skutis/jtbubl/cores/bubl/ver/game/scene1/1.png

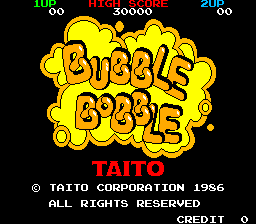
cores/bubl/ver/game/scene1/1.png
