skutis/jtbubl/cores/bubl/ver/game/scene2/2.png

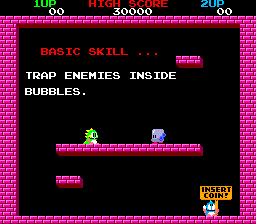
cores/bubl/ver/game/scene2/2.png
