skutis/jtbubl/cores/bubl/ver/game/scene3/3.png

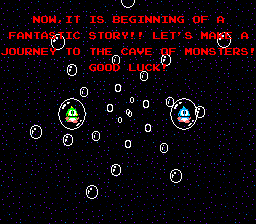
cores/bubl/ver/game/scene3/3.png
