skutis/jtbubl/cores/bubl/ver/game/scene4/4.png

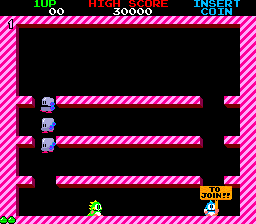
cores/bubl/ver/game/scene4/4.png
