skutis/jtbubl/cores/bubl/ver/game/scene5/5.png

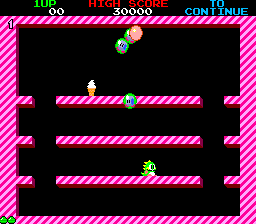
cores/bubl/ver/game/scene5/5.png
