skutis/jtbubl/cores/bubl/ver/game/scene6/6.png

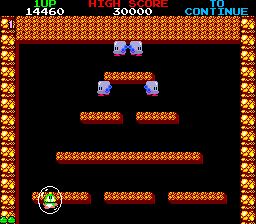
cores/bubl/ver/game/scene6/6.png
