skutis/jtbubl/cores/bubl/ver/game/scene7/7.png

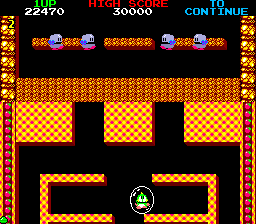
cores/bubl/ver/game/scene7/7.png
