skutis/jtbubl/cores/bubl/ver/game/scene8/8.png

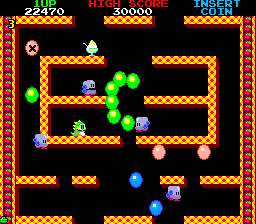
cores/bubl/ver/game/scene8/8.png
