skutis/jtbubl/cores/kiwi/sch/capacitors.kicad_sch

## KiCad design cores/kiwi/sch/capacitors.kicad_sch (2022-11-14, an earlier design)

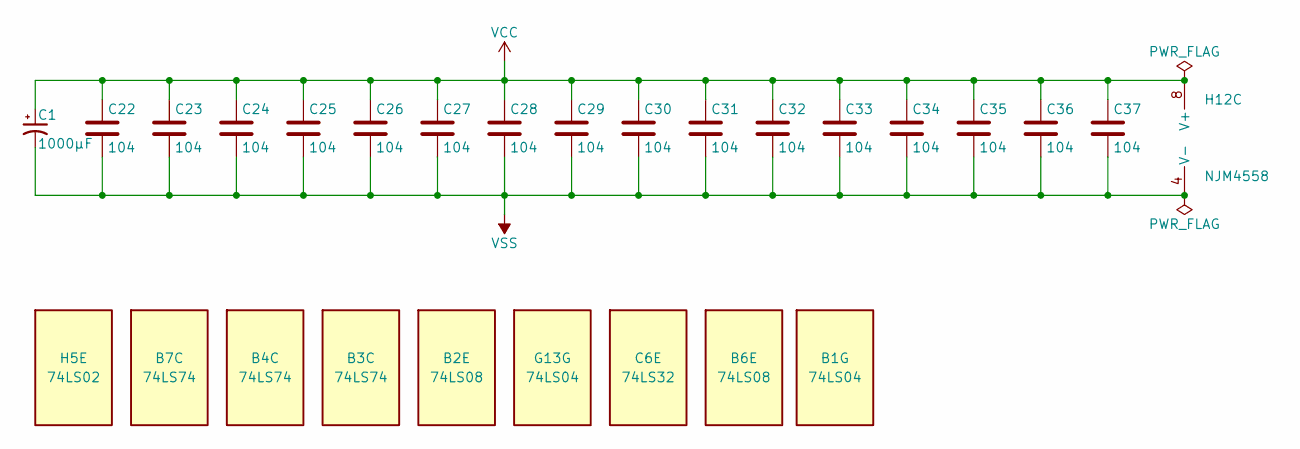
[picture p10: schematic capacitors.kicad_sch]

Parts:
B1: 74LS04
B2, B6: 74LS08
B3, B4, B7: 74LS74
C1: 1000μF
C6: 74LS32
C22, C23, C24, C25, C26, C27, C28, C29, C30, C31, C32, C33, C34, C35, C36, C37: 104
G13: 74LS04
H5: 74LS02
H12: NJM4558

Connections:
VCC: C1.1, C22.1, C23.1, C24.1, C25.1, C26.1, C27.1, C28.1, C29.1, C30.1, C31.1, C32.1, C33.1, C34.1, C35.1, C36.1, C37.1, H12.8 (V+)
VSS: C1.2, C22.2, C23.2, C24.2, C25.2, C26.2, C27.2, C28.2, C29.2, C30.2, C31.2, C32.2, C33.2, C34.2, C35.2, C36.2, C37.2, H12.4 (V-)
