skutis/jtbubl/cores/kiwi/sch/colmix.kicad_sch

## KiCad design cores/kiwi/sch/colmix.kicad_sch (2022-11-14, an earlier design)

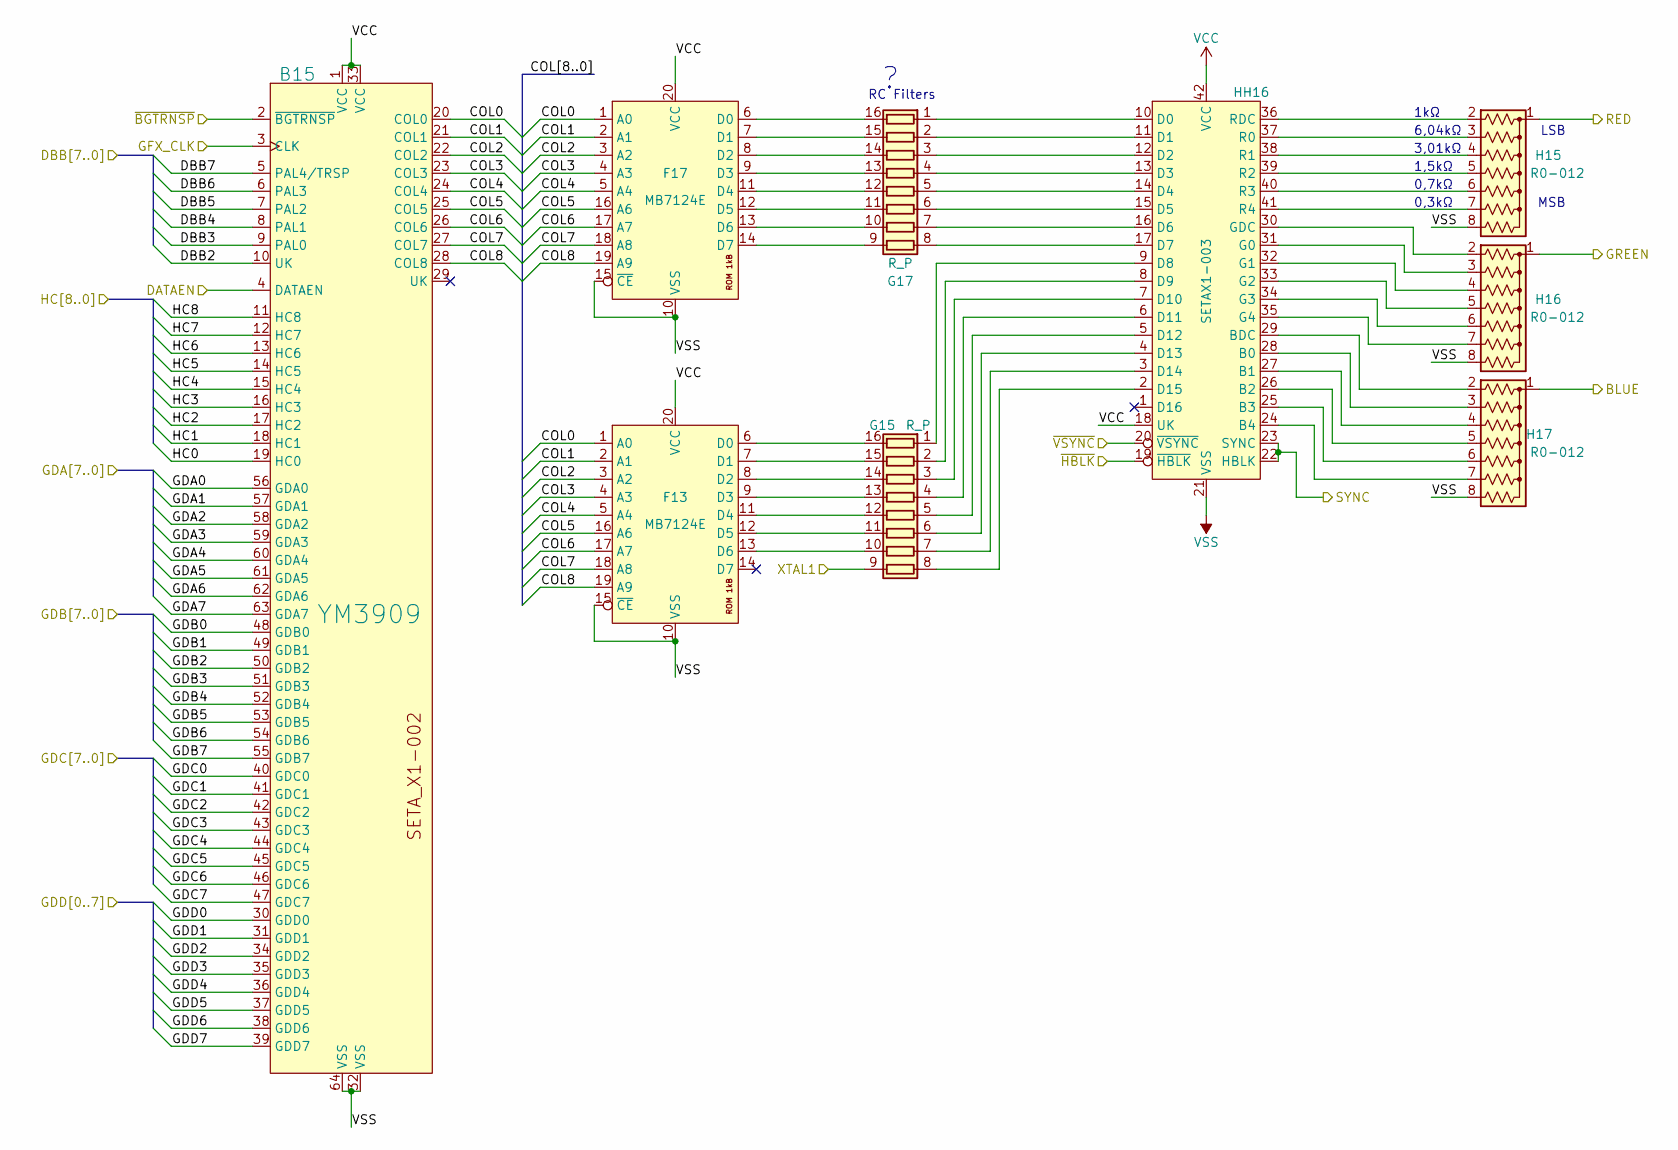
[picture p11: schematic colmix.kicad_sch]

Parts:
B15: YM3909
F13, F17: MB7124E
G15, G17: R_P
H15, H16, H17: R0-012; R_Array_SIP8
HH16: SETAX1-003

Connections:
BLUE: H17.1 (common)
COL0: B15.20 (COL0), F13.1 (A0), F17.1 (A0)
COL1: B15.21 (COL1), F13.2 (A1), F17.2 (A1)
COL2: B15.22 (COL2), F13.3 (A2), F17.3 (A2)
COL3: B15.23 (COL3), F13.4 (A3), F17.4 (A3)
COL4: B15.24 (COL4), F13.5 (A4), F17.5 (A4)
COL5: B15.25 (COL5), F13.16 (A6), F17.16 (A6)
COL6: B15.26 (COL6), F13.17 (A7), F17.17 (A7)
COL7: B15.27 (COL7), F13.18 (A8), F17.18 (A8)
COL8: B15.28 (COL8), F13.19 (A9), F17.19 (A9)
DATAEN: B15.4 (DATAEN)
DBB2: B15.10 (UK)
DBB3: B15.9 (PAL0)
DBB4: B15.8 (PAL1)
DBB5: B15.7 (PAL2)
DBB6: B15.6 (PAL3)
DBB7: B15.5 (PAL4/TRSP)
GDA0: B15.56 (GDA0)
GDA1: B15.57 (GDA1)
GDA2: B15.58 (GDA2)
GDA3: B15.59 (GDA3)
GDA4: B15.60 (GDA4)
GDA5: B15.61 (GDA5)
GDA6: B15.62 (GDA6)
GDA7: B15.63 (GDA7)
GDB0: B15.48 (GDB0)
GDB1: B15.49 (GDB1)
GDB2: B15.50 (GDB2)
GDB3: B15.51 (GDB3)
GDB4: B15.52 (GDB4)
GDB5: B15.53 (GDB5)
GDB6: B15.54 (GDB6)
GDB7: B15.55 (GDB7)
GDC0: B15.40 (GDC0)
GDC1: B15.41 (GDC1)
GDC2: B15.42 (GDC2)
GDC3: B15.43 (GDC3)
GDC4: B15.44 (GDC4)
GDC5: B15.45 (GDC5)
GDC6: B15.46 (GDC6)
GDC7: B15.47 (GDC7)
GDD0: B15.30 (GDD0)
GDD1: B15.31 (GDD1)
GDD2: B15.34 (GDD2)
GDD3: B15.35 (GDD3)
GDD4: B15.36 (GDD4)
GDD5: B15.37 (GDD5)
GDD6: B15.38 (GDD6)
GDD7: B15.39 (GDD7)
GFX_CLK: B15.3 (CLK)
GREEN: H16.1 (common)
HC0: B15.19 (HC0)
HC1: B15.18 (HC1)
HC2: B15.17 (HC2)
HC3: B15.16 (HC3)
HC4: B15.15 (HC4)
HC5: B15.14 (HC5)
HC6: B15.13 (HC6)
HC7: B15.12 (HC7)
HC8: B15.11 (HC8)
unnamed: F13.6 (D0), G15.16 (R1.2)
unnamed: F13.7 (D1), G15.15 (R2.2)
unnamed: F13.8 (D2), G15.14 (R3.2)
unnamed: F13.9 (D3), G15.13 (R4.2)
unnamed: F13.11 (D4), G15.12 (R5.2)
unnamed: F13.12 (D5), G15.11 (R6.2)
unnamed: F13.13 (D6), G15.10 (R7.2)
unnamed: F17.6 (D0), G17.16 (R1.2)
unnamed: F17.7 (D1), G17.15 (R2.2)
unnamed: F17.8 (D2), G17.14 (R3.2)
unnamed: F17.9 (D3), G17.13 (R4.2)
unnamed: F17.11 (D4), G17.12 (R5.2)
unnamed: F17.12 (D5), G17.11 (R6.2)
unnamed: F17.13 (D6), G17.10 (R7.2)
unnamed: F17.14 (D7), G17.9 (R8.2)
unnamed: G15.1 (R1.1), HH16.9 (D8)
unnamed: G15.2 (R2.1), HH16.8 (D9)
unnamed: G15.3 (R3.1), HH16.7 (D10)
unnamed: G15.4 (R4.1), HH16.6 (D11)
unnamed: G15.5 (R5.1), HH16.5 (D12)
unnamed: G15.6 (R6.1), HH16.4 (D13)
unnamed: G15.7 (R7.1), HH16.3 (D14)
unnamed: G15.8 (R8.1), HH16.2 (D15)
unnamed: G17.1 (R1.1), HH16.10 (D0)
unnamed: G17.2 (R2.1), HH16.11 (D1)
unnamed: G17.3 (R3.1), HH16.12 (D2)
unnamed: G17.4 (R4.1), HH16.13 (D3)
unnamed: G17.5 (R5.1), HH16.14 (D4)
unnamed: G17.6 (R6.1), HH16.15 (D5)
unnamed: G17.7 (R7.1), HH16.16 (D6)
unnamed: G17.8 (R8.1), HH16.17 (D7)
unnamed: H15.2 (R1), HH16.36 (RDC)
unnamed: H15.3 (R2), HH16.37 (R0)
unnamed: H15.4 (R3), HH16.38 (R1)
unnamed: H15.5 (R4), HH16.39 (R2)
unnamed: H15.6 (R5), HH16.40 (R3)
unnamed: H15.7 (R6), HH16.41 (R4)
unnamed: H16.2 (R1), HH16.30 (GDC)
unnamed: H16.3 (R2), HH16.31 (G0)
unnamed: H16.4 (R3), HH16.32 (G1)
unnamed: H16.5 (R4), HH16.33 (G2)
unnamed: H16.6 (R5), HH16.34 (G3)
unnamed: H16.7 (R6), HH16.35 (G4)
unnamed: H17.2 (R1), HH16.29 (BDC)
unnamed: H17.3 (R2), HH16.28 (B0)
unnamed: H17.4 (R3), HH16.27 (B1)
unnamed: H17.5 (R4), HH16.26 (B2)
unnamed: H17.6 (R5), HH16.25 (B3)
unnamed: H17.7 (R6), HH16.24 (B4)
RED: H15.1 (common)
SYNC: HH16.22 (HBLK), HH16.23 (SYNC)
VCC: B15.1 (VCC), B15.33 (VCC), F13.20 (VCC), F17.20 (VCC), HH16.18 (UK), HH16.42 (VCC)
VSS: B15.32 (VSS), B15.64 (VSS), F13.10 (VSS), F13.15 (~CE), F17.10 (VSS), F17.15 (~CE), H15.8 (R7), H16.8 (R7), H17.8 (R7), HH16.21 (VSS)
XTAL1: G15.9 (R8.2)
~BGTRNSP: B15.2 (~BGTRNSP)
~HBLK: HH16.19 (~HBLK)
~VSYNC: HH16.20 (~VSYNC)

Notes on the sheet:
MSB
RC Filters
1,5kΩ
1kΩ
3,01kΩ
0,3kΩ
LSB
6,04kΩ
0,7kΩ
