skutis/jtbubl/cores/kiwi/sch/gfx.kicad_sch

## KiCad design cores/kiwi/sch/gfx.kicad_sch (2022-11-14, an earlier design)

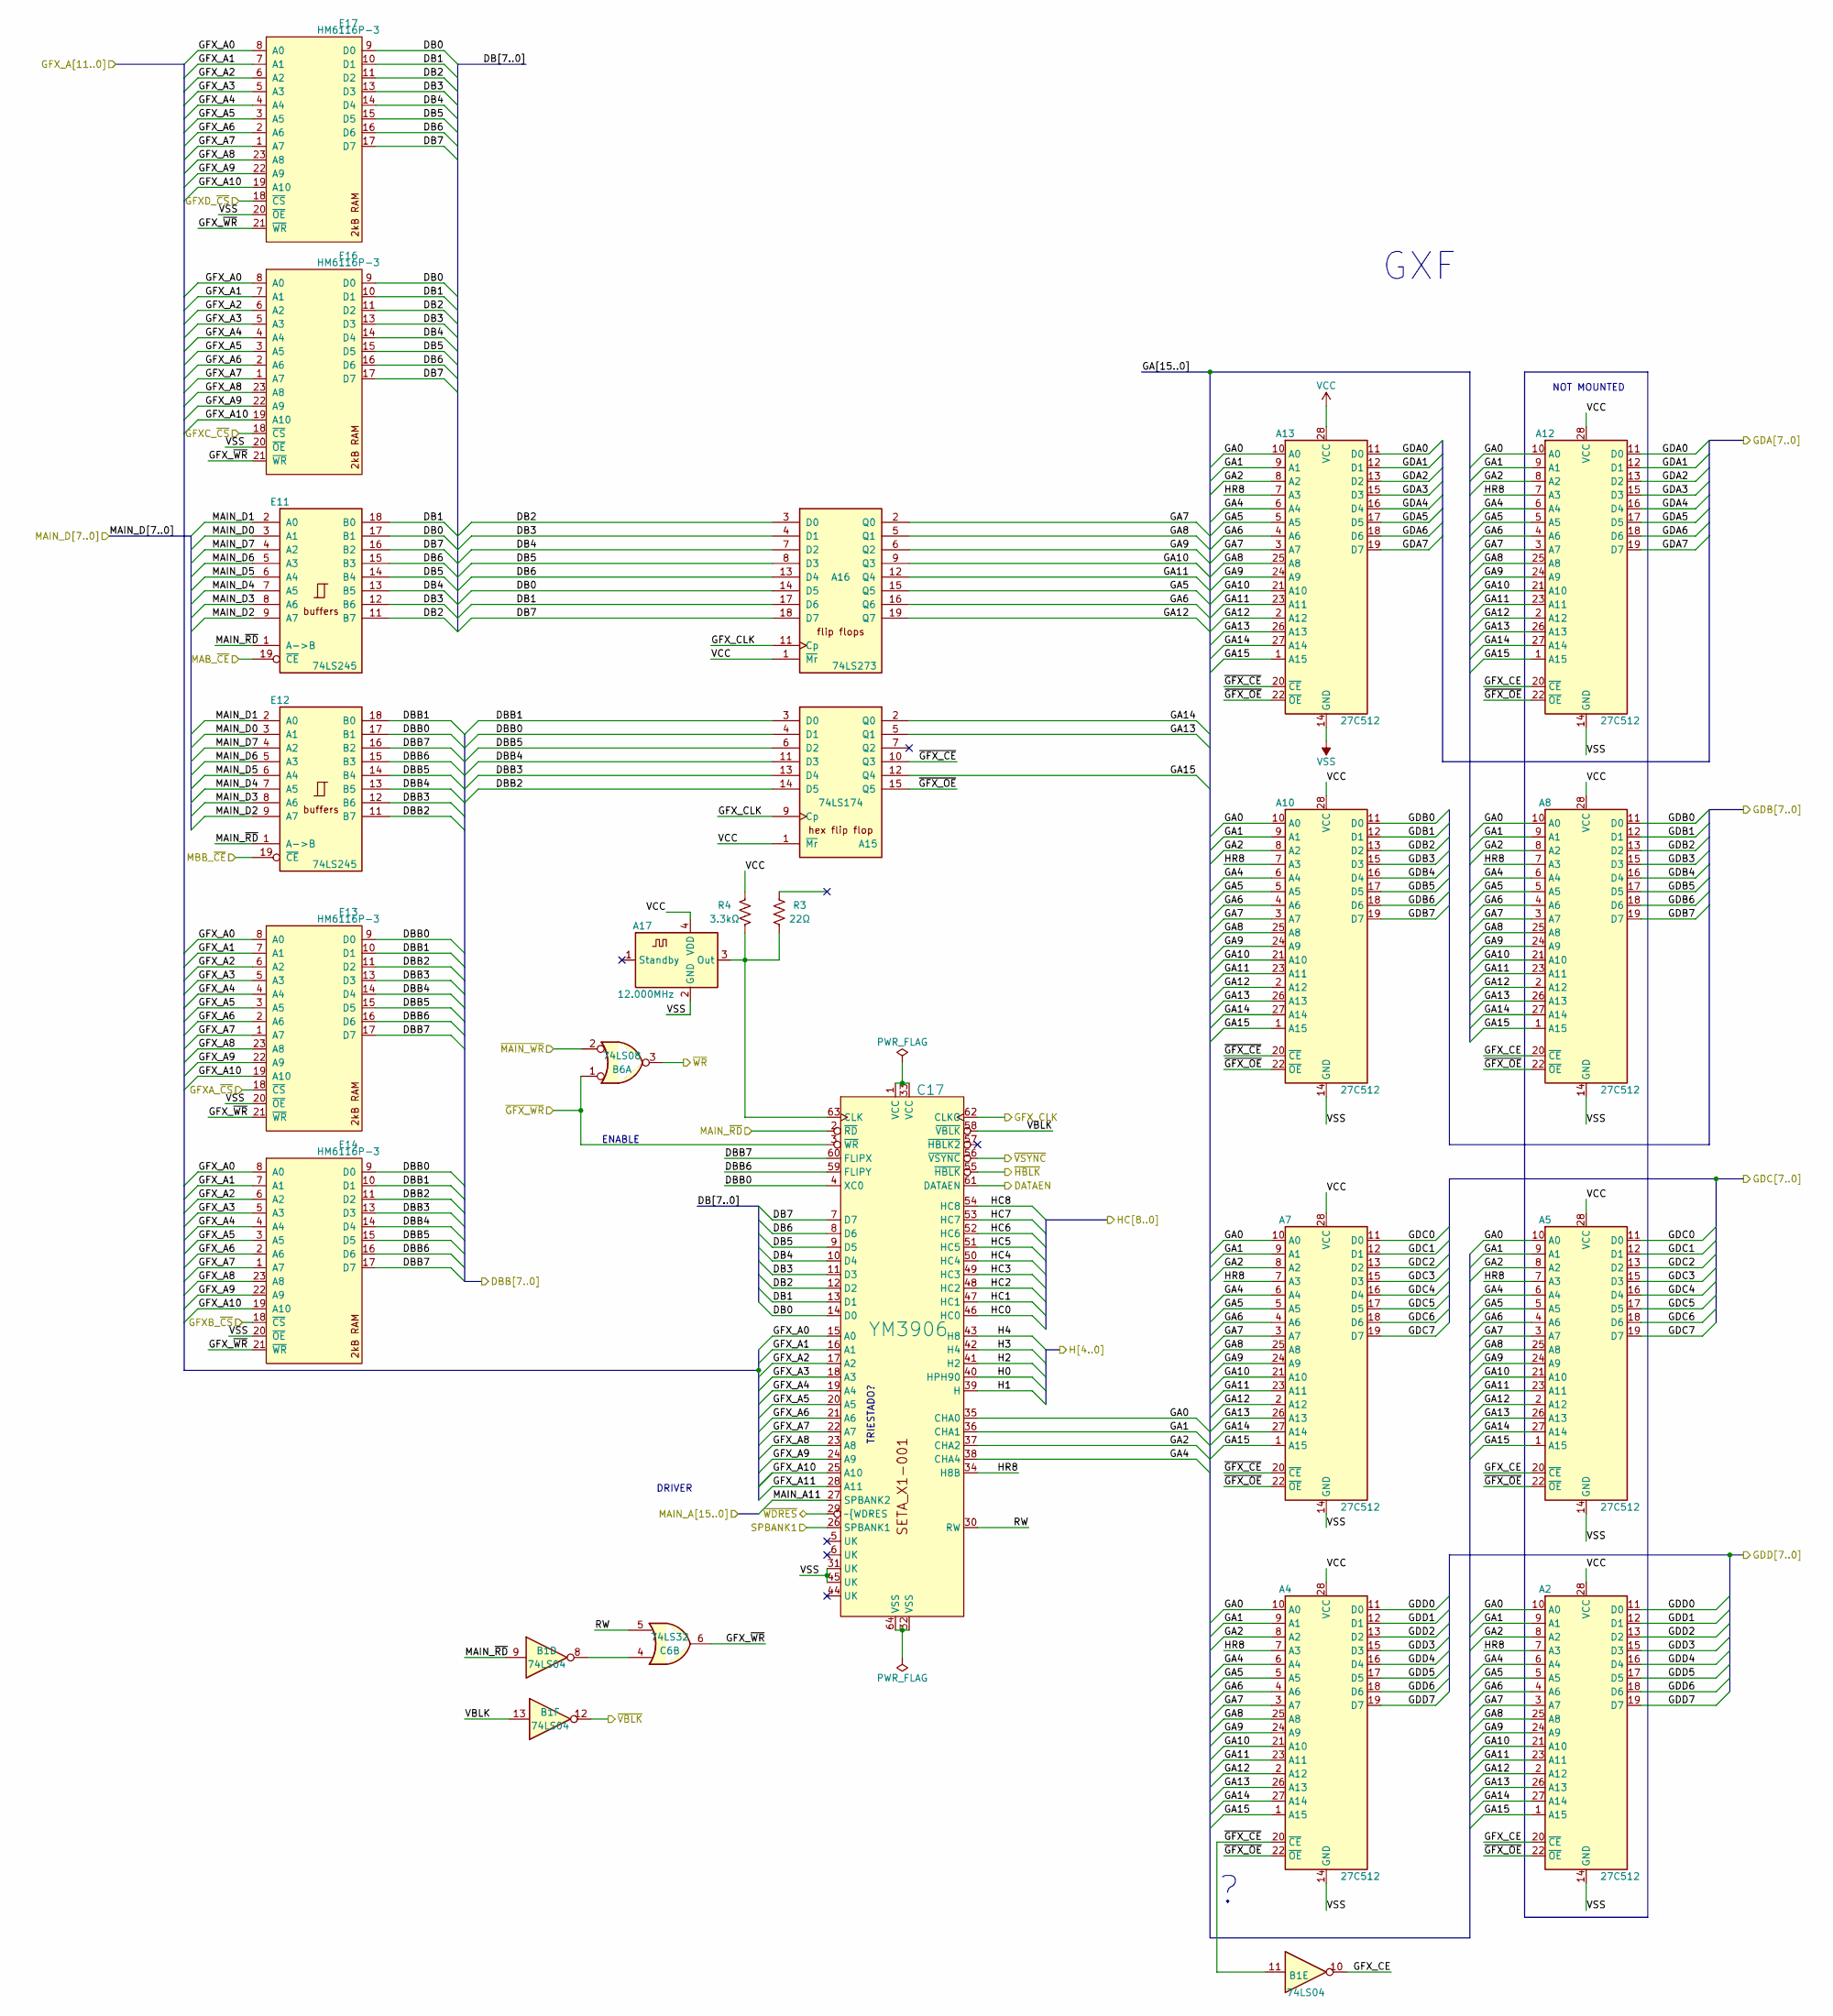
[picture p13: schematic gfx.kicad_sch]

Parts:
A2, A4, A5, A7, A8, A10, A12, A13: 27C512; DIP-28_W15.24mm
A15: 74LS174
A16: 74LS273
A17: 12.000MHz; Oscillator_SMD_Abracon_ASDMB-4Pin_2.5x2.0mm
B1: 74LS04
B6: 74LS08
C6: 74LS32
C17: YM3906
E11, E12: 74LS245
E13, E14, E16, E17: HM6116P-3
R3: 22Ω
R4: 3.3kΩ

Connections:
DATAEN: C17.61 (DATAEN)
DB0: A16.14 (D5), C17.14 (D0), E11.17 (B1), E16.9 (D0), E17.9 (D0)
DB1: A16.17 (D6), C17.13 (D1), E11.18 (B0), E16.10 (D1), E17.10 (D1)
DB2: A16.3 (D0), C17.12 (D2), E11.11 (B7), E16.11 (D2), E17.11 (D2)
DB3: A16.4 (D1), C17.11 (D3), E11.12 (B6), E16.13 (D3), E17.13 (D3)
DB4: A16.7 (D2), C17.10 (D4), E11.13 (B5), E16.14 (D4), E17.14 (D4)
DB5: A16.8 (D3), C17.9 (D5), E11.14 (B4), E16.15 (D5), E17.15 (D5)
DB6: A16.13 (D4), C17.8 (D6), E11.15 (B3), E16.16 (D6), E17.16 (D6)
DB7: A16.18 (D7), C17.7 (D7), E11.16 (B2), E16.17 (D7), E17.17 (D7)
DBB0: A15.4 (D1), C17.4 (XC0), E12.17 (B1), E13.9 (D0), E14.9 (D0)
DBB1: A15.3 (D0), E12.18 (B0), E13.10 (D1), E14.10 (D1)
DBB2: A15.14 (D5), E12.11 (B7), E13.11 (D2), E14.11 (D2)
DBB3: A15.13 (D4), E12.12 (B6), E13.13 (D3), E14.13 (D3)
DBB4: A15.11 (D3), E12.13 (B5), E13.14 (D4), E14.14 (D4)
DBB5: A15.6 (D2), E12.14 (B4), E13.15 (D5), E14.15 (D5)
DBB6: C17.59 (FLIPY), E12.15 (B3), E13.16 (D6), E14.16 (D6)
DBB7: C17.60 (FLIPX), E12.16 (B2), E13.17 (D7), E14.17 (D7)
GA0: A2.10 (A0), A4.10 (A0), A5.10 (A0), A7.10 (A0), A8.10 (A0), A10.10 (A0), A12.10 (A0), A13.10 (A0), C17.35 (CHA0)
GA1: A2.9 (A1), A4.9 (A1), A5.9 (A1), A7.9 (A1), A8.9 (A1), A10.9 (A1), A12.9 (A1), A13.9 (A1), C17.36 (CHA1)
GA2: A2.8 (A2), A4.8 (A2), A5.8 (A2), A7.8 (A2), A8.8 (A2), A10.8 (A2), A12.8 (A2), A13.8 (A2), C17.37 (CHA2)
GA4: A2.6 (A4), A4.6 (A4), A5.6 (A4), A7.6 (A4), A8.6 (A4), A10.6 (A4), A12.6 (A4), A13.6 (A4), C17.38 (CHA4)
GA5: A2.5 (A5), A4.5 (A5), A5.5 (A5), A7.5 (A5), A8.5 (A5), A10.5 (A5), A12.5 (A5), A13.5 (A5), A16.15 (Q5)
GA6: A2.4 (A6), A4.4 (A6), A5.4 (A6), A7.4 (A6), A8.4 (A6), A10.4 (A6), A12.4 (A6), A13.4 (A6), A16.16 (Q6)
GA7: A2.3 (A7), A4.3 (A7), A5.3 (A7), A7.3 (A7), A8.3 (A7), A10.3 (A7), A12.3 (A7), A13.3 (A7), A16.2 (Q0)
GA8: A2.25 (A8), A4.25 (A8), A5.25 (A8), A7.25 (A8), A8.25 (A8), A10.25 (A8), A12.25 (A8), A13.25 (A8), A16.5 (Q1)
GA9: A2.24 (A9), A4.24 (A9), A5.24 (A9), A7.24 (A9), A8.24 (A9), A10.24 (A9), A12.24 (A9), A13.24 (A9), A16.6 (Q2)
GA10: A2.21 (A10), A4.21 (A10), A5.21 (A10), A7.21 (A10), A8.21 (A10), A10.21 (A10), A12.21 (A10), A13.21 (A10), A16.9 (Q3)
GA11: A2.23 (A11), A4.23 (A11), A5.23 (A11), A7.23 (A11), A8.23 (A11), A10.23 (A11), A12.23 (A11), A13.23 (A11), A16.12 (Q4)
GA12: A2.2 (A12), A4.2 (A12), A5.2 (A12), A7.2 (A12), A8.2 (A12), A10.2 (A12), A12.2 (A12), A13.2 (A12), A16.19 (Q7)
GA13: A2.26 (A13), A4.26 (A13), A5.26 (A13), A7.26 (A13), A8.26 (A13), A10.26 (A13), A12.26 (A13), A13.26 (A13), A15.5 (Q1)
GA14: A2.27 (A14), A4.27 (A14), A5.27 (A14), A7.27 (A14), A8.27 (A14), A10.27 (A14), A12.27 (A14), A13.27 (A14), A15.2 (Q0)
GA15: A2.1 (A15), A4.1 (A15), A5.1 (A15), A7.1 (A15), A8.1 (A15), A10.1 (A15), A12.1 (A15), A13.1 (A15), A15.12 (Q4)
GDA0: A12.11 (D0), A13.11 (D0)
GDA1: A12.12 (D1), A13.12 (D1)
GDA2: A12.13 (D2), A13.13 (D2)
GDA3: A12.15 (D3), A13.15 (D3)
GDA4: A12.16 (D4), A13.16 (D4)
GDA5: A12.17 (D5), A13.17 (D5)
GDA6: A12.18 (D6), A13.18 (D6)
GDA7: A12.19 (D7), A13.19 (D7)
GDB0: A8.11 (D0), A10.11 (D0)
GDB1: A8.12 (D1), A10.12 (D1)
GDB2: A8.13 (D2), A10.13 (D2)
GDB3: A8.15 (D3), A10.15 (D3)
GDB4: A8.16 (D4), A10.16 (D4)
GDB5: A8.17 (D5), A10.17 (D5)
GDB6: A8.18 (D6), A10.18 (D6)
GDB7: A8.19 (D7), A10.19 (D7)
GDC0: A5.11 (D0), A7.11 (D0)
GDC1: A5.12 (D1), A7.12 (D1)
GDC2: A5.13 (D2), A7.13 (D2)
GDC3: A5.15 (D3), A7.15 (D3)
GDC4: A5.16 (D4), A7.16 (D4)
GDC5: A5.17 (D5), A7.17 (D5)
GDC6: A5.18 (D6), A7.18 (D6)
GDC7: A5.19 (D7), A7.19 (D7)
GDD0: A2.11 (D0), A4.11 (D0)
GDD1: A2.12 (D1), A4.12 (D1)
GDD2: A2.13 (D2), A4.13 (D2)
GDD3: A2.15 (D3), A4.15 (D3)
GDD4: A2.16 (D4), A4.16 (D4)
GDD5: A2.17 (D5), A4.17 (D5)
GDD6: A2.18 (D6), A4.18 (D6)
GDD7: A2.19 (D7), A4.19 (D7)
GFXA_~CS: E13.18 (~CS)
GFXB_~CS: E14.18 (~CS)
GFXC_~CS: E16.18 (~CS)
GFXD_~CS: E17.18 (~CS)
GFX_A0: C17.15 (A0), E13.8 (A0), E14.8 (A0), E16.8 (A0), E17.8 (A0)
GFX_A1: C17.16 (A1), E13.7 (A1), E14.7 (A1), E16.7 (A1), E17.7 (A1)
GFX_A2: C17.17 (A2), E13.6 (A2), E14.6 (A2), E16.6 (A2), E17.6 (A2)
GFX_A3: C17.18 (A3), E13.5 (A3), E14.5 (A3), E16.5 (A3), E17.5 (A3)
GFX_A4: C17.19 (A4), E13.4 (A4), E14.4 (A4), E16.4 (A4), E17.4 (A4)
GFX_A5: C17.20 (A5), E13.3 (A5), E14.3 (A5), E16.3 (A5), E17.3 (A5)
GFX_A6: C17.21 (A6), E13.2 (A6), E14.2 (A6), E16.2 (A6), E17.2 (A6)
GFX_A7: C17.22 (A7), E13.1 (A7), E14.1 (A7), E16.1 (A7), E17.1 (A7)
GFX_A8: C17.23 (A8), E13.23 (A8), E14.23 (A8), E16.23 (A8), E17.23 (A8)
GFX_A9: C17.24 (A9), E13.22 (A9), E14.22 (A9), E16.22 (A9), E17.22 (A9)
GFX_A10: C17.25 (A10), E13.19 (A10), E14.19 (A10), E16.19 (A10), E17.19 (A10)
GFX_A11: C17.28 (A11)
GFX_CE: A2.20 (~CE), A5.20 (~CE), A8.20 (~CE), A12.20 (~CE), B1.10
GFX_CLK: A15.9 (Cp), A16.11 (Cp), C17.62 (CLKO)
GFX_~WR: C6.6, E13.21 (~WR), E14.21 (~WR), E16.21 (~WR), E17.21 (~WR)
H0: C17.40 (HPH90)
H1: C17.39 (H)
H2: C17.41 (H2)
H3: C17.42 (H4)
H4: C17.43 (H8)
HC0: C17.46 (HC0)
HC1: C17.47 (HC1)
HC2: C17.48 (HC2)
HC3: C17.49 (HC3)
HC4: C17.50 (HC4)
HC5: C17.51 (HC5)
HC6: C17.52 (HC6)
HC7: C17.53 (HC7)
HC8: C17.54 (HC8)
HR8: A2.7 (A3), A4.7 (A3), A5.7 (A3), A7.7 (A3), A8.7 (A3), A10.7 (A3), A12.7 (A3), A13.7 (A3), C17.34 (H8B)
MAB_~CE: E11.19 (~CE)
MAIN_A11: C17.27 (SPBANK2)
MAIN_D0: E11.3 (A1), E12.3 (A1)
MAIN_D1: E11.2 (A0), E12.2 (A0)
MAIN_D2: E11.9 (A7), E12.9 (A7)
MAIN_D3: E11.8 (A6), E12.8 (A6)
MAIN_D4: E11.7 (A5), E12.7 (A5)
MAIN_D5: E11.6 (A4), E12.6 (A4)
MAIN_D6: E11.5 (A3), E12.5 (A3)
MAIN_D7: E11.4 (A2), E12.4 (A2)
MAIN_~RD: B1.9, C17.2 (~RD), E11.1 (A->B), E12.1 (A->B)
MBB_~CE: E12.19 (~CE)
unnamed: A17.3 (Out), C17.63 (CLK), R3.2, R4.2
unnamed: B1.8, C6.4
unnamed: C17.1 (VCC), C17.33 (VCC)
unnamed: C17.32 (VSS), C17.64 (VSS)
RW: C6.5, C17.30 (RW)
SPBANK1: C17.26 (SPBANK1)
VBLK: B1.13, C17.58 (~VBLK)
VCC: A2.28 (VCC), A4.28 (VCC), A5.28 (VCC), A7.28 (VCC), A8.28 (VCC), A10.28 (VCC), A12.28 (VCC), A13.28 (VCC), A15.1 (~Mr), A16.1 (~Mr), A17.4 (VDD), R4.1
VSS: A2.14 (GND), A4.14 (GND), A5.14 (GND), A7.14 (GND), A8.14 (GND), A10.14 (GND), A12.14 (GND), A13.14 (GND), A17.2 (GND), C17.31 (UK), C17.45 (UK), E13.20 (~OE), E14.20 (~OE), E16.20 (~OE), E17.20 (~OE)
~GFX_CE: A4.20 (~CE), A7.20 (~CE), A10.20 (~CE), A13.20 (~CE), A15.10 (Q3), B1.11
~GFX_OE: A2.22 (~OE), A4.22 (~OE), A5.22 (~OE), A7.22 (~OE), A8.22 (~OE), A10.22 (~OE), A12.22 (~OE), A13.22 (~OE), A15.15 (Q5)
~GFX_WR: B6.1, C17.3 (~WR)
~HBLK: C17.55 (~HBLK)
~MAIN_WR: B6.2
~VBLK: B1.12
~VSYNC: C17.56 (~VSYNC)
~WDRES: C17.29 (~{WDRES)
~WR: B6.3

Notes on the sheet:
TRIESTADO?
DRIVER
GXF
ENABLE
NOT MOUNTED
