skutis/jtbubl/cores/kiwi/sch/main.kicad_sch

## KiCad design cores/kiwi/sch/main.kicad_sch (2022-11-14)

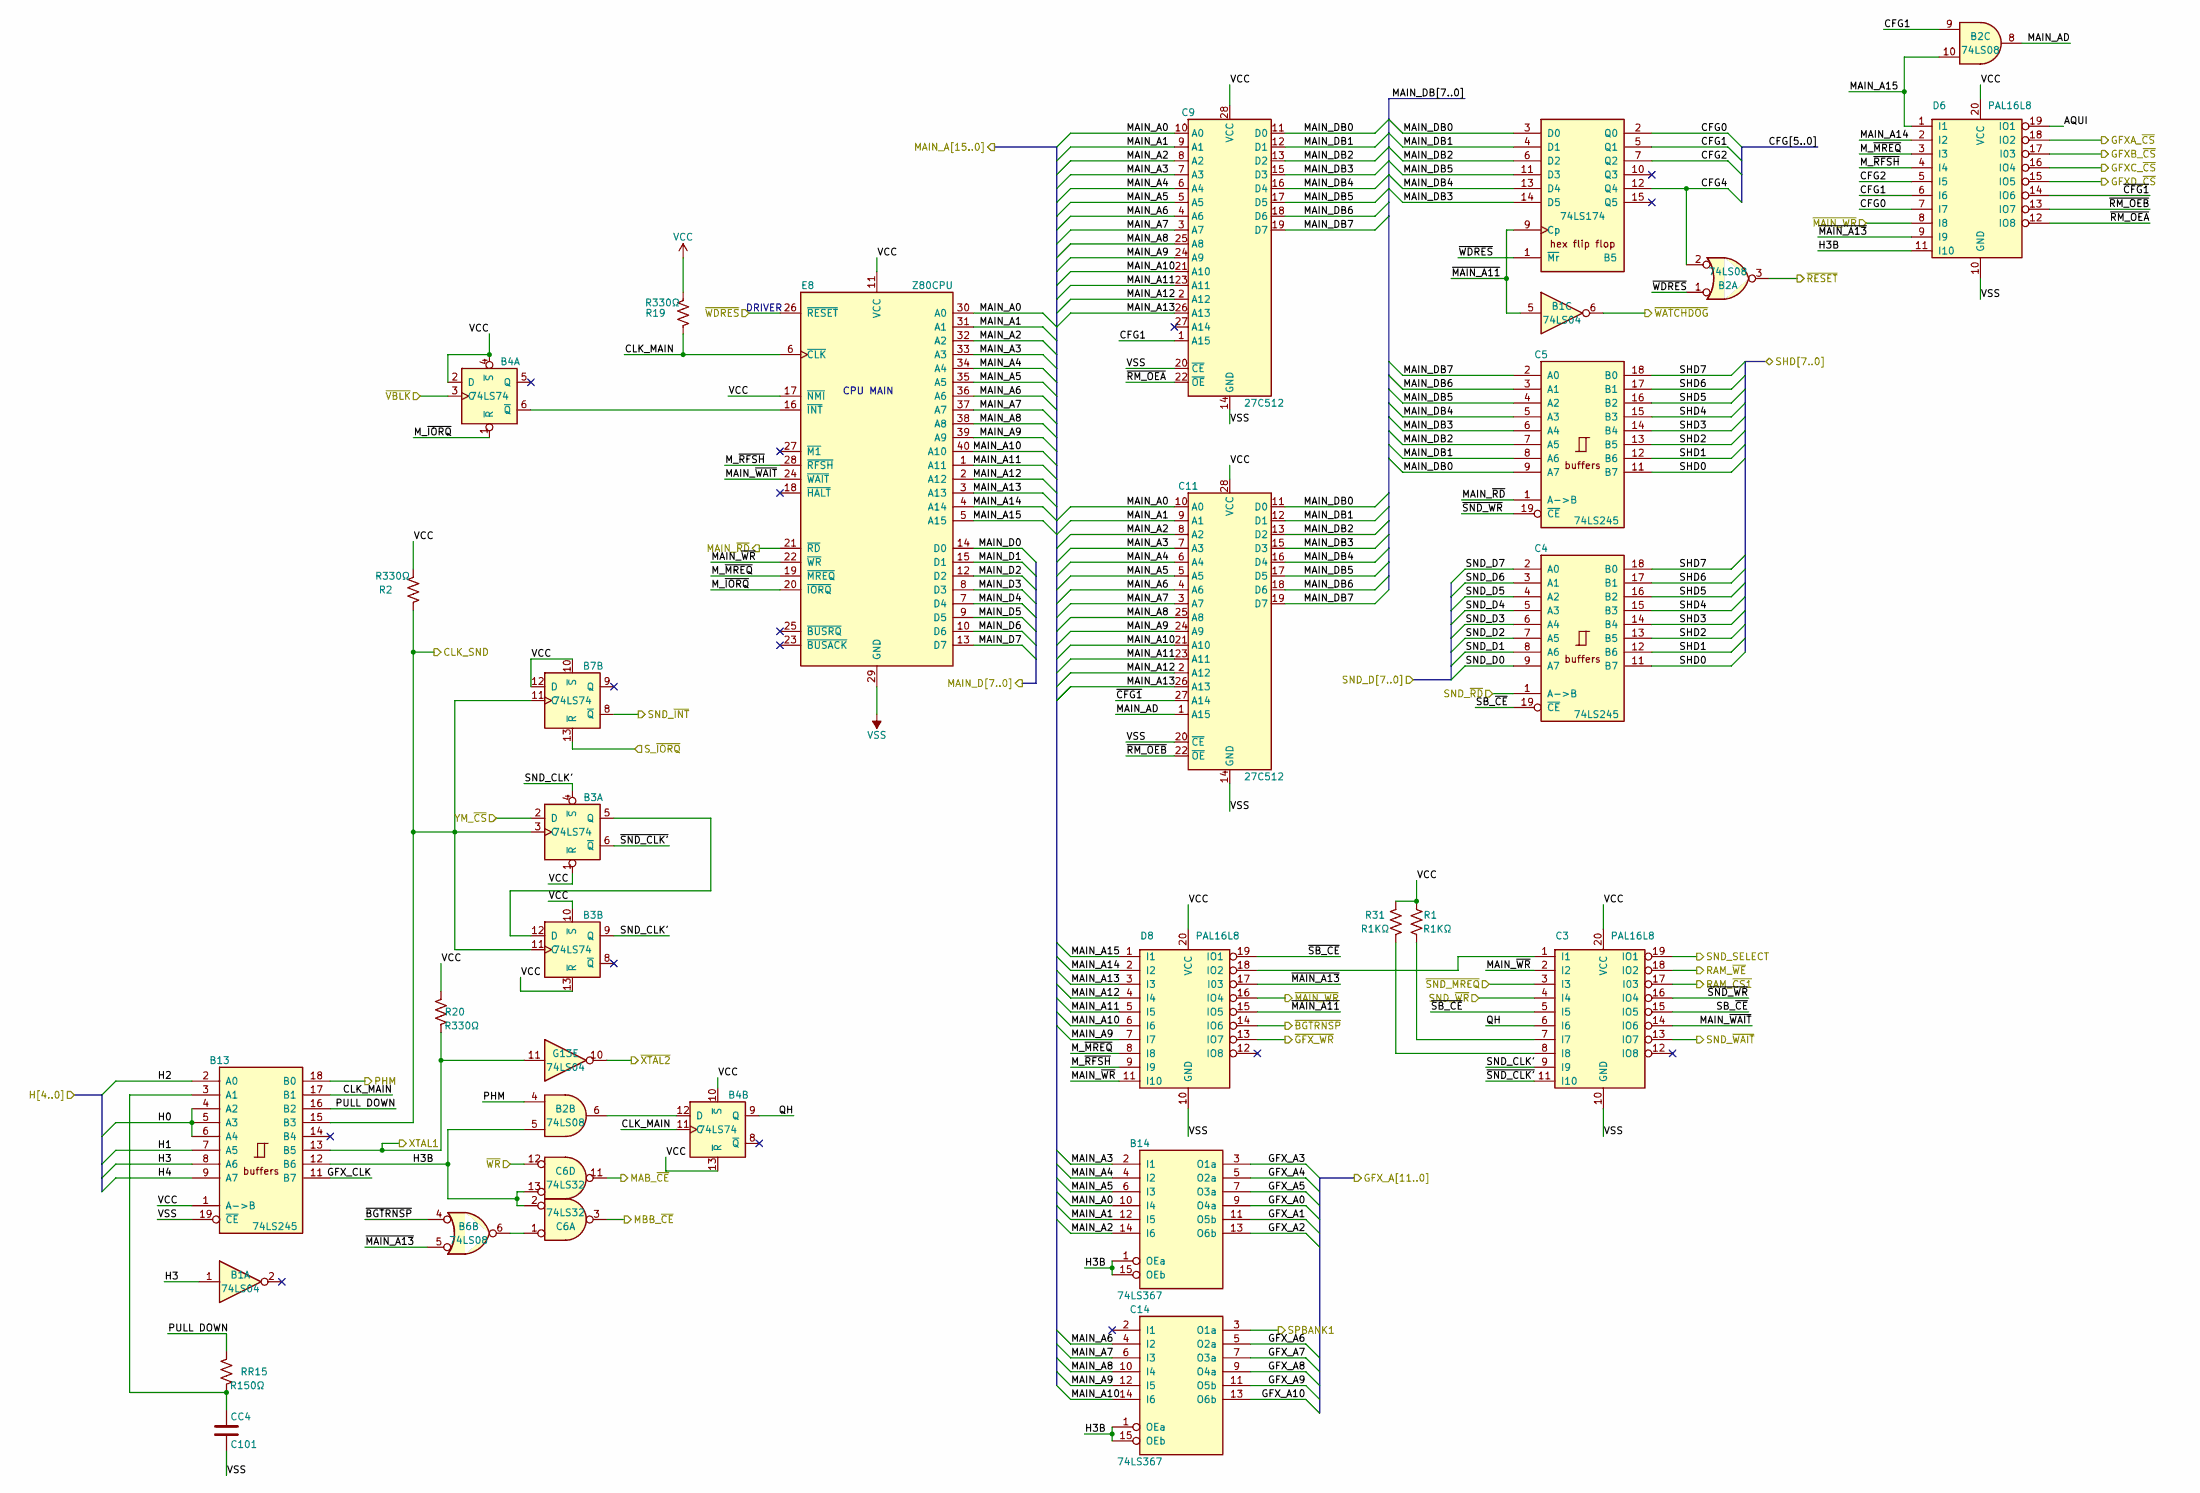
[picture p14: schematic main.kicad_sch]

Parts:
B1: 74LS04
B2, B6: 74LS08
B3, B4, B7: 74LS74
B5: 74LS174
B13: 74LS245
B14: 74LS367
C3: PAL16L8
C4, C5: 74LS245
C6: 74LS32
C9, C11: 27C512; DIP-28_W15.24mm
C14: 74LS367
CC4: C101
D6, D8: PAL16L8
E8: Z80CPU
G13: 74LS04
R1, R31: R1KΩ
R2, R19, R20: R330Ω
RR15: R150Ω

Connections:
AQUI: D6.19 (IO1)
CFG0: B5.2 (Q0), D6.7 (I7)
CFG1: B2.9, B5.5 (Q1), C9.1 (A15), D6.6 (I6)
CFG2: B5.7 (Q2), D6.5 (I5)
CFG4: B2.2, B5.12 (Q4)
CLK_MAIN: B4.11 (C), B13.17 (B1), E8.6 (~CLK), R19.2
CLK_SND: B3.3 (C), B3.11 (C), B7.11 (C), B13.15 (B3), R2.2
GFXA_~CS: D6.18 (IO2)
GFXB_~CS: D6.17 (I03)
GFXC_~CS: D6.16 (IO4)
GFXD_~CS: D6.15 (IO5)
GFX_A0: B14.9 (O4a)
GFX_A1: B14.11 (O5b)
GFX_A2: B14.13 (O6b)
GFX_A3: B14.3 (O1a)
GFX_A4: B14.5 (O2a)
GFX_A5: B14.7 (O3a)
GFX_A6: C14.5 (O2a)
GFX_A7: C14.7 (O3a)
GFX_A8: C14.9 (O4a)
GFX_A9: C14.11 (O5b)
GFX_A10: C14.13 (O6b)
GFX_CLK: B13.11 (B7)
H0: B13.4 (A2), B13.5 (A3), B13.6 (A4)
H1: B13.7 (A5)
H2: B13.2 (A0)
H3: B1.1, B13.8 (A6)
H3B: B2.5, B13.12 (B6), B14.1 (OEa), B14.15 (OEb), C6.2, C6.13, C14.1 (OEa), C14.15 (OEb), D6.11 (I10)
H4: B13.9 (A7)
MAB_~CE: C6.11
MAIN_A0: B14.10 (I4), C9.10 (A0), C11.10 (A0), E8.30 (A0)
MAIN_A1: B14.12 (I5), C9.9 (A1), C11.9 (A1), E8.31 (A1)
MAIN_A2: B14.14 (I6), C9.8 (A2), C11.8 (A2), E8.32 (A2)
MAIN_A3: B14.2 (I1), C9.7 (A3), C11.7 (A3), E8.33 (A3)
MAIN_A4: B14.4 (I2), C9.6 (A4), C11.6 (A4), E8.34 (A4)
MAIN_A5: B14.6 (I3), C9.5 (A5), C11.5 (A5), E8.35 (A5)
MAIN_A6: C9.4 (A6), C11.4 (A6), C14.4 (I2), E8.36 (A6)
MAIN_A7: C9.3 (A7), C11.3 (A7), C14.6 (I3), E8.37 (A7)
MAIN_A8: C9.25 (A8), C11.25 (A8), C14.10 (I4), E8.38 (A8)
MAIN_A9: C9.24 (A9), C11.24 (A9), C14.12 (I5), D8.7 (I7), E8.39 (A9)
MAIN_A10: C9.21 (A10), C11.21 (A10), C14.14 (I6), D8.6 (I6), E8.40 (A10)
MAIN_A11: C9.23 (A11), C11.23 (A11), D8.5 (I5), E8.1 (A11)
MAIN_A12: C9.2 (A12), C11.2 (A12), D8.4 (I4), E8.2 (A12)
MAIN_A13: C9.26 (A13), C11.26 (A13), D8.3 (I3), E8.3 (A13)
MAIN_A14: D6.2 (I2), D8.2 (I2), E8.4 (A14)
MAIN_A15: B2.10, D6.1 (I1), D8.1 (I1), E8.5 (A15)
MAIN_AD: B2.8, C11.1 (A15)
MAIN_D0: E8.14 (D0)
MAIN_D1: E8.15 (D1)
MAIN_D2: E8.12 (D2)
MAIN_D3: E8.8 (D3)
MAIN_D4: E8.7 (D4)
MAIN_D5: E8.9 (D5)
MAIN_D6: E8.10 (D6)
MAIN_D7: E8.13 (D7)
MAIN_DB0: B5.3 (D0), C5.9 (A7), C9.11 (D0), C11.11 (D0)
MAIN_DB1: B5.4 (D1), C5.8 (A6), C9.12 (D1), C11.12 (D1)
MAIN_DB2: B5.6 (D2), C5.7 (A5), C9.13 (D2), C11.13 (D2)
MAIN_DB3: B5.14 (D5), C5.6 (A4), C9.15 (D3), C11.15 (D3)
MAIN_DB4: B5.13 (D4), C5.5 (A3), C9.16 (D4), C11.16 (D4)
MAIN_DB5: B5.11 (D3), C5.4 (A2), C9.17 (D5), C11.17 (D5)
MAIN_DB6: C5.3 (A1), C9.18 (D6), C11.18 (D6)
MAIN_DB7: C5.2 (A0), C9.19 (D7), C11.19 (D7)
MAIN_~RD: C5.1 (A->B), E8.21 (~RD)
MAIN_~WAIT: C3.14 (IO6), E8.24 (~WAIT)
MAIN_~WR: C3.2 (I2), D8.11 (I10), E8.22 (~WR)
MBB_~CE: C6.3
M_~IORQ: B4.1 (~R), E8.20 (~IORQ)
M_~MREQ: D6.3 (I3), D8.8 (I8), E8.19 (~MREQ)
M_~RFSH: D6.4 (I4), D8.9 (I9), E8.28 (~RFSH)
unnamed: B2.6, B4.12 (D)
unnamed: B3.5 (Q), B3.12 (D)
unnamed: B4.6 (~Q), E8.16 (~INT)
unnamed: B6.6, C6.1
unnamed: B13.3 (A1), CC4.1, RR15.1
unnamed: C3.1 (I1), D8.18 (IO2)
unnamed: C3.7 (I7), R1.2
unnamed: C3.8 (I8), R31.2
PHM: B2.4, B13.18 (B0)
PULL DOWN: B13.16 (B2), RR15.2
QH: B4.9 (Q), C3.6 (I6)
RAM_~CS1: C3.17 (I03)
RAM_~WE: C3.18 (IO2)
SB_~CE: C3.15 (IO5), C4.19 (~CE)
SHD0: C4.11 (B7), C5.11 (B7)
SHD1: C4.12 (B6), C5.12 (B6)
SHD2: C4.13 (B5), C5.13 (B5)
SHD3: C4.14 (B4), C5.14 (B4)
SHD4: C4.15 (B3), C5.15 (B3)
SHD5: C4.16 (B2), C5.16 (B2)
SHD6: C4.17 (B1), C5.17 (B1)
SHD7: C4.18 (B0), C5.18 (B0)
SND_CLK': B3.4 (~S), B3.9 (Q), C3.9 (I9)
SND_D0: C4.9 (A7)
SND_D1: C4.8 (A6)
SND_D2: C4.7 (A5)
SND_D3: C4.6 (A4)
SND_D4: C4.5 (A3)
SND_D5: C4.4 (A2)
SND_D6: C4.3 (A1)
SND_D7: C4.2 (A0)
SND_SELECT: C3.19 (IO1)
SND_~INT: B7.8 (~Q)
SND_~RD: C4.1 (A->B)
SND_~WAIT: C3.13 (IO7)
SND_~WR: C3.4 (I4)
SPBANK1: C14.3 (O1a)
S_~IORQ: B7.13 (~R)
VCC: B3.1 (~R), B3.10 (~S), B3.13 (~R), B4.2 (D), B4.4 (~S), B4.10 (~S), B4.13 (~R), B7.10 (~S), B7.12 (D), B13.1 (A->B), C3.20 (VCC), C9.28 (VCC), C11.28 (VCC), D6.20 (VCC), D8.20 (VCC), E8.11 (VCC), E8.17 (~NMI), R1.1, R2.1, R19.1, R20.2, R31.1
VSS: B13.19 (~CE), C3.10 (GND), C9.14 (GND), C9.20 (~CE), C11.14 (GND), C11.20 (~CE), CC4.2, D6.10 (GND), D8.10 (GND), E8.29 (GND)
XTAL1: B13.13 (B5), G13.11, R20.1
YM_~CS: B3.2 (D)
~BGTRNSP: B6.4, D8.14 (IO6)
~CFG1: C11.27 (A14), D6.14 (IO6)
~GFX_WR: D8.13 (IO7)
~MAIN_A11: B1.5, B5.9 (Cp), D8.15 (IO5)
~MAIN_A13: B6.5, D6.9 (I9), D8.17 (I03)
~MAIN_WR: D6.8 (I8), D8.16 (IO4)
~RESET: B2.3
~RM_OEA: C9.22 (~OE), D6.12 (IO8)
~RM_OEB: C11.22 (~OE), D6.13 (IO7)
~SB_CE: C3.5 (I5), D8.19 (IO1)
~SND_CLK': B3.6 (~Q), C3.11 (I10)
~SND_MREQ: C3.3 (I3)
~SND_WR: C3.16 (IO4), C5.19 (~CE)
~VBLK: B4.3 (C)
~WATCHDOG: B1.6
~WDRES: B2.1, B5.1 (~Mr), E8.26 (~RESET)
~WR: C6.12
~XTAL2: G13.10

Notes on the sheet:
DRIVER
CPU MAIN
