skutis/jtbubl/cores/kiwi/sch/sound.kicad_sch

## KiCad design cores/kiwi/sch/sound.kicad_sch (2022-11-14, an earlier design)

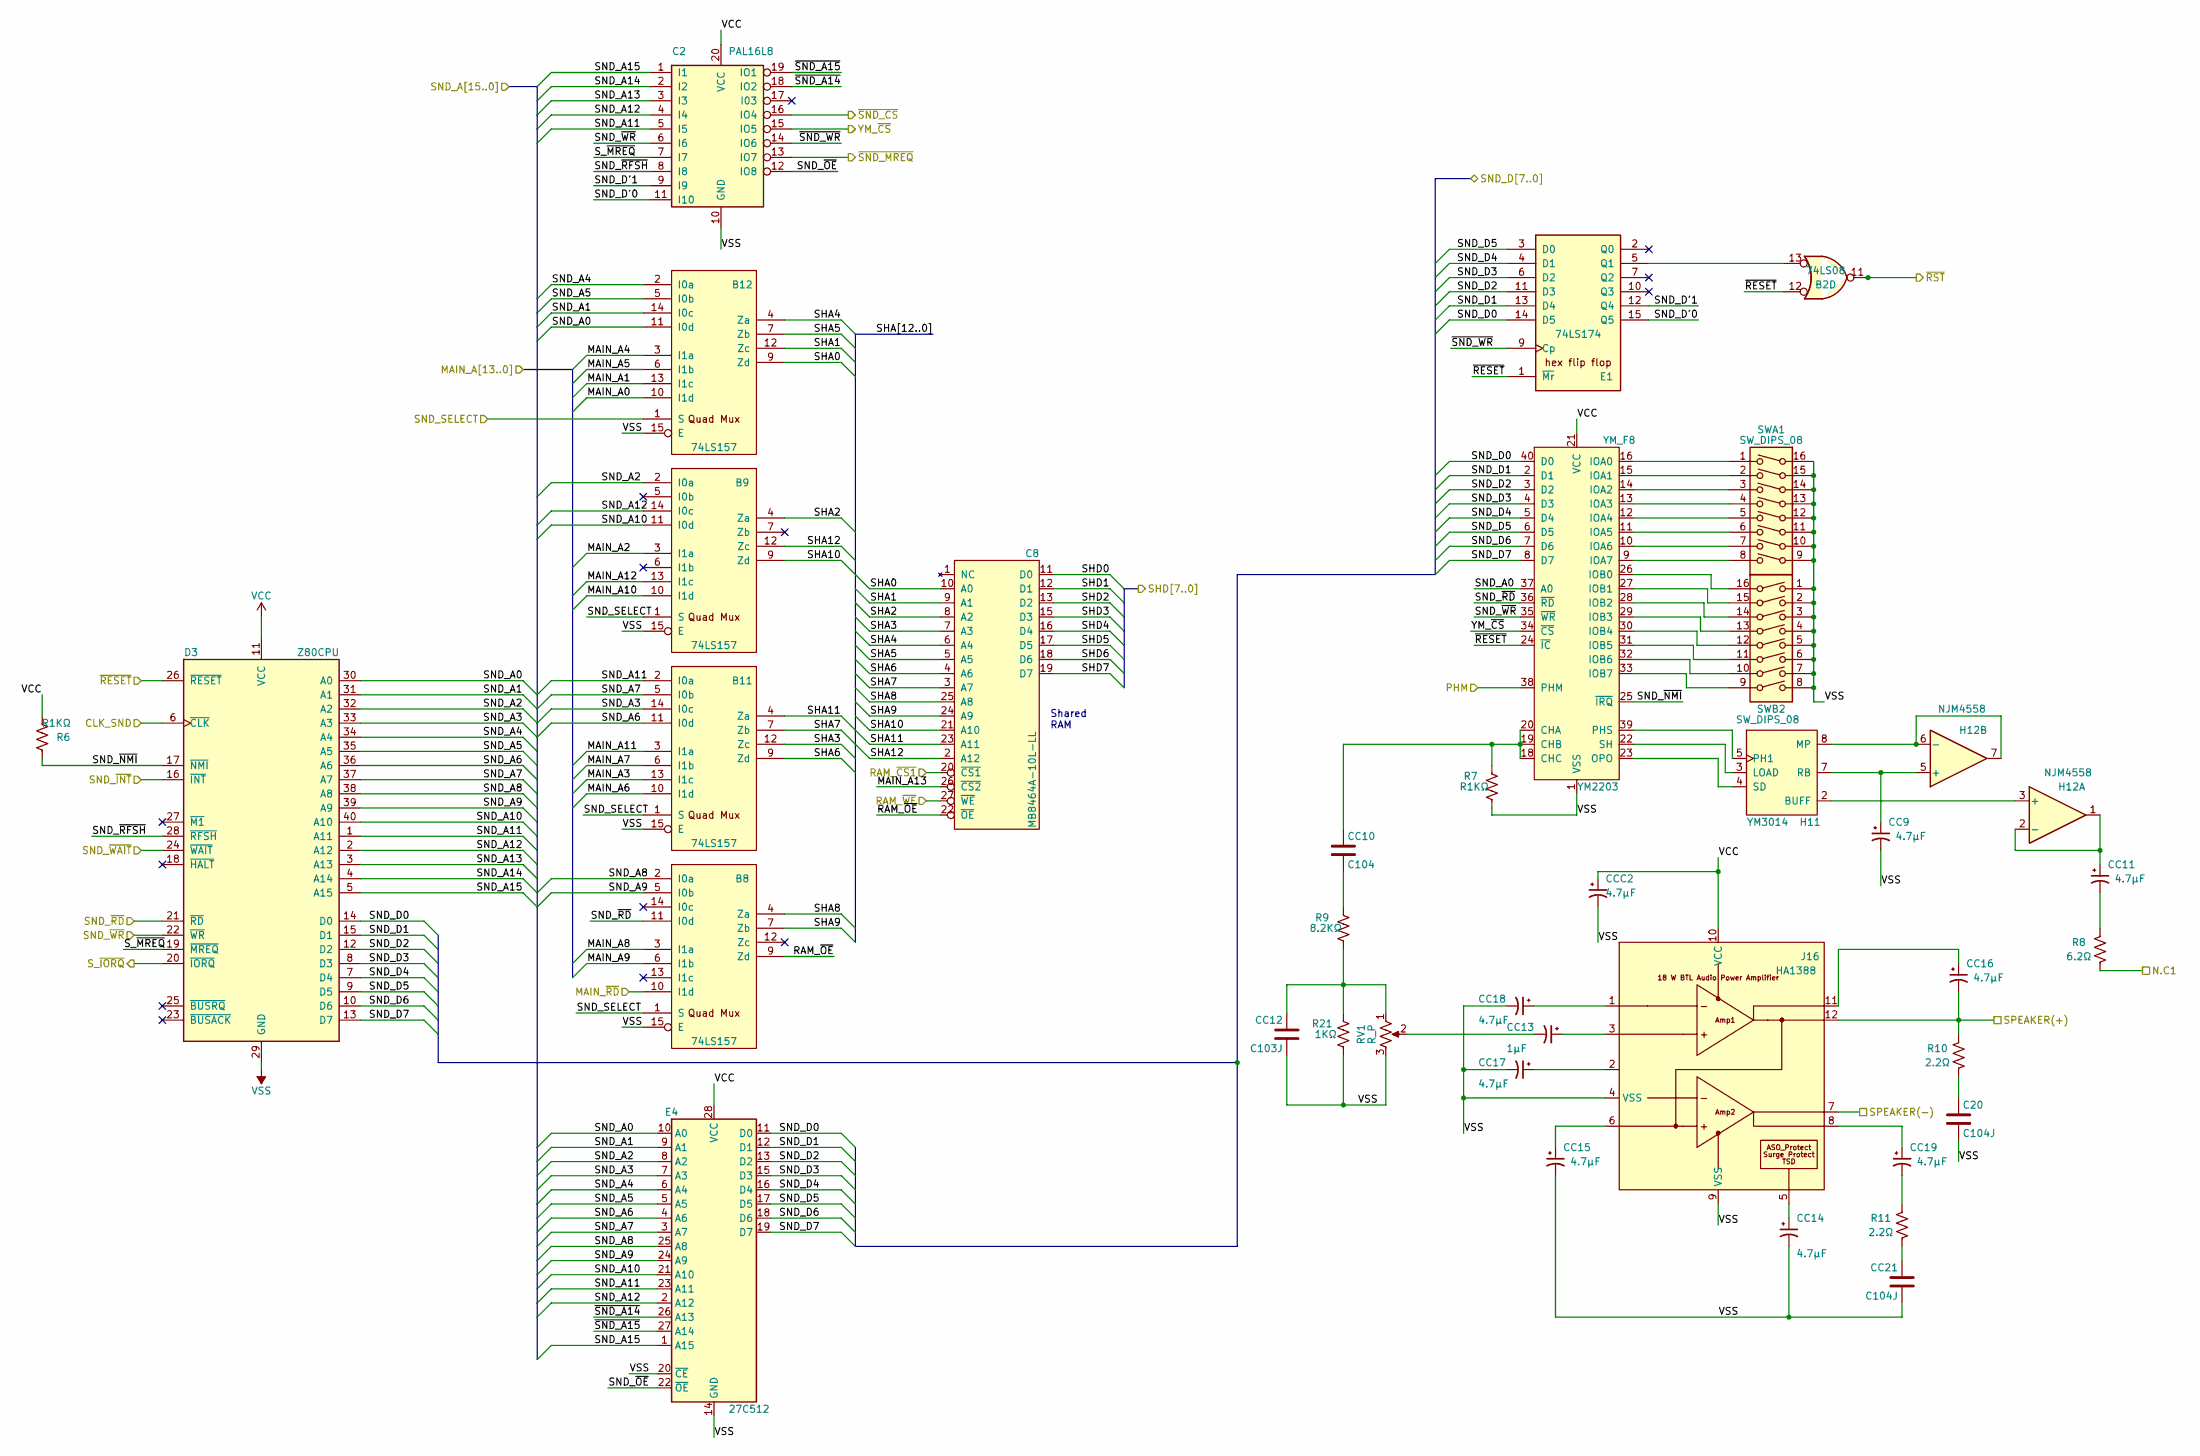
[picture p15: schematic sound.kicad_sch]

Parts:
B2: 74LS08
B8, B9, B11, B12: 74LS157
C2: PAL16L8
C8: MB8464A-10L-LL
C20: C104J
CC9, CC11, CC14, CC15, CC16, CC17, CC18, CC19: 4.7μF
CC10: C104
CC12: C103J
CC13: 1μF
CC21: C104J
CCC2: 4.7μF
D3: Z80CPU
E1: 74LS174
E4: 27C512; DIP-28_W15.24mm
H11: YM3014; DIP-8_W7.62mm
H12: NJM4558
J16: HA1388
R6, R7: R1KΩ
R8: 6.2Ω
R9: 8.2KΩ
R10, R11: 2.2Ω
R21: 1KΩ
RV1: R_P
SWA1: SW_DIPS_08
SWB2: SW_DIPS_08
YM_F8: YM2203; DIP-40_W15.24mm

Connections:
CLK_SND: D3.6 (~CLK)
MAIN_A0: B12.10 (I1d)
MAIN_A1: B12.13 (I1c)
MAIN_A2: B9.3 (I1a)
MAIN_A3: B11.13 (I1c)
MAIN_A4: B12.3 (I1a)
MAIN_A5: B12.6 (I1b)
MAIN_A6: B11.10 (I1d)
MAIN_A7: B11.6 (I1b)
MAIN_A8: B8.3 (I1a)
MAIN_A9: B8.6 (I1b)
MAIN_A10: B9.10 (I1d)
MAIN_A11: B11.3 (I1a)
MAIN_A12: B9.13 (I1c)
MAIN_A13: C8.26 (~CS2)
MAIN_~RD: B8.10 (I1d)
N.C1: R8.2
unnamed: B2.13, E1.5 (Q1)
unnamed: C20.1, R10.2
unnamed: CC9.1, H11.7 (RB), H12.5 (+)
unnamed: CC10.1, R7.2, YM_F8.18 (CHC), YM_F8.19 (CHB), YM_F8.20 (CHA)
unnamed: CC10.2, R9.2
unnamed: CC11.1, H12.1, H12.2 (-)
unnamed: CC11.2, R8.1
unnamed: CC12.1, R9.1, R21.2, RV1.1
unnamed: CC13.1, J16.3
unnamed: CC13.2, RV1.2
unnamed: CC14.1, J16.5
unnamed: CC15.1, J16.6
unnamed: CC16.1, J16.11
unnamed: CC17.1, J16.2
unnamed: CC18.1, J16.1
unnamed: CC19.1, J16.8
unnamed: CC19.2, R11.1
unnamed: CC21.1, R11.2
unnamed: H11.2 (BUFF), H12.3 (+)
unnamed: H11.3 (LOAD), YM_F8.22 (SH)
unnamed: H11.4 (SD), YM_F8.23 (OPO)
unnamed: H11.5 (PH1), YM_F8.39 (PHS)
unnamed: H11.8 (MP), H12.6 (-), H12.7
unnamed: SWA1.1, YM_F8.16 (IOA0)
unnamed: SWA1.2, YM_F8.15 (IOA1)
unnamed: SWA1.3, YM_F8.14 (IOA2)
unnamed: SWA1.4, YM_F8.13 (IOA3)
unnamed: SWA1.5, YM_F8.12 (IOA4)
unnamed: SWA1.6, YM_F8.11 (IOA5)
unnamed: SWA1.7, YM_F8.10 (IOA6)
unnamed: SWA1.8, YM_F8.9 (IOA7)
unnamed: SWB2.9, YM_F8.33 (IOB7)
unnamed: SWB2.10, YM_F8.32 (IOB6)
unnamed: SWB2.11, YM_F8.31 (IOB5)
unnamed: SWB2.12, YM_F8.30 (IOB4)
unnamed: SWB2.13, YM_F8.29 (IOB3)
unnamed: SWB2.14, YM_F8.28 (IOB2)
unnamed: SWB2.15, YM_F8.27 (IOB1)
unnamed: SWB2.16, YM_F8.26 (IOB0)
PHM: YM_F8.38 (PHM)
RAM_~CS1: C8.20 (~CS1)
RAM_~OE: B8.9 (Zd), C8.22 (~OE)
RAM_~WE: C8.27 (~WE)
SHA0: B12.9 (Zd), C8.10 (A0)
SHA1: B12.12 (Zc), C8.9 (A1)
SHA2: B9.4 (Za), C8.8 (A2)
SHA3: B11.12 (Zc), C8.7 (A3)
SHA4: B12.4 (Za), C8.6 (A4)
SHA5: B12.7 (Zb), C8.5 (A5)
SHA6: B11.9 (Zd), C8.4 (A6)
SHA7: B11.7 (Zb), C8.3 (A7)
SHA8: B8.4 (Za), C8.25 (A8)
SHA9: B8.7 (Zb), C8.24 (A9)
SHA10: B9.9 (Zd), C8.21 (A10)
SHA11: B11.4 (Za), C8.23 (A11)
SHA12: B9.12 (Zc), C8.2 (A12)
SHD0: C8.11 (D0)
SHD1: C8.12 (D1)
SHD2: C8.13 (D2)
SHD3: C8.15 (D3)
SHD4: C8.16 (D4)
SHD5: C8.17 (D5)
SHD6: C8.18 (D6)
SHD7: C8.19 (D7)
SND_A0: B12.11 (I0d), D3.30 (A0), E4.10 (A0), YM_F8.37 (A0)
SND_A1: B12.14 (I0c), D3.31 (A1), E4.9 (A1)
SND_A2: B9.2 (I0a), D3.32 (A2), E4.8 (A2)
SND_A3: B11.14 (I0c), D3.33 (A3), E4.7 (A3)
SND_A4: B12.2 (I0a), D3.34 (A4), E4.6 (A4)
SND_A5: B12.5 (I0b), D3.35 (A5), E4.5 (A5)
SND_A6: B11.11 (I0d), D3.36 (A6), E4.4 (A6)
SND_A7: B11.5 (I0b), D3.37 (A7), E4.3 (A7)
SND_A8: B8.2 (I0a), D3.38 (A8), E4.25 (A8)
SND_A9: B8.5 (I0b), D3.39 (A9), E4.24 (A9)
SND_A10: B9.11 (I0d), D3.40 (A10), E4.21 (A10)
SND_A11: B11.2 (I0a), C2.5 (I5), D3.1 (A11), E4.23 (A11)
SND_A12: B9.14 (I0c), C2.4 (I4), D3.2 (A12), E4.2 (A12)
SND_A13: C2.3 (I3), D3.3 (A13)
SND_A14: C2.2 (I2), D3.4 (A14)
SND_A15: C2.1 (I1), D3.5 (A15), E4.1 (A15)
SND_D0: D3.14 (D0), E1.14 (D5), E4.11 (D0), YM_F8.40 (D0)
SND_D1: D3.15 (D1), E1.13 (D4), E4.12 (D1), YM_F8.2 (D1)
SND_D2: D3.12 (D2), E1.11 (D3), E4.13 (D2), YM_F8.3 (D2)
SND_D3: D3.8 (D3), E1.6 (D2), E4.15 (D3), YM_F8.4 (D3)
SND_D4: D3.7 (D4), E1.4 (D1), E4.16 (D4), YM_F8.5 (D4)
SND_D5: D3.9 (D5), E1.3 (D0), E4.17 (D5), YM_F8.6 (D5)
SND_D6: D3.10 (D6), E4.18 (D6), YM_F8.7 (D6)
SND_D7: D3.13 (D7), E4.19 (D7), YM_F8.8 (D7)
SND_D'0: C2.11 (I10), E1.15 (Q5)
SND_D'1: C2.9 (I9), E1.12 (Q4)
SND_SELECT: B8.1 (S), B9.1 (S), B11.1 (S), B12.1 (S)
SND_~INT: D3.16 (~INT)
SND_~NMI: D3.17 (~NMI), R6.2, YM_F8.25 (~IRQ)
SND_~OE: C2.12 (IO8), E4.22 (~OE)
SND_~RD: B8.11 (I0d), D3.21 (~RD), YM_F8.36 (~RD)
SND_~RFSH: C2.8 (I8), D3.28 (~RFSH)
SND_~WAIT: D3.24 (~WAIT)
SND_~WR: C2.6 (I6), D3.22 (~WR), YM_F8.35 (~WR)
SPEAKER(+): CC16.2, J16.12, R10.1
SPEAKER(-): J16.7
S_~IORQ: D3.20 (~IORQ)
S_~MREQ: C2.7 (I7), D3.19 (~MREQ)
VCC: C2.20 (VCC), CCC2.1, D3.11 (VCC), E4.28 (VCC), J16.10 (VCC), R6.1, YM_F8.21 (VCC)
VSS: B8.15 (E), B9.15 (E), B11.15 (E), B12.15 (E), C2.10 (GND), C20.2, CC9.2, CC12.2, CC14.2, CC15.2, CC17.2, CC18.2, CC21.2, CCC2.2, D3.29 (GND), E4.14 (GND), E4.20 (~CE), J16.4 (VSS), J16.9 (VSS), R7.1, R21.1, RV1.3, SWA1.9, SWA1.10, SWA1.11, SWA1.12, SWA1.13, SWA1.14, SWA1.15, SWA1.16, SWB2.1, SWB2.2, SWB2.3, SWB2.4, SWB2.5, SWB2.6, SWB2.7, SWB2.8, YM_F8.1 (VSS)
YM_~CS: C2.15 (IO5), YM_F8.34 (~CS)
~RESET: B2.12, D3.26 (~RESET), E1.1 (~Mr), YM_F8.24 (~IC)
~RST: B2.11
~SND_A14: C2.18 (IO2), E4.26 (A13)
~SND_A15: C2.19 (IO1), E4.27 (A14)
~SND_CS: C2.16 (IO4)
~SND_MREQ: C2.13 (IO7)
~SND_WR: C2.14 (IO6), E1.9 (Cp)

Notes on the sheet:
Shared RAM
