skutis/jtbubl/cores/kiwi/sch/exterm/exterm.kicad_sch

## KiCad design cores/kiwi/sch/exterm/exterm.kicad_sch (2023-01-22)

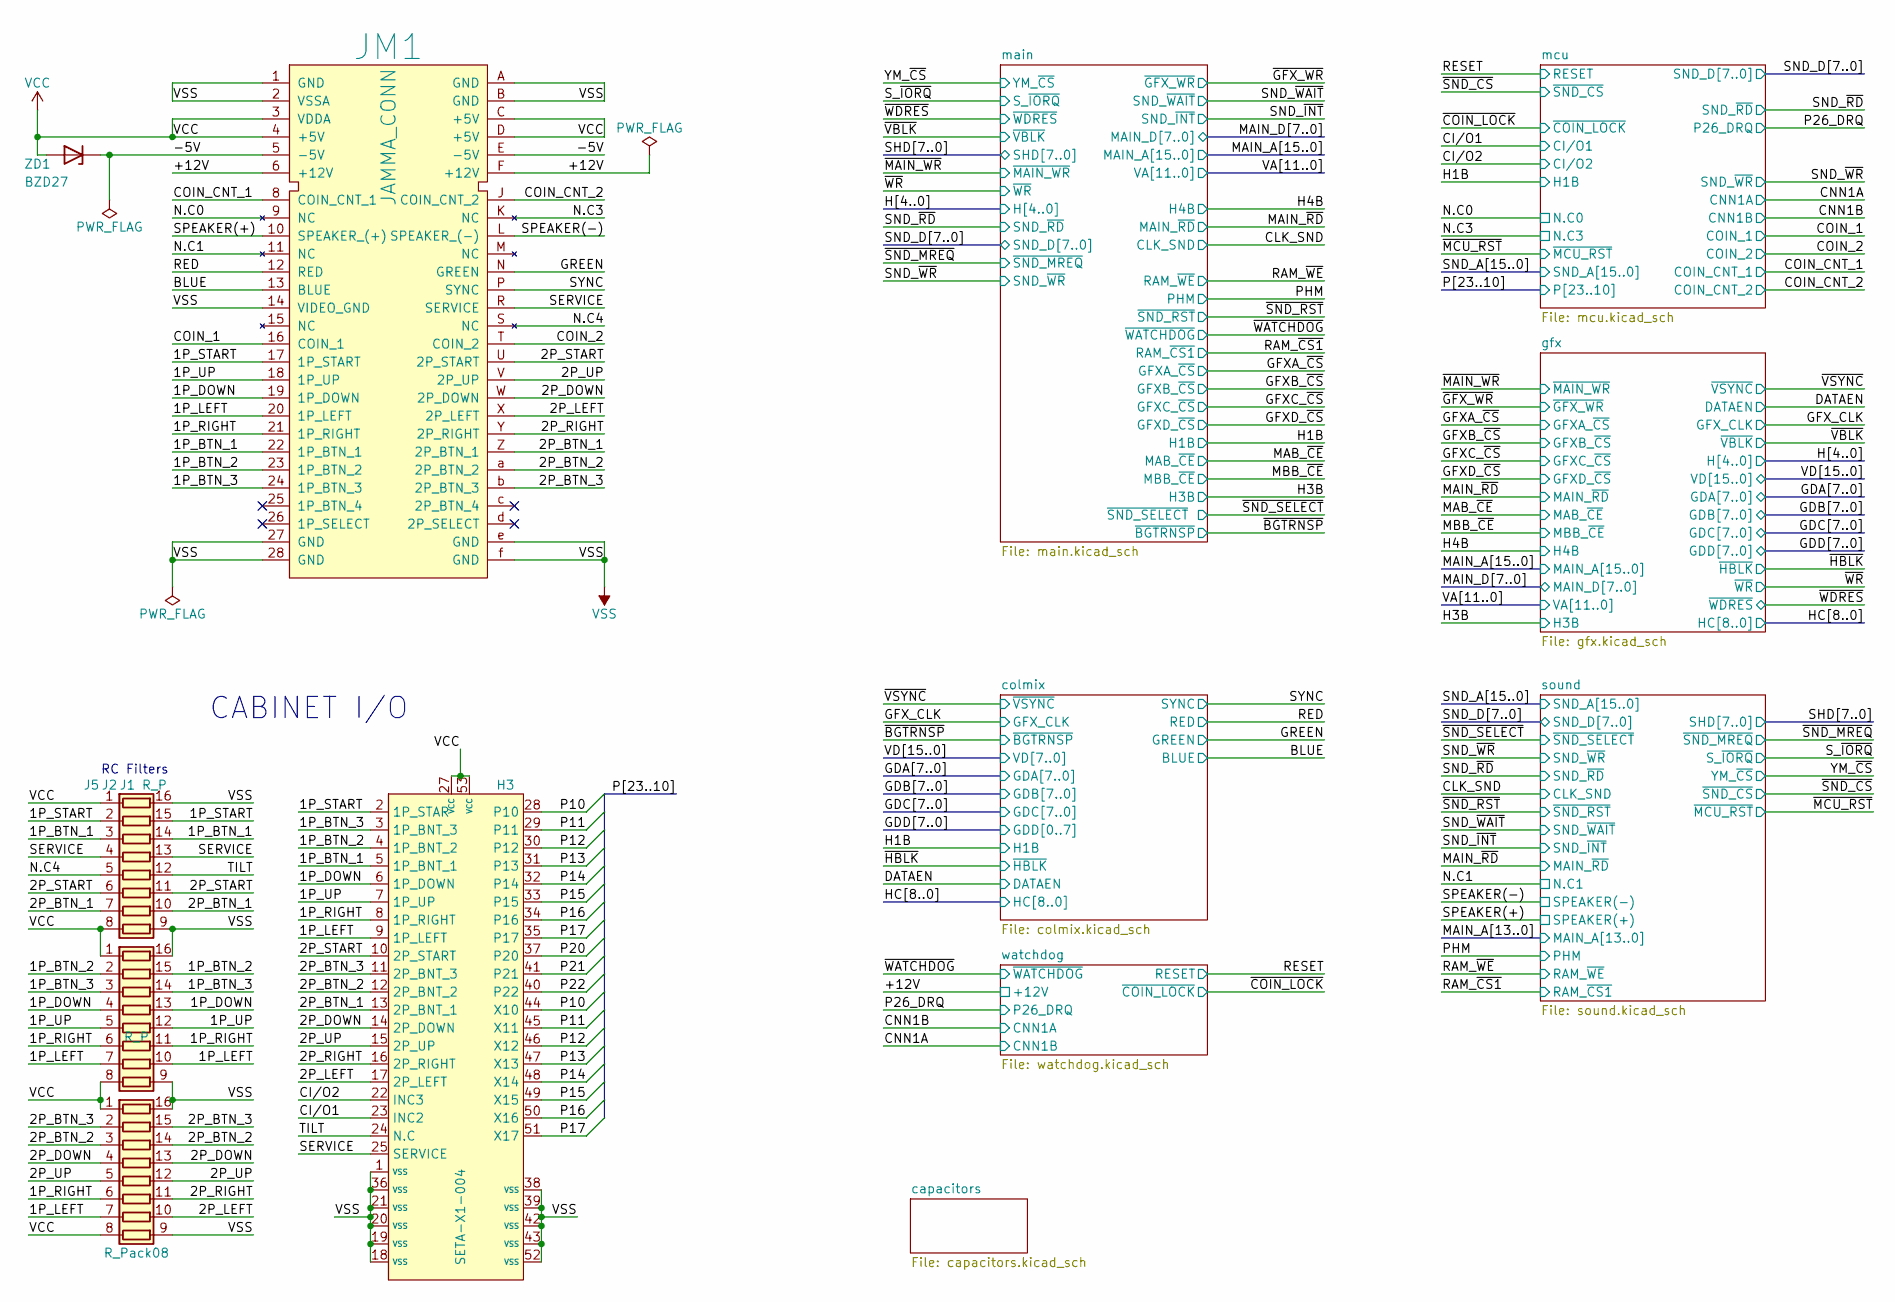
[picture p16: schematic exterm.kicad_sch]

Parts:
H3: SETA-X1-004
J1: R_Pack08
J2, J5: R_P
JM1: JAMMA_CONN
ZD1: BZD27; D_SMF

Connections:
1P_BTN_1: H3.5 (1P_BNT_1), J5.3 (R3.1), J5.14 (R3.2), JM1.22 (1P_BTN_1)
1P_BTN_2: H3.4 (1P_BNT_2), J2.2 (R2.1), J2.15 (R2.2), JM1.23 (1P_BTN_2)
1P_BTN_3: H3.3 (1P_BNT_3), J2.3 (R3.1), J2.14 (R3.2), JM1.24 (1P_BTN_3)
1P_DOWN: H3.6 (1P_DOWN), J2.4 (R4.1), J2.13 (R4.2), JM1.19 (1P_DOWN)
1P_LEFT: H3.9 (1P_LEFT), J1.7 (R7.1), J2.7 (R7.1), J2.10 (R7.2), JM1.20 (1P_LEFT)
1P_RIGHT: H3.8 (1P_RIGHT), J1.6 (R6.1), J2.6 (R6.1), J2.11 (R6.2), JM1.21 (1P_RIGHT)
1P_START: H3.2 (1P_STAR), J5.2 (R2.1), J5.15 (R2.2), JM1.17 (1P_START)
1P_UP: H3.7 (1P_UP), J2.5 (R5.1), J2.12 (R5.2), JM1.18 (1P_UP)
2P_BTN_1: H3.13 (2P_BNT_1), J5.7 (R7.1), J5.10 (R7.2), JM1.Z (2P_BTN_1)
2P_BTN_2: H3.12 (2P_BNT_2), J1.3 (R3.1), J1.14 (R3.2), JM1.a (2P_BTN_2)
2P_BTN_3: H3.11 (2P_BNT_3), J1.2 (R2.1), J1.15 (R2.2), JM1.b (2P_BTN_3)
2P_DOWN: H3.14 (2P_DOWN), J1.4 (R4.1), J1.13 (R4.2), JM1.W (2P_DOWN)
2P_LEFT: H3.17 (2P_LEFT), J1.10 (R7.2), JM1.X (2P_LEFT)
2P_RIGHT: H3.16 (2P_RIGHT), J1.11 (R6.2), JM1.Y (2P_RIGHT)
2P_START: H3.10 (2P_START), J5.6 (R6.1), J5.11 (R6.2), JM1.U (2P_START)
2P_UP: H3.15 (2P_UP), J1.5 (R5.1), J1.12 (R5.2), JM1.V (2P_UP)
+12V: JM1.6 (+12V), JM1.F (+12V)
-5V: JM1.5 (-5V), JM1.E (-5V), ZD1.1 (K)
BLUE: JM1.13 (BLUE)
CI/O1: H3.23 (INC2)
CI/O2: H3.22 (INC3)
COIN_1: JM1.16 (COIN_1)
COIN_2: JM1.T (COIN_2)
COIN_CNT_1: JM1.8 (COIN_CNT_1)
COIN_CNT_2: JM1.J (COIN_CNT_2)
GREEN: JM1.N (GREEN)
N.C0: JM1.9 (NC)
N.C1: JM1.11 (NC)
N.C3: JM1.K (NC)
N.C4: J5.5 (R5.1), JM1.S (NC)
P10: H3.28 (P10), H3.44 (X10)
P11: H3.29 (P11), H3.45 (X11)
P12: H3.30 (P12), H3.46 (X12)
P13: H3.31 (P13), H3.47 (X13)
P14: H3.32 (P14), H3.48 (X14)
P15: H3.33 (P15), H3.49 (X15)
P16: H3.34 (P16), H3.50 (X16)
P17: H3.35 (P17), H3.51 (X17)
P20: H3.37 (P20)
P21: H3.41 (P21)
P22: H3.40 (P22)
RED: JM1.12 (RED)
SERVICE: H3.25 (SERVICE), J5.4 (R4.1), J5.13 (R4.2), JM1.R (SERVICE)
SPEAKER(+): JM1.10 (SPEAKER_(+))
SPEAKER(-): JM1.L (SPEAKER_(-))
SYNC: JM1.P (SYNC)
TILT: H3.24 (N.C), J5.12 (R5.2)
VCC: H3.27 (VCC), H3.53 (VCC), J1.1 (R1.1), J1.8 (R8.1), J2.1 (R1.1), J2.8 (R8.1), J5.1 (R1.1), J5.8 (R8.1), JM1.3 (VDDA), JM1.4 (+5V), JM1.C (+5V), JM1.D (+5V), ZD1.2 (A)
VSS: H3.1 (VSS), H3.18 (VSS), H3.19 (VSS), H3.20 (VSS), H3.21 (VSS), H3.36 (VSS), H3.38 (VSS), H3.39 (VSS), H3.42 (VSS), H3.43 (VSS), H3.52 (VSS), J1.9 (R8.2), J1.16 (R1.2), J2.9 (R8.2), J2.16 (R1.2), J5.9 (R8.2), J5.16 (R1.2), JM1.1 (GND), JM1.2 (VSSA), JM1.14 (VIDEO_GND), JM1.27 (GND), JM1.28 (GND), JM1.A (GND), JM1.B (GND), JM1.e (GND), JM1.f (GND)

Notes on the sheet:
RC Filters
CABINET I/O
