skutis/jtbubl/cores/kiwi/sch/exterm/gfx.kicad_sch

## KiCad design cores/kiwi/sch/exterm/gfx.kicad_sch (2022-12-09)

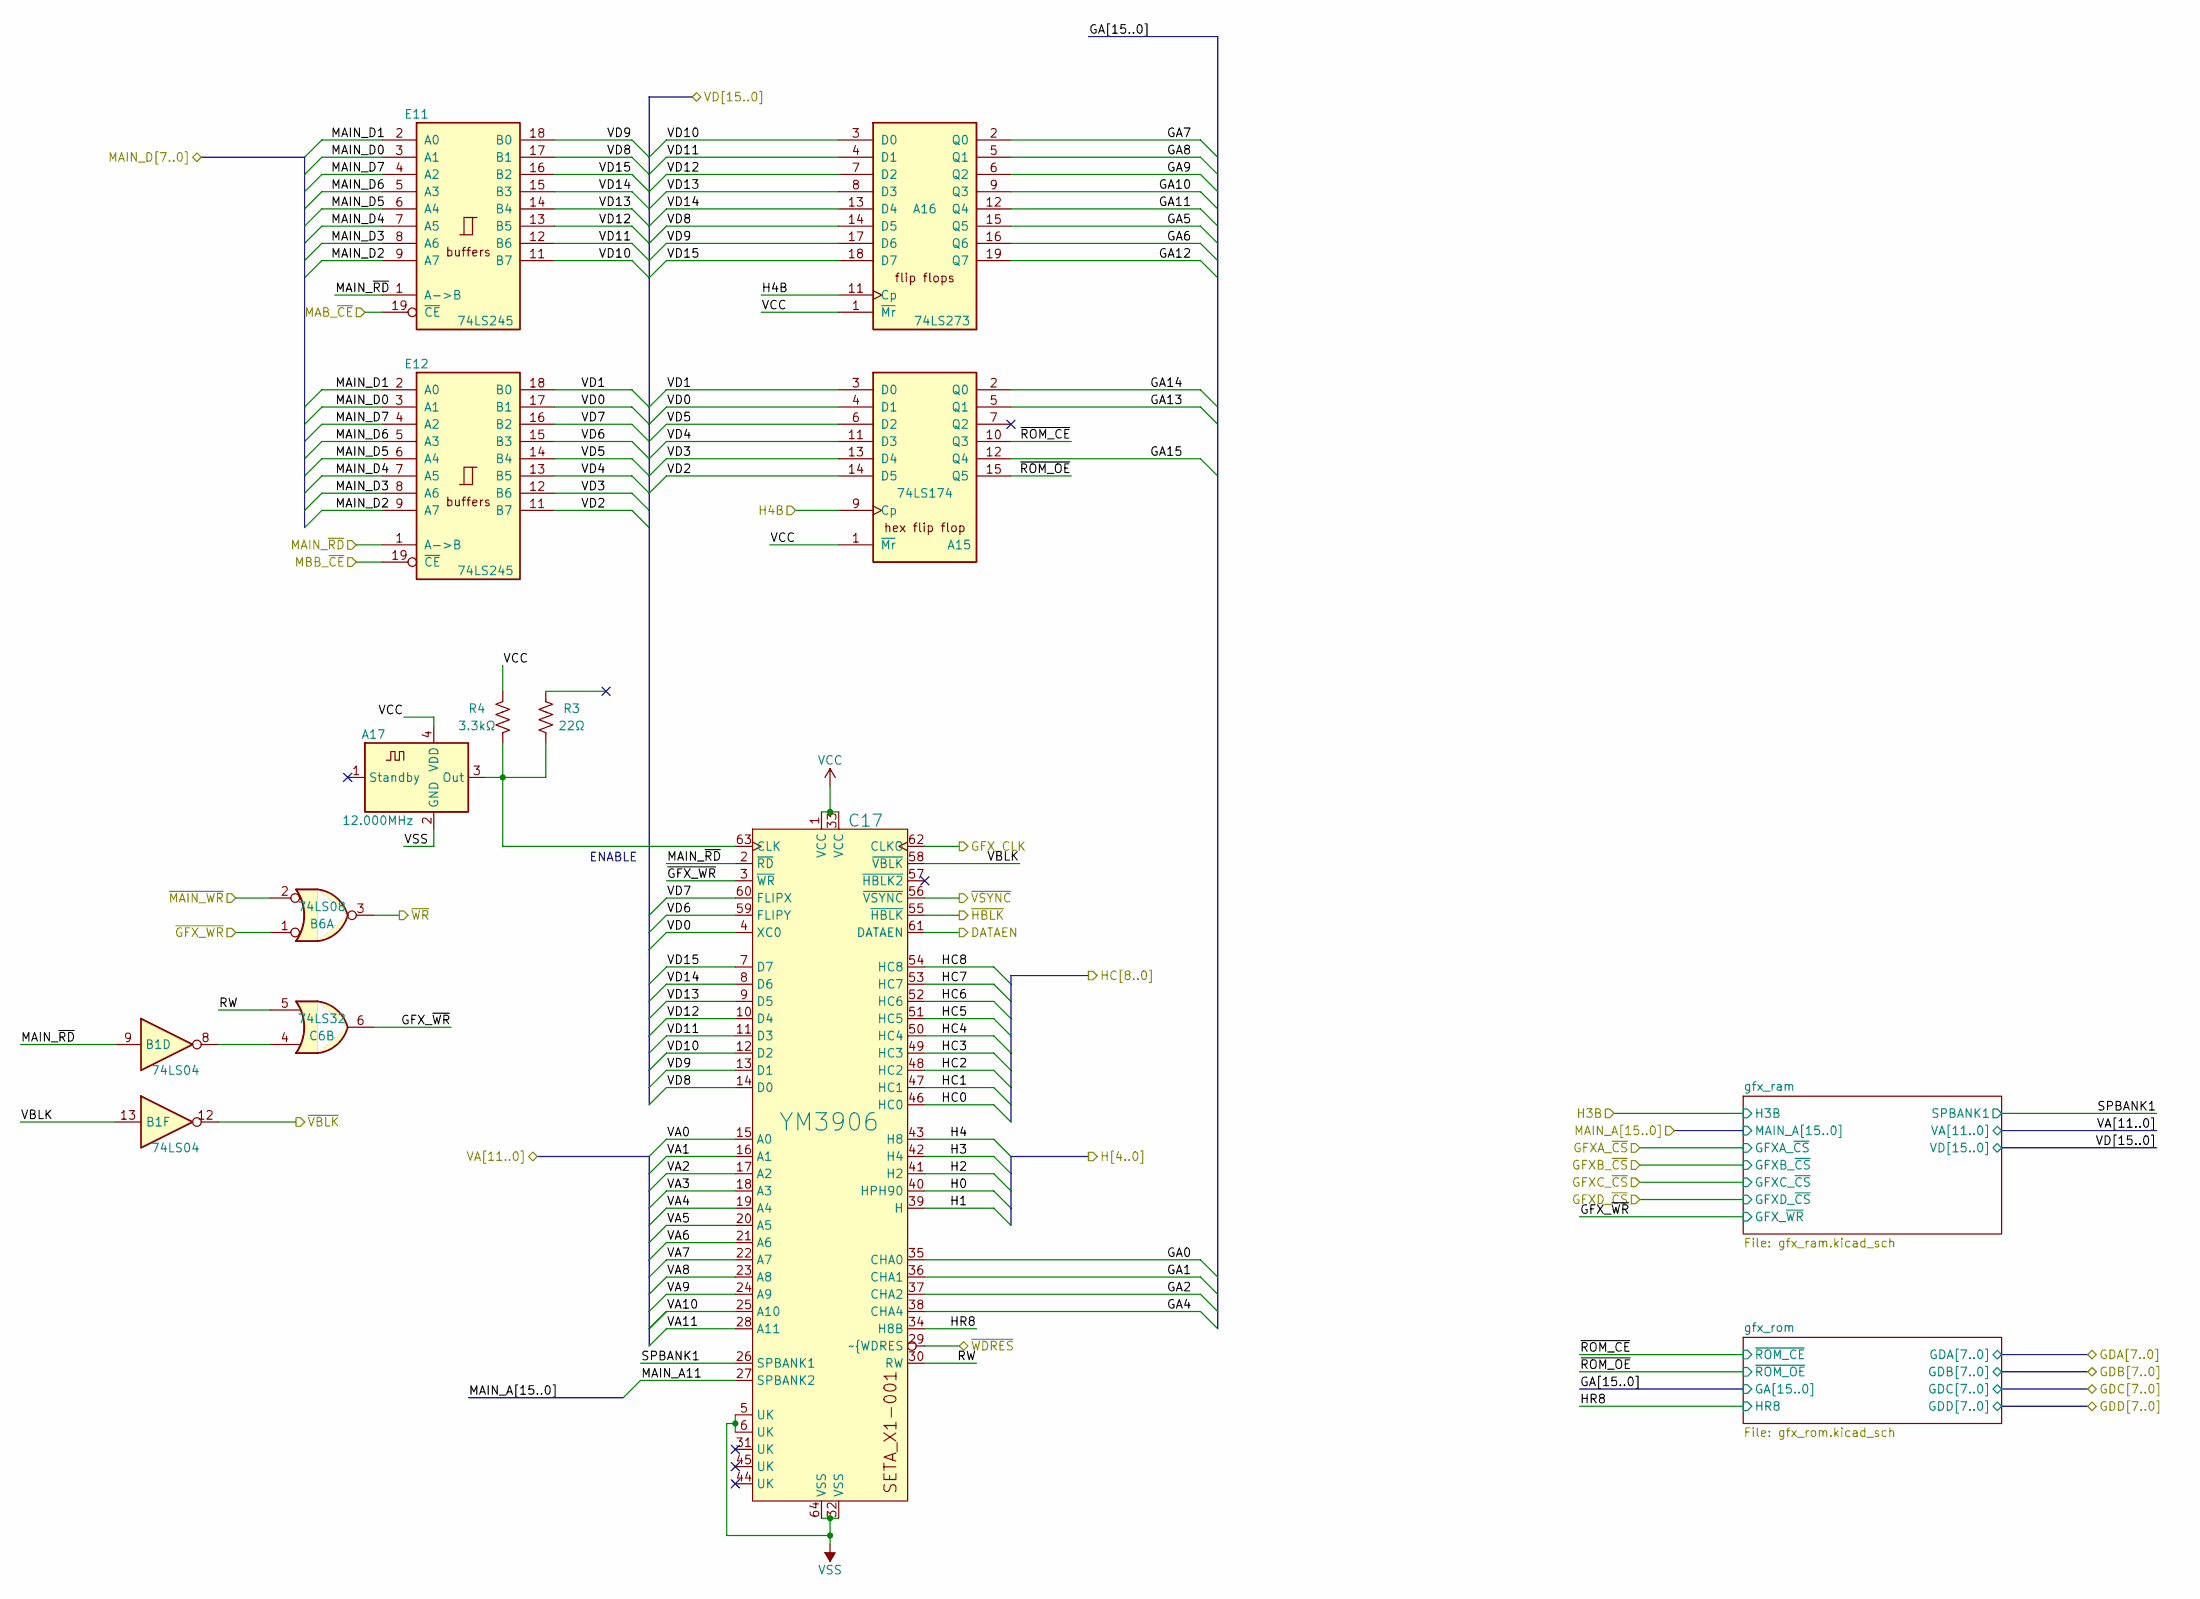
[picture p17: schematic gfx.kicad_sch]

Parts:
A15: 74LS174
A16: 74LS273
A17: 12.000MHz; Oscillator_SMD_Abracon_ASDMB-4Pin_2.5x2.0mm
B1: 74LS04
B6: 74LS08
C6: 74LS32
C17: YM3906
E11, E12: 74LS245
R3: 22Ω
R4: 3.3kΩ

Connections:
DATAEN: C17.61 (DATAEN)
GA0: C17.35 (CHA0)
GA1: C17.36 (CHA1)
GA2: C17.37 (CHA2)
GA4: C17.38 (CHA4)
GA5: A16.15 (Q5)
GA6: A16.16 (Q6)
GA7: A16.2 (Q0)
GA8: A16.5 (Q1)
GA9: A16.6 (Q2)
GA10: A16.9 (Q3)
GA11: A16.12 (Q4)
GA12: A16.19 (Q7)
GA13: A15.5 (Q1)
GA14: A15.2 (Q0)
GA15: A15.12 (Q4)
GFX_CLK: C17.62 (CLKO)
GFX_~WR: C6.6
H0: C17.40 (HPH90)
H1: C17.39 (H)
H2: C17.41 (H2)
H3: C17.42 (H4)
H4: C17.43 (H8)
H4B: A15.9 (Cp), A16.11 (Cp)
HC0: C17.46 (HC0)
HC1: C17.47 (HC1)
HC2: C17.48 (HC2)
HC3: C17.49 (HC3)
HC4: C17.50 (HC4)
HC5: C17.51 (HC5)
HC6: C17.52 (HC6)
HC7: C17.53 (HC7)
HC8: C17.54 (HC8)
HR8: C17.34 (H8B)
MAB_~CE: E11.19 (~CE)
MAIN_A11: C17.27 (SPBANK2)
MAIN_D0: E11.3 (A1), E12.3 (A1)
MAIN_D1: E11.2 (A0), E12.2 (A0)
MAIN_D2: E11.9 (A7), E12.9 (A7)
MAIN_D3: E11.8 (A6), E12.8 (A6)
MAIN_D4: E11.7 (A5), E12.7 (A5)
MAIN_D5: E11.6 (A4), E12.6 (A4)
MAIN_D6: E11.5 (A3), E12.5 (A3)
MAIN_D7: E11.4 (A2), E12.4 (A2)
MAIN_~RD: B1.9, C17.2 (~RD), E11.1 (A->B), E12.1 (A->B)
MBB_~CE: E12.19 (~CE)
unnamed: A17.3 (Out), C17.63 (CLK), R3.2, R4.2
unnamed: B1.8, C6.4
RW: C6.5, C17.30 (RW)
SPBANK1: C17.26 (SPBANK1)
VA0: C17.15 (A0)
VA1: C17.16 (A1)
VA2: C17.17 (A2)
VA3: C17.18 (A3)
VA4: C17.19 (A4)
VA5: C17.20 (A5)
VA6: C17.21 (A6)
VA7: C17.22 (A7)
VA8: C17.23 (A8)
VA9: C17.24 (A9)
VA10: C17.25 (A10)
VA11: C17.28 (A11)
VBLK: B1.13, C17.58 (~VBLK)
VCC: A15.1 (~Mr), A16.1 (~Mr), A17.4 (VDD), C17.1 (VCC), C17.33 (VCC), R4.1
VD0: A15.4 (D1), C17.4 (XC0), E12.17 (B1)
VD1: A15.3 (D0), E12.18 (B0)
VD2: A15.14 (D5), E12.11 (B7)
VD3: A15.13 (D4), E12.12 (B6)
VD4: A15.11 (D3), E12.13 (B5)
VD5: A15.6 (D2), E12.14 (B4)
VD6: C17.59 (FLIPY), E12.15 (B3)
VD7: C17.60 (FLIPX), E12.16 (B2)
VD8: A16.14 (D5), C17.14 (D0), E11.17 (B1)
VD9: A16.17 (D6), C17.13 (D1), E11.18 (B0)
VD10: A16.3 (D0), C17.12 (D2), E11.11 (B7)
VD11: A16.4 (D1), C17.11 (D3), E11.12 (B6)
VD12: A16.7 (D2), C17.10 (D4), E11.13 (B5)
VD13: A16.8 (D3), C17.9 (D5), E11.14 (B4)
VD14: A16.13 (D4), C17.8 (D6), E11.15 (B3)
VD15: A16.18 (D7), C17.7 (D7), E11.16 (B2)
VSS: A17.2 (GND), C17.5 (UK), C17.6 (UK), C17.32 (VSS), C17.64 (VSS)
~GFX_WR: B6.1, C17.3 (~WR)
~HBLK: C17.55 (~HBLK)
~MAIN_WR: B6.2
~ROM_CE: A15.10 (Q3)
~ROM_OE: A15.15 (Q5)
~VBLK: B1.12
~VSYNC: C17.56 (~VSYNC)
~WDRES: C17.29 (~{WDRES)
~WR: B6.3

Notes on the sheet:
ENABLE
