skutis/jtbubl/cores/kiwi/sch/exterm/gfx_ram.kicad_sch

## KiCad design cores/kiwi/sch/exterm/gfx_ram.kicad_sch (2022-12-09)

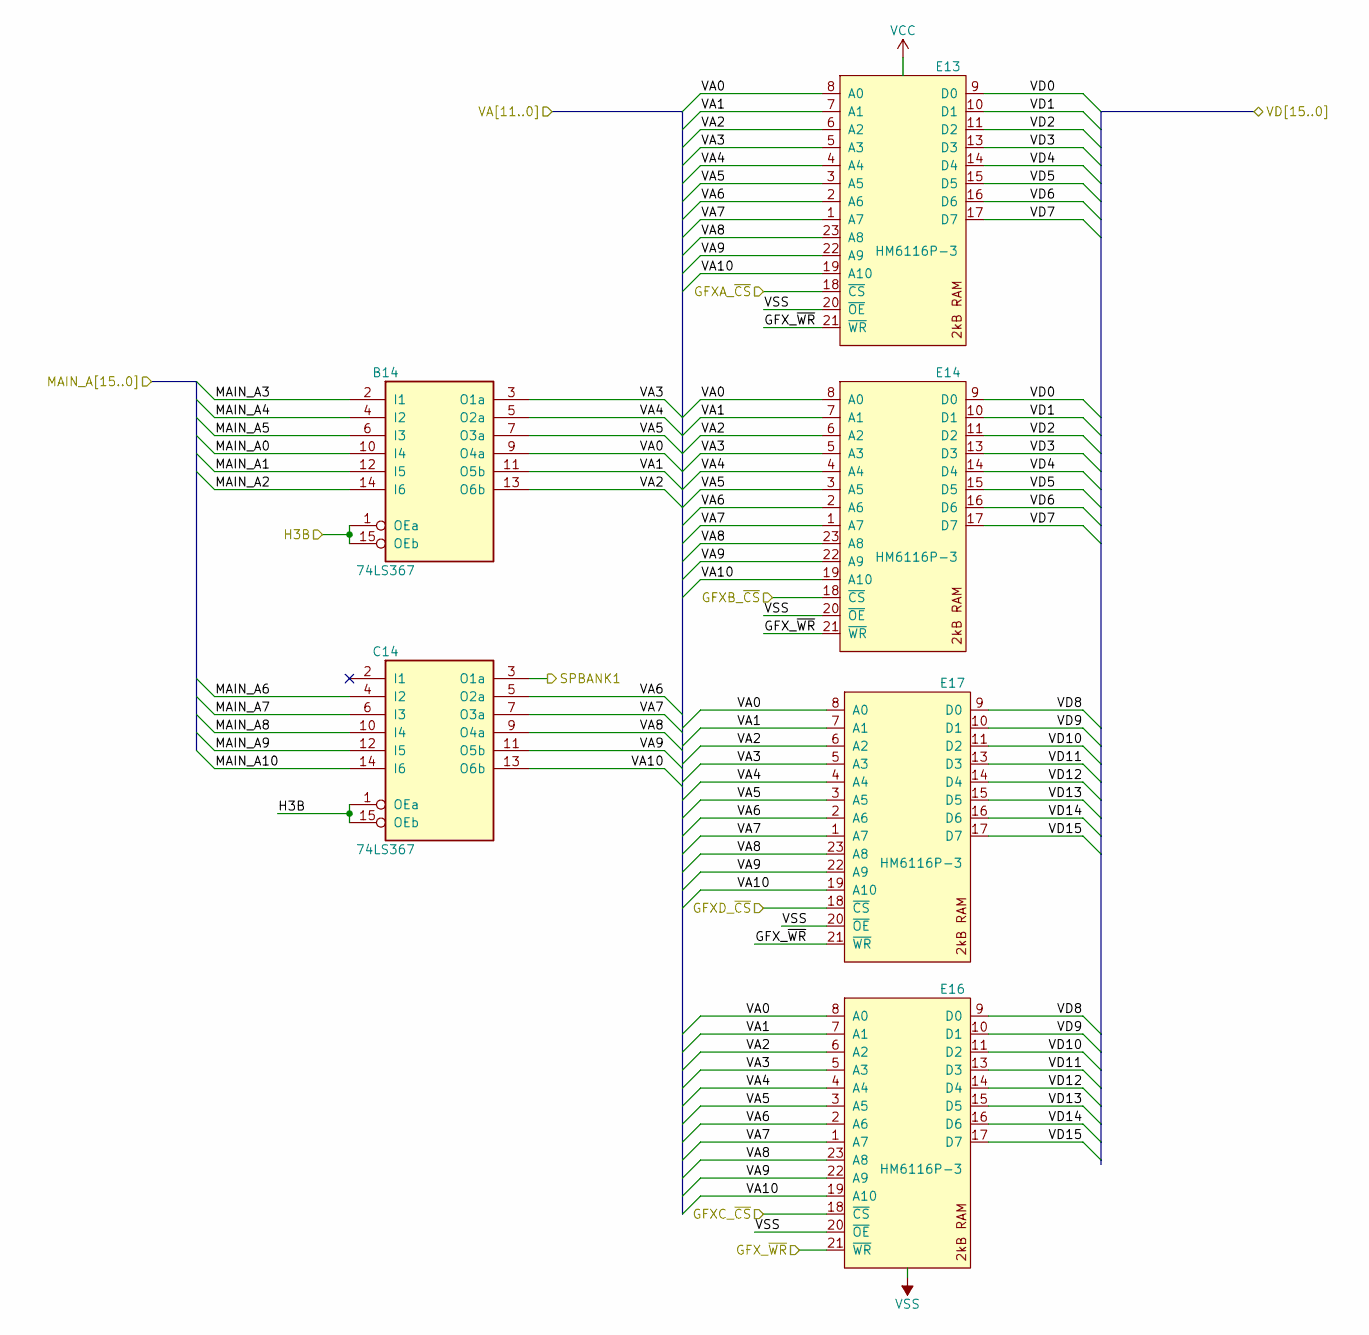
[picture p18: schematic gfx_ram.kicad_sch]

Parts:
B14: 74LS367
C14: 74LS367
E13, E14, E16, E17: HM6116P-3

Connections:
GFXA_~CS: E13.18 (~CS)
GFXB_~CS: E14.18 (~CS)
GFXC_~CS: E16.18 (~CS)
GFXD_~CS: E17.18 (~CS)
GFX_~WR: E13.21 (~WR), E14.21 (~WR), E16.21 (~WR), E17.21 (~WR)
H3B: B14.1 (OEa), B14.15 (OEb), C14.1 (OEa), C14.15 (OEb)
MAIN_A0: B14.10 (I4)
MAIN_A1: B14.12 (I5)
MAIN_A2: B14.14 (I6)
MAIN_A3: B14.2 (I1)
MAIN_A4: B14.4 (I2)
MAIN_A5: B14.6 (I3)
MAIN_A6: C14.4 (I2)
MAIN_A7: C14.6 (I3)
MAIN_A8: C14.10 (I4)
MAIN_A9: C14.12 (I5)
MAIN_A10: C14.14 (I6)
SPBANK1: C14.3 (O1a)
VA0: B14.9 (O4a), E13.8 (A0), E14.8 (A0), E16.8 (A0), E17.8 (A0)
VA1: B14.11 (O5b), E13.7 (A1), E14.7 (A1), E16.7 (A1), E17.7 (A1)
VA2: B14.13 (O6b), E13.6 (A2), E14.6 (A2), E16.6 (A2), E17.6 (A2)
VA3: B14.3 (O1a), E13.5 (A3), E14.5 (A3), E16.5 (A3), E17.5 (A3)
VA4: B14.5 (O2a), E13.4 (A4), E14.4 (A4), E16.4 (A4), E17.4 (A4)
VA5: B14.7 (O3a), E13.3 (A5), E14.3 (A5), E16.3 (A5), E17.3 (A5)
VA6: C14.5 (O2a), E13.2 (A6), E14.2 (A6), E16.2 (A6), E17.2 (A6)
VA7: C14.7 (O3a), E13.1 (A7), E14.1 (A7), E16.1 (A7), E17.1 (A7)
VA8: C14.9 (O4a), E13.23 (A8), E14.23 (A8), E16.23 (A8), E17.23 (A8)
VA9: C14.11 (O5b), E13.22 (A9), E14.22 (A9), E16.22 (A9), E17.22 (A9)
VA10: C14.13 (O6b), E13.19 (A10), E14.19 (A10), E16.19 (A10), E17.19 (A10)
VCC: E13.24 (VCC)
VD0: E13.9 (D0), E14.9 (D0)
VD1: E13.10 (D1), E14.10 (D1)
VD2: E13.11 (D2), E14.11 (D2)
VD3: E13.13 (D3), E14.13 (D3)
VD4: E13.14 (D4), E14.14 (D4)
VD5: E13.15 (D5), E14.15 (D5)
VD6: E13.16 (D6), E14.16 (D6)
VD7: E13.17 (D7), E14.17 (D7)
VD8: E16.9 (D0), E17.9 (D0)
VD9: E16.10 (D1), E17.10 (D1)
VD10: E16.11 (D2), E17.11 (D2)
VD11: E16.13 (D3), E17.13 (D3)
VD12: E16.14 (D4), E17.14 (D4)
VD13: E16.15 (D5), E17.15 (D5)
VD14: E16.16 (D6), E17.16 (D6)
VD15: E16.17 (D7), E17.17 (D7)
VSS: E13.20 (~OE), E14.20 (~OE), E16.12 (VSS), E16.20 (~OE), E17.20 (~OE)
