skutis/jtbubl/cores/kiwi/sch/exterm/gfx_rom.kicad_sch

## KiCad design cores/kiwi/sch/exterm/gfx_rom.kicad_sch (2022-12-09)

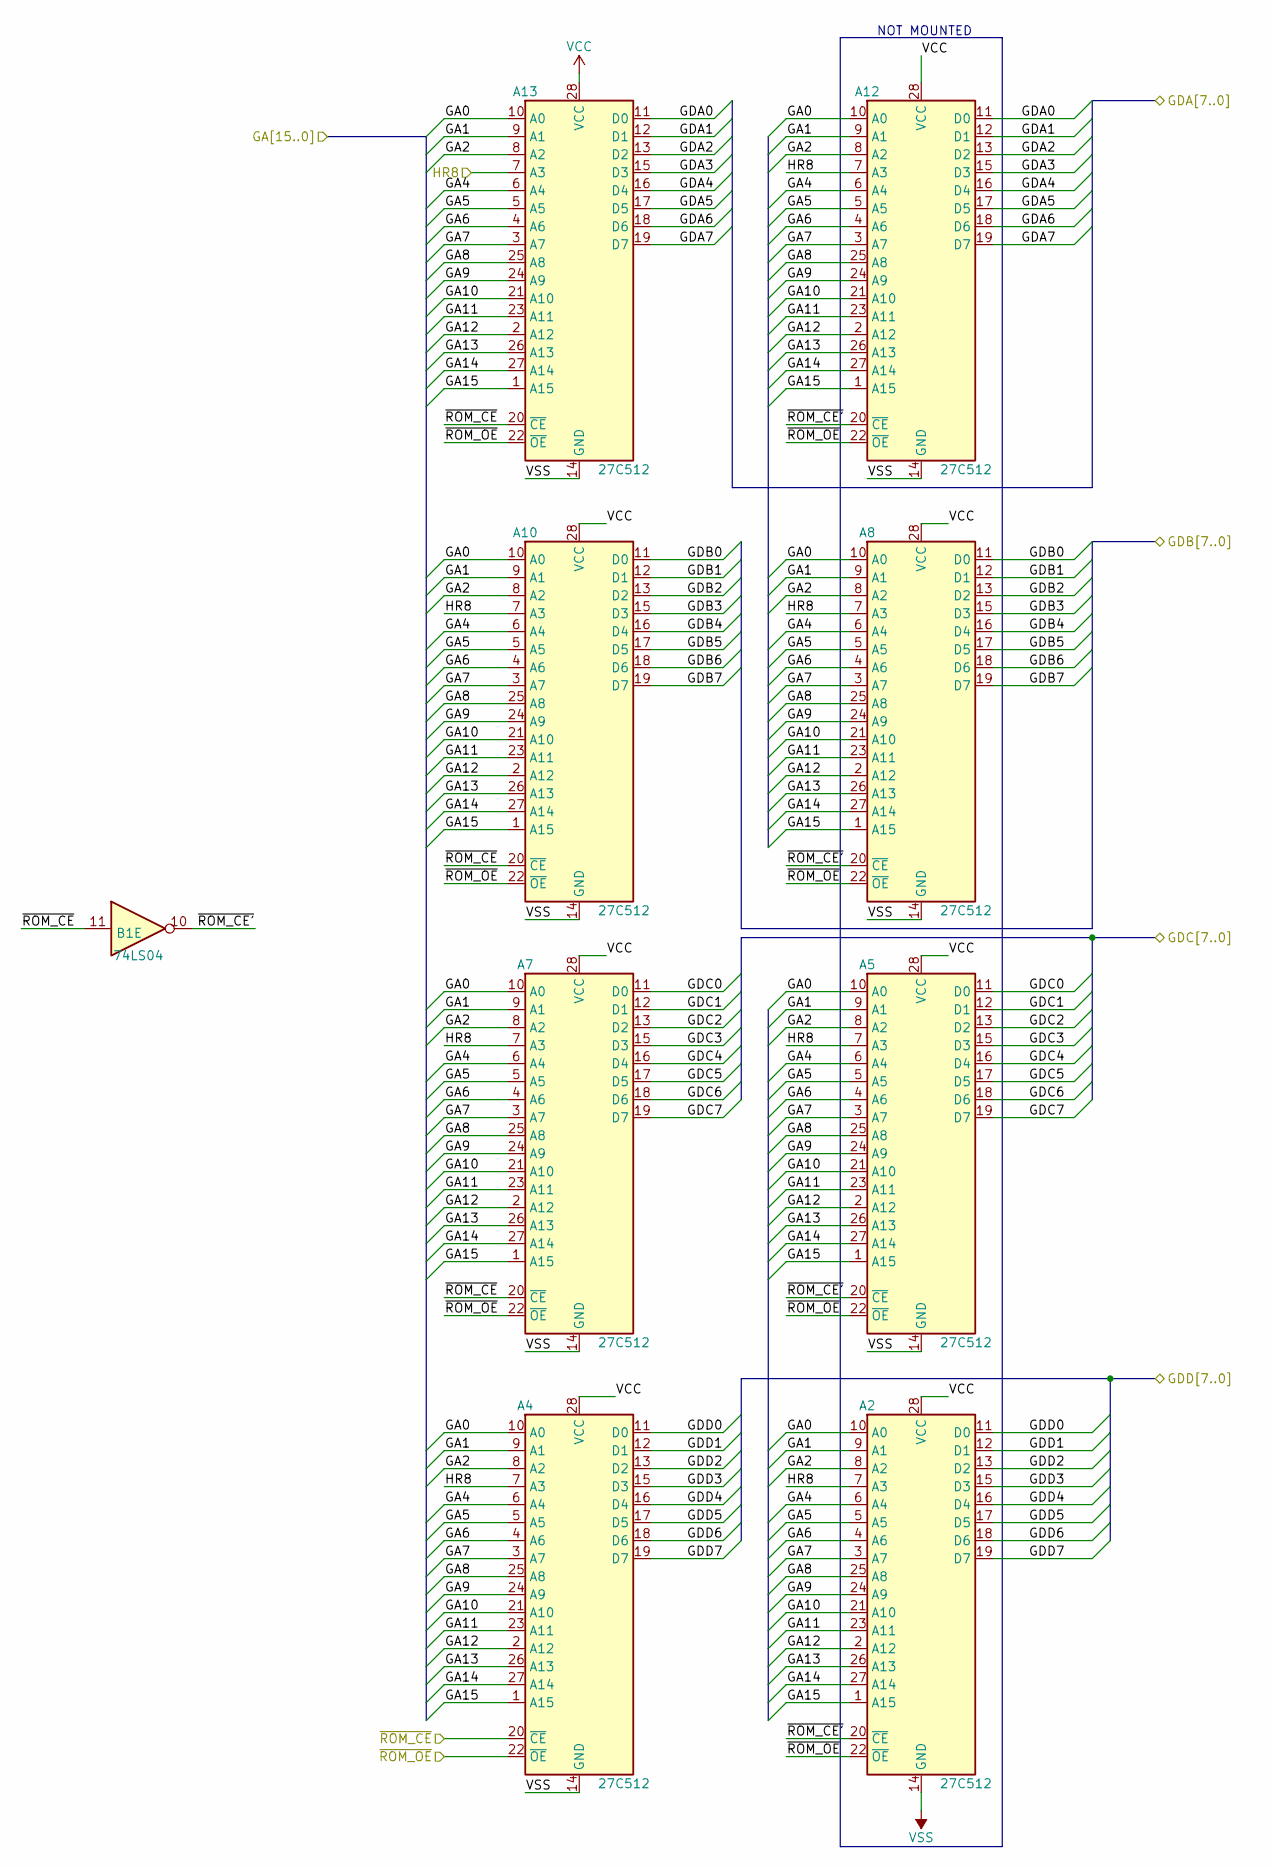
[picture p19: schematic gfx_rom.kicad_sch]

Parts:
A2, A4, A5, A7, A8, A10, A12, A13: 27C512; DIP-28_W15.24mm
B1: 74LS04

Connections:
GA0: A2.10 (A0), A4.10 (A0), A5.10 (A0), A7.10 (A0), A8.10 (A0), A10.10 (A0), A12.10 (A0), A13.10 (A0)
GA1: A2.9 (A1), A4.9 (A1), A5.9 (A1), A7.9 (A1), A8.9 (A1), A10.9 (A1), A12.9 (A1), A13.9 (A1)
GA2: A2.8 (A2), A4.8 (A2), A5.8 (A2), A7.8 (A2), A8.8 (A2), A10.8 (A2), A12.8 (A2), A13.8 (A2)
GA4: A2.6 (A4), A4.6 (A4), A5.6 (A4), A7.6 (A4), A8.6 (A4), A10.6 (A4), A12.6 (A4), A13.6 (A4)
GA5: A2.5 (A5), A4.5 (A5), A5.5 (A5), A7.5 (A5), A8.5 (A5), A10.5 (A5), A12.5 (A5), A13.5 (A5)
GA6: A2.4 (A6), A4.4 (A6), A5.4 (A6), A7.4 (A6), A8.4 (A6), A10.4 (A6), A12.4 (A6), A13.4 (A6)
GA7: A2.3 (A7), A4.3 (A7), A5.3 (A7), A7.3 (A7), A8.3 (A7), A10.3 (A7), A12.3 (A7), A13.3 (A7)
GA8: A2.25 (A8), A4.25 (A8), A5.25 (A8), A7.25 (A8), A8.25 (A8), A10.25 (A8), A12.25 (A8), A13.25 (A8)
GA9: A2.24 (A9), A4.24 (A9), A5.24 (A9), A7.24 (A9), A8.24 (A9), A10.24 (A9), A12.24 (A9), A13.24 (A9)
GA10: A2.21 (A10), A4.21 (A10), A5.21 (A10), A7.21 (A10), A8.21 (A10), A10.21 (A10), A12.21 (A10), A13.21 (A10)
GA11: A2.23 (A11), A4.23 (A11), A5.23 (A11), A7.23 (A11), A8.23 (A11), A10.23 (A11), A12.23 (A11), A13.23 (A11)
GA12: A2.2 (A12), A4.2 (A12), A5.2 (A12), A7.2 (A12), A8.2 (A12), A10.2 (A12), A12.2 (A12), A13.2 (A12)
GA13: A2.26 (A13), A4.26 (A13), A5.26 (A13), A7.26 (A13), A8.26 (A13), A10.26 (A13), A12.26 (A13), A13.26 (A13)
GA14: A2.27 (A14), A4.27 (A14), A5.27 (A14), A7.27 (A14), A8.27 (A14), A10.27 (A14), A12.27 (A14), A13.27 (A14)
GA15: A2.1 (A15), A4.1 (A15), A5.1 (A15), A7.1 (A15), A8.1 (A15), A10.1 (A15), A12.1 (A15), A13.1 (A15)
GDA0: A12.11 (D0), A13.11 (D0)
GDA1: A12.12 (D1), A13.12 (D1)
GDA2: A12.13 (D2), A13.13 (D2)
GDA3: A12.15 (D3), A13.15 (D3)
GDA4: A12.16 (D4), A13.16 (D4)
GDA5: A12.17 (D5), A13.17 (D5)
GDA6: A12.18 (D6), A13.18 (D6)
GDA7: A12.19 (D7), A13.19 (D7)
GDB0: A8.11 (D0), A10.11 (D0)
GDB1: A8.12 (D1), A10.12 (D1)
GDB2: A8.13 (D2), A10.13 (D2)
GDB3: A8.15 (D3), A10.15 (D3)
GDB4: A8.16 (D4), A10.16 (D4)
GDB5: A8.17 (D5), A10.17 (D5)
GDB6: A8.18 (D6), A10.18 (D6)
GDB7: A8.19 (D7), A10.19 (D7)
GDC0: A5.11 (D0), A7.11 (D0)
GDC1: A5.12 (D1), A7.12 (D1)
GDC2: A5.13 (D2), A7.13 (D2)
GDC3: A5.15 (D3), A7.15 (D3)
GDC4: A5.16 (D4), A7.16 (D4)
GDC5: A5.17 (D5), A7.17 (D5)
GDC6: A5.18 (D6), A7.18 (D6)
GDC7: A5.19 (D7), A7.19 (D7)
GDD0: A2.11 (D0), A4.11 (D0)
GDD1: A2.12 (D1), A4.12 (D1)
GDD2: A2.13 (D2), A4.13 (D2)
GDD3: A2.15 (D3), A4.15 (D3)
GDD4: A2.16 (D4), A4.16 (D4)
GDD5: A2.17 (D5), A4.17 (D5)
GDD6: A2.18 (D6), A4.18 (D6)
GDD7: A2.19 (D7), A4.19 (D7)
HR8: A2.7 (A3), A4.7 (A3), A5.7 (A3), A7.7 (A3), A8.7 (A3), A10.7 (A3), A12.7 (A3), A13.7 (A3)
VCC: A2.28 (VCC), A4.28 (VCC), A5.28 (VCC), A7.28 (VCC), A8.28 (VCC), A10.28 (VCC), A12.28 (VCC), A13.28 (VCC)
VSS: A2.14 (GND), A4.14 (GND), A5.14 (GND), A7.14 (GND), A8.14 (GND), A10.14 (GND), A12.14 (GND), A13.14 (GND)
~ROM_CE': A2.20 (~CE), A5.20 (~CE), A8.20 (~CE), A12.20 (~CE), B1.10
~ROM_CE: A4.20 (~CE), A7.20 (~CE), A10.20 (~CE), A13.20 (~CE), B1.11
~ROM_OE: A2.22 (~OE), A4.22 (~OE), A5.22 (~OE), A7.22 (~OE), A8.22 (~OE), A10.22 (~OE), A12.22 (~OE), A13.22 (~OE)

Notes on the sheet:
NOT MOUNTED
