skutis/jtbubl/cores/kiwi/sch/exterm/watchdog.kicad_sch

## KiCad design cores/kiwi/sch/exterm/watchdog.kicad_sch (2022-12-01)

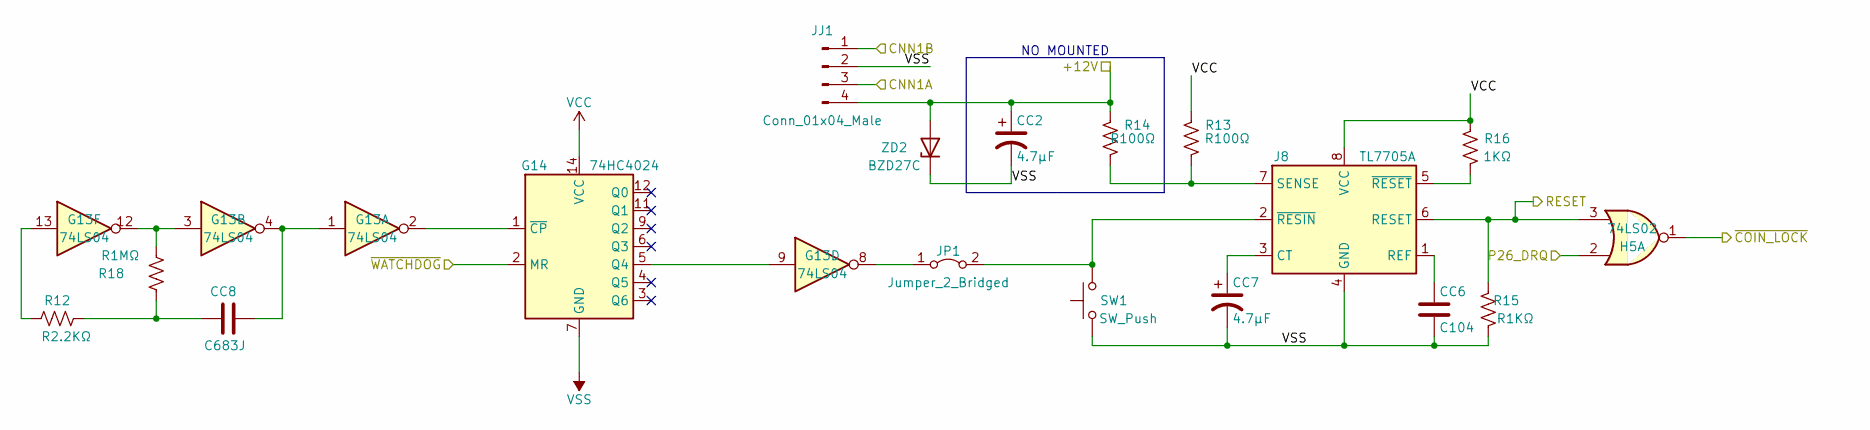
[picture p21: schematic watchdog.kicad_sch]

Parts:
CC2, CC7: 4.7μF
CC6: C104
CC8: C683J
G13: 74LS04
G14: 74HC4024; SOIC-14_3.9x8.7mm_P1.27mm
H5: 74LS02
J8: TL7705A
JJ1: Conn_01x04_Male
JP1: Jumper_2_Bridged
R12: R2.2KΩ
R13, R14: R100Ω
R15: R1KΩ
R16: 1KΩ
R18: R1MΩ
SW1: SW_Push
ZD2: BZD27C; D_SMF

Connections:
+12V: CC2.1, JJ1.4, R14.2, ZD2.2 (A)
CNN1A: JJ1.3
CNN1B: JJ1.1
unnamed: CC6.1, J8.1 (REF)
unnamed: CC7.1, J8.3 (CT)
unnamed: CC8.1, R12.2, R18.1
unnamed: CC8.2, G13.1, G13.4
unnamed: G13.2, G14.1 (~CP)
unnamed: G13.8, JP1.1 (A)
unnamed: G13.9, G14.5 (Q4)
unnamed: G13.3, G13.12, R18.2
unnamed: G13.13, R12.1
unnamed: J8.2 (~RESIN), JP1.2 (B), SW1.2
unnamed: J8.5 (~RESET), R16.1
unnamed: J8.7 (SENSE), R13.1, R14.1
P26_DRQ: H5.2
RESET: H5.3, J8.6 (RESET), R15.2
VCC: G14.14 (VCC), J8.8 (VCC), R13.2, R16.2
VSS: CC2.2, CC6.2, CC7.2, G14.7 (GND), J8.4 (GND), JJ1.2, R15.1, SW1.1, ZD2.1 (K)
~COIN_LOCK: H5.1
~WATCHDOG: G14.2 (MR)

Notes on the sheet:
NO MOUNTED
