skutis/jtbubl/cores/kiwi/sch/insectx/cpu.kicad_sch

## KiCad design cores/kiwi/sch/insectx/cpu.kicad_sch (2022-12-07)

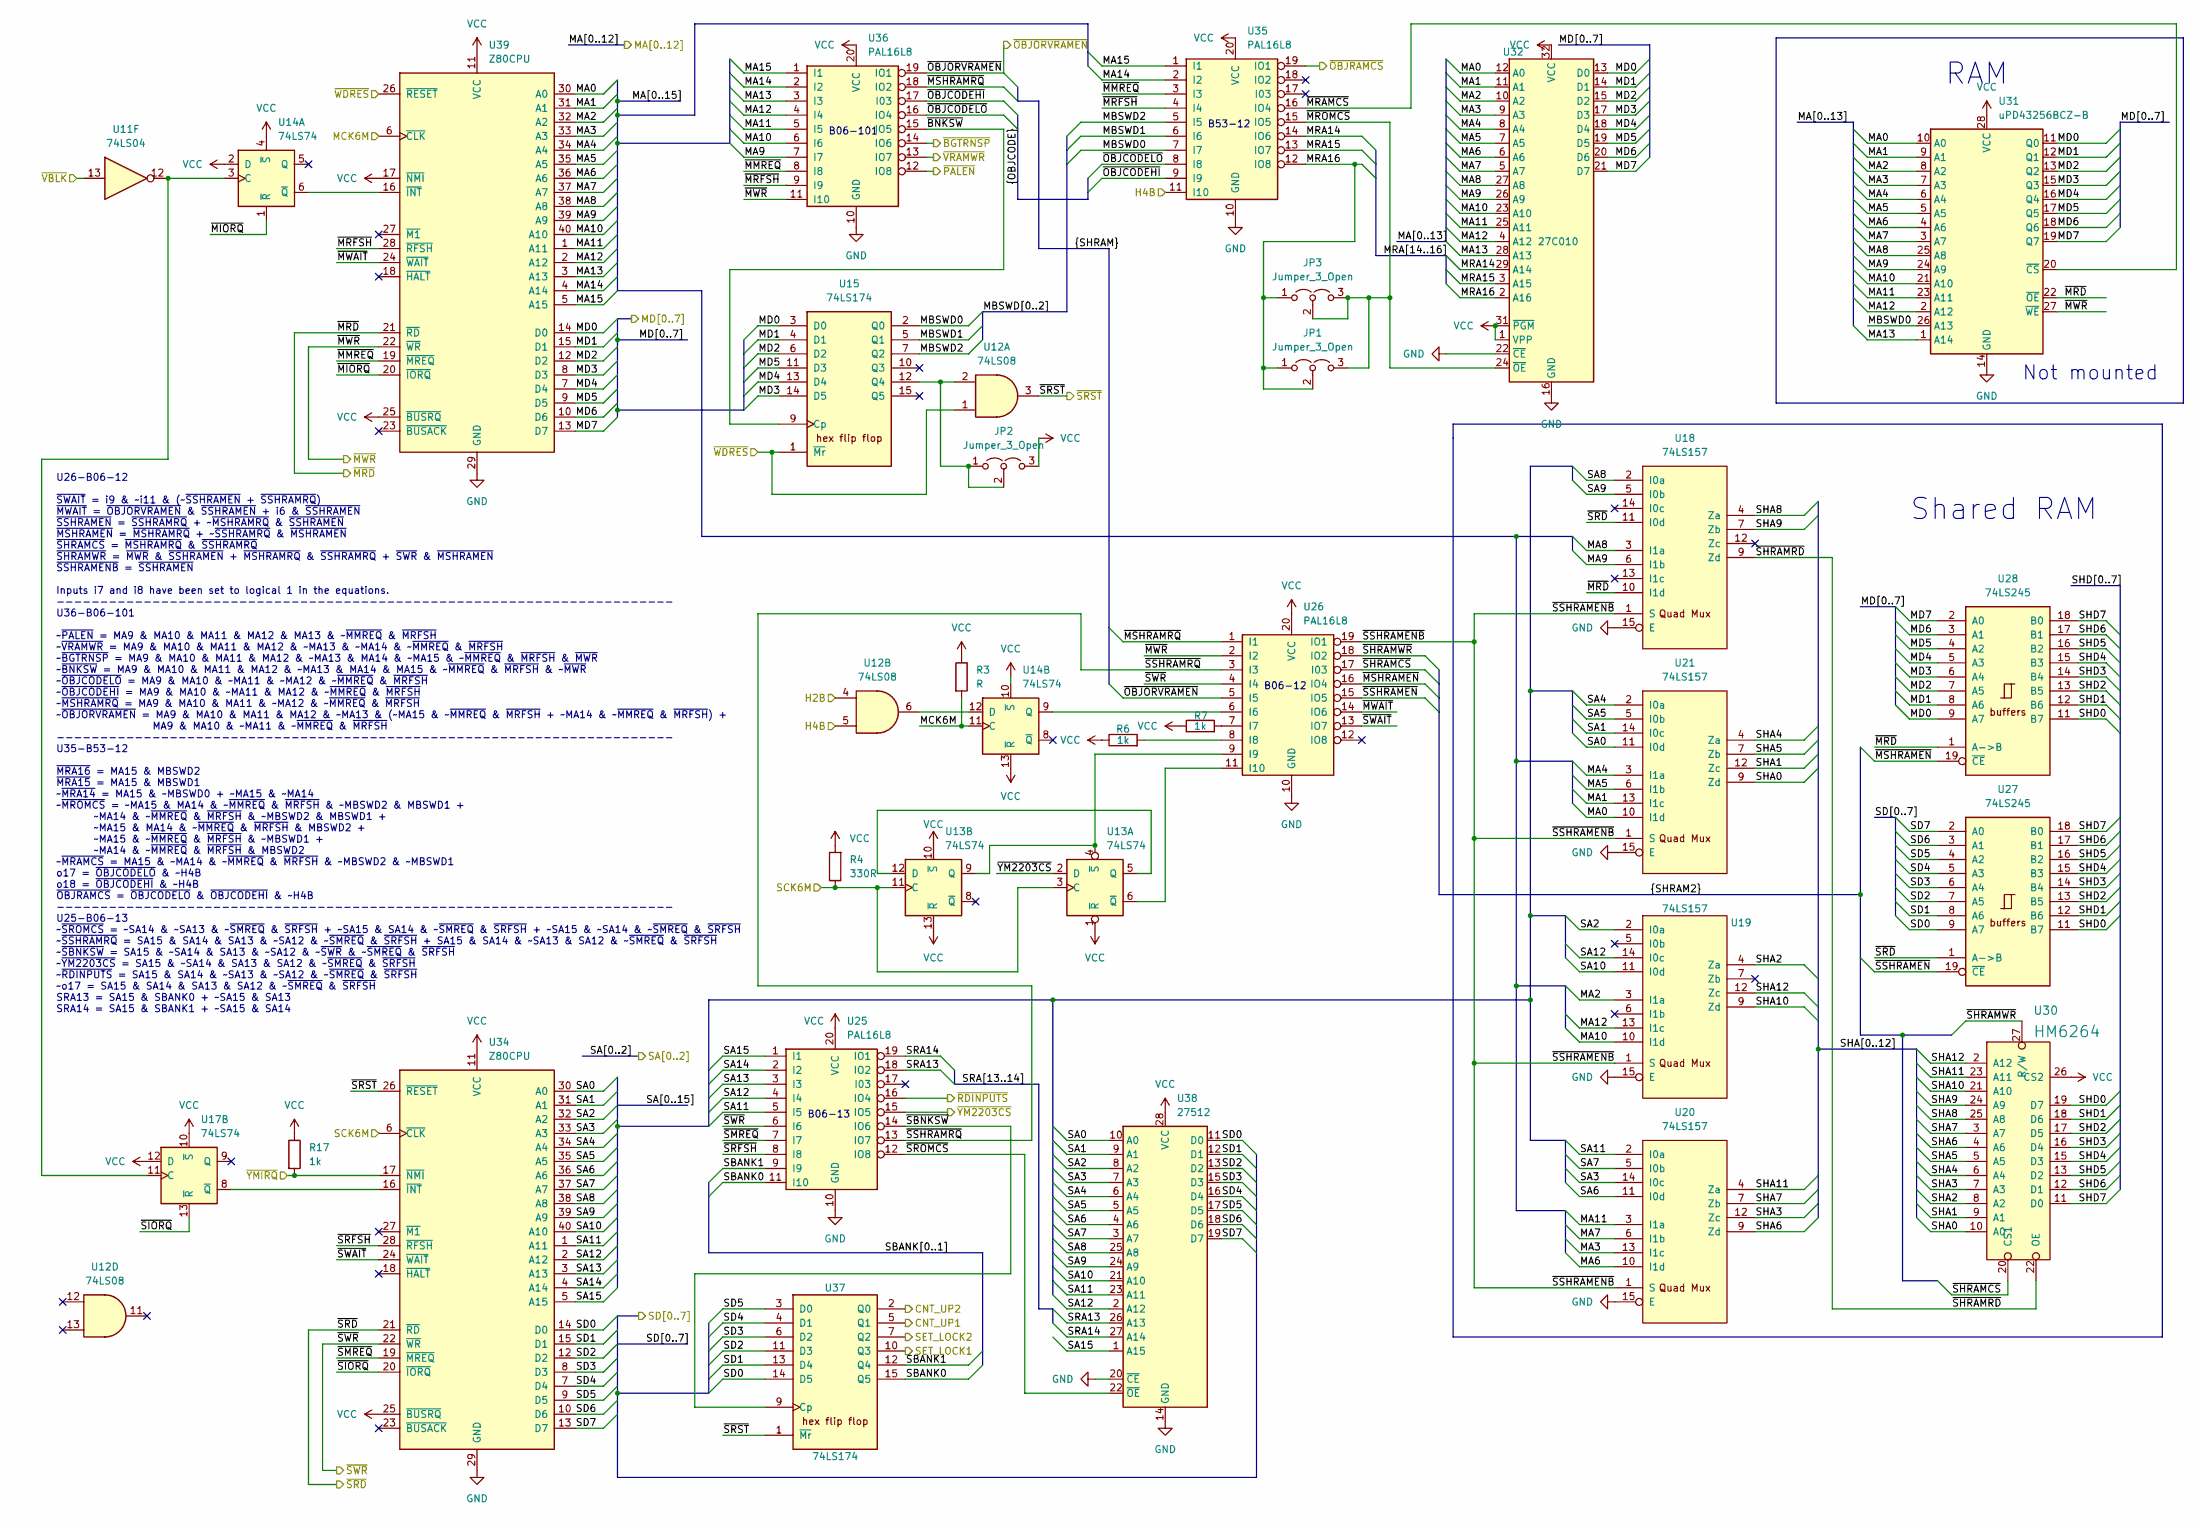
[picture p22: schematic cpu.kicad_sch]

Parts:
JP1, JP2, JP3: Jumper_3_Open
R3: R
R4: 330R
R6, R7, R17: 1k
U11: 74LS04
U12: 74LS08
U13, U14, U17: 74LS74
U15, U37: 74LS174
U18, U19, U20, U21: 74LS157
U25, U26, U35, U36: PAL16L8
U27, U28: 74LS245
U30: HM6264
U31: uPD43256BCZ-B
U32: 27C010
U34, U39: Z80CPU
U38: 27512; DIP-28_W15.24mm

Connections:
CNT_UP1: U37.5 (Q1)
CNT_UP2: U37.2 (Q0)
GND: U18.15 (E), U19.15 (E), U20.15 (E), U21.15 (E), U25.10 (GND), U26.10 (GND), U31.14 (GND), U32.16 (GND), U32.22 (~CE), U34.29 (GND), U35.10 (GND), U36.10 (GND), U38.14 (GND), U38.20 (~CE), U39.29 (GND)
H2B: U12.4
H4B: U12.5, U35.11 (I10)
MA0: U21.10 (I1d), U31.10 (A0), U32.12 (A0), U39.30 (A0)
MA1: U21.13 (I1c), U31.9 (A1), U32.11 (A1), U39.31 (A1)
MA2: U19.3 (I1a), U31.8 (A2), U32.10 (A2), U39.32 (A2)
MA3: U20.13 (I1c), U31.7 (A3), U32.9 (A3), U39.33 (A3)
MA4: U21.3 (I1a), U31.6 (A4), U32.8 (A4), U39.34 (A4)
MA5: U21.6 (I1b), U31.5 (A5), U32.7 (A5), U39.35 (A5)
MA6: U20.10 (I1d), U31.4 (A6), U32.6 (A6), U39.36 (A6)
MA7: U20.6 (I1b), U31.3 (A7), U32.5 (A7), U39.37 (A7)
MA8: U18.3 (I1a), U31.25 (A8), U32.27 (A8), U39.38 (A8)
MA9: U18.6 (I1b), U31.24 (A9), U32.26 (A9), U36.7 (I7), U39.39 (A9)
MA10: U19.10 (I1d), U31.21 (A10), U32.23 (A10), U36.6 (I6), U39.40 (A10)
MA11: U20.3 (I1a), U31.23 (A11), U32.25 (A11), U36.5 (I5), U39.1 (A11)
MA12: U19.13 (I1c), U31.2 (A12), U32.4 (A12), U36.4 (I4), U39.2 (A12)
MA13: U31.1 (A14), U32.28 (A13), U36.3 (I3), U39.3 (A13)
MA14: U35.2 (I2), U36.2 (I2), U39.4 (A14)
MA15: U35.1 (I1), U36.1 (I1), U39.5 (A15)
MBSWD0: U15.2 (Q0), U31.26 (A13), U35.7 (I7)
MBSWD1: U15.5 (Q1), U35.6 (I6)
MBSWD2: U15.7 (Q2), U35.5 (I5)
MCK6M: R3.2, U14.11 (C), U39.6 (~CLK)
MD0: U15.3 (D0), U28.9 (A7), U31.11 (Q0), U32.13 (D0), U39.14 (D0)
MD1: U15.4 (D1), U28.8 (A6), U31.12 (Q1), U32.14 (D1), U39.15 (D1)
MD2: U15.6 (D2), U28.7 (A5), U31.13 (Q2), U32.15 (D2), U39.12 (D2)
MD3: U15.14 (D5), U28.6 (A4), U31.15 (Q3), U32.17 (D3), U39.8 (D3)
MD4: U15.13 (D4), U28.5 (A3), U31.16 (Q4), U32.18 (D4), U39.7 (D4)
MD5: U15.11 (D3), U28.4 (A2), U31.17 (Q5), U32.19 (D5), U39.9 (D5)
MD6: U28.3 (A1), U31.18 (Q6), U32.20 (D6), U39.10 (D6)
MD7: U28.2 (A0), U31.19 (Q7), U32.21 (D7), U39.13 (D7)
MRA14: U32.29 (A14), U35.14 (IO6)
MRA15: U32.3 (A15), U35.13 (IO7)
MRA16: JP1.1 (A), JP1.2 (C), JP3.1 (A), U32.2 (A16), U35.12 (IO8)
unnamed: JP2.1 (A), JP2.2 (C), U12.2, U15.12 (Q4)
unnamed: R6.2, U26.8 (I8)
unnamed: R7.2, U26.7 (I7)
unnamed: U11.12, U14.3 (C), U17.11 (C)
unnamed: U12.6, U14.12 (D)
unnamed: U13.4 (~S), U13.9 (Q), U26.9 (I9)
unnamed: U13.6 (~Q), U26.11 (I10)
unnamed: U13.5 (Q), U13.12 (D)
unnamed: U14.6 (~Q), U39.16 (~INT)
unnamed: U14.9 (Q), U26.6 (I6)
unnamed: U17.8 (~Q), U34.16 (~INT)
SA0: U21.11 (I0d), U34.30 (A0), U38.10 (A0)
SA1: U21.14 (I0c), U34.31 (A1), U38.9 (A1)
SA2: U19.2 (I0a), U34.32 (A2), U38.8 (A2)
SA3: U20.14 (I0c), U34.33 (A3), U38.7 (A3)
SA4: U21.2 (I0a), U34.34 (A4), U38.6 (A4)
SA5: U21.5 (I0b), U34.35 (A5), U38.5 (A5)
SA6: U20.11 (I0d), U34.36 (A6), U38.4 (A6)
SA7: U20.5 (I0b), U34.37 (A7), U38.3 (A7)
SA8: U18.2 (I0a), U34.38 (A8), U38.25 (A8)
SA9: U18.5 (I0b), U34.39 (A9), U38.24 (A9)
SA10: U19.11 (I0d), U34.40 (A10), U38.21 (A10)
SA11: U20.2 (I0a), U25.5 (I5), U34.1 (A11), U38.23 (A11)
SA12: U19.14 (I0c), U25.4 (I4), U34.2 (A12), U38.2 (A12)
SA13: U25.3 (I3), U34.3 (A13)
SA14: U25.2 (I2), U34.4 (A14)
SA15: U25.1 (I1), U34.5 (A15), U38.1 (A15)
SBANK0: U25.11 (I10), U37.15 (Q5)
SBANK1: U25.9 (I9), U37.12 (Q4)
SCK6M: R4.1, U13.3 (C), U13.11 (C), U34.6 (~CLK)
SD0: U27.9 (A7), U34.14 (D0), U37.14 (D5), U38.11 (D0)
SD1: U27.8 (A6), U34.15 (D1), U37.13 (D4), U38.12 (D1)
SD2: U27.7 (A5), U34.12 (D2), U37.11 (D3), U38.13 (D2)
SD3: U27.6 (A4), U34.8 (D3), U37.6 (D2), U38.15 (D3)
SD4: U27.5 (A3), U34.7 (D4), U37.4 (D1), U38.16 (D4)
SD5: U27.4 (A2), U34.9 (D5), U37.3 (D0), U38.17 (D5)
SD6: U27.3 (A1), U34.10 (D6), U38.18 (D6)
SD7: U27.2 (A0), U34.13 (D7), U38.19 (D7)
SET_LOCK1: U37.10 (Q3)
SET_LOCK2: U37.7 (Q2)
SHA0: U21.9 (Zd), U30.10 (A0)
SHA1: U21.12 (Zc), U30.9 (A1)
SHA2: U19.4 (Za), U30.8 (A2)
SHA3: U20.12 (Zc), U30.7 (A3)
SHA4: U21.4 (Za), U30.6 (A4)
SHA5: U21.7 (Zb), U30.5 (A5)
SHA6: U20.9 (Zd), U30.4 (A6)
SHA7: U20.7 (Zb), U30.3 (A7)
SHA8: U18.4 (Za), U30.25 (A8)
SHA9: U18.7 (Zb), U30.24 (A9)
SHA10: U19.9 (Zd), U30.21 (A10)
SHA11: U20.4 (Za), U30.23 (A11)
SHA12: U19.12 (Zc), U30.2 (A12)
SHD0: U27.11 (B7), U28.11 (B7), U30.19 (D7)
SHD1: U27.12 (B6), U28.12 (B6), U30.18 (D6)
SHD2: U27.13 (B5), U28.13 (B5), U30.17 (D5)
SHD3: U27.14 (B4), U28.14 (B4), U30.16 (D4)
SHD4: U27.15 (B3), U28.15 (B3), U30.15 (D3)
SHD5: U27.16 (B2), U28.16 (B2), U30.13 (D2)
SHD6: U27.17 (B1), U28.17 (B1), U30.12 (D1)
SHD7: U27.18 (B0), U28.18 (B0), U30.11 (D0)
SRA13: U25.18 (IO2), U38.26 (A13)
SRA14: U25.19 (IO1), U38.27 (A14)
VCC: JP2.3 (B), R3.1, R4.2, R6.1, R7.1, R17.1, U13.1 (~R), U13.10 (~S), U13.13 (~R), U14.2 (D), U14.4 (~S), U14.10 (~S), U14.13 (~R), U17.10 (~S), U17.12 (D), U25.20 (VCC), U26.20 (VCC), U30.26 (CS2), U31.28 (VCC), U32.1 (VPP), U32.31 (~PGM), U32.32 (VCC), U34.11 (VCC), U34.25 (~BUSRQ), U35.20 (VCC), U36.20 (VCC), U38.28 (VCC), U39.11 (VCC), U39.17 (~NMI), U39.25 (~BUSRQ)
~BGTRNSP: U36.14 (IO6)
~BNKSW: U15.9 (Cp), U36.15 (IO5)
~MIORQ: U14.1 (~R), U39.20 (~IORQ)
~MMREQ: U35.3 (I3), U36.8 (I8), U39.19 (~MREQ)
~MRAMCS: U31.20 (~CS), U35.16 (IO4)
~MRD: U18.10 (I1d), U28.1 (A->B), U31.22 (~OE), U39.21 (~RD)
~MRFSH: U35.4 (I4), U36.9 (I9), U39.28 (~RFSH)
~MROMCS: JP1.3 (B), JP3.2 (C), JP3.3 (B), U32.24 (~OE), U35.15 (IO5)
~MSHRAMEN: U26.16 (IO4), U28.19 (~CE)
~MSHRAMRQ: U26.1 (I1), U36.18 (IO2)
~MWAIT: U26.14 (IO6), U39.24 (~WAIT)
~MWR: U26.2 (I2), U31.27 (~WE), U36.11 (I10), U39.22 (~WR)
~OBJCODEHI: U35.9 (I9), U36.17 (I03)
~OBJCODELO: U35.8 (I8), U36.16 (IO4)
~OBJORVRAMEN: U26.5 (I5), U36.19 (IO1)
~OBJRAMCS: U35.19 (IO1)
~PALEN: U36.12 (IO8)
~RDINPUTS: U25.16 (IO4)
~SBNKSW: U25.14 (IO6), U37.9 (Cp)
~SHRAMCS: U26.17 (I03), U30.20 (CS1)
~SHRAMRD: U18.9 (Zd), U30.22 (OE)
~SHRAMWR: U26.18 (IO2), U30.27 (R/W)
~SIORQ: U17.13 (~R), U34.20 (~IORQ)
~SMREQ: U25.7 (I7), U34.19 (~MREQ)
~SRD: U18.11 (I0d), U27.1 (A->B), U34.21 (~RD)
~SRFSH: U25.8 (I8), U34.28 (~RFSH)
~SROMCS: U25.12 (IO8), U38.22 (~OE)
~SRST: U12.3, U34.26 (~RESET), U37.1 (~Mr)
~SSHRAMENB: U18.1 (S), U19.1 (S), U20.1 (S), U21.1 (S), U26.19 (IO1)
~SSHRAMEN: U26.15 (IO5), U27.19 (~CE)
~SSHRAMRQ: U25.13 (IO7), U26.3 (I3)
~SWAIT: U26.13 (IO7), U34.24 (~WAIT)
~SWR: U25.6 (I6), U26.4 (I4), U34.22 (~WR)
~VBLK: U11.13
~VRAMWR: U36.13 (IO7)
~WDRES: U12.1, U15.1 (~Mr), U39.26 (~RESET)
~YM2203CS: U13.2 (D), U25.15 (IO5)
~YMIRQ: R17.2, U34.17 (~NMI)

Notes on the sheet:
Not mounted
B06-13
Shared RAM
RAM
B06-12
U26-B06-12 ~{SWAIT} = i9 & ~i11 & (~~{SSHRAMEN} + ~{SSHRAMRQ}) ~{MWAIT} = ~{OBJORVRAMEN} & ~{SSHRAMEN} + i6 & ~{SSHRAMEN} ~{SSHRAMEN} = ~{SSHRAMRQ} + ~~{MSHRAMRQ} & ~{SSHRAMEN} ~{MSHRAMEN} = ~{MSHRAMRQ} + ~~{SSHRAMRQ} & ~{MSHRAMEN} ~{SHRAMCS} = ~{MSHRAMRQ} & ~{SSHRAMRQ} ~{SHRAMWR} = ~{MWR} & ~{SSHR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
B53-12
B06-101
