skutis/jtbubl/cores/kiwi/sch/insectx/graphics.kicad_sch

## KiCad design cores/kiwi/sch/insectx/graphics.kicad_sch (2022-12-07)

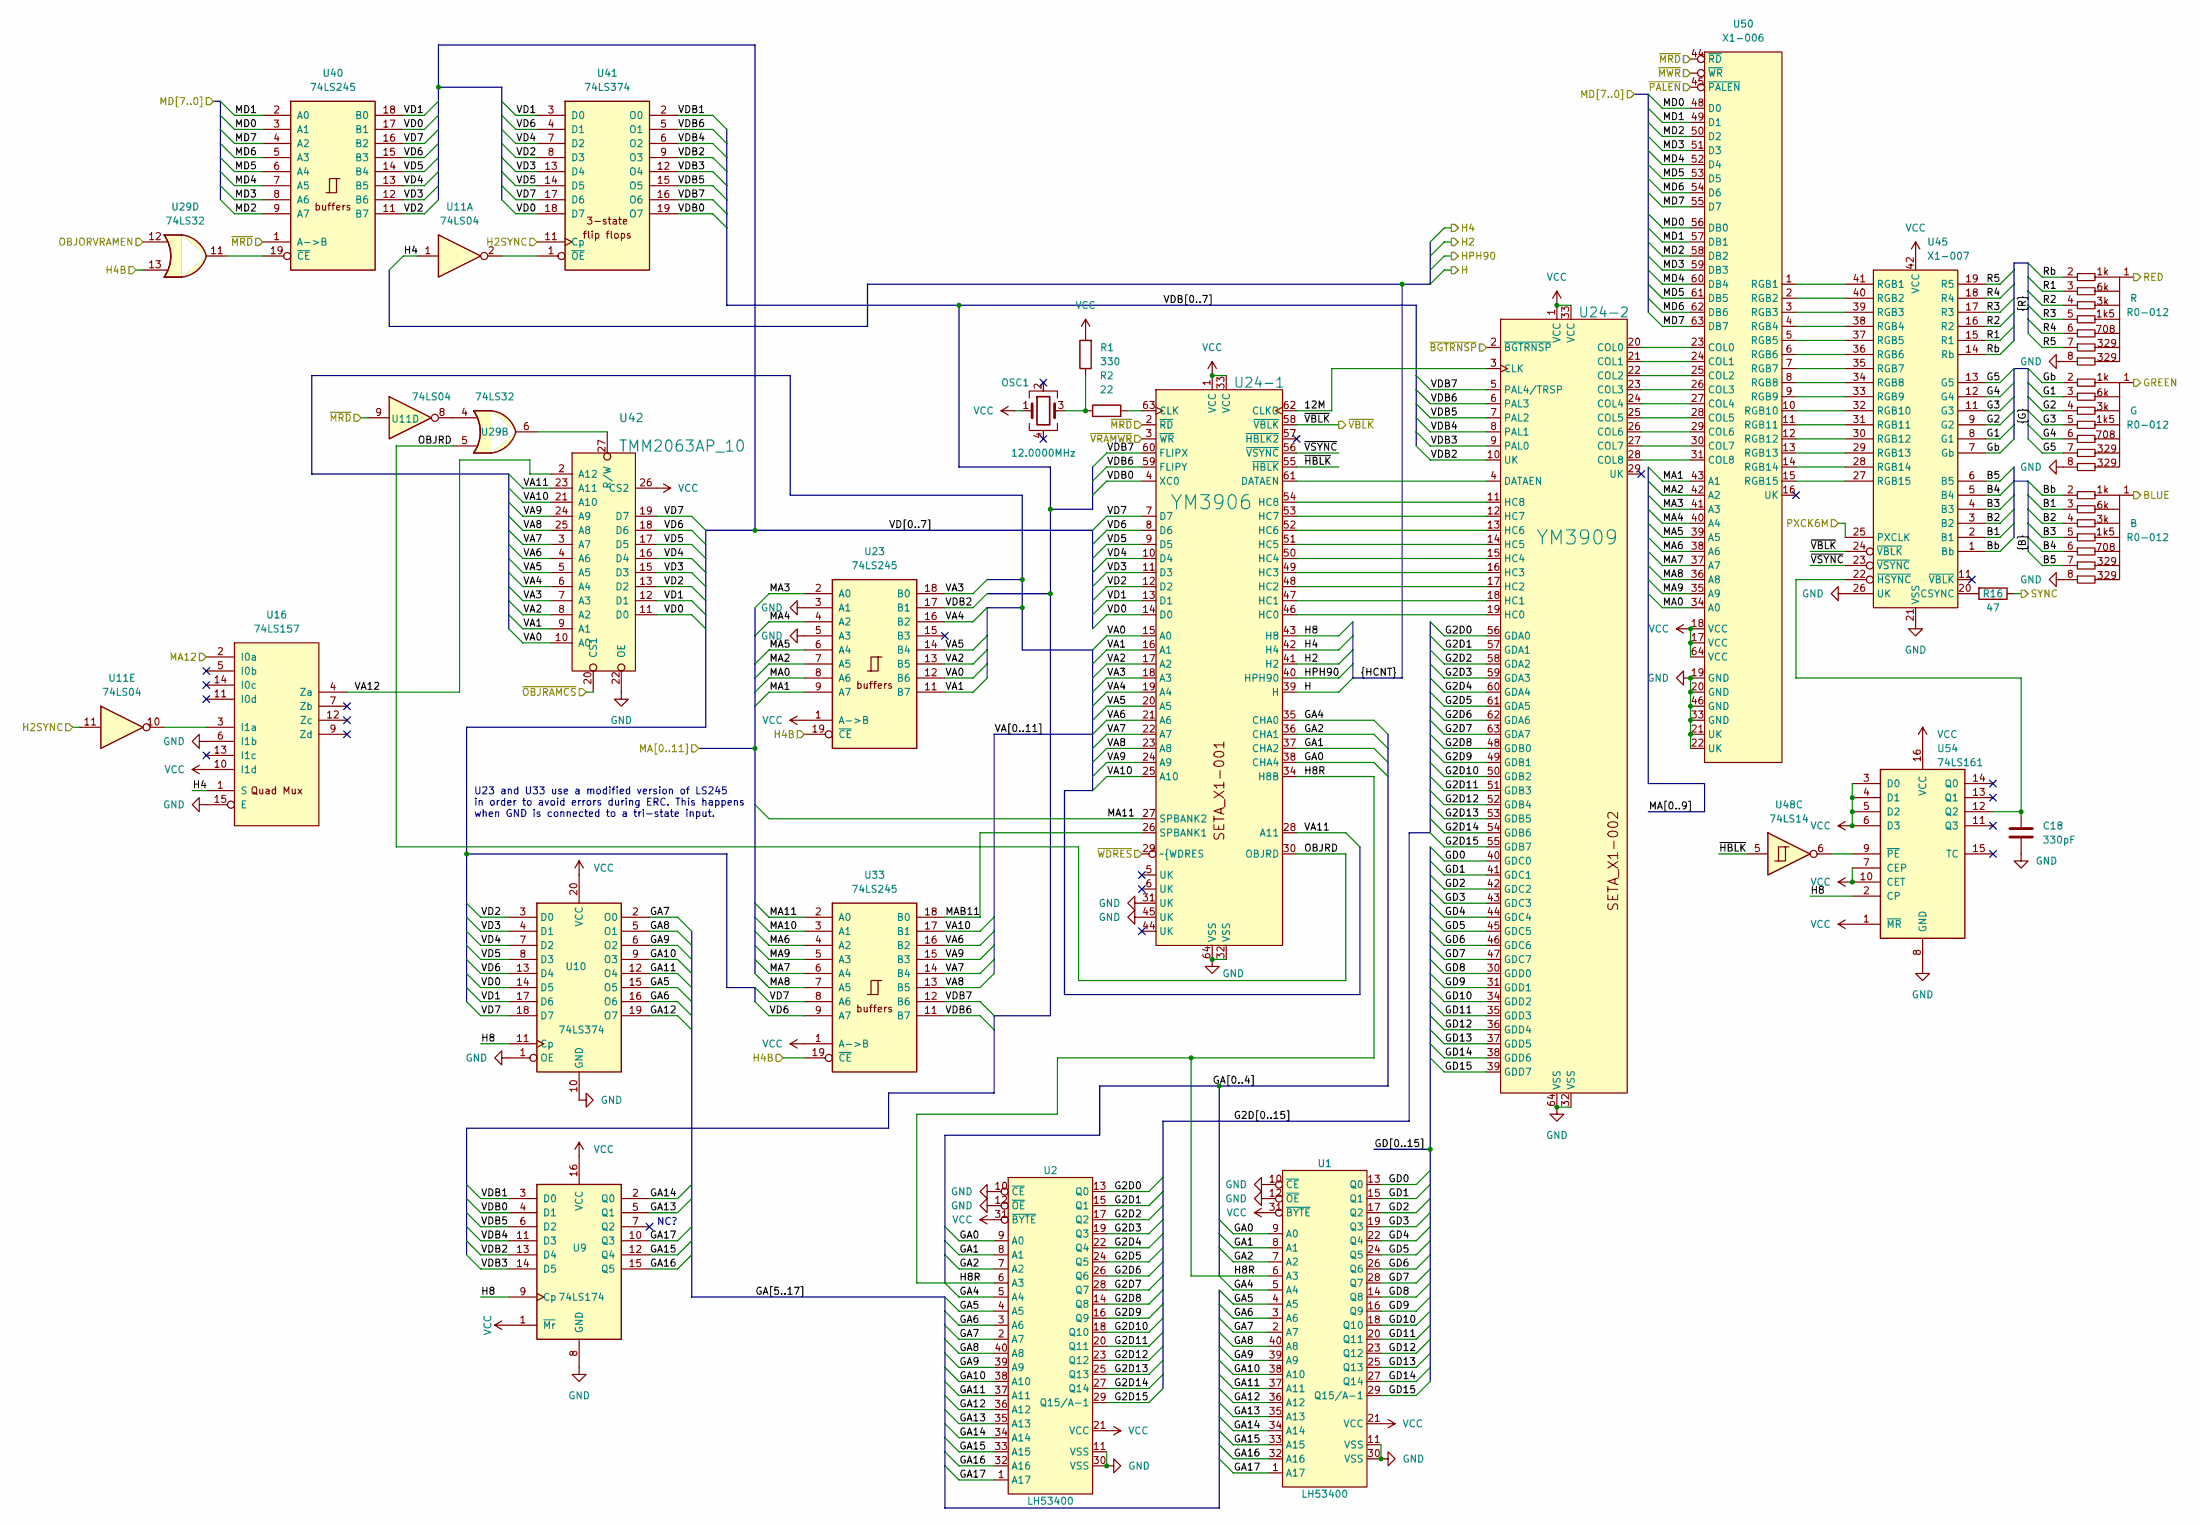
[picture p23: schematic graphics.kicad_sch]

Parts:
B1: R0-012
C18: 330pF
G1: R0-012
OSC1: 12.0000MHz
R1: 330
R2: 22
R16: 47
R999: R0-012
U1, U2: LH53400
U9: 74LS174
U10, U41: 74LS374
U11: 74LS04
U16: 74LS157
U23, U33, U40: 74LS245
U24-1: YM3906
U24-2: YM3909
U29: 74LS32
U42: TMM2063AP_10
U45: X1-007
U48: 74LS14
U50: X1-006
U54: 74LS161

Connections:
12M: U24-1.62 (CLKO), U24-2.3 (CLK)
B1: B1.3, U45.2 (B1)
B2: B1.4, U45.3 (B2)
B3: B1.5, U45.4 (B3)
B4: B1.6, U45.5 (B4)
B5: B1.7, U45.6 (B5)
BLUE: B1.1
Bb: B1.2, U45.1 (Bb)
G1: G1.3, U45.8 (G1)
G2: G1.4, U45.9 (G2)
G2D0: U2.13 (Q0), U24-2.56 (GDA0)
G2D1: U2.15 (Q1), U24-2.57 (GDA1)
G2D2: U2.17 (Q2), U24-2.58 (GDA2)
G2D3: U2.19 (Q3), U24-2.59 (GDA3)
G2D4: U2.22 (Q4), U24-2.60 (GDA4)
G2D5: U2.24 (Q5), U24-2.61 (GDA5)
G2D6: U2.26 (Q6), U24-2.62 (GDA6)
G2D7: U2.28 (Q7), U24-2.63 (GDA7)
G2D8: U2.14 (Q8), U24-2.48 (GDB0)
G2D9: U2.16 (Q9), U24-2.49 (GDB1)
G2D10: U2.18 (Q10), U24-2.50 (GDB2)
G2D11: U2.20 (Q11), U24-2.51 (GDB3)
G2D12: U2.23 (Q12), U24-2.52 (GDB4)
G2D13: U2.25 (Q13), U24-2.53 (GDB5)
G2D14: U2.27 (Q14), U24-2.54 (GDB6)
G2D15: U2.29 (Q15/A-1), U24-2.55 (GDB7)
G3: G1.5, U45.11 (G3)
G4: G1.6, U45.12 (G4)
G5: G1.7, U45.13 (G5)
GA0: U1.9 (A0), U2.9 (A0), U24-1.38 (CHA4)
GA1: U1.8 (A1), U2.8 (A1), U24-1.37 (CHA2)
GA2: U1.7 (A2), U2.7 (A2), U24-1.36 (CHA1)
GA4: U1.5 (A4), U2.5 (A4), U24-1.35 (CHA0)
GA5: U1.4 (A5), U2.4 (A5), U10.15 (O5)
GA6: U1.3 (A6), U2.3 (A6), U10.16 (O6)
GA7: U1.2 (A7), U2.2 (A7), U10.2 (O0)
GA8: U1.40 (A8), U2.40 (A8), U10.5 (O1)
GA9: U1.39 (A9), U2.39 (A9), U10.6 (O2)
GA10: U1.38 (A10), U2.38 (A10), U10.9 (O3)
GA11: U1.37 (A11), U2.37 (A11), U10.12 (O4)
GA12: U1.36 (A12), U2.36 (A12), U10.19 (O7)
GA13: U1.35 (A13), U2.35 (A13), U9.5 (Q1)
GA14: U1.34 (A14), U2.34 (A14), U9.2 (Q0)
GA15: U1.33 (A15), U2.33 (A15), U9.12 (Q4)
GA16: U1.32 (A16), U2.32 (A16), U9.15 (Q5)
GA17: U1.1 (A17), U2.1 (A17), U9.10 (Q3)
GD0: U1.13 (Q0), U24-2.40 (GDC0)
GD1: U1.15 (Q1), U24-2.41 (GDC1)
GD2: U1.17 (Q2), U24-2.42 (GDC2)
GD3: U1.19 (Q3), U24-2.43 (GDC3)
GD4: U1.22 (Q4), U24-2.44 (GDC4)
GD5: U1.24 (Q5), U24-2.45 (GDC5)
GD6: U1.26 (Q6), U24-2.46 (GDC6)
GD7: U1.28 (Q7), U24-2.47 (GDC7)
GD8: U1.14 (Q8), U24-2.30 (GDD0)
GD9: U1.16 (Q9), U24-2.31 (GDD1)
GD10: U1.18 (Q10), U24-2.34 (GDD2)
GD11: U1.20 (Q11), U24-2.35 (GDD3)
GD12: U1.23 (Q12), U24-2.36 (GDD4)
GD13: U1.25 (Q13), U24-2.37 (GDD5)
GD14: U1.27 (Q14), U24-2.38 (GDD6)
GD15: U1.29 (Q15/A-1), U24-2.39 (GDD7)
GND: B1.8, C18.2, G1.8, R999.8, U1.10 (~CE), U1.11 (VSS), U1.12 (~OE), U1.30 (VSS), U2.10 (~CE), U2.11 (VSS), U2.12 (~OE), U2.30 (VSS), U9.8 (GND), U10.1 (OE), U10.10 (GND), U16.6 (I1b), U16.15 (E), U23.3 (A1), U23.5 (A3), U24-1.31 (UK), U24-1.32 (VSS), U24-1.45 (UK), U24-1.64 (VSS), U24-2.32 (VSS), U24-2.64 (VSS), U42.22 (OE), U45.21 (VSS), U45.26 (UK), U50.19 (GND), U50.20 (GND), U50.21 (UK), U50.22 (UK), U50.33 (GND), U50.46 (GND), U54.8 (GND)
GREEN: G1.1
Gb: G1.2, U45.7 (Gb)
H: U24-1.39 (H)
H2: U24-1.41 (H2)
H2SYNC: U11.11, U41.11 (Cp)
H4: U11.1, U16.1 (S), U24-1.42 (H4)
H4B: U23.19 (~CE), U29.13, U33.19 (~CE)
H8: U9.9 (Cp), U10.11 (Cp), U24-1.43 (H8), U54.2 (CP)
H8R: U1.6 (A3), U2.6 (A3), U24-1.34 (H8B)
HPH90: U24-1.40 (HPH90)
MA0: U23.8 (A6), U50.34 (A0)
MA1: U23.9 (A7), U50.43 (A1)
MA2: U23.7 (A5), U50.42 (A2)
MA3: U23.2 (A0), U50.41 (A3)
MA4: U23.4 (A2), U50.40 (A4)
MA5: U23.6 (A4), U50.39 (A5)
MA6: U33.4 (A2), U50.38 (A6)
MA7: U33.6 (A4), U50.37 (A7)
MA8: U33.7 (A5), U50.36 (A8)
MA9: U33.5 (A3), U50.35 (A9)
MA10: U33.3 (A1)
MA11: U24-1.27 (SPBANK2), U33.2 (A0)
MA12: U16.2 (I0a)
MAB11: U24-1.26 (SPBANK1), U33.18 (B0)
MD0: U40.3 (A1), U50.48 (D0), U50.56 (DB0)
MD1: U40.2 (A0), U50.49 (D1), U50.57 (DB1)
MD2: U40.9 (A7), U50.50 (D2), U50.58 (DB2)
MD3: U40.8 (A6), U50.51 (D3), U50.59 (DB3)
MD4: U40.7 (A5), U50.52 (D4), U50.60 (DB4)
MD5: U40.6 (A4), U50.53 (D5), U50.61 (DB5)
MD6: U40.5 (A3), U50.54 (D6), U50.62 (DB6)
MD7: U40.4 (A2), U50.55 (D7), U50.63 (DB7)
unnamed: C18.1, U45.22 (~HSYNC), U54.12 (Q2)
unnamed: OSC1.3, R1.1, R2.1
unnamed: R2.2, U24-1.63 (CLK)
unnamed: R16.2, U45.20 (CSYNC)
unnamed: U11.2, U41.1 (~OE)
unnamed: U11.8, U29.4
unnamed: U11.10, U16.3 (I1a)
unnamed: U24-1.46 (HC0), U24-2.19 (HC0)
unnamed: U24-1.47 (HC1), U24-2.18 (HC1)
unnamed: U24-1.48 (HC2), U24-2.17 (HC2)
unnamed: U24-1.49 (HC3), U24-2.16 (HC3)
unnamed: U24-1.50 (HC4), U24-2.15 (HC4)
unnamed: U24-1.51 (HC5), U24-2.14 (HC5)
unnamed: U24-1.52 (HC6), U24-2.13 (HC6)
unnamed: U24-1.53 (HC7), U24-2.12 (HC7)
unnamed: U24-1.54 (HC8), U24-2.11 (HC8)
unnamed: U24-1.61 (DATAEN), U24-2.4 (DATAEN)
unnamed: U24-2.20 (COL0), U50.23 (COL0)
unnamed: U24-2.21 (COL1), U50.24 (COL1)
unnamed: U24-2.22 (COL2), U50.25 (COL2)
unnamed: U24-2.23 (COL3), U50.26 (COL3)
unnamed: U24-2.24 (COL4), U50.27 (COL4)
unnamed: U24-2.25 (COL5), U50.28 (COL5)
unnamed: U24-2.26 (COL6), U50.29 (COL6)
unnamed: U24-2.27 (COL7), U50.30 (COL7)
unnamed: U24-2.28 (COL8), U50.31 (COL8)
unnamed: U29.6, U42.27 (R/W)
unnamed: U29.11, U40.19 (~CE)
unnamed: U45.27 (RGB15), U50.15 (RGB15)
unnamed: U45.28 (RGB14), U50.14 (RGB14)
unnamed: U45.29 (RGB13), U50.13 (RGB13)
unnamed: U45.30 (RGB12), U50.12 (RGB12)
unnamed: U45.31 (RGB11), U50.11 (RGB11)
unnamed: U45.32 (RGB10), U50.10 (RGB10)
unnamed: U45.33 (RGB9), U50.9 (RGB9)
unnamed: U45.34 (RGB8), U50.8 (RGB8)
unnamed: U45.35 (RGB7), U50.7 (RGB7)
unnamed: U45.36 (RGB6), U50.6 (RGB6)
unnamed: U45.37 (RGB5), U50.5 (RGB5)
unnamed: U45.38 (RGB4), U50.4 (RGB4)
unnamed: U45.39 (RGB3), U50.3 (RGB3)
unnamed: U45.40 (RGB2), U50.2 (RGB2)
unnamed: U45.41 (RGB1), U50.1 (RGB1)
unnamed: U48.6, U54.9 (~PE)
OBJORVRAMEN: U29.12
OBJRD: U24-1.30 (OBJRD), U29.5
PXCK6M: U45.25 (PXCLK)
R1: R999.3, U45.15 (R1)
R2: R999.4, U45.16 (R2)
R3: R999.5, U45.17 (R3)
R4: R999.6, U45.18 (R4)
R5: R999.7, U45.19 (R5)
RED: R999.1
Rb: R999.2, U45.14 (Rb)
SYNC: R16.1
VA0: U23.12 (B6), U24-1.15 (A0), U42.10 (A0)
VA1: U23.11 (B7), U24-1.16 (A1), U42.9 (A1)
VA2: U23.13 (B5), U24-1.17 (A2), U42.8 (A2)
VA3: U23.18 (B0), U24-1.18 (A3), U42.7 (A3)
VA4: U23.16 (B2), U24-1.19 (A4), U42.6 (A4)
VA5: U23.14 (B4), U24-1.20 (A5), U42.5 (A5)
VA6: U24-1.21 (A6), U33.16 (B2), U42.4 (A6)
VA7: U24-1.22 (A7), U33.14 (B4), U42.3 (A7)
VA8: U24-1.23 (A8), U33.13 (B5), U42.25 (A8)
VA9: U24-1.24 (A9), U33.15 (B3), U42.24 (A9)
VA10: U24-1.25 (A10), U33.17 (B1), U42.21 (A10)
VA11: U24-1.28 (A11), U42.23 (A11)
VA12: U16.4 (Za), U42.2 (A12)
VCC: OSC1.1, R1.2, U1.21 (VCC), U1.31 (~BYTE), U2.21 (VCC), U2.31 (~BYTE), U9.1 (~Mr), U9.16 (VCC), U10.20 (VCC), U16.10 (I1d), U23.1 (A->B), U24-1.1 (VCC), U24-1.33 (VCC), U24-2.1 (VCC), U24-2.33 (VCC), U33.1 (A->B), U42.26 (CS2), U45.42 (VCC), U50.17 (VCC), U50.18 (VCC), U50.64 (VCC), U54.1 (~MR), U54.3 (D0), U54.4 (D1), U54.5 (D2), U54.6 (D3), U54.7 (CEP), U54.10 (CET), U54.16 (VCC)
VD0: U10.14 (D5), U24-1.14 (D0), U40.17 (B1), U41.18 (D7), U42.11 (D0)
VD1: U10.17 (D6), U24-1.13 (D1), U40.18 (B0), U41.3 (D0), U42.12 (D1)
VD2: U10.3 (D0), U24-1.12 (D2), U40.11 (B7), U41.8 (D3), U42.13 (D2)
VD3: U10.4 (D1), U24-1.11 (D3), U40.12 (B6), U41.13 (D4), U42.15 (D3)
VD4: U10.7 (D2), U24-1.10 (D4), U40.13 (B5), U41.7 (D2), U42.16 (D4)
VD5: U10.8 (D3), U24-1.9 (D5), U40.14 (B4), U41.14 (D5), U42.17 (D5)
VD6: U10.13 (D4), U24-1.8 (D6), U33.9 (A7), U40.15 (B3), U41.4 (D1), U42.18 (D6)
VD7: U10.18 (D7), U24-1.7 (D7), U33.8 (A6), U40.16 (B2), U41.17 (D6), U42.19 (D7)
VDB0: U9.4 (D1), U24-1.4 (XC0), U41.19 (O7)
VDB1: U9.3 (D0), U41.2 (O0)
VDB2: U9.13 (D4), U23.17 (B1), U24-2.10 (UK), U41.9 (O3)
VDB3: U9.14 (D5), U24-2.9 (PAL0), U41.12 (O4)
VDB4: U9.11 (D3), U24-2.8 (PAL1), U41.6 (O2)
VDB5: U9.6 (D2), U24-2.7 (PAL2), U41.15 (O5)
VDB6: U24-1.59 (FLIPY), U24-2.6 (PAL3), U33.11 (B7), U41.5 (O1)
VDB7: U24-1.60 (FLIPX), U24-2.5 (PAL4/TRSP), U33.12 (B6), U41.16 (O6)
~BGTRNSP: U24-2.2 (~BGTRNSP)
~HBLK: U24-1.55 (~HBLK), U48.5
~MRD: U11.9, U24-1.2 (~RD), U40.1 (A->B), U50.44 (~RD)
~MWR: U50. (~WR)
~OBJRAMCS: U42.20 (CS1)
~PALEN: U50.45 (~PALEN)
~VBLK: U24-1.58 (~VBLK), U45.24 (~VBLK)
~VRAMWR: U24-1.3 (~WR)
~VSYNC: U24-1.56 (~VSYNC), U45.23 (~VSYNC)
~WDRES: U24-1.29 (~{WDRES)

Notes on the sheet:
NC?
U23 and U33 use a modified version of LS245 in order to avoid errors during ERC. This happens when GND is connected to a tri-state input.
