skutis/jtbubl/cores/kiwi/sch/insectx/io.kicad_sch

## KiCad design cores/kiwi/sch/insectx/io.kicad_sch (2022-12-07)

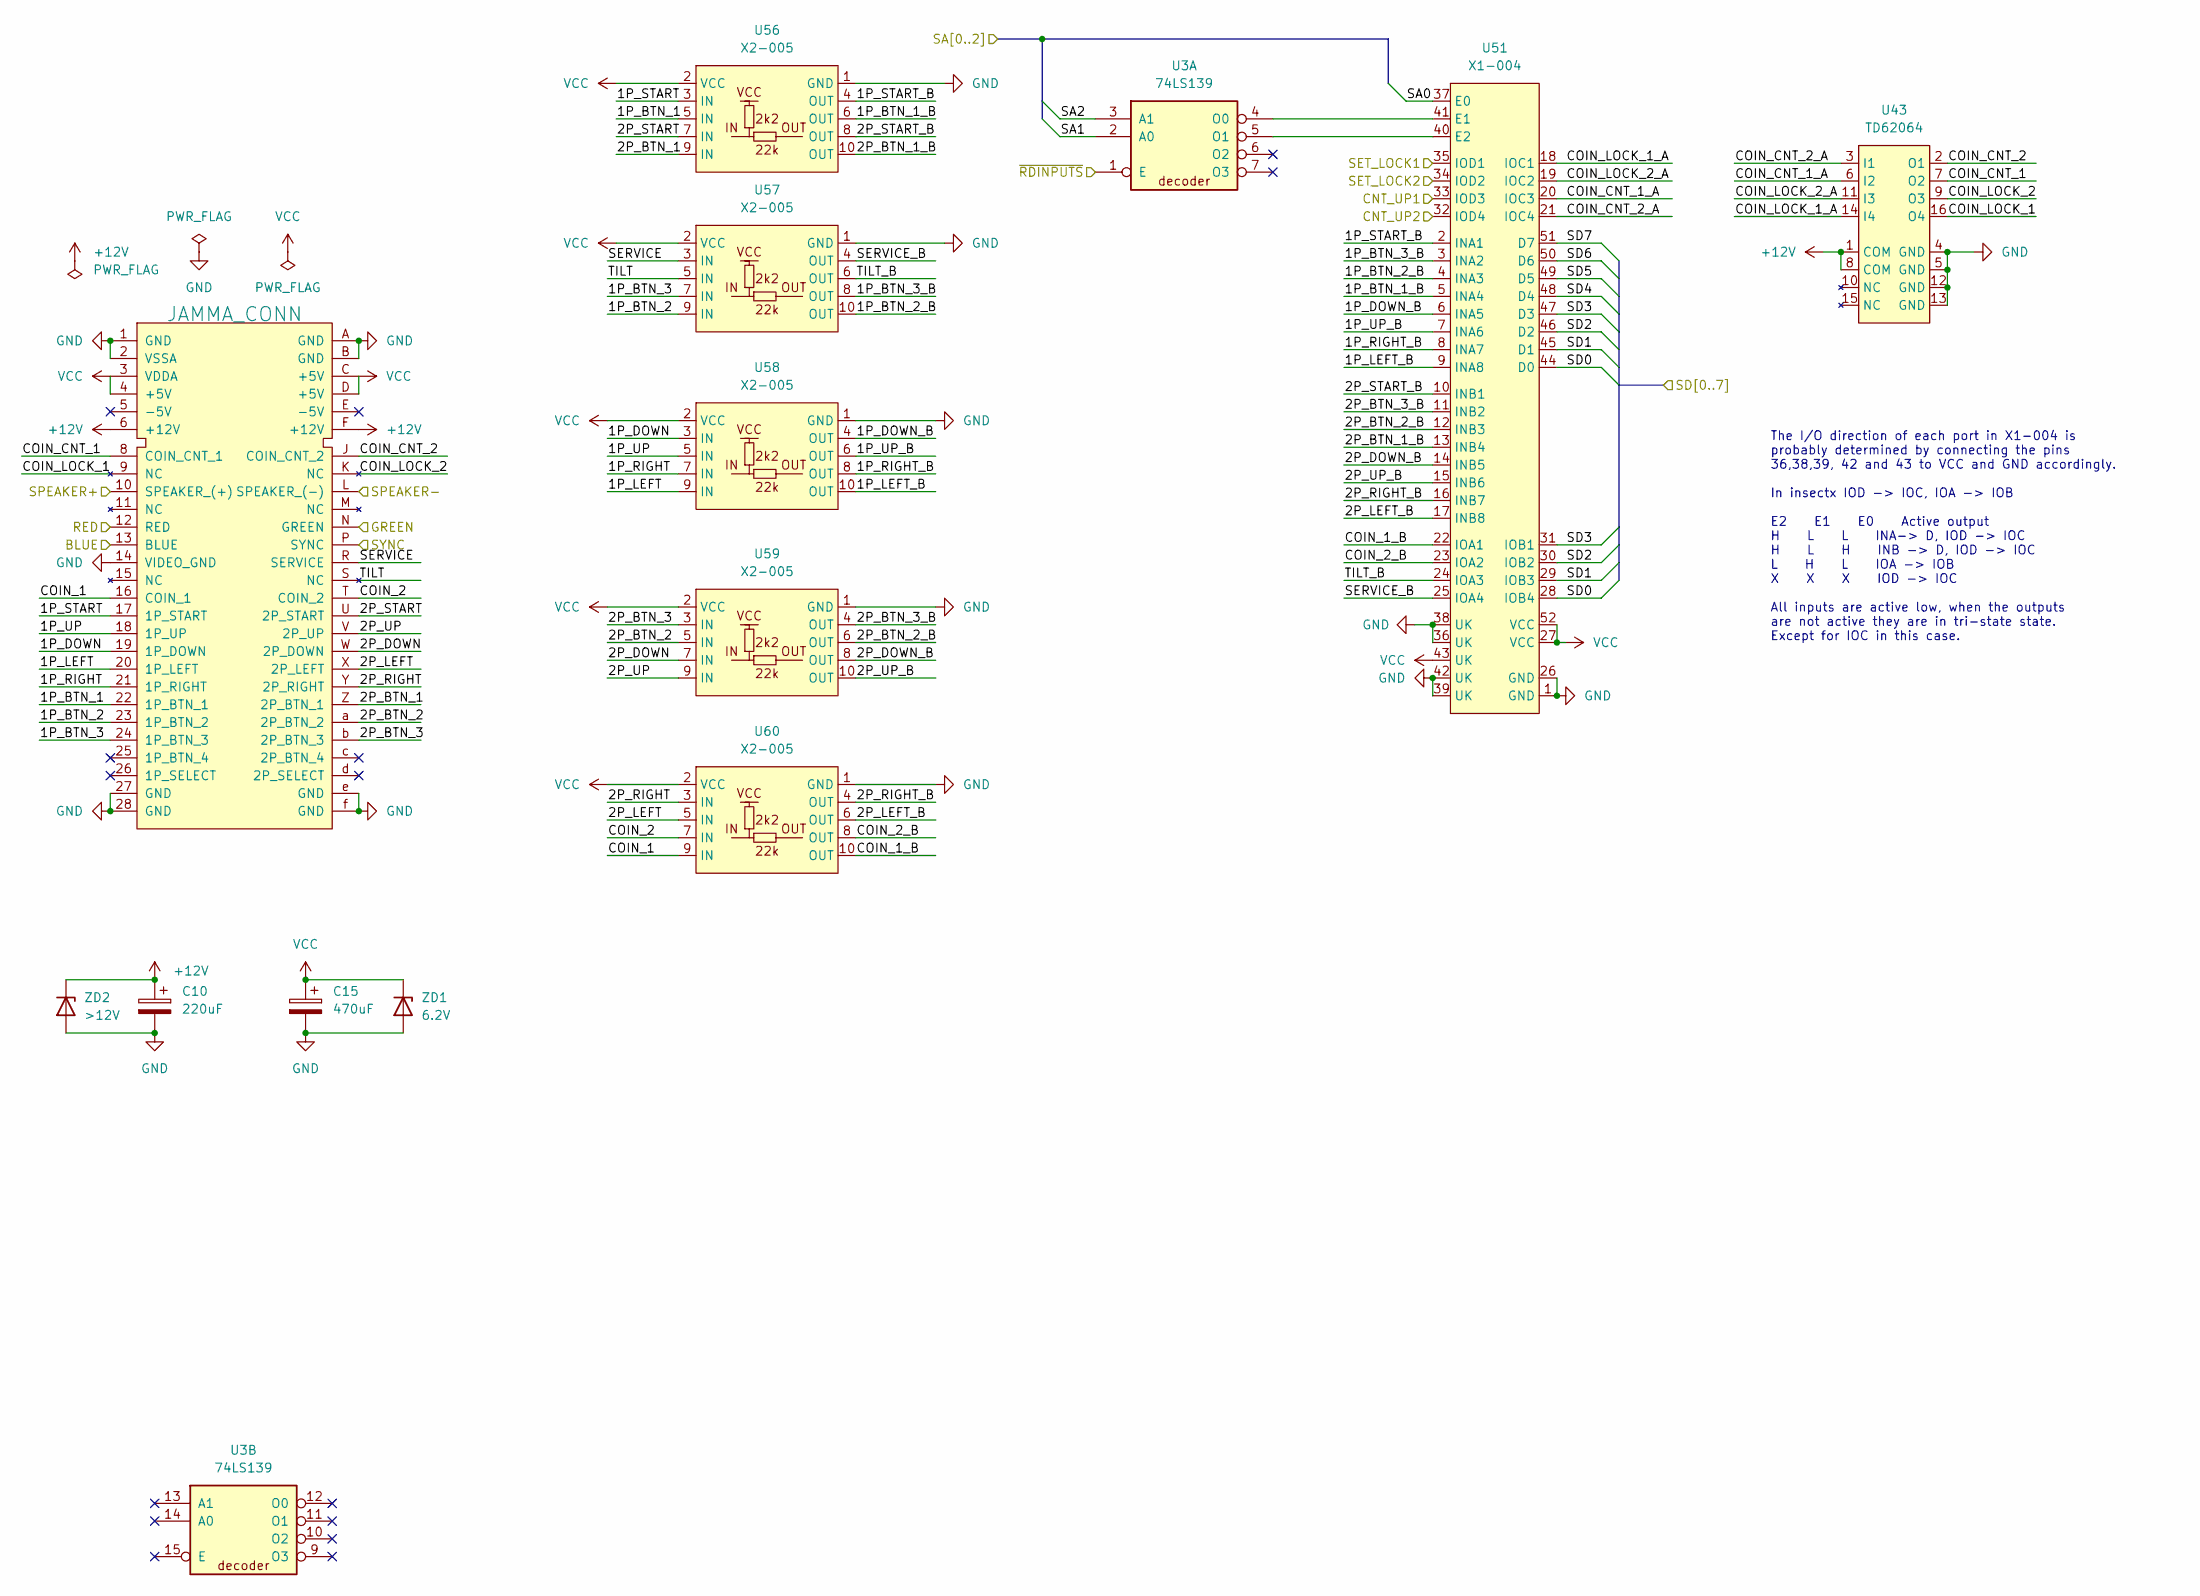
[picture p24: schematic io.kicad_sch]

Parts:
C10: 220uF
C15: 470uF
JAMMA1: JAMMA_CONN
U3: 74LS139
U43: TD62064
U51: X1-004
U56, U57, U58, U59, U60: X2-005
ZD1: 6.2V
ZD2: >12V

Connections:
1P_BTN_1: JAMMA1.22 (1P_BTN_1), U56.5 (IN)
1P_BTN_1_B: U51.5 (INA4), U56.6 (OUT)
1P_BTN_2: JAMMA1.23 (1P_BTN_2), U57.9 (IN)
1P_BTN_2_B: U51.4 (INA3), U57.10 (OUT)
1P_BTN_3: JAMMA1.24 (1P_BTN_3), U57.7 (IN)
1P_BTN_3_B: U51.3 (INA2), U57.8 (OUT)
1P_DOWN: JAMMA1.19 (1P_DOWN), U58.3 (IN)
1P_DOWN_B: U51.6 (INA5), U58.4 (OUT)
1P_LEFT: JAMMA1.20 (1P_LEFT), U58.9 (IN)
1P_LEFT_B: U51.9 (INA8), U58.10 (OUT)
1P_RIGHT: JAMMA1.21 (1P_RIGHT), U58.7 (IN)
1P_RIGHT_B: U51.8 (INA7), U58.8 (OUT)
1P_START: JAMMA1.17 (1P_START), U56.3 (IN)
1P_START_B: U51.2 (INA1), U56.4 (OUT)
1P_UP: JAMMA1.18 (1P_UP), U58.5 (IN)
1P_UP_B: U51.7 (INA6), U58.6 (OUT)
2P_BTN_1: JAMMA1.Z (2P_BTN_1), U56.9 (IN)
2P_BTN_1_B: U51.13 (INB4), U56.10 (OUT)
2P_BTN_2: JAMMA1.a (2P_BTN_2), U59.5 (IN)
2P_BTN_2_B: U51.12 (INB3), U59.6 (OUT)
2P_BTN_3: JAMMA1.b (2P_BTN_3), U59.3 (IN)
2P_BTN_3_B: U51.11 (INB2), U59.4 (OUT)
2P_DOWN: JAMMA1.W (2P_DOWN), U59.7 (IN)
2P_DOWN_B: U51.14 (INB5), U59.8 (OUT)
2P_LEFT: JAMMA1.X (2P_LEFT), U60.5 (IN)
2P_LEFT_B: U51.17 (INB8), U60.6 (OUT)
2P_RIGHT: JAMMA1.Y (2P_RIGHT), U60.3 (IN)
2P_RIGHT_B: U51.16 (INB7), U60.4 (OUT)
2P_START: JAMMA1.U (2P_START), U56.7 (IN)
2P_START_B: U51.10 (INB1), U56.8 (OUT)
2P_UP: JAMMA1.V (2P_UP), U59.9 (IN)
2P_UP_B: U51.15 (INB6), U59.10 (OUT)
+12V: C10.1, JAMMA1.6 (+12V), JAMMA1.F (+12V), U43.1 (COM), U43.8 (COM), ZD2.1 (K)
BLUE: JAMMA1.13 (BLUE)
CNT_UP1: U51.33 (IOD3)
CNT_UP2: U51.32 (IOD4)
COIN_1: JAMMA1.16 (COIN_1), U60.9 (IN)
COIN_1_B: U51.22 (IOA1), U60.10 (OUT)
COIN_2: JAMMA1.T (COIN_2), U60.7 (IN)
COIN_2_B: U51.23 (IOA2), U60.8 (OUT)
COIN_CNT_1: JAMMA1.8 (COIN_CNT_1), U43.7 (O2)
COIN_CNT_1_A: U43.6 (I2), U51.20 (IOC3)
COIN_CNT_2: JAMMA1.J (COIN_CNT_2), U43.2 (O1)
COIN_CNT_2_A: U43.3 (I1), U51.21 (IOC4)
COIN_LOCK_1: JAMMA1.9 (NC), U43.16 (O4)
COIN_LOCK_1_A: U43.14 (I4), U51.18 (IOC1)
COIN_LOCK_2: JAMMA1.K (NC), U43.9 (O3)
COIN_LOCK_2_A: U43.11 (I3), U51.19 (IOC2)
GND: C10.2, C15.2, JAMMA1.1 (GND), JAMMA1.2 (VSSA), JAMMA1.14 (VIDEO_GND), JAMMA1.27 (GND), JAMMA1.28 (GND), JAMMA1.A (GND), JAMMA1.B (GND), JAMMA1.e (GND), JAMMA1.f (GND), U43.4 (GND), U43.5 (GND), U43.12 (GND), U43.13 (GND), U51.1 (GND), U51.26 (GND), U51.36 (UK), U51.38 (UK), U51.39 (UK), U51.42 (UK), U56.1 (GND), U57.1 (GND), U58.1 (GND), U59.1 (GND), U60.1 (GND), ZD1.2 (A), ZD2.2 (A)
GREEN: JAMMA1.N (GREEN)
unnamed: U3.4 (O0), U51.41 (E1)
unnamed: U3.5 (O1), U51.40 (E2)
RED: JAMMA1.12 (RED)
SA0: U51.37 (E0)
SA1: U3.2 (A0)
SA2: U3.3 (A1)
SD0: U51.28 (IOB4), U51.44 (D0)
SD1: U51.29 (IOB3), U51.45 (D1)
SD2: U51.30 (IOB2), U51.46 (D2)
SD3: U51.31 (IOB1), U51.47 (D3)
SD4: U51.48 (D4)
SD5: U51.49 (D5)
SD6: U51.50 (D6)
SD7: U51.51 (D7)
SERVICE: JAMMA1.R (SERVICE), U57.3 (IN)
SERVICE_B: U51.25 (IOA4), U57.4 (OUT)
SET_LOCK1: U51.35 (IOD1)
SET_LOCK2: U51.34 (IOD2)
SPEAKER+: JAMMA1.10 (SPEAKER_(+))
SPEAKER-: JAMMA1.L (SPEAKER_(-))
SYNC: JAMMA1.P (SYNC)
TILT: JAMMA1.S (NC), U57.5 (IN)
TILT_B: U51.24 (IOA3), U57.6 (OUT)
VCC: C15.1, JAMMA1.3 (VDDA), JAMMA1.4 (+5V), JAMMA1.C (+5V), JAMMA1.D (+5V), U51.27 (VCC), U51.43 (UK), U51.52 (VCC), U56.2 (VCC), U57.2 (VCC), U58.2 (VCC), U59.2 (VCC), U60.2 (VCC), ZD1.1 (K)
~RDINPUTS: U3.1 (E)

Notes on the sheet:
The I/O direction of each port in X1-004 is probably determined by connecting the pins 36,38,39, 42 and 43 to VCC and GND accordingly. In insectx IOD -> IOC, IOA -> IOB E2 E1 E0 Active output H L L INA-> D, IOD -> IOC H L H INB -> D, IOD -> IOC L H L IOA -> IOB X X X IOD -> IOC All inputs are activ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
