skutis/jtbubl/cores/kiwi/sch/insectx/mcu.kicad_sch

## KiCad design cores/kiwi/sch/insectx/mcu.kicad_sch (2022-11-14)

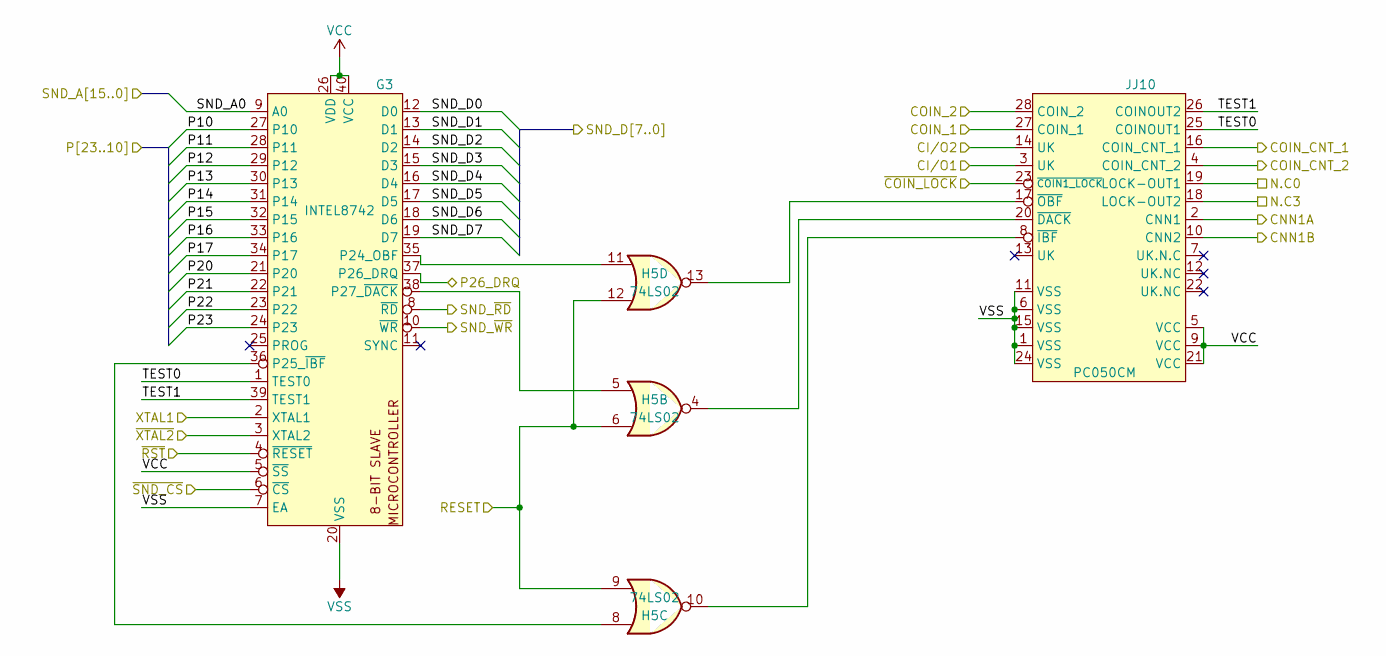
[picture p25: schematic mcu.kicad_sch]

Parts:
G3: INTEL8742
H5: 74LS02
JJ10: PC050CM

Connections:
CI/O1: JJ10.3 (UK)
CI/O2: JJ10.14 (UK)
CNN1A: JJ10.2 (CNN1)
CNN1B: JJ10.10 (CNN2)
COIN_1: JJ10.27 (COIN_1)
COIN_2: JJ10.28 (COIN_2)
COIN_CNT_1: JJ10.16 (COIN_CNT_1)
COIN_CNT_2: JJ10.4 (COIN_CNT_2)
N.C0: JJ10.19 (LOCK-OUT1)
N.C3: JJ10.18 (LOCK-OUT2)
unnamed: G3.35 (P24_OBF), H5.11
unnamed: G3.36 (P25_~IBF), H5.8
unnamed: G3.38 (P27_~DACK), H5.5
unnamed: H5.4, JJ10.20 (~DACK)
unnamed: H5.10, JJ10.8 (~IBF)
unnamed: H5.13, JJ10.17 (~OBF)
P10: G3.27 (P10)
P11: G3.28 (P11)
P12: G3.29 (P12)
P13: G3.30 (P13)
P14: G3.31 (P14)
P15: G3.32 (P15)
P16: G3.33 (P16)
P17: G3.34 (P17)
P20: G3.21 (P20)
P21: G3.22 (P21)
P22: G3.23 (P22)
P23: G3.24 (P23)
P26_DRQ: G3.37 (P26_DRQ)
RESET: H5.6, H5.9, H5.12
SND_A0: G3.9 (A0)
SND_D0: G3.12 (D0)
SND_D1: G3.13 (D1)
SND_D2: G3.14 (D2)
SND_D3: G3.15 (D3)
SND_D4: G3.16 (D4)
SND_D5: G3.17 (D5)
SND_D6: G3.18 (D6)
SND_D7: G3.19 (D7)
SND_~RD: G3.8 (~RD)
SND_~WR: G3.10 (~WR)
TEST0: G3.1 (TEST0), JJ10.25 (COINOUT1)
TEST1: G3.39 (TEST1), JJ10.26 (COINOUT2)
VCC: G3.5 (~SS), G3.26 (VDD), G3.40 (VCC), JJ10.5 (VCC), JJ10.9 (VCC), JJ10.21 (VCC)
VSS: G3.7 (EA), G3.20 (VSS), JJ10.1 (VSS), JJ10.6 (VSS), JJ10.11 (VSS), JJ10.15 (VSS), JJ10.24 (VSS)
XTAL1: G3.2 (XTAL1)
~COIN_LOCK: JJ10.23 (~COIN1_LOCK)
~RST: G3.4 (~RESET)
~SND_CS: G3.6 (~CS)
~XTAL2: G3.3 (XTAL2)
