skutis/jtbubl/cores/kiwi/sch/insectx/misc.kicad_sch

## KiCad design cores/kiwi/sch/insectx/misc.kicad_sch (2022-12-07)

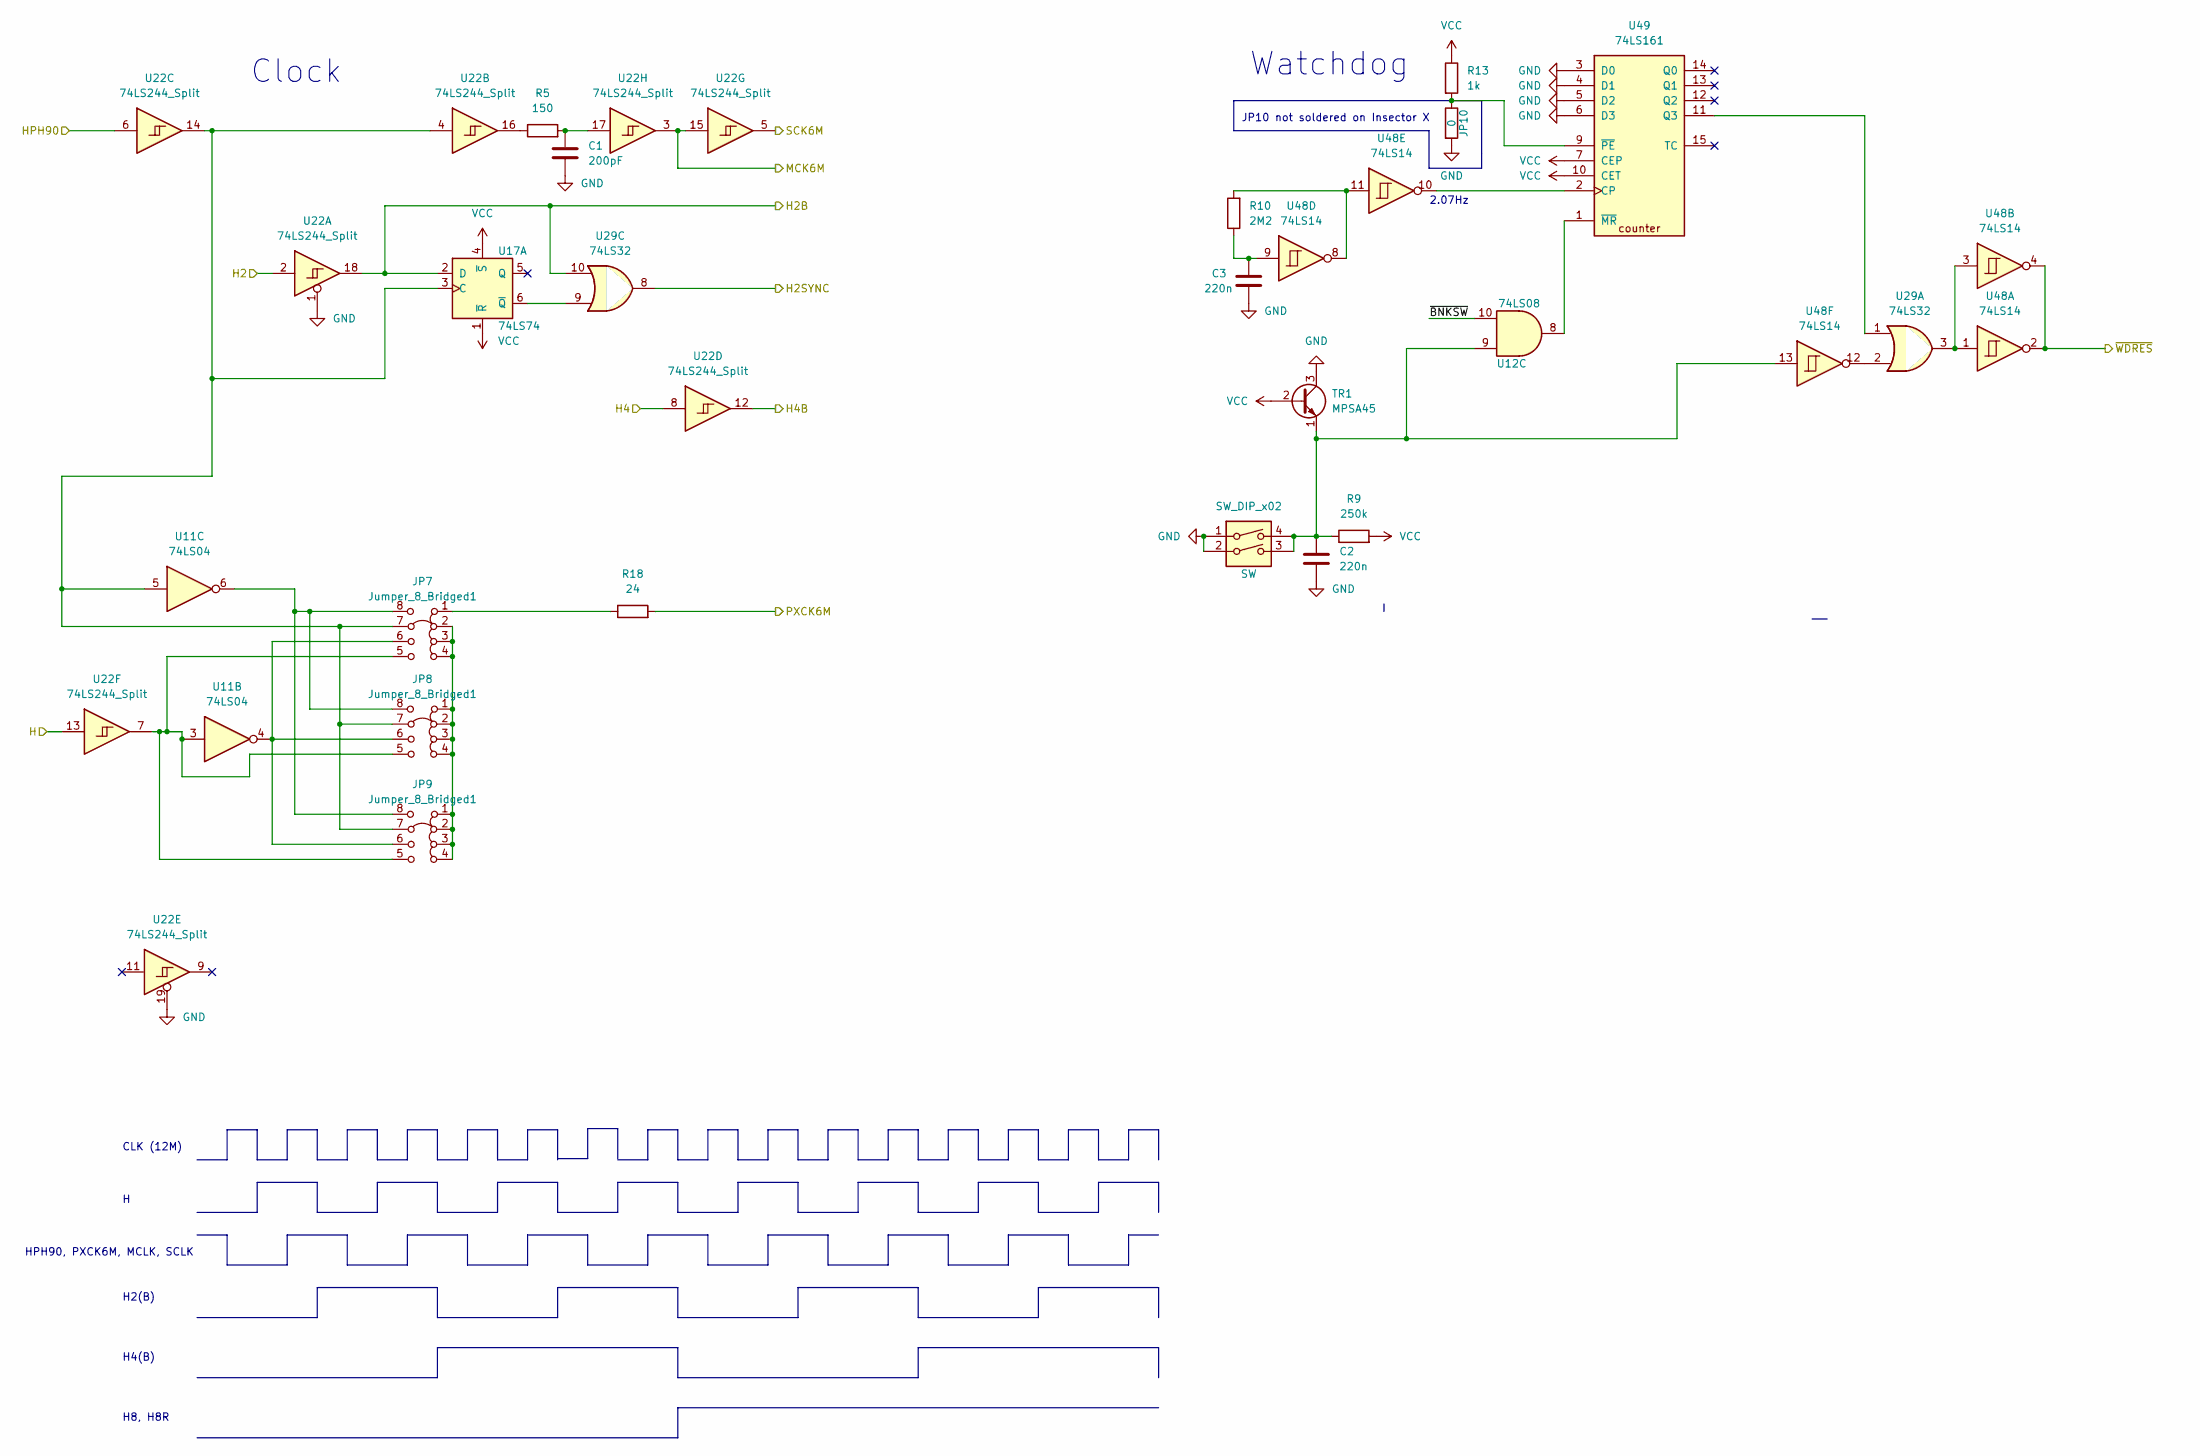
[picture p26: schematic misc.kicad_sch]

Parts:
C1: 200pF
C2, C3: 220n
JP7, JP8, JP9: Jumper_8_Bridged1
JP10: 0
R5: 150
R9: 250k
R10: 2M2
R13: 1k
R18: 24
SW1: SW_DIP_x02
TR1: MPSA45; TO-92_Inline
U11: 74LS04
U12: 74LS08
U17: 74LS74
U22: 74LS244_Split
U29: 74LS32
U48: 74LS14
U49: 74LS161

Connections:
GND: C1.2, C2.2, C3.2, JP10.2, SW1.1, SW1.2, TR1.3 (C), U22.1, U22.19, U49.3 (D0), U49.4 (D1), U49.5 (D2), U49.6 (D3)
H: U22.13
H2: U22.2
H2B: U17.2 (D), U22.18, U29.10
H2SYNC: U29.8
H4: U22.8
H4B: U22.12
HPH90: U22.6
MCK6M: U22.3, U22.15
unnamed: C1.1, R5.2, U22.17
unnamed: C2.1, R9.1, SW1.3, SW1.4, TR1.1 (E), U12.9, U48.13
unnamed: C3.1, R10.1, U48.9
unnamed: JP7.1 (A), R18.1
unnamed: JP7.2 (B), JP7.3 (C), JP7.4 (D), JP8.1 (A), JP8.2 (B), JP8.3 (C), JP8.4 (D), JP9.1 (A), JP9.2 (B), JP9.3 (C), JP9.4 (D)
unnamed: JP7.5 (B), JP8.5 (B), JP9.5 (B), U11.3, U22.7
unnamed: JP7.6 (B), JP8.6 (B), JP9.6 (B), U11.4
unnamed: JP7.7 (B), JP8.7 (B), JP9.7 (B), U11.5, U17.3 (C), U22.4, U22.14
unnamed: JP7.8 (B), JP8.8 (B), JP9.8 (B), U11.6
unnamed: JP10.1, R13.2, U49.9 (~PE)
unnamed: R5.1, U22.16
unnamed: R10.2, U48.8, U48.11
unnamed: U12.8, U49.1 (~MR)
unnamed: U17.6 (~Q), U29.9
unnamed: U29.1, U49.11 (Q3)
unnamed: U29.2, U48.12
unnamed: U29.3, U48.1, U48.3
unnamed: U48.10, U49.2 (CP)
PXCK6M: R18.2
SCK6M: U22.5
VCC: R9.2, R13.1, TR1.2 (B), U17.1 (~R), U17.4 (~S), U49.7 (CEP), U49.10 (CET)
~BNKSW: U12.10
~WDRES: U48.2, U48.4

Notes on the sheet:
HPH90, PXCK6M, MCLK, SCLK
H4(B)
CLK (12M)
JP10 not soldered on Insector X
Watchdog
2.07Hz
H2(B)
H8, H8R
Clock
