skutis/jtbubl/cores/kiwi/sch/insectx/sound.kicad_sch

## KiCad design cores/kiwi/sch/insectx/sound.kicad_sch (2022-12-07)

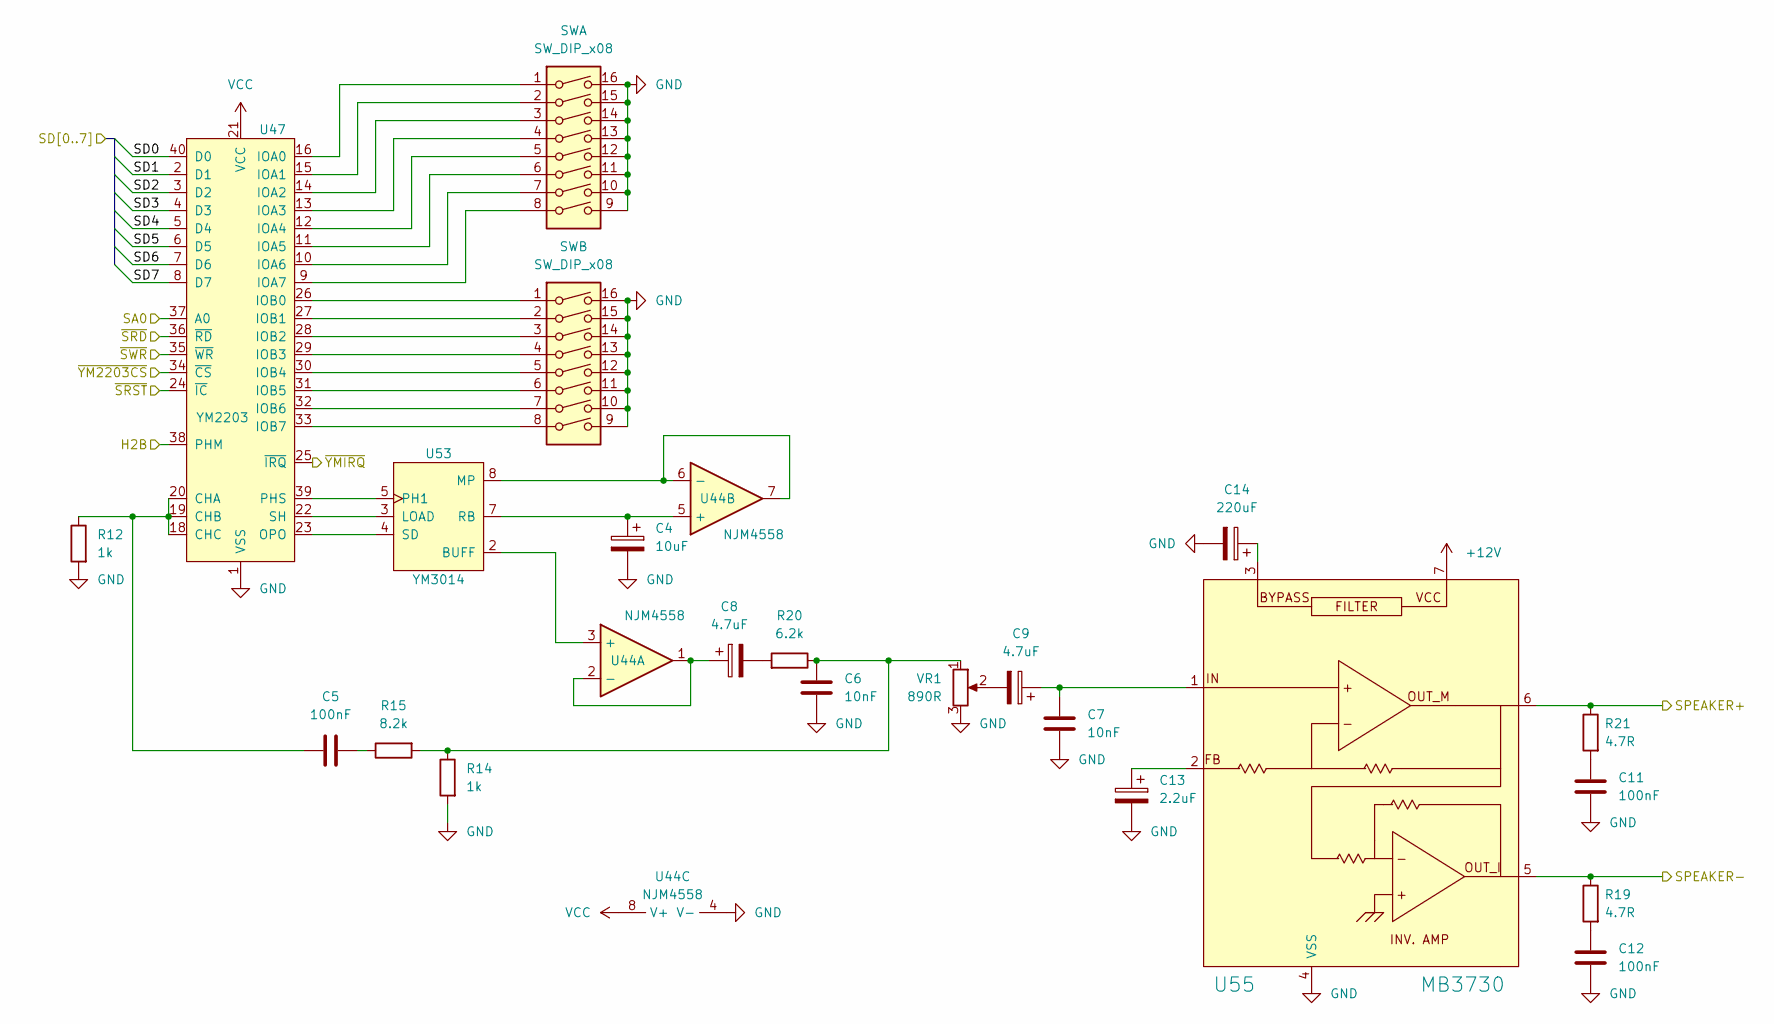
[picture p27: schematic sound.kicad_sch]

Parts:
C4: 10uF
C5, C11, C12: 100nF
C6, C7: 10nF
C8, C9: 4.7uF
C13: 2.2uF
C14: 220uF
R12, R14: 1k
R15: 8.2k
R19, R21: 4.7R
R20: 6.2k
SW2, SW3: SW_DIP_x08
U44: NJM4558
U47: YM2203; DIP-40_W15.24mm
U53: YM3014; DIP-8_W7.62mm
U55: MB3730
VR1: 890R

Connections:
+12V: U55.7
GND: C4.2, C6.2, C7.2, C11.1, C12.1, C13.2, C14.2, R12.2, R14.2, SW2.9, SW2.10, SW2.11, SW2.12, SW2.13, SW2.14, SW2.15, SW2.16, SW3.9, SW3.10, SW3.11, SW3.12, SW3.13, SW3.14, SW3.15, SW3.16, U44.4 (V-), U47.1 (VSS), U55.4 (VSS), VR1.3
H2B: U47.38 (PHM)
unnamed: C4.1, U44.5 (+), U53.7 (RB)
unnamed: C5.1, R15.1
unnamed: C5.2, R12.1, U47.18 (CHC), U47.19 (CHB), U47.20 (CHA)
unnamed: C6.1, R14.1, R15.2, R20.1, VR1.1
unnamed: C7.1, C9.1, U55.1
unnamed: C8.1, U44.1, U44.2 (-)
unnamed: C8.2, R20.2
unnamed: C9.2, VR1.2
unnamed: C11.2, R21.2
unnamed: C12.2, R19.2
unnamed: C13.1, U55.2
unnamed: C14.1, U55.3
unnamed: SW2.1, U47.16 (IOA0)
unnamed: SW2.2, U47.15 (IOA1)
unnamed: SW2.3, U47.14 (IOA2)
unnamed: SW2.4, U47.13 (IOA3)
unnamed: SW2.5, U47.12 (IOA4)
unnamed: SW2.6, U47.11 (IOA5)
unnamed: SW2.7, U47.10 (IOA6)
unnamed: SW2.8, U47.9 (IOA7)
unnamed: SW3.1, U47.26 (IOB0)
unnamed: SW3.2, U47.27 (IOB1)
unnamed: SW3.3, U47.28 (IOB2)
unnamed: SW3.4, U47.29 (IOB3)
unnamed: SW3.5, U47.30 (IOB4)
unnamed: SW3.6, U47.31 (IOB5)
unnamed: SW3.7, U47.32 (IOB6)
unnamed: SW3.8, U47.33 (IOB7)
unnamed: U44.3 (+), U53.2 (BUFF)
unnamed: U44.6 (-), U44.7, U53.8 (MP)
unnamed: U47.22 (SH), U53.3 (LOAD)
unnamed: U47.23 (OPO), U53.4 (SD)
unnamed: U47.39 (PHS), U53.5 (PH1)
SA0: U47.37 (A0)
SD0: U47.40 (D0)
SD1: U47.2 (D1)
SD2: U47.3 (D2)
SD3: U47.4 (D3)
SD4: U47.5 (D4)
SD5: U47.6 (D5)
SD6: U47.7 (D6)
SD7: U47.8 (D7)
SPEAKER+: R21.1, U55.6
SPEAKER-: R19.1, U55.5
VCC: U44.8 (V+), U47.21 (VCC)
~SRD: U47.36 (~RD)
~SRST: U47.24 (~IC)
~SWR: U47.35 (~WR)
~YM2203CS: U47.34 (~CS)
~YMIRQ: U47.25 (~IRQ)
