skutis/jtbubl/cores/kiwi/sch/insectx/untitled.kicad_sch

## KiCad design cores/kiwi/sch/insectx/untitled.kicad_sch (2022-12-01)

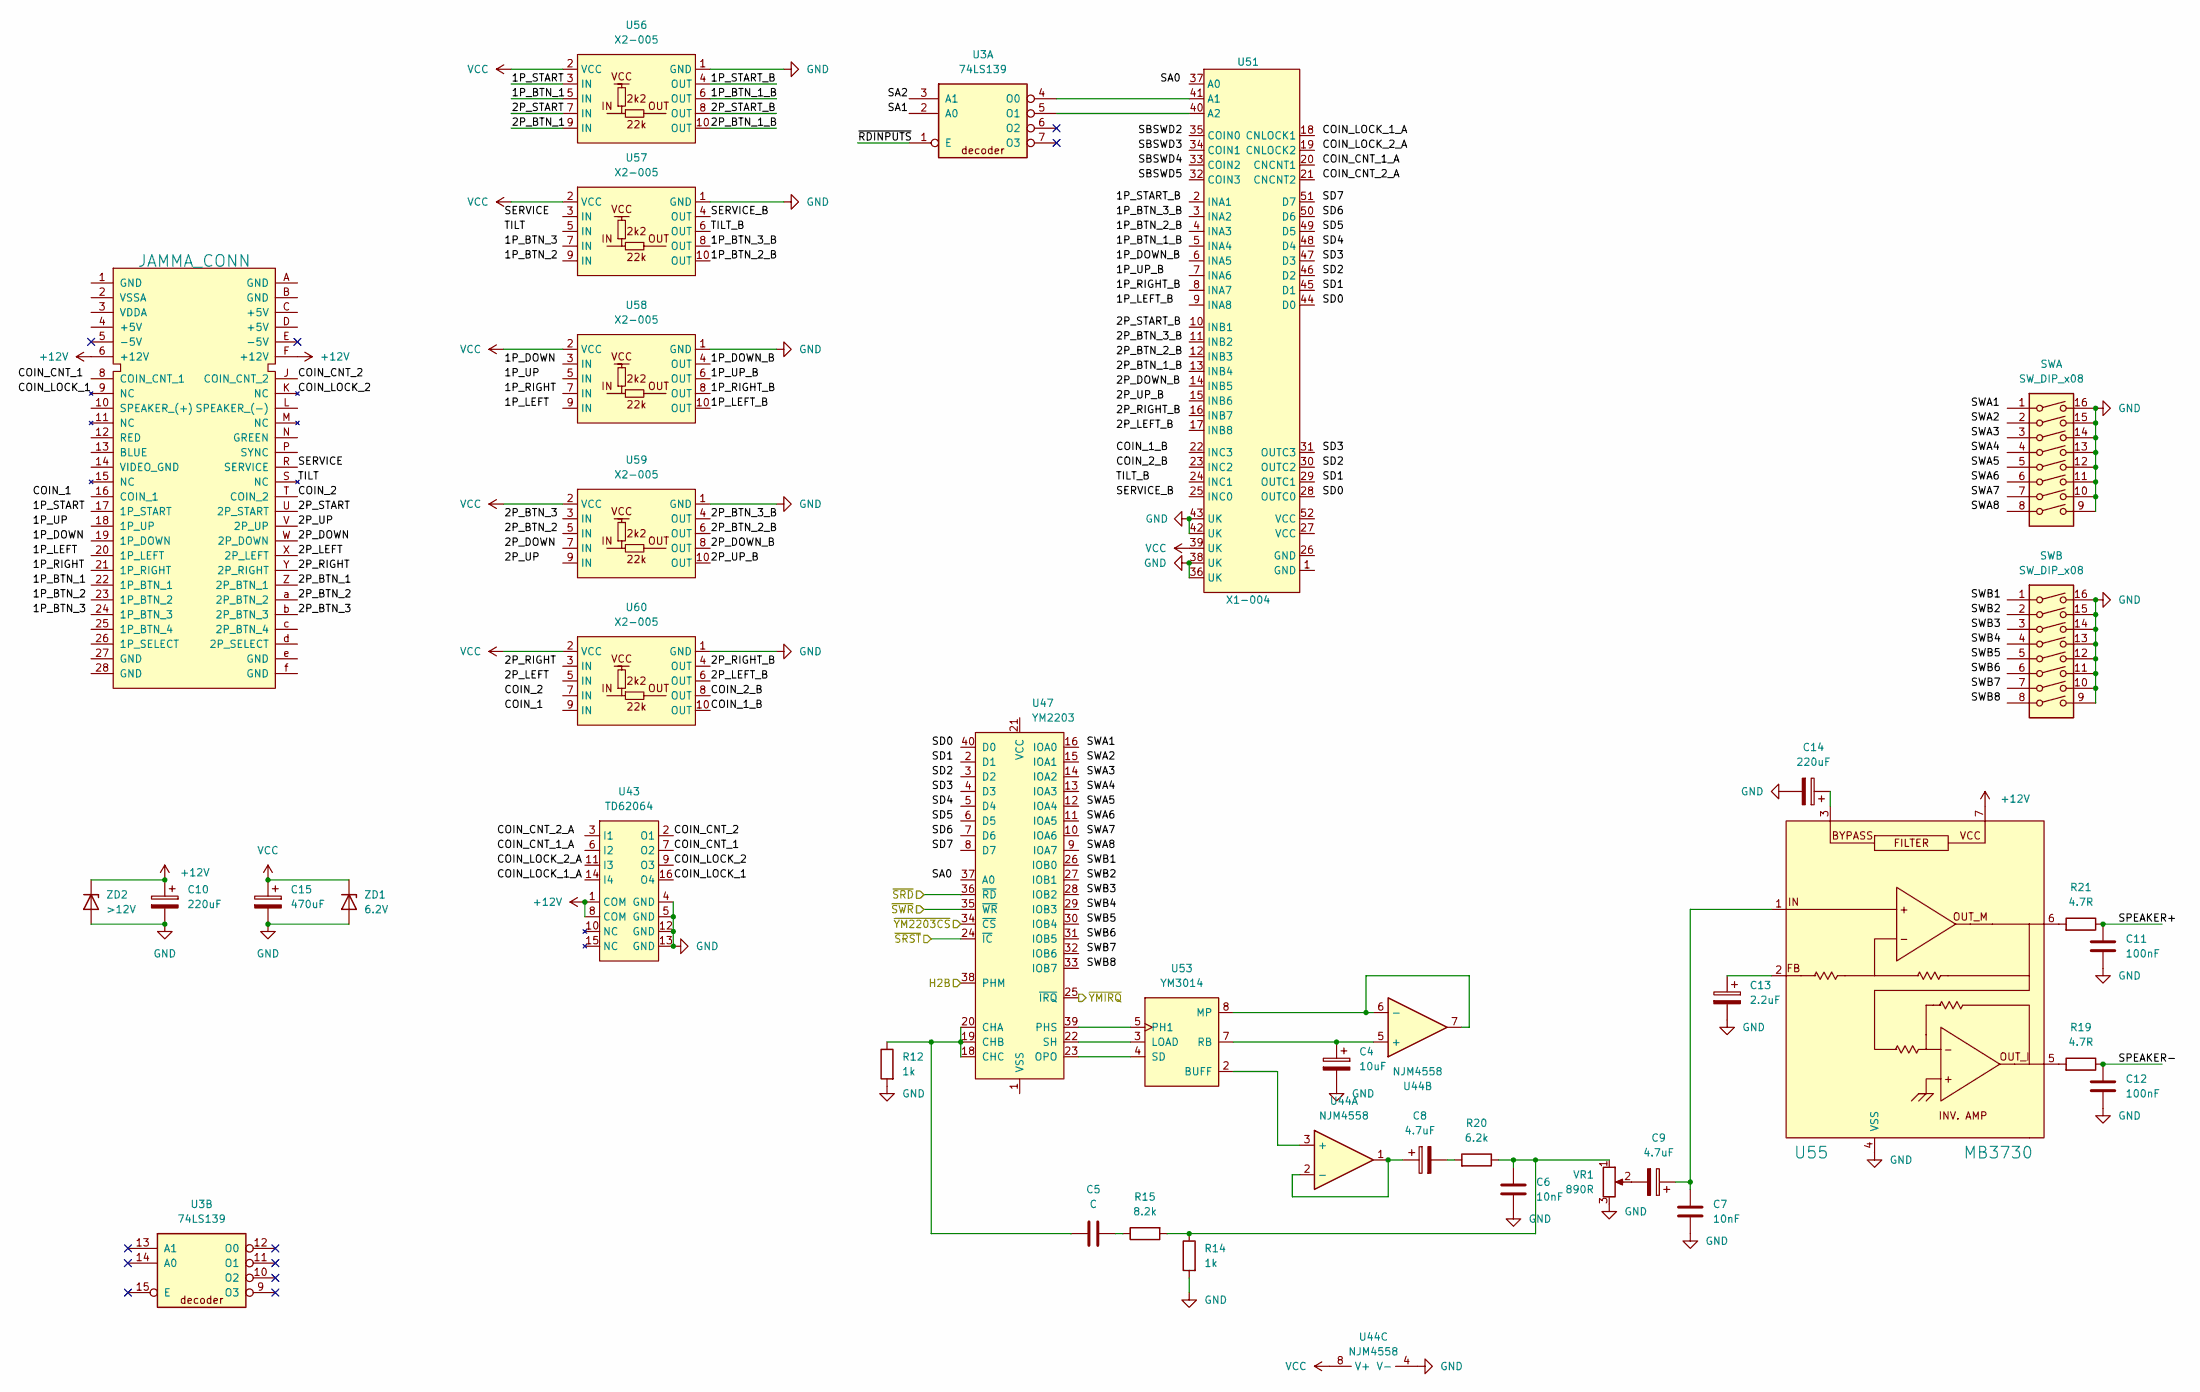
[picture p28: schematic untitled.kicad_sch]

Parts:
C4: 10uF
C5: C
C6, C7: 10nF
C8, C9: 4.7uF
C10, C14: 220uF
C11, C12: 100nF
C13: 2.2uF
C15: 470uF
R12, R14: 1k
R15: 8.2k
R19, R21: 4.7R
R20: 6.2k
SWA: SW_DIP_x08
SWB: SW_DIP_x08
U3: 74LS139
U43: TD62064
U44: NJM4558
U47: YM2203; DIP-40_W15.24mm
U51: X1-004
U53: YM3014; DIP-8_W7.62mm
U55: MB3730
U56, U57, U58, U59, U60: X2-005
VR1: 890R
ZD1: 6.2V
ZD2: >12V

Connections:
1P_BTN_1: U56.5 (IN)
1P_BTN_1_B: U56.6 (OUT)
1P_BTN_2_B: U57.10 (OUT)
1P_BTN_3_B: U57.8 (OUT)
1P_DOWN_B: U58.4 (OUT)
1P_LEFT_B: U58.10 (OUT)
1P_RIGHT_B: U58.8 (OUT)
1P_START: U56.3 (IN)
1P_START_B: U56.4 (OUT)
1P_UP_B: U58.6 (OUT)
2P_BTN_1: U56.9 (IN)
2P_BTN_1_B: U56.10 (OUT)
2P_BTN_2_B: U59.6 (OUT)
2P_BTN_3_B: U59.4 (OUT)
2P_DOWN_B: U59.8 (OUT)
2P_LEFT_B: U60.6 (OUT)
2P_RIGHT_B: U60.4 (OUT)
2P_START: U56.7 (IN)
2P_START_B: U56.8 (OUT)
2P_UP_B: U59.10 (OUT)
COIN_1_B: U60.10 (OUT)
COIN_2_B: U60.8 (OUT)
COIN_CNT_1: U43.7 (O2)
COIN_CNT_2: U43.2 (O1)
COIN_LOCK_1: U43.16 (O4)
COIN_LOCK_2: U43.9 (O3)
H2B: U47.38 (PHM)
unnamed: C4.1, U44.5 (+), U53.7 (RB)
unnamed: C5.1, R15.1
unnamed: C5.2, R12.1, U47.18 (CHC), U47.19 (CHB), U47.20 (CHA)
unnamed: C6.1, R14.1, R15.2, R20.1, VR1.1
unnamed: C7.1, C9.1, U55.1
unnamed: C8.1, U44.1, U44.2 (-)
unnamed: C8.2, R20.2
unnamed: C9.2, VR1.2
unnamed: C10.1, ZD2.1 (K)
unnamed: C10.2, ZD2.2 (A)
unnamed: C13.1, U55.2
unnamed: C14.1, U55.3
unnamed: C15.1, ZD1.1 (K)
unnamed: C15.2, ZD1.2 (A)
unnamed: R19.2, U55.5
unnamed: R21.2, U55.6
unnamed: SWA.9, SWA.10, SWA.11, SWA.12, SWA.13, SWA.14, SWA.15, SWA.16
unnamed: SWB.9, SWB.10, SWB.11, SWB.12, SWB.13, SWB.14, SWB.15, SWB.16
unnamed: U3.4 (O0), U51.41 (A1)
unnamed: U3.5 (O1), U51.40 (A2)
unnamed: U43.1 (COM), U43.8 (COM)
unnamed: U43.4 (GND), U43.5 (GND), U43.12 (GND), U43.13 (GND)
unnamed: U44.3 (+), U53.2 (BUFF)
unnamed: U44.6 (-), U44.7, U53.8 (MP)
unnamed: U47.22 (SH), U53.3 (LOAD)
unnamed: U47.23 (OPO), U53.4 (SD)
unnamed: U47.39 (PHS), U53.5 (PH1)
unnamed: U51.36 (UK), U51.38 (UK)
unnamed: U51.42 (UK), U51.43 (UK)
SERVICE_B: U57.4 (OUT)
SPEAKER+: C11.2, R21.1
SPEAKER-: C12.2, R19.1
TILT_B: U57.6 (OUT)
~RDINPUTS: U3.1 (E)
~SRD: U47.36 (~RD)
~SRST: U47.24 (~IC)
~SWR: U47.35 (~WR)
~YM2203CS: U47.34 (~CS)
~YMIRQ: U47.25 (~IRQ)
