skutis/jtbubl/cores/kiwi/sch/tnzs/cpu.kicad_sch

## KiCad design cores/kiwi/sch/tnzs/cpu.kicad_sch (2022-12-01)

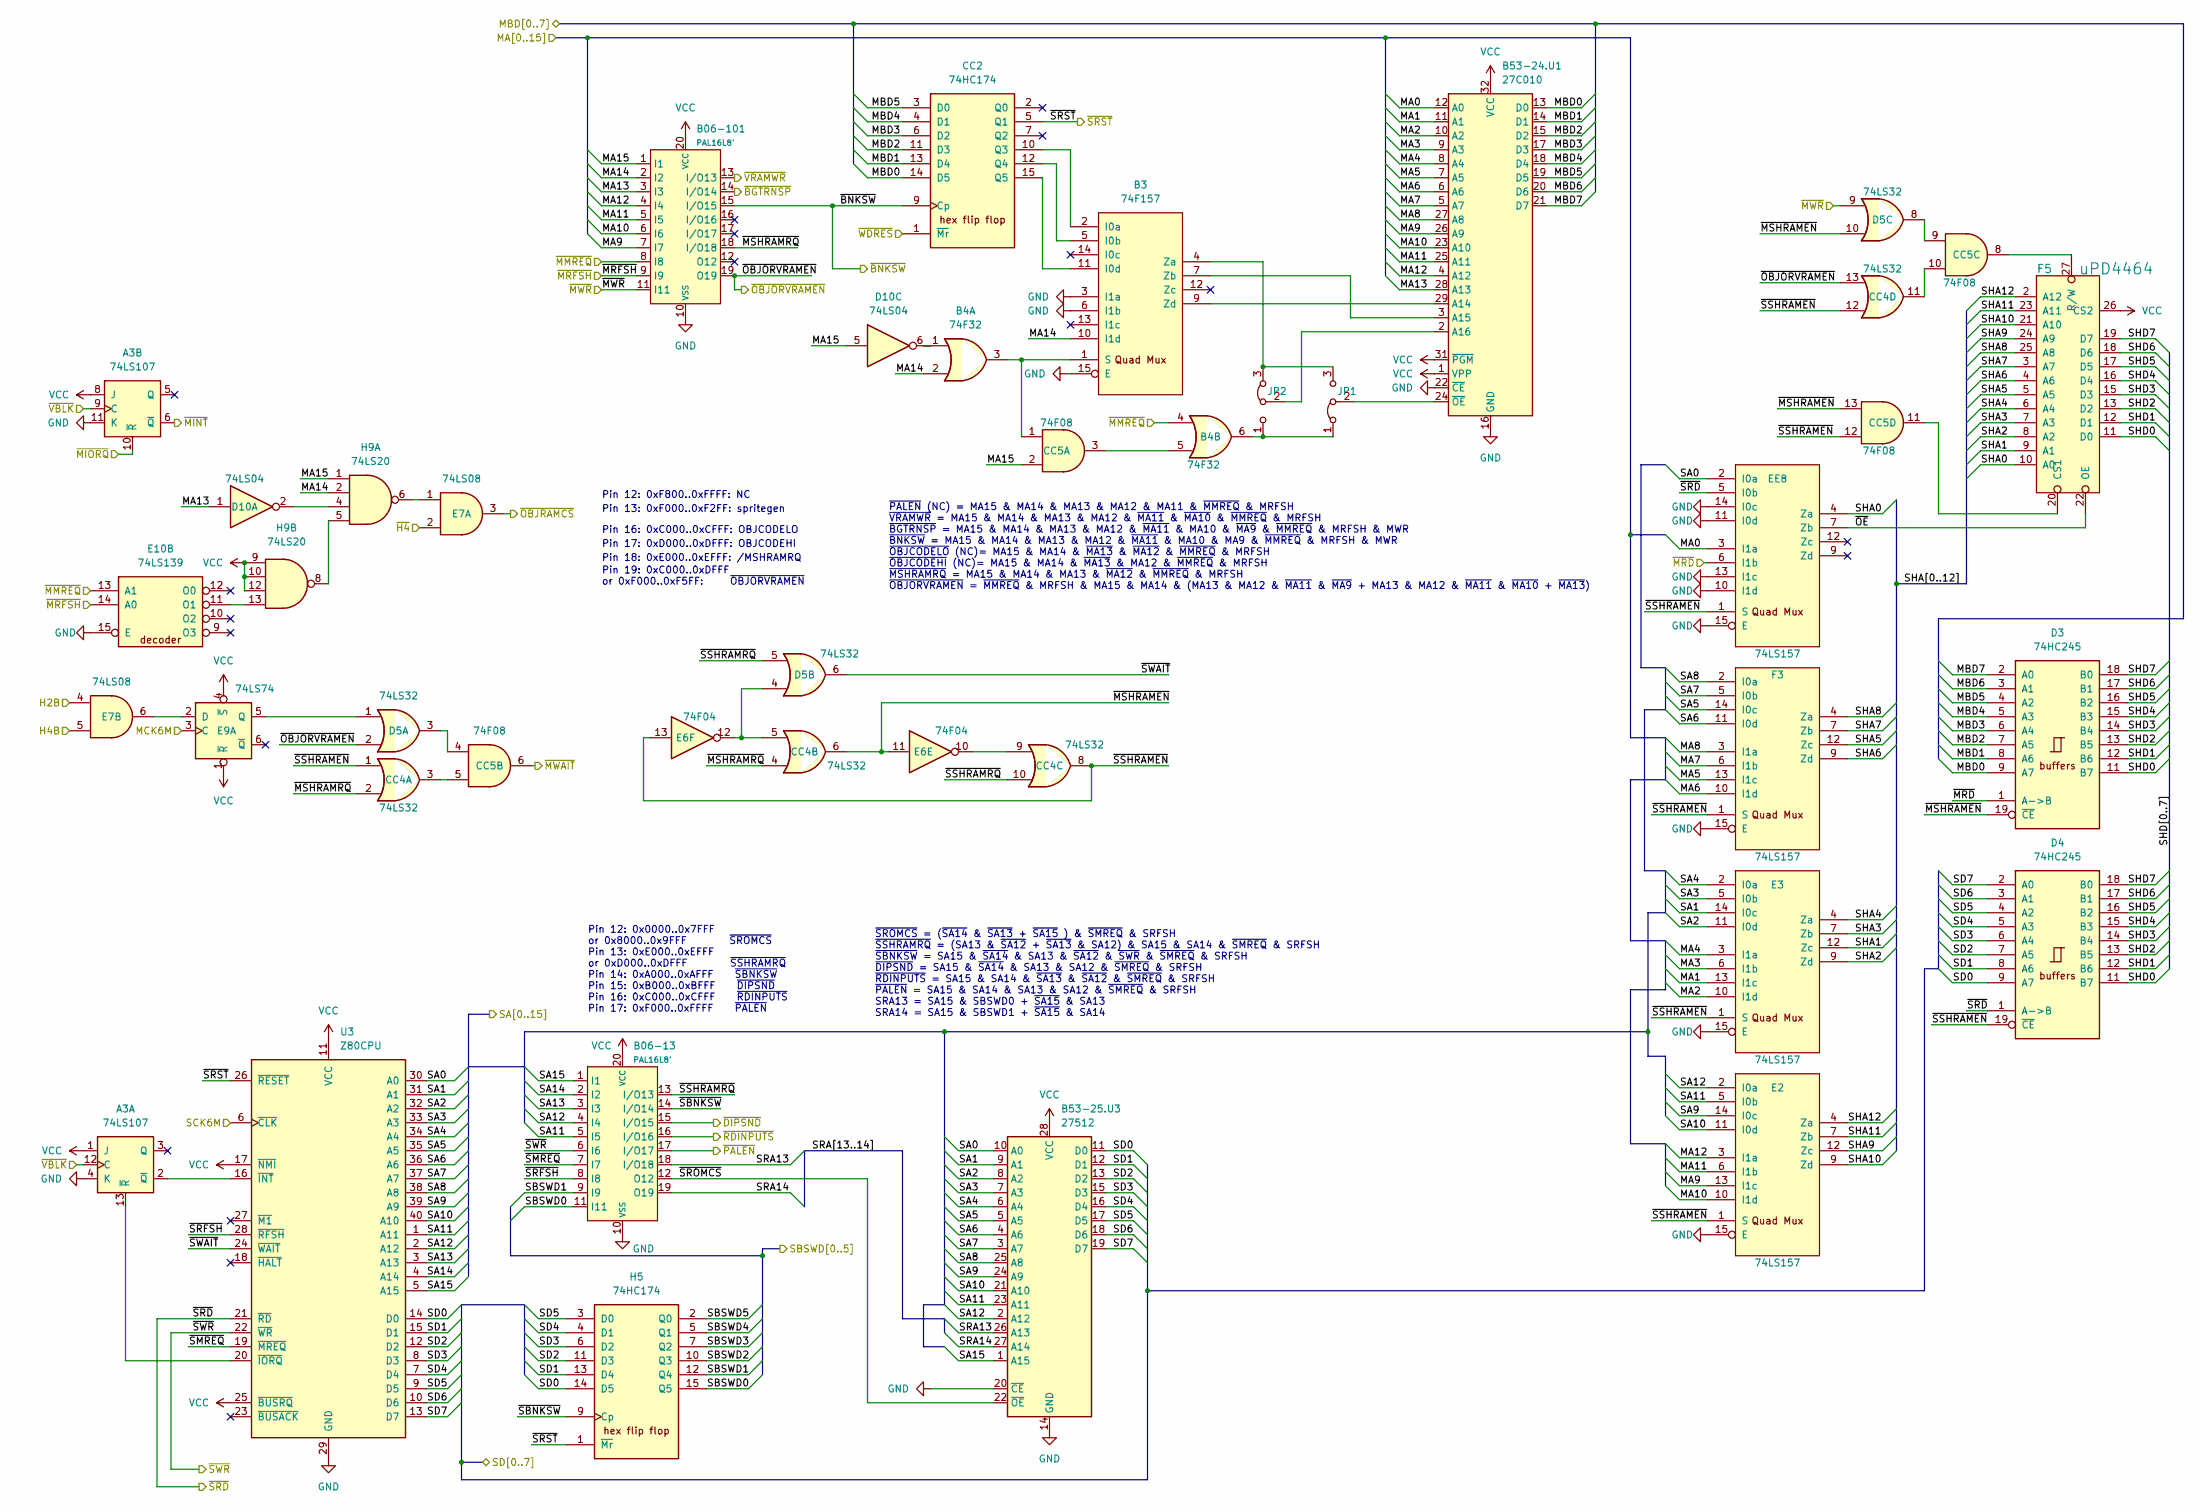
[picture p29: schematic cpu.kicad_sch]

Parts:
A3: 74LS107
B3: 74F157
B4: 74F32
B06-13, B06-101: PAL16L8’
B53-24.U1: 27C010
B53-25.U3: 27512; DIP-28_W15.24mm
CC2: 74HC174
CC4: 74LS32
CC5: 74F08
D3, D4: 74HC245
D5: 74LS32
D10: 74LS04
E2, E3: 74LS157
E6: 74F04
E7: 74LS08
E9: 74LS74
E10: 74LS139
EE8: 74LS157
F3: 74LS157
F5: uPD4464
H5: 74HC174
H9: 74LS20
JP1: Jumper_3_Bridged12
JP2: Jumper_3_Bridged23
U3: Z80CPU

Connections:
GND: A3.4 (K), A3.11 (K), B3.3 (I1a), B3.6 (I1b), B3.15 (E), B06-13.10 (VSS), B06-101.10 (VSS), B53-24.U1.16 (GND), B53-24.U1.22 (~CE), B53-25.U3.14 (GND), B53-25.U3.20 (~CE), E2.15 (E), E3.15 (E), E10.15 (E), EE8.10 (I1d), EE8.11 (I0d), EE8.13 (I1c), EE8.14 (I0c), EE8.15 (E), F3.15 (E), U3.29 (GND)
H2B: E7.4
H4B: E7.5
MA0: B53-24.U1.12 (A0), EE8.3 (I1a)
MA1: B53-24.U1.11 (A1), E3.13 (I1c)
MA2: B53-24.U1.10 (A2), E3.10 (I1d)
MA3: B53-24.U1.9 (A3), E3.6 (I1b)
MA4: B53-24.U1.8 (A4), E3.3 (I1a)
MA5: B53-24.U1.7 (A5), F3.13 (I1c)
MA6: B53-24.U1.6 (A6), F3.10 (I1d)
MA7: B53-24.U1.5 (A7), F3.6 (I1b)
MA8: B53-24.U1.27 (A8), F3.3 (I1a)
MA9: B06-101.7 (I7), B53-24.U1.26 (A9), E2.13 (I1c)
MA10: B06-101.6 (I6), B53-24.U1.23 (A10), E2.10 (I1d)
MA11: B06-101.5 (I5), B53-24.U1.25 (A11), E2.6 (I1b)
MA12: B06-101.4 (I4), B53-24.U1.4 (A12), E2.3 (I1a)
MA13: B06-101.3 (I3), B53-24.U1.28 (A13), D10.1
MA14: B3.10 (I1d), B4.2, B06-101.2 (I2), H9.2
MA15: B06-101.1 (I1), CC5.2, D10.5, H9.1
MBD0: B53-24.U1.13 (D0), CC2.14 (D5), D3.9 (A7)
MBD1: B53-24.U1.14 (D1), CC2.13 (D4), D3.8 (A6)
MBD2: B53-24.U1.15 (D2), CC2.11 (D3), D3.7 (A5)
MBD3: B53-24.U1.17 (D3), CC2.6 (D2), D3.6 (A4)
MBD4: B53-24.U1.18 (D4), CC2.4 (D1), D3.5 (A3)
MBD5: B53-24.U1.19 (D5), CC2.3 (D0), D3.4 (A2)
MBD6: B53-24.U1.20 (D6), D3.3 (A1)
MBD7: B53-24.U1.21 (D7), D3.2 (A0)
MCK6M: E9.3 (C)
unnamed: A3.2 (~Q), U3.16 (~INT)
unnamed: A3.13 (~R), U3.20 (~IORQ)
unnamed: B3.1 (S), B4.3, CC5.1
unnamed: B3.2 (I0a), CC2.10 (Q3)
unnamed: B3.4 (Za), JP1.3 (B), JP2.3 (B)
unnamed: B3.5 (I0b), CC2.12 (Q4)
unnamed: B3.7 (Zb), B53-24.U1.3 (A15)
unnamed: B3.9 (Zd), B53-24.U1.29 (A14)
unnamed: B3.11 (I0d), CC2.15 (Q5)
unnamed: B4.1, D10.6
unnamed: B4.5, CC5.3
unnamed: B4.6, JP1.1 (A), JP2.1 (A)
unnamed: B53-24.U1.2 (A16), JP2.2 (C)
unnamed: B53-24.U1.24 (~OE), JP1.2 (C)
unnamed: CC4.3, CC5.5
unnamed: CC4.5, D5.4, E6.12
unnamed: CC4.9, E6.10
unnamed: CC4.11, CC5.10
unnamed: CC5.4, D5.3
unnamed: CC5.8, F5.27 (R/W)
unnamed: CC5.9, D5.8
unnamed: CC5.11, F5.20 (CS1)
unnamed: D5.1, E9.5 (Q)
unnamed: D10.2, H9.4
unnamed: E7.1, H9.6
unnamed: E7.6, E9.2 (D)
unnamed: E10.11 (O1), H9.13
unnamed: H9.5, H9.8
SA0: B53-25.U3.10 (A0), EE8.2 (I0a), U3.30 (A0)
SA1: B53-25.U3.9 (A1), E3.14 (I0c), U3.31 (A1)
SA2: B53-25.U3.8 (A2), E3.11 (I0d), U3.32 (A2)
SA3: B53-25.U3.7 (A3), E3.5 (I0b), U3.33 (A3)
SA4: B53-25.U3.6 (A4), E3.2 (I0a), U3.34 (A4)
SA5: B53-25.U3.5 (A5), F3.14 (I0c), U3.35 (A5)
SA6: B53-25.U3.4 (A6), F3.11 (I0d), U3.36 (A6)
SA7: B53-25.U3.3 (A7), F3.5 (I0b), U3.37 (A7)
SA8: B53-25.U3.25 (A8), F3.2 (I0a), U3.38 (A8)
SA9: B53-25.U3.24 (A9), E2.14 (I0c), U3.39 (A9)
SA10: B53-25.U3.21 (A10), E2.11 (I0d), U3.40 (A10)
SA11: B06-13.5 (I5), B53-25.U3.23 (A11), E2.5 (I0b), U3.1 (A11)
SA12: B06-13.4 (I4), B53-25.U3.2 (A12), E2.2 (I0a), U3.2 (A12)
SA13: B06-13.3 (I3), U3.3 (A13)
SA14: B06-13.2 (I2), U3.4 (A14)
SA15: B06-13.1 (I1), B53-25.U3.1 (A15), U3.5 (A15)
SBSWD0: B06-13.11 (I11), H5.15 (Q5)
SBSWD1: B06-13.9 (I9), H5.12 (Q4)
SBSWD2: H5.10 (Q3)
SBSWD3: H5.7 (Q2)
SBSWD4: H5.5 (Q1)
SBSWD5: H5.2 (Q0)
SCK6M: U3.6 (~CLK)
SD0: B53-25.U3.11 (D0), D4.9 (A7), H5.14 (D5), U3.14 (D0)
SD1: B53-25.U3.12 (D1), D4.8 (A6), H5.13 (D4), U3.15 (D1)
SD2: B53-25.U3.13 (D2), D4.7 (A5), H5.11 (D3), U3.12 (D2)
SD3: B53-25.U3.15 (D3), D4.6 (A4), H5.6 (D2), U3.8 (D3)
SD4: B53-25.U3.16 (D4), D4.5 (A3), H5.4 (D1), U3.7 (D4)
SD5: B53-25.U3.17 (D5), D4.4 (A2), H5.3 (D0), U3.9 (D5)
SD6: B53-25.U3.18 (D6), D4.3 (A1), U3.10 (D6)
SD7: B53-25.U3.19 (D7), D4.2 (A0), U3.13 (D7)
SHA0: EE8.4 (Za), F5.10 (A0)
SHA1: E3.12 (Zc), F5.9 (A1)
SHA2: E3.9 (Zd), F5.8 (A2)
SHA3: E3.7 (Zb), F5.7 (A3)
SHA4: E3.4 (Za), F5.6 (A4)
SHA5: F3.12 (Zc), F5.5 (A5)
SHA6: F3.9 (Zd), F5.4 (A6)
SHA7: F3.7 (Zb), F5.3 (A7)
SHA8: F3.4 (Za), F5.25 (A8)
SHA9: E2.12 (Zc), F5.24 (A9)
SHA10: E2.9 (Zd), F5.21 (A10)
SHA11: E2.7 (Zb), F5.23 (A11)
SHA12: E2.4 (Za), F5.2 (A12)
SHD0: D3.11 (B7), D4.11 (B7), F5.11 (D0)
SHD1: D3.12 (B6), D4.12 (B6), F5.12 (D1)
SHD2: D3.13 (B5), D4.13 (B5), F5.13 (D2)
SHD3: D3.14 (B4), D4.14 (B4), F5.15 (D3)
SHD4: D3.15 (B3), D4.15 (B3), F5.16 (D4)
SHD5: D3.16 (B2), D4.16 (B2), F5.17 (D5)
SHD6: D3.17 (B1), D4.17 (B1), F5.18 (D6)
SHD7: D3.18 (B0), D4.18 (B0), F5.19 (D7)
SRA13: B06-13.18 (I/O18), B53-25.U3.26 (A13)
SRA14: B06-13.19 (O19), B53-25.U3.27 (A14)
VCC: A3.1 (J), A3.8 (J), B06-13.20 (VCC), B06-101.20 (VCC), B53-24.U1.1 (VPP), B53-24.U1.31 (~PGM), B53-24.U1.32 (VCC), B53-25.U3.28 (VCC), E9.1 (~R), E9.4 (~S), F5.26 (CS2), H9.9, H9.10, H9.12, U3.11 (VCC), U3.17 (~NMI), U3.25 (~BUSRQ)
~BGTRNSP: B06-101.14 (I/O14)
~BNKSW: B06-101.15 (I/O15), CC2.9 (Cp)
~DIPSND: B06-13.15 (I/O15)
~H4: E7.2
~MINT: A3.6 (~Q)
~MIORQ: A3.10 (~R)
~MMREQ: B4.4, B06-101.8 (I8), E10.13 (A1)
~MRD: D3.1 (A->B), EE8.6 (I1b)
~MRFSH: B06-101.9 (I9), E10.14 (A0)
~MSHRAMEN: CC4.6, CC5.13, D3.19 (~CE), D5.10, E6.11
~MSHRAMRQ: B06-101.18 (I/O18), CC4.2, CC4.4
~MWAIT: CC5.6
~MWR: B06-101.11 (I11), D5.9
~OBJORVRAMEN: B06-101.19 (O19), CC4.13, D5.2
~OBJRAMCS: E7.3
~OE: EE8.7 (Zb), F5.22 (OE)
~PALEN: B06-13.17 (I/O17)
~RDINPUTS: B06-13.16 (I/O16)
~SBNKSW: B06-13.14 (I/O14), H5.9 (Cp)
~SMREQ: B06-13.7 (I7), U3.19 (~MREQ)
~SRD: D4.1 (A->B), EE8.5 (I0b), U3.21 (~RD)
~SRFSH: B06-13.8 (I8), U3.28 (~RFSH)
~SROMCS: B06-13.12 (O12), B53-25.U3.22 (~OE)
~SRST: CC2.5 (Q1), H5.1 (~Mr), U3.26 (~RESET)
~SSHRAMEN: CC4.1, CC4.8, CC4.12, CC5.12, D4.19 (~CE), E2.1 (S), E3.1 (S), E6.13, EE8.1 (S), F3.1 (S)
~SSHRAMRQ: B06-13.13 (I/O13), CC4.10, D5.5
~SWAIT: D5.6, U3.24 (~WAIT)
~SWR: B06-13.6 (I6), U3.22 (~WR)
~VBLK: A3.9 (C), A3.12 (C)
~VRAMWR: B06-101.13 (I/O13)
~WDRES: CC2.1 (~Mr)

Notes on the sheet:
Pin 12: 0x0000..0x7FFF or 0x8000..0x9FFF ~{SROMCS} Pin 13: 0xE000..0xEFFF or 0xD000..0xDFFF ~{SSHRAMRQ} Pin 14: 0xA000..0xAFFF ~{SBNKSW} Pin 15: 0xB000..0xBFFF ~{DIPSND} Pin 16: 0xC000..0xCFFF ~{RDINPUTS} Pin 17: 0xF000..0xFFFF ~{PALEN}
Pin 17: 0xD000..0xDFFF: OBJCODEHI
Pin 13: 0xF000..0xF2FF: spritegen
Pin 18: 0xE000..0xEFFF: /MSHRAMRQ
Pin 12: 0xF800..0xFFFF: NC
~{PALEN} (NC) = MA15 & MA14 & MA13 & MA12 & MA11 & ~{MMREQ} & MRFSH ~{VRAMWR} = MA15 & MA14 & MA13 & MA12 & ~{MA11} & ~{MA10} & ~{MMREQ} & MRFSH ~{BGTRNSP} = MA15 & MA14 & MA13 & MA12 & ~{MA11} & MA10 & ~{MA9} & ~{MMREQ} & MRFSH & MWR ~{BNKSW} = MA15 & MA14 & MA13 & MA12 & ~{MA11} & MA10 & MA9 & ~{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
~{SROMCS} = (~{SA14} & ~{SA13} + ~{SA15} ) & ~{SMREQ} & SRFSH ~{SSHRAMRQ} = (SA13 & ~{SA12} + ~{SA13} & SA12) & SA15 & SA14 & ~{SMREQ} & SRFSH ~{SBNKSW} = SA15 & ~{SA14} & SA13 & ~{SA12} & ~{SWR} & ~{SMREQ} & SRFSH ~{DIPSND} = SA15 & ~{SA14} & SA13 & SA12 & ~{SMREQ} & SRFSH ~{RDINPUTS} = SA15 & SA1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
Pin 16: 0xC000..0xCFFF: OBJCODELO
Pin 19: 0xC000..0xDFFF or 0xF000..0xF5FF: ~{OBJORVRAMEN}
