skutis/jtbubl/cores/kiwi/sch/tnzs/graphics.kicad_sch

## KiCad design cores/kiwi/sch/tnzs/graphics.kicad_sch (2022-12-01)

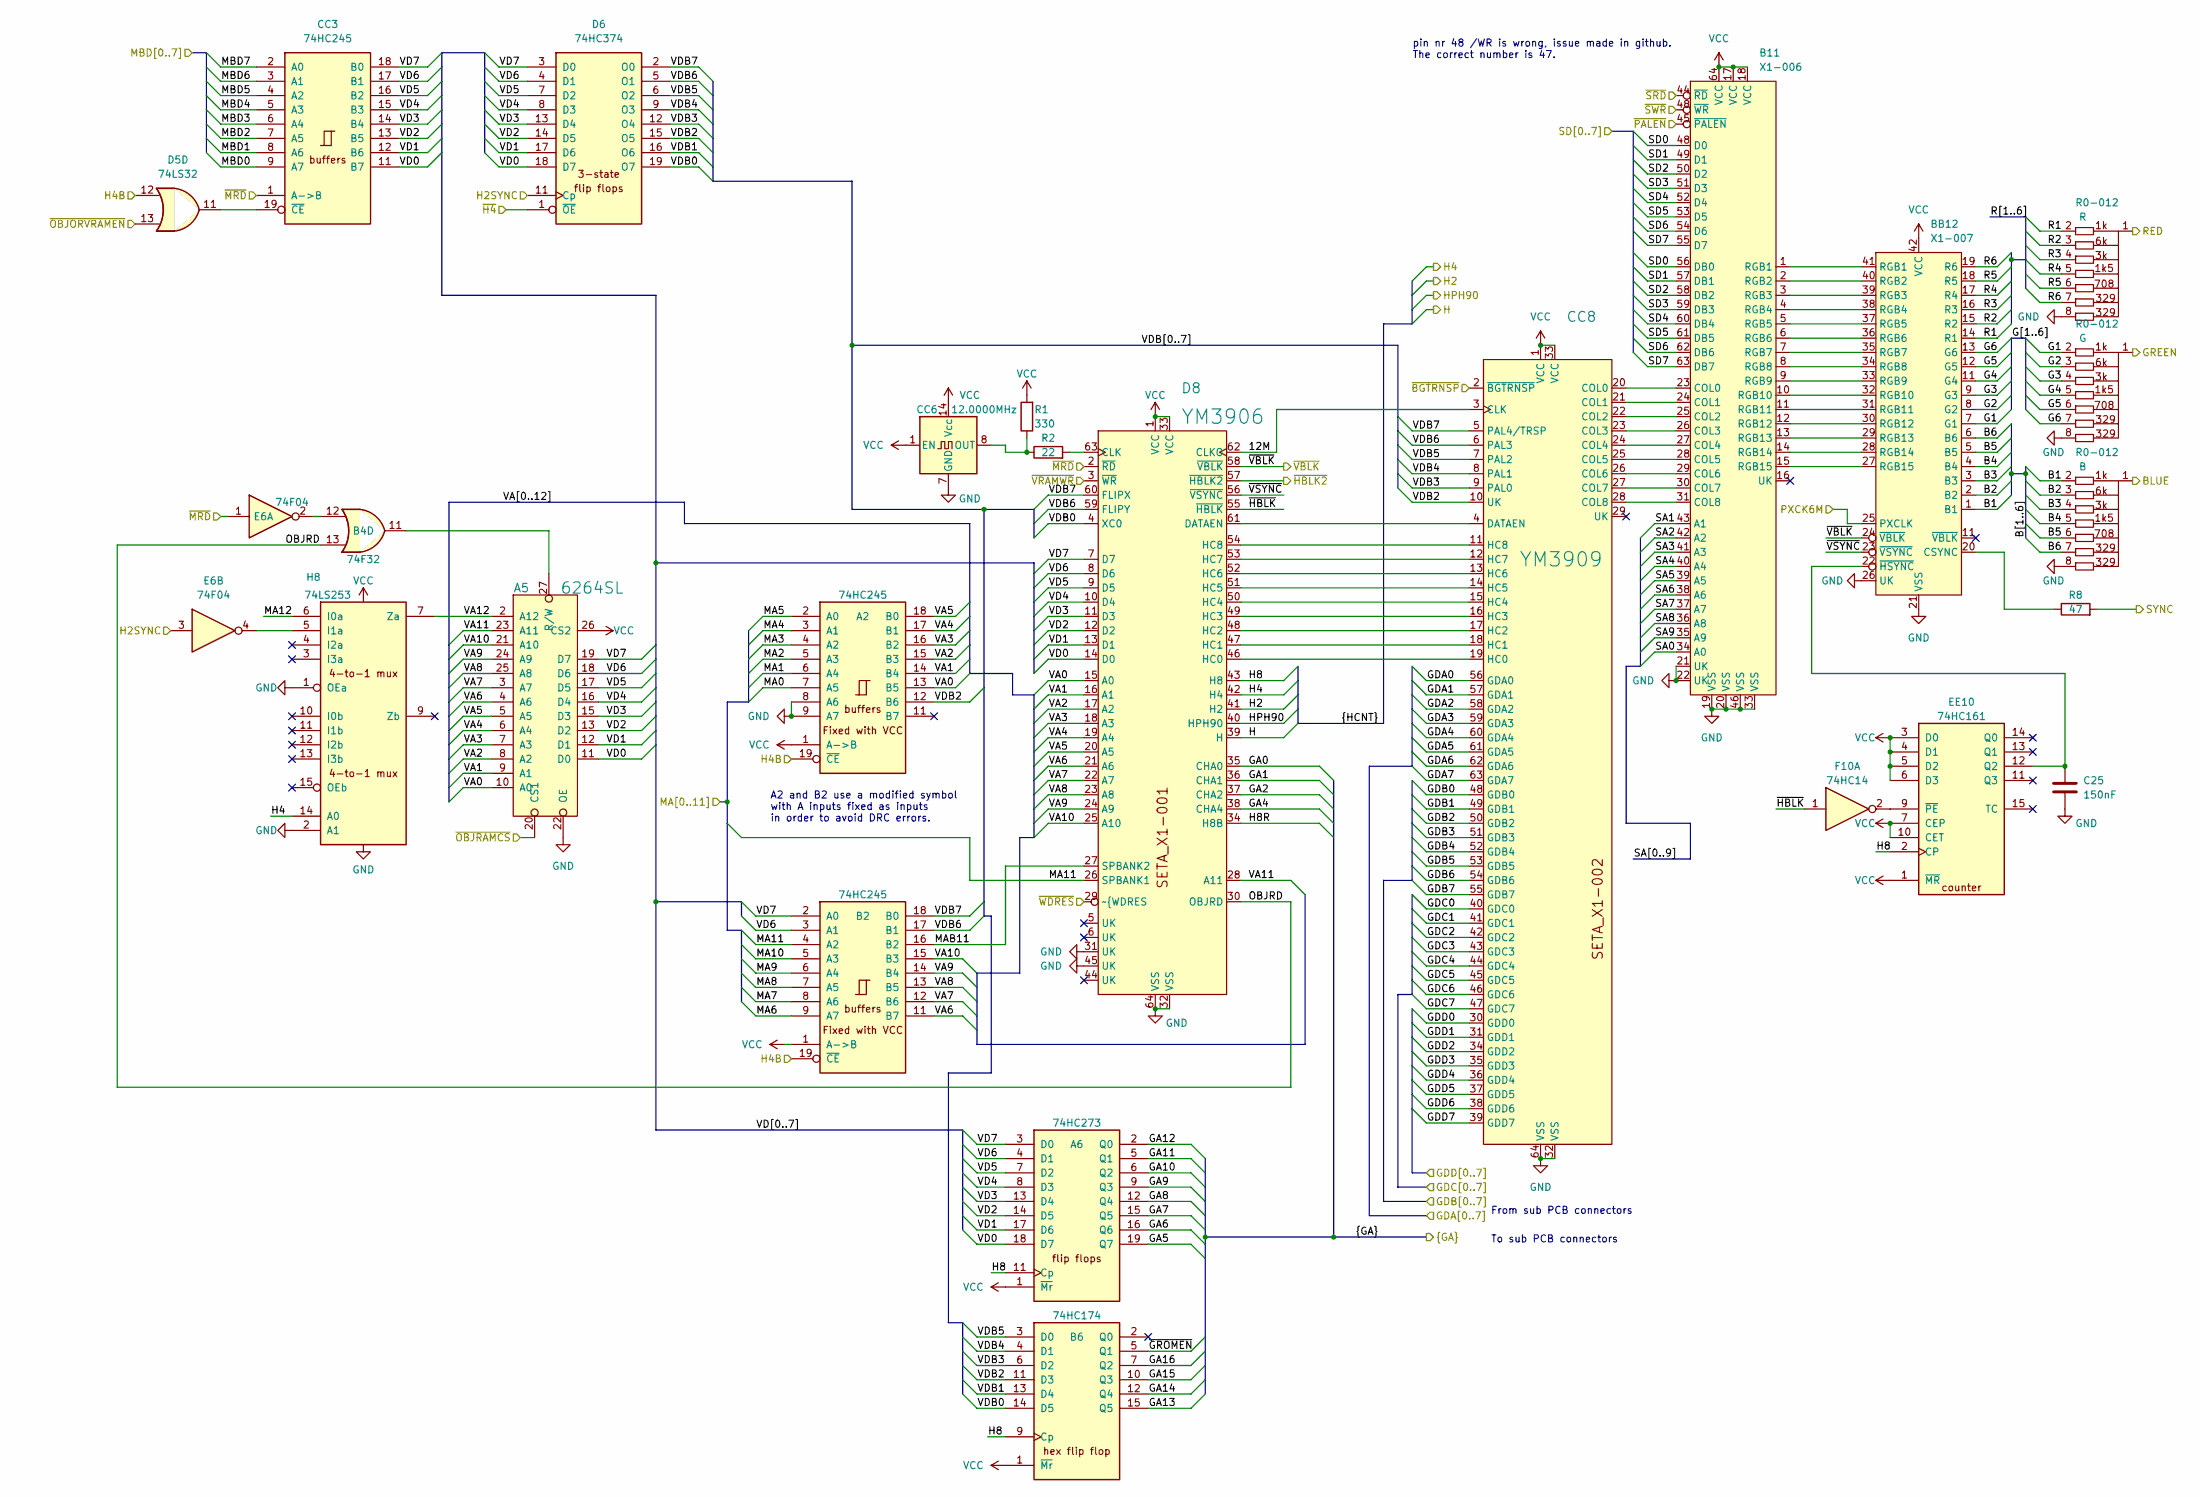
[picture p30: schematic graphics.kicad_sch]

Parts:
A2: 74HC245
A5: 6264SL
A6: 74HC273
B1: R0-012
B2: 74HC245
B4: 74F32
B6: 74HC174
B11: X1-006
BB12: X1-007
C25: 150nF
CC3: 74HC245
CC6: 12.0000MHz; Oscillator_DIP-14
CC8: YM3909
D5: 74LS32
D6: 74HC374
D8: YM3906
E6: 74F04
EE10: 74HC161
F10: 74HC14
G1: R0-012
H8: 74LS253
R1: 330
R2: 22
R8: 47
R999: R0-012

Connections:
12M: CC8.3 (CLK), D8.62 (CLKO)
B1: B1.2, BB12.1 (B1)
B2: B1.3, BB12.2 (B2)
B3: B1.4, BB12.3 (B3)
B4: B1.5, BB12.4 (B4)
B5: B1.6, BB12.5 (B5)
B6: B1.7, BB12.6 (B6)
BLUE: B1.1
G1: BB12.7 (G1), G1.2
G2: BB12.8 (G2), G1.3
G3: BB12.9 (G3), G1.4
G4: BB12.11 (G4), G1.5
G5: BB12.12 (G5), G1.6
G6: BB12.13 (G6), G1.7
GA0: D8.35 (CHA0)
GA1: D8.36 (CHA1)
GA2: D8.37 (CHA2)
GA4: D8.38 (CHA4)
GA5: A6.19 (Q7)
GA6: A6.16 (Q6)
GA7: A6.15 (Q5)
GA8: A6.12 (Q4)
GA9: A6.9 (Q3)
GA10: A6.6 (Q2)
GA11: A6.5 (Q1)
GA12: A6.2 (Q0)
GA13: B6.15 (Q5)
GA14: B6.12 (Q4)
GA15: B6.10 (Q3)
GA16: B6.7 (Q2)
GDA0: CC8.56 (GDA0)
GDA1: CC8.57 (GDA1)
GDA2: CC8.58 (GDA2)
GDA3: CC8.59 (GDA3)
GDA4: CC8.60 (GDA4)
GDA5: CC8.61 (GDA5)
GDA6: CC8.62 (GDA6)
GDA7: CC8.63 (GDA7)
GDB0: CC8.48 (GDB0)
GDB1: CC8.49 (GDB1)
GDB2: CC8.50 (GDB2)
GDB3: CC8.51 (GDB3)
GDB4: CC8.52 (GDB4)
GDB5: CC8.53 (GDB5)
GDB6: CC8.54 (GDB6)
GDB7: CC8.55 (GDB7)
GDC0: CC8.40 (GDC0)
GDC1: CC8.41 (GDC1)
GDC2: CC8.42 (GDC2)
GDC3: CC8.43 (GDC3)
GDC4: CC8.44 (GDC4)
GDC5: CC8.45 (GDC5)
GDC6: CC8.46 (GDC6)
GDC7: CC8.47 (GDC7)
GDD0: CC8.30 (GDD0)
GDD1: CC8.31 (GDD1)
GDD2: CC8.34 (GDD2)
GDD3: CC8.35 (GDD3)
GDD4: CC8.36 (GDD4)
GDD5: CC8.37 (GDD5)
GDD6: CC8.38 (GDD6)
GDD7: CC8.39 (GDD7)
GND: A2.8 (A6), A2.9 (A7), A5.22 (OE), B1.8, B11.19 (VSS), B11.20 (VSS), B11.21 (UK), B11.22 (UK), B11.33 (VSS), B11.46 (VSS), BB12.21 (VSS), BB12.26 (UK), C25.2, CC6.7 (GND), CC8.32 (VSS), CC8.64 (VSS), D8.31 (UK), D8.32 (VSS), D8.45 (UK), D8.64 (VSS), G1.8, H8.1 (OEa), H8.2 (A1), H8.8 (VSS), R999.8
GREEN: G1.1
H: D8.39 (H)
H2: D8.41 (H2)
H2SYNC: D6.11 (Cp), E6.3
H4: D8.42 (H4), H8.14 (A0)
H4B: A2.19 (~CE), B2.19 (~CE), D5.12
H8: A6.11 (Cp), B6.9 (Cp), D8.43 (H8), EE10.2 (CP)
H8R: D8.34 (H8B)
HPH90: D8.40 (HPH90)
MA0: A2.7 (A5)
MA1: A2.6 (A4)
MA2: A2.5 (A3)
MA3: A2.4 (A2)
MA4: A2.3 (A1)
MA5: A2.2 (A0)
MA6: B2.9 (A7)
MA7: B2.8 (A6)
MA8: B2.7 (A5)
MA9: B2.6 (A4)
MA10: B2.5 (A3)
MA11: B2.4 (A2), D8.26 (SPBANK1)
MA12: H8.6 (I0a)
MAB11: B2.16 (B2), D8.27 (SPBANK2)
MBD0: CC3.9 (A7)
MBD1: CC3.8 (A6)
MBD2: CC3.7 (A5)
MBD3: CC3.6 (A4)
MBD4: CC3.5 (A3)
MBD5: CC3.4 (A2)
MBD6: CC3.3 (A1)
MBD7: CC3.2 (A0)
unnamed: A5.27 (R/W), B4.11
unnamed: B4.12, E6.2
unnamed: B11.1 (RGB1), BB12.41 (RGB1)
unnamed: B11.2 (RGB2), BB12.40 (RGB2)
unnamed: B11.3 (RGB3), BB12.39 (RGB3)
unnamed: B11.4 (RGB4), BB12.38 (RGB4)
unnamed: B11.5 (RGB5), BB12.37 (RGB5)
unnamed: B11.6 (RGB6), BB12.36 (RGB6)
unnamed: B11.7 (RGB7), BB12.35 (RGB7)
unnamed: B11.8 (RGB8), BB12.34 (RGB8)
unnamed: B11.9 (RGB9), BB12.33 (RGB9)
unnamed: B11.10 (RGB10), BB12.32 (RGB10)
unnamed: B11.11 (RGB11), BB12.31 (RGB11)
unnamed: B11.12 (RGB12), BB12.30 (RGB12)
unnamed: B11.13 (RGB13), BB12.29 (RGB13)
unnamed: B11.14 (RGB14), BB12.28 (RGB14)
unnamed: B11.15 (RGB15), BB12.27 (RGB15)
unnamed: B11.23 (COL0), CC8.20 (COL0)
unnamed: B11.24 (COL1), CC8.21 (COL1)
unnamed: B11.25 (COL2), CC8.22 (COL2)
unnamed: B11.26 (COL3), CC8.23 (COL3)
unnamed: B11.27 (COL4), CC8.24 (COL4)
unnamed: B11.28 (COL5), CC8.25 (COL5)
unnamed: B11.29 (COL6), CC8.26 (COL6)
unnamed: B11.30 (COL7), CC8.27 (COL7)
unnamed: B11.31 (COL8), CC8.28 (COL8)
unnamed: BB12.20 (CSYNC), R8.1
unnamed: BB12.22 (~HSYNC), C25.1, EE10.12 (Q2)
unnamed: CC3.19 (~CE), D5.11
unnamed: CC6.8 (OUT), R1.1, R2.1
unnamed: CC8.4 (DATAEN), D8.61 (DATAEN)
unnamed: CC8.11 (HC8), D8.54 (HC8)
unnamed: CC8.12 (HC7), D8.53 (HC7)
unnamed: CC8.13 (HC6), D8.52 (HC6)
unnamed: CC8.14 (HC5), D8.51 (HC5)
unnamed: CC8.15 (HC4), D8.50 (HC4)
unnamed: CC8.16 (HC3), D8.49 (HC3)
unnamed: CC8.17 (HC2), D8.48 (HC2)
unnamed: CC8.18 (HC1), D8.47 (HC1)
unnamed: CC8.19 (HC0), D8.46 (HC0)
unnamed: D8.63 (CLK), R2.2
unnamed: E6.4, H8.5 (I1a)
unnamed: EE10.9 (~PE), F10.2
OBJRD: B4.13, D8.30 (OBJRD)
PXCK6M: BB12.25 (PXCLK)
R1: BB12.14 (R1), R999.2
R2: BB12.15 (R2), R999.3
R3: BB12.16 (R3), R999.4
R4: BB12.17 (R4), R999.5
R5: BB12.18 (R5), R999.6
R6: BB12.19 (R6), R999.7
RED: R999.1
SA0: B11.34 (A0)
SA1: B11.43 (A1)
SA2: B11.42 (A2)
SA3: B11.41 (A3)
SA4: B11.40 (A4)
SA5: B11.39 (A5)
SA6: B11.38 (A6)
SA7: B11.37 (A7)
SA8: B11.36 (A8)
SA9: B11.35 (A9)
SD0: B11.48 (D0), B11.56 (DB0)
SD1: B11.49 (D1), B11.57 (DB1)
SD2: B11.50 (D2), B11.58 (DB2)
SD3: B11.51 (D3), B11.59 (DB3)
SD4: B11.52 (D4), B11.60 (DB4)
SD5: B11.53 (D5), B11.61 (DB5)
SD6: B11.54 (D6), B11.62 (DB6)
SD7: B11.55 (D7), B11.63 (DB7)
SYNC: R8.2
VA0: A2.13 (B5), A5.10 (A0), D8.15 (A0)
VA1: A2.14 (B4), A5.9 (A1), D8.16 (A1)
VA2: A2.15 (B3), A5.8 (A2), D8.17 (A2)
VA3: A2.16 (B2), A5.7 (A3), D8.18 (A3)
VA4: A2.17 (B1), A5.6 (A4), D8.19 (A4)
VA5: A2.18 (B0), A5.5 (A5), D8.20 (A5)
VA6: A5.4 (A6), B2.11 (B7), D8.21 (A6)
VA7: A5.3 (A7), B2.12 (B6), D8.22 (A7)
VA8: A5.25 (A8), B2.13 (B5), D8.23 (A8)
VA9: A5.24 (A9), B2.14 (B4), D8.24 (A9)
VA10: A5.21 (A10), B2.15 (B3), D8.25 (A10)
VA11: A5.23 (A11), D8.28 (A11)
VA12: A5.2 (A12), H8.7 (Za)
VCC: A2.1 (A->B), A5.26 (CS2), A6.1 (~Mr), B2.1 (A->B), B6.1 (~Mr), B11.17 (VCC), B11.18 (VCC), B11.64 (VCC), BB12.42 (VCC), CC6.1 (EN), CC6.14 (Vcc), CC8.1 (VCC), CC8.33 (VCC), D8.1 (VCC), D8.33 (VCC), EE10.1 (~MR), EE10.3 (D0), EE10.4 (D1), EE10.5 (D2), EE10.6 (D3), EE10.7 (CEP), EE10.10 (CET), H8.16 (VCC), R1.2
VD0: A5.11 (D0), A6.18 (D7), CC3.11 (B7), D6.18 (D7), D8.14 (D0)
VD1: A5.12 (D1), A6.17 (D6), CC3.12 (B6), D6.17 (D6), D8.13 (D1)
VD2: A5.13 (D2), A6.14 (D5), CC3.13 (B5), D6.14 (D5), D8.12 (D2)
VD3: A5.15 (D3), A6.13 (D4), CC3.14 (B4), D6.13 (D4), D8.11 (D3)
VD4: A5.16 (D4), A6.8 (D3), CC3.15 (B3), D6.8 (D3), D8.10 (D4)
VD5: A5.17 (D5), A6.7 (D2), CC3.16 (B2), D6.7 (D2), D8.9 (D5)
VD6: A5.18 (D6), A6.4 (D1), B2.3 (A1), CC3.17 (B1), D6.4 (D1), D8.8 (D6)
VD7: A5.19 (D7), A6.3 (D0), B2.2 (A0), CC3.18 (B0), D6.3 (D0), D8.7 (D7)
VDB0: B6.14 (D5), D6.19 (O7), D8.4 (XC0)
VDB1: B6.13 (D4), D6.16 (O6)
VDB2: A2.12 (B6), B6.11 (D3), CC8.10 (UK), D6.15 (O5)
VDB3: B6.6 (D2), CC8.9 (PAL0), D6.12 (O4)
VDB4: B6.4 (D1), CC8.8 (PAL1), D6.9 (O3)
VDB5: B6.3 (D0), CC8.7 (PAL2), D6.6 (O2)
VDB6: B2.17 (B1), CC8.6 (PAL3), D6.5 (O1), D8.59 (FLIPY)
VDB7: B2.18 (B0), CC8.5 (PAL4/TRSP), D6.2 (O0), D8.60 (FLIPX)
~BGTRNSP: CC8.2 (~BGTRNSP)
~GROMEN: B6.5 (Q1)
~H4: D6.1 (~OE)
~HBLK2: D8.57 (~HBLK2)
~HBLK: D8.55 (~HBLK), F10.1
~MRD: CC3.1 (A->B), D8.2 (~RD), E6.1
~OBJORVRAMEN: D5.13
~OBJRAMCS: A5.20 (CS1)
~PALEN: B11.45 (~PALEN)
~SRD: B11.44 (~RD)
~SWR: B11.48 (D0)
~VBLK: BB12.24 (~VBLK), D8.58 (~VBLK)
~VRAMWR: D8.3 (~WR)
~VSYNC: BB12.23 (~VSYNC), D8.56 (~VSYNC)
~WDRES: D8.29 (~{WDRES)

Notes on the sheet:
To sub PCB connectors
pin nr 48 /WR is wrong, issue made in github. The correct number is 47.
A2 and B2 use a modified symbol with A inputs fixed as inputs in order to avoid DRC errors.
From sub PCB connectors
