skutis/jtbubl/cores/kiwi/sch/tnzs/io.kicad_sch

## KiCad design cores/kiwi/sch/tnzs/io.kicad_sch (2022-12-01)

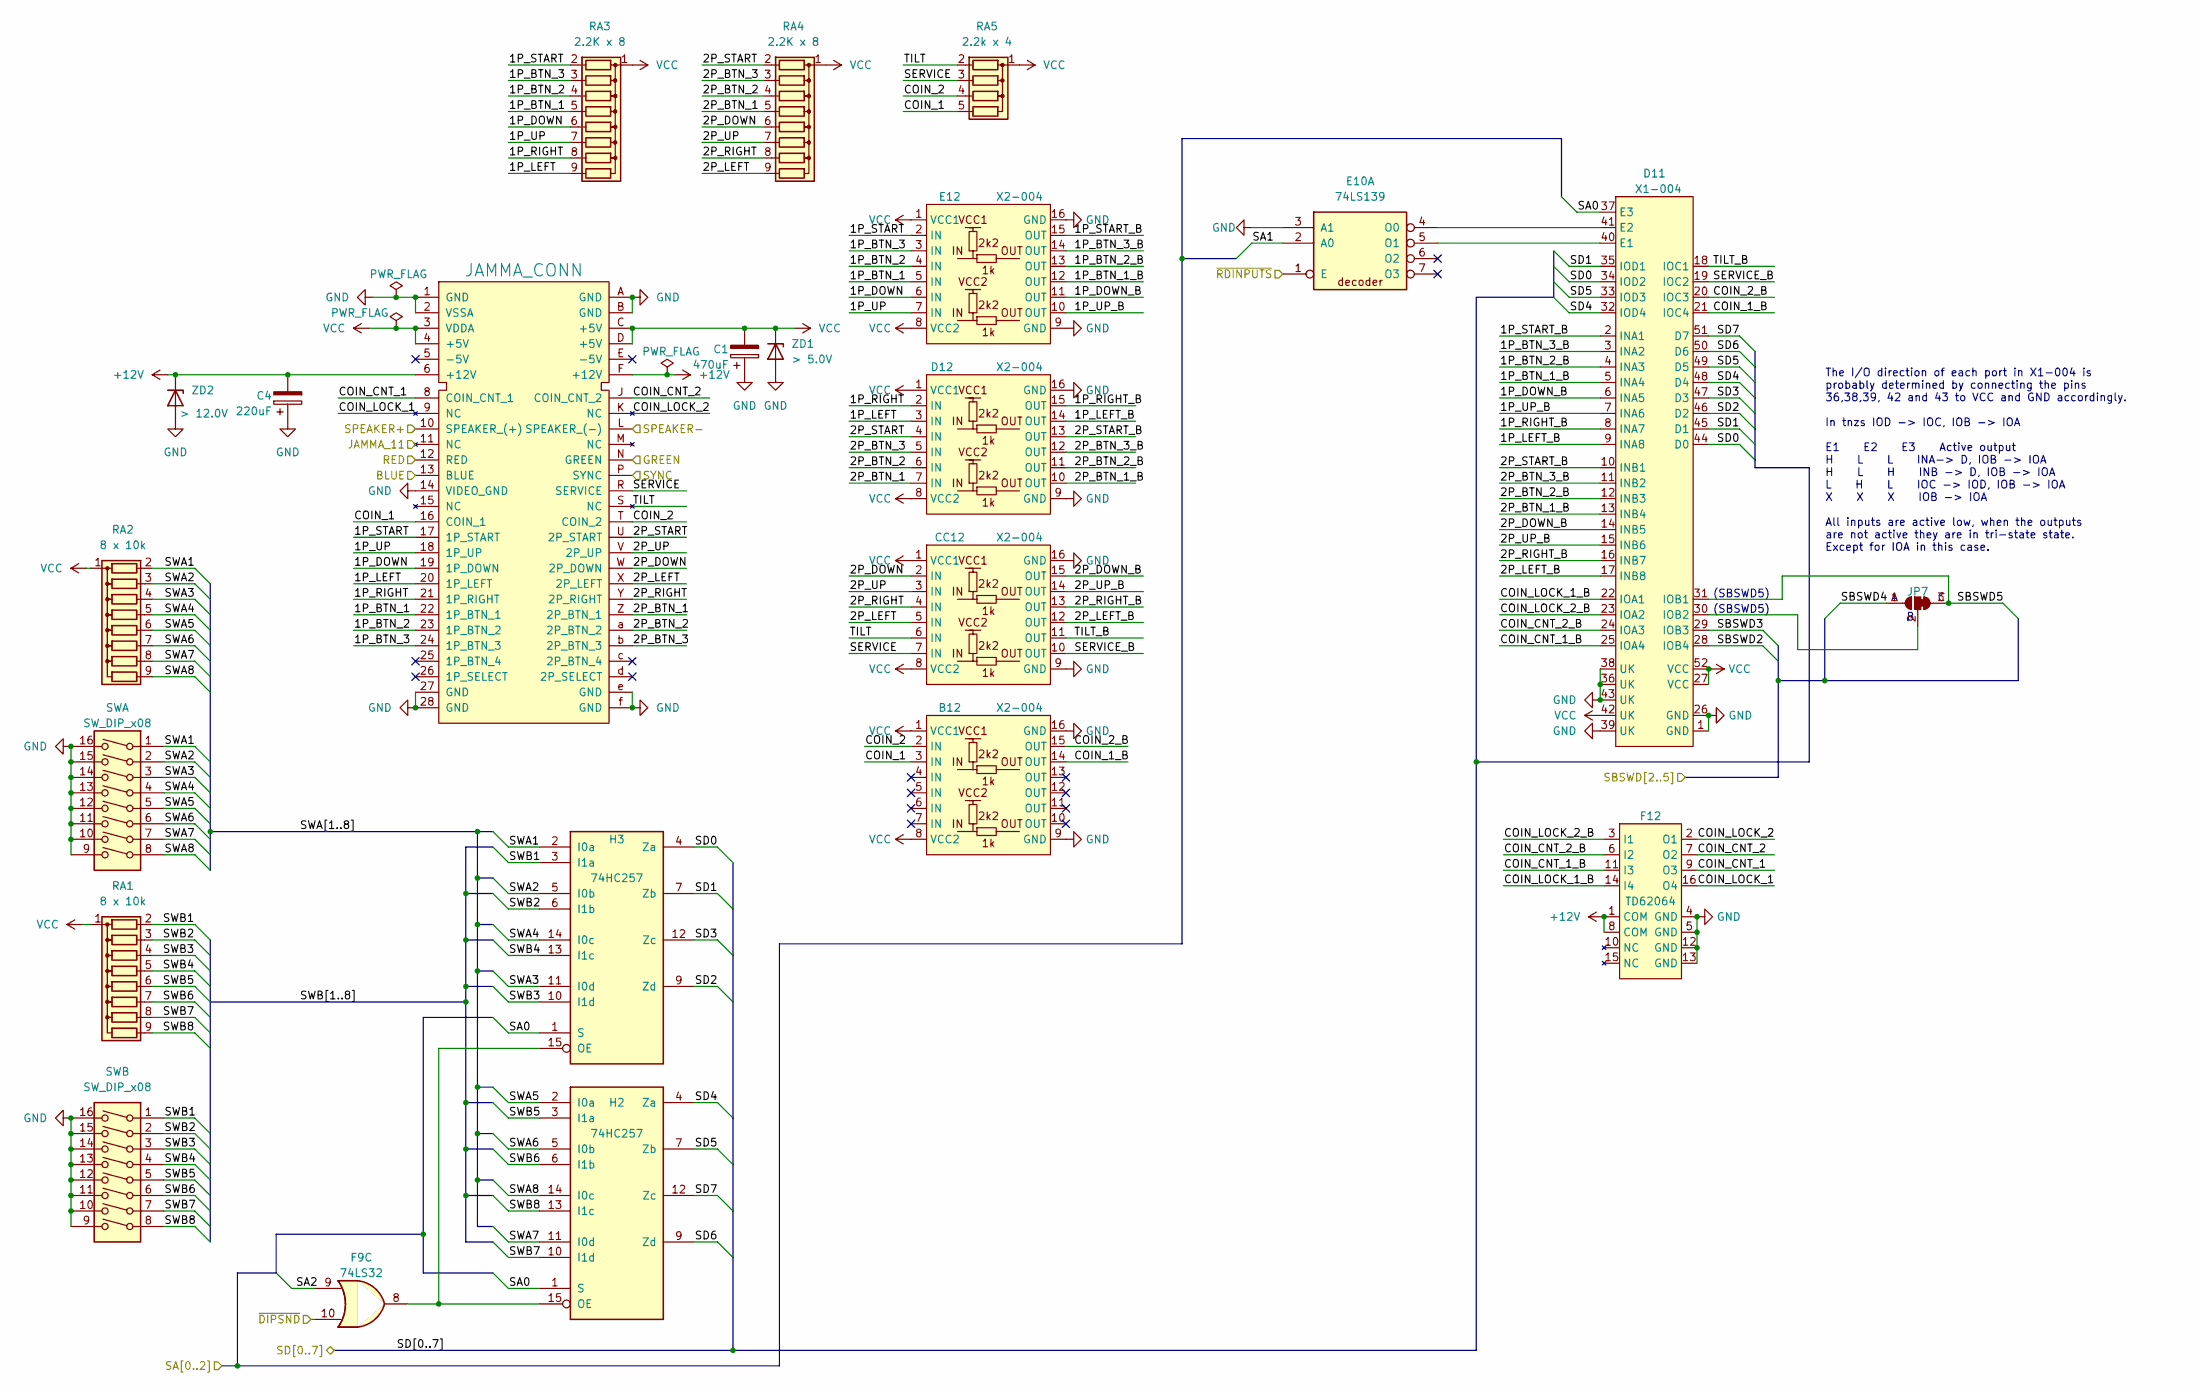
[picture p31: schematic io.kicad_sch]

Parts:
B12: X2-004
C1: 470uF
C4: 220uF
CC12: X2-004
D11: X1-004
D12: X2-004
E10: 74LS139
E12: X2-004
F9: 74LS32
F12: TD62064
H2, H3: 74HC257
JAMMA1: JAMMA_CONN
JP7: SolderJumper_3_Bridged23
RA1, RA2: 8 x 10k; R_Array_SIP9
RA3, RA4: 2.2K x 8; R_Array_SIP9
RA5: 2.2k x 4; R_Array_SIP5
SWA1: SW_DIP_x08
SWB1: SW_DIP_x08
ZD1: > 5.0V
ZD2: > 12.0V

Connections:
1P_BTN_1: E12.5 (IN), JAMMA1.22 (1P_BTN_1), RA3.5 (R4)
1P_BTN_1_B: D11.5 (INA4), E12.12 (OUT)
1P_BTN_2: E12.4 (IN), JAMMA1.23 (1P_BTN_2), RA3.4 (R3)
1P_BTN_2_B: D11.4 (INA3), E12.13 (OUT)
1P_BTN_3: E12.3 (IN), JAMMA1.24 (1P_BTN_3), RA3.3 (R2)
1P_BTN_3_B: D11.3 (INA2), E12.14 (OUT)
1P_DOWN: E12.6 (IN), JAMMA1.19 (1P_DOWN), RA3.6 (R5)
1P_DOWN_B: D11.6 (INA5), E12.11 (OUT)
1P_LEFT: D12.3 (IN), JAMMA1.20 (1P_LEFT), RA3.9 (R8)
1P_LEFT_B: D11.9 (INA8), D12.14 (OUT)
1P_RIGHT: D12.2 (IN), JAMMA1.21 (1P_RIGHT), RA3.8 (R7)
1P_RIGHT_B: D11.8 (INA7), D12.15 (OUT)
1P_START: E12.2 (IN), JAMMA1.17 (1P_START), RA3.2 (R1)
1P_START_B: D11.2 (INA1), E12.15 (OUT)
1P_UP: E12.7 (IN), JAMMA1.18 (1P_UP), RA3.7 (R6)
1P_UP_B: D11.7 (INA6), E12.10 (OUT)
2P_BTN_1: D12.7 (IN), JAMMA1.Z (2P_BTN_1), RA4.5 (R4)
2P_BTN_1_B: D11.13 (INB4), D12.10 (OUT)
2P_BTN_2: D12.6 (IN), JAMMA1.a (2P_BTN_2), RA4.4 (R3)
2P_BTN_2_B: D11.12 (INB3), D12.11 (OUT)
2P_BTN_3: D12.5 (IN), JAMMA1.b (2P_BTN_3), RA4.3 (R2)
2P_BTN_3_B: D11.11 (INB2), D12.12 (OUT)
2P_DOWN: CC12.2 (IN), JAMMA1.W (2P_DOWN), RA4.6 (R5)
2P_DOWN_B: CC12.15 (OUT), D11.14 (INB5)
2P_LEFT: CC12.5 (IN), JAMMA1.X (2P_LEFT), RA4.9 (R8)
2P_LEFT_B: CC12.12 (OUT), D11.17 (INB8)
2P_RIGHT: CC12.4 (IN), JAMMA1.Y (2P_RIGHT), RA4.8 (R7)
2P_RIGHT_B: CC12.13 (OUT), D11.16 (INB7)
2P_START: D12.4 (IN), JAMMA1.U (2P_START), RA4.2 (R1)
2P_START_B: D11.10 (INB1), D12.13 (OUT)
2P_UP: CC12.3 (IN), JAMMA1.V (2P_UP), RA4.7 (R6)
2P_UP_B: CC12.14 (OUT), D11.15 (INB6)
+12V: C4.2, F12.1 (COM), F12.8 (COM), JAMMA1.6 (+12V), JAMMA1.F (+12V), ZD2.1 (K)
BLUE: JAMMA1.13 (BLUE)
COIN_1: B12.3 (IN), JAMMA1.16 (COIN_1), RA5.5 (R4)
COIN_1_B: B12.14 (OUT), D11.21 (IOC4)
COIN_2: B12.2 (IN), JAMMA1.T (COIN_2), RA5.4 (R3)
COIN_2_B: B12.15 (OUT), D11.20 (IOC3)
COIN_CNT_1: F12.9 (O3), JAMMA1.8 (COIN_CNT_1)
COIN_CNT_1_B: D11.25 (IOA4), F12.11 (I3)
COIN_CNT_2: F12.7 (O2), JAMMA1.J (COIN_CNT_2)
COIN_CNT_2_B: D11.24 (IOA3), F12.6 (I2)
COIN_LOCK_1: F12.16 (O4), JAMMA1.9 (NC)
COIN_LOCK_1_B: D11.22 (IOA1), F12.14 (I4)
COIN_LOCK_2: F12.2 (O1), JAMMA1.K (NC)
COIN_LOCK_2_B: D11.23 (IOA2), F12.3 (I1)
GND: B12.9 (GND), B12.16 (GND), C1.1, C4.1, CC12.9 (GND), CC12.16 (GND), D11.1 (GND), D11.26 (GND), D11.36 (UK), D11.38 (UK), D11.39 (UK), D11.43 (UK), D12.9 (GND), D12.16 (GND), E10.3 (A1), E12.9 (GND), E12.16 (GND), F12.4 (GND), F12.5 (GND), F12.12 (GND), F12.13 (GND), JAMMA1.1 (GND), JAMMA1.2 (VSSA), JAMMA1.14 (VIDEO_GND), JAMMA1.27 (GND), JAMMA1.28 (GND), JAMMA1.A (GND), JAMMA1.B (GND), JAMMA1.e (GND), JAMMA1.f (GND), SWA1.9, SWA1.10, SWA1.11, SWA1.12, SWA1.13, SWA1.14, SWA1.15, SWA1.16, SWB1.9, SWB1.10, SWB1.11, SWB1.12, SWB1.13, SWB1.14, SWB1.15, SWB1.16, ZD1.2 (A), ZD2.2 (A)
GREEN: JAMMA1.N (GREEN)
JAMMA_11: JAMMA1.11 (NC)
unnamed: D11.30 (IOB2), JP7.2 (C)
unnamed: D11.40 (E1), E10.5 (O1)
unnamed: D11.41 (E2), E10.4 (O0)
unnamed: F9.8, H2.15 (OE), H3.15 (OE)
RED: JAMMA1.12 (RED)
SA0: D11.37 (E3), H2.1 (S), H3.1 (S)
SA1: E10.2 (A0)
SA2: F9.9
SBSWD2: D11.28 (IOB4)
SBSWD3: D11.29 (IOB3)
SBSWD4: JP7.1 (A)
SBSWD5: D11.31 (IOB1), JP7.3 (B)
SD0: D11.34 (IOD2), D11.44 (D0), H3.4 (Za)
SD1: D11.35 (IOD1), D11.45 (D1), H3.7 (Zb)
SD2: D11.46 (D2), H3.9 (Zd)
SD3: D11.47 (D3), H3.12 (Zc)
SD4: D11.32 (IOD4), D11.48 (D4), H2.4 (Za)
SD5: D11.33 (IOD3), D11.49 (D5), H2.7 (Zb)
SD6: D11.50 (D6), H2.9 (Zd)
SD7: D11.51 (D7), H2.12 (Zc)
SERVICE: CC12.7 (IN), JAMMA1.R (SERVICE), RA5.3 (R2)
SERVICE_B: CC12.10 (OUT), D11.19 (IOC2)
SPEAKER+: JAMMA1.10 (SPEAKER_(+))
SPEAKER-: JAMMA1.L (SPEAKER_(-))
SWA1: H3.2 (I0a), RA2.2 (R1), SWA1.1
SWA2: H3.5 (I0b), RA2.3 (R2), SWA1.2
SWA3: H3.11 (I0d), RA2.4 (R3), SWA1.3
SWA4: H3.14 (I0c), RA2.5 (R4), SWA1.4
SWA5: H2.2 (I0a), RA2.6 (R5), SWA1.5
SWA6: H2.5 (I0b), RA2.7 (R6), SWA1.6
SWA7: H2.11 (I0d), RA2.8 (R7), SWA1.7
SWA8: H2.14 (I0c), RA2.9 (R8), SWA1.8
SWB1: H3.3 (I1a), RA1.2 (R1), SWB1.1
SWB2: H3.6 (I1b), RA1.3 (R2), SWB1.2
SWB3: H3.10 (I1d), RA1.4 (R3), SWB1.3
SWB4: H3.13 (I1c), RA1.5 (R4), SWB1.4
SWB5: H2.3 (I1a), RA1.6 (R5), SWB1.5
SWB6: H2.6 (I1b), RA1.7 (R6), SWB1.6
SWB7: H2.10 (I1d), RA1.8 (R7), SWB1.7
SWB8: H2.13 (I1c), RA1.9 (R8), SWB1.8
SYNC: JAMMA1.P (SYNC)
TILT: CC12.6 (IN), JAMMA1.S (NC), RA5.2 (R1)
TILT_B: CC12.11 (OUT), D11.18 (IOC1)
VCC: B12.1 (VCC1), B12.8 (VCC2), C1.2, CC12.1 (VCC1), CC12.8 (VCC2), D11.27 (VCC), D11.42 (UK), D11.52 (VCC), D12.1 (VCC1), D12.8 (VCC2), E12.1 (VCC1), E12.8 (VCC2), JAMMA1.3 (VDDA), JAMMA1.4 (+5V), JAMMA1.C (+5V), JAMMA1.D (+5V), RA1.1 (common), RA2.1 (common), RA3.1 (common), RA4.1 (common), RA5.1 (common), ZD1.1 (K)
~DIPSND: F9.10
~RDINPUTS: E10.1 (E)

Notes on the sheet:
(SBSWD5)
The I/O direction of each port in X1-004 is probably determined by connecting the pins 36,38,39, 42 and 43 to VCC and GND accordingly. In tnzs IOD -> IOC, IOB -> IOA E1 E2 E3 Active output H L L INA-> D, IOB -> IOA H L H INB -> D, IOB -> IOA L H L IOC -> IOD, IOB -> IOA X X X IOB -> IOA All inputs 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
