skutis/jtbubl/cores/kiwi/sch/tnzs/misc.kicad_sch

## KiCad design cores/kiwi/sch/tnzs/misc.kicad_sch (2022-12-01)

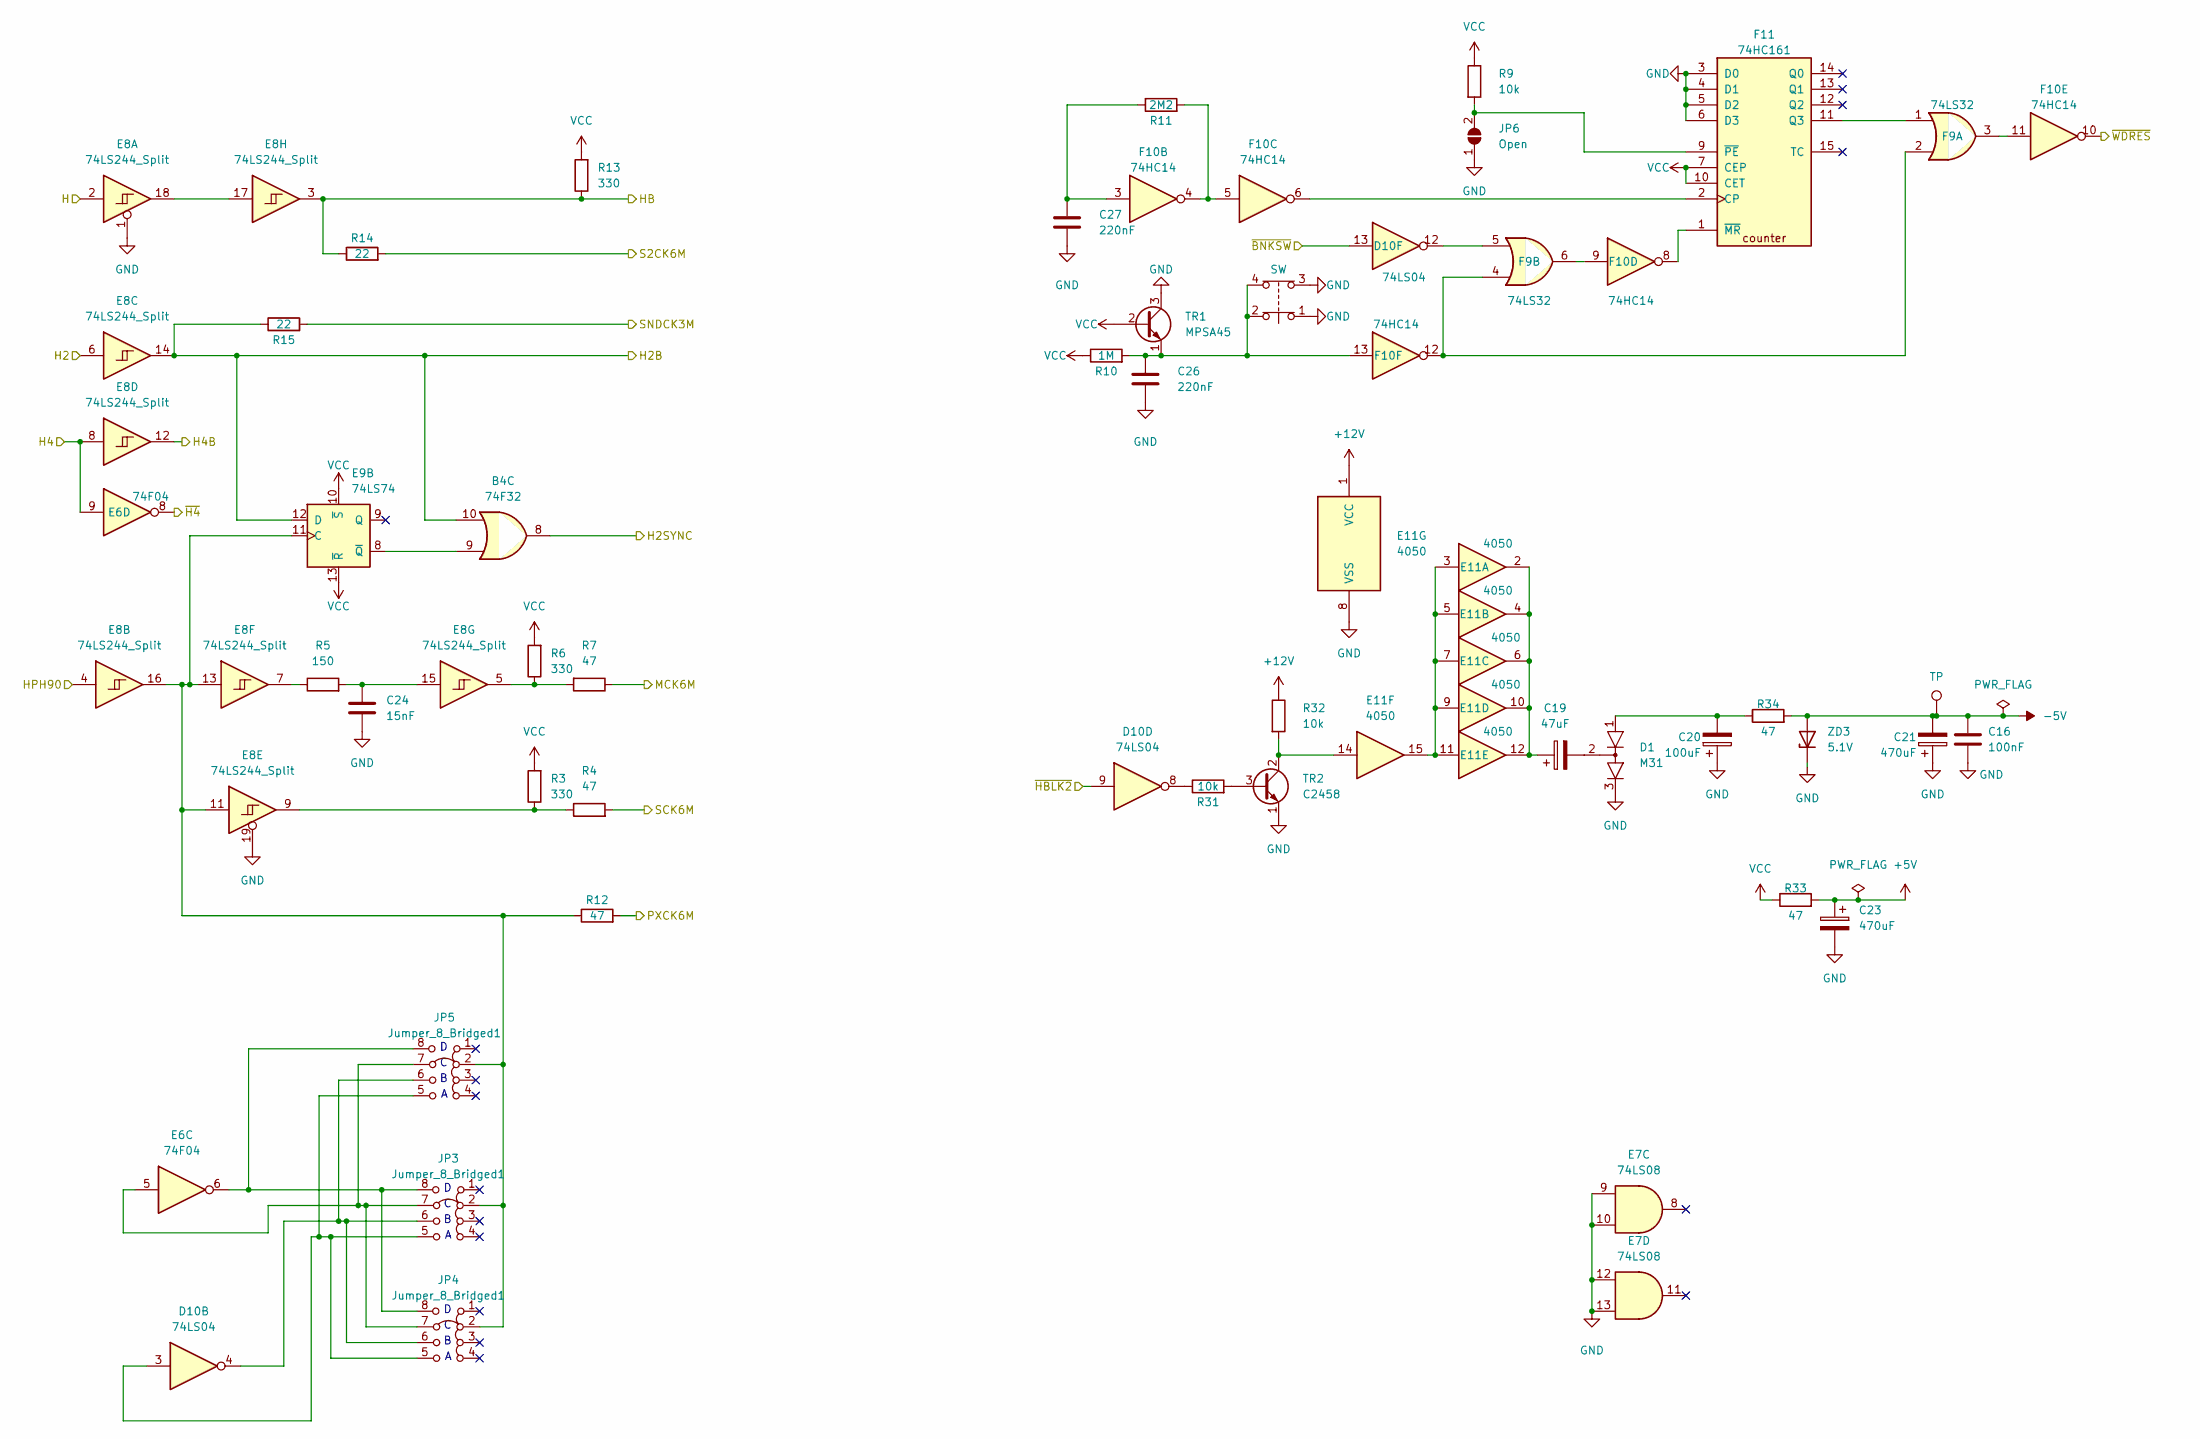
[picture p32: schematic misc.kicad_sch]

Parts:
B4: 74F32
C16: 100nF
C19: 47uF
C20: 100uF
C21, C23: 470uF
C24: 15nF
C26, C27: 220nF
D1: M31
D10: 74LS04
E6: 74F04
E7: 74LS08
E8: 74LS244_Split
E9: 74LS74
E11: 4050
F9: 74LS32
F10: 74HC14
F11: 74HC161
JP3, JP4, JP5: Jumper_8_Bridged1
JP6: Open
R3, R6, R13: 330
R4, R7, R12, R33, R34: 47
R5: 150
R9, R31, R32: 10k
R10: 1M
R11: 2M2
R14, R15: 22
SW1: SW_Push_Open_Dual
TP1: TestPoint
TR1: MPSA45
TR2: C2458
ZD3: 5.1V

Connections:
+5V: C23.1, R33.2
+12V: E11.1 (VCC), R32.1
-5V: C16.1, C21.2, R34.2, TP1.1, ZD3.2 (A)
GND: C16.2, C20.1, C21.1, C23.2, C24.2, C26.2, C27.2, D1.3, E7.9, E7.10, E7.12, E7.13, E8.1, E8.19, E11.8 (VSS), F11.3 (D0), F11.4 (D1), F11.5 (D2), F11.6 (D3), JP6.1 (A), SW1.1, SW1.3, TR1.3 (C), TR2.1 (E), ZD3.1 (K)
H: E8.2
H2: E8.6
H2B: B4.10, E8.14, E9.12 (D), R15.1
H2SYNC: B4.8
H4: E6.9, E8.8
H4B: E8.12
HB: E8.3, R13.1, R14.1
HPH90: E8.4
MCK6M: R7.1
unnamed: B4.9, E9.8 (~Q)
unnamed: C19.1, E11.2, E11.4, E11.6, E11.10, E11.12
unnamed: C19.2, D1.2
unnamed: C20.2, D1.1, R34.1
unnamed: C24.1, E8.15, R5.2
unnamed: C26.1, F10.13, R10.2, SW1.2, SW1.4, TR1.1 (E)
unnamed: C27.1, F10.3, R11.1
unnamed: D10.3, JP3.5 (B), JP4.5 (B), JP5.5 (B)
unnamed: D10.4, JP3.6 (B), JP4.6 (B), JP5.6 (B)
unnamed: D10.8, R31.1
unnamed: D10.12, F9.5
unnamed: E6.5, JP3.7 (B), JP4.7 (B), JP5.7 (B)
unnamed: E6.6, JP3.8 (B), JP4.8 (B), JP5.8 (B)
unnamed: E8.5, R6.1, R7.2
unnamed: E8.7, R5.1
unnamed: E8.9, R3.1, R4.1
unnamed: E8.11, E8.13, E8.16, E9.11 (C), JP3.2 (B), JP4.2 (B), JP5.2 (B), R12.1
unnamed: E8.17, E8.18
unnamed: E11.3, E11.5, E11.7, E11.9, E11.11, E11.15
unnamed: E11.14, R32.2, TR2.2 (C)
unnamed: F10.4, F10.5, R11.2
unnamed: F10.6, F11.2 (CP)
unnamed: F10.8, F11.1 (~MR)
unnamed: F9.6, F10.9
unnamed: F9.3, F10.11
unnamed: F9.2, F9.4, F10.12
unnamed: F11.9 (~PE), JP6.2 (B), R9.2
unnamed: F9.1, F11.11 (Q3)
unnamed: R31.2, TR2.3 (B)
PXCK6M: R12.2
S2CK6M: R14.2
SCK6M: R4.2
SNDCK3M: R15.2
VCC: E9.10 (~S), E9.13 (~R), F11.7 (CEP), F11.10 (CET), R3.2, R6.2, R9.1, R10.1, R13.2, R33.1, TR1.2 (B)
~BNKSW: D10.13
~H4: E6.8
~HBLK2: D10.9
~WDRES: F10.10
