skutis/jtbubl/cores/kiwi/sch/tnzs/sound.kicad_sch

## KiCad design cores/kiwi/sch/tnzs/sound.kicad_sch (2022-12-01)

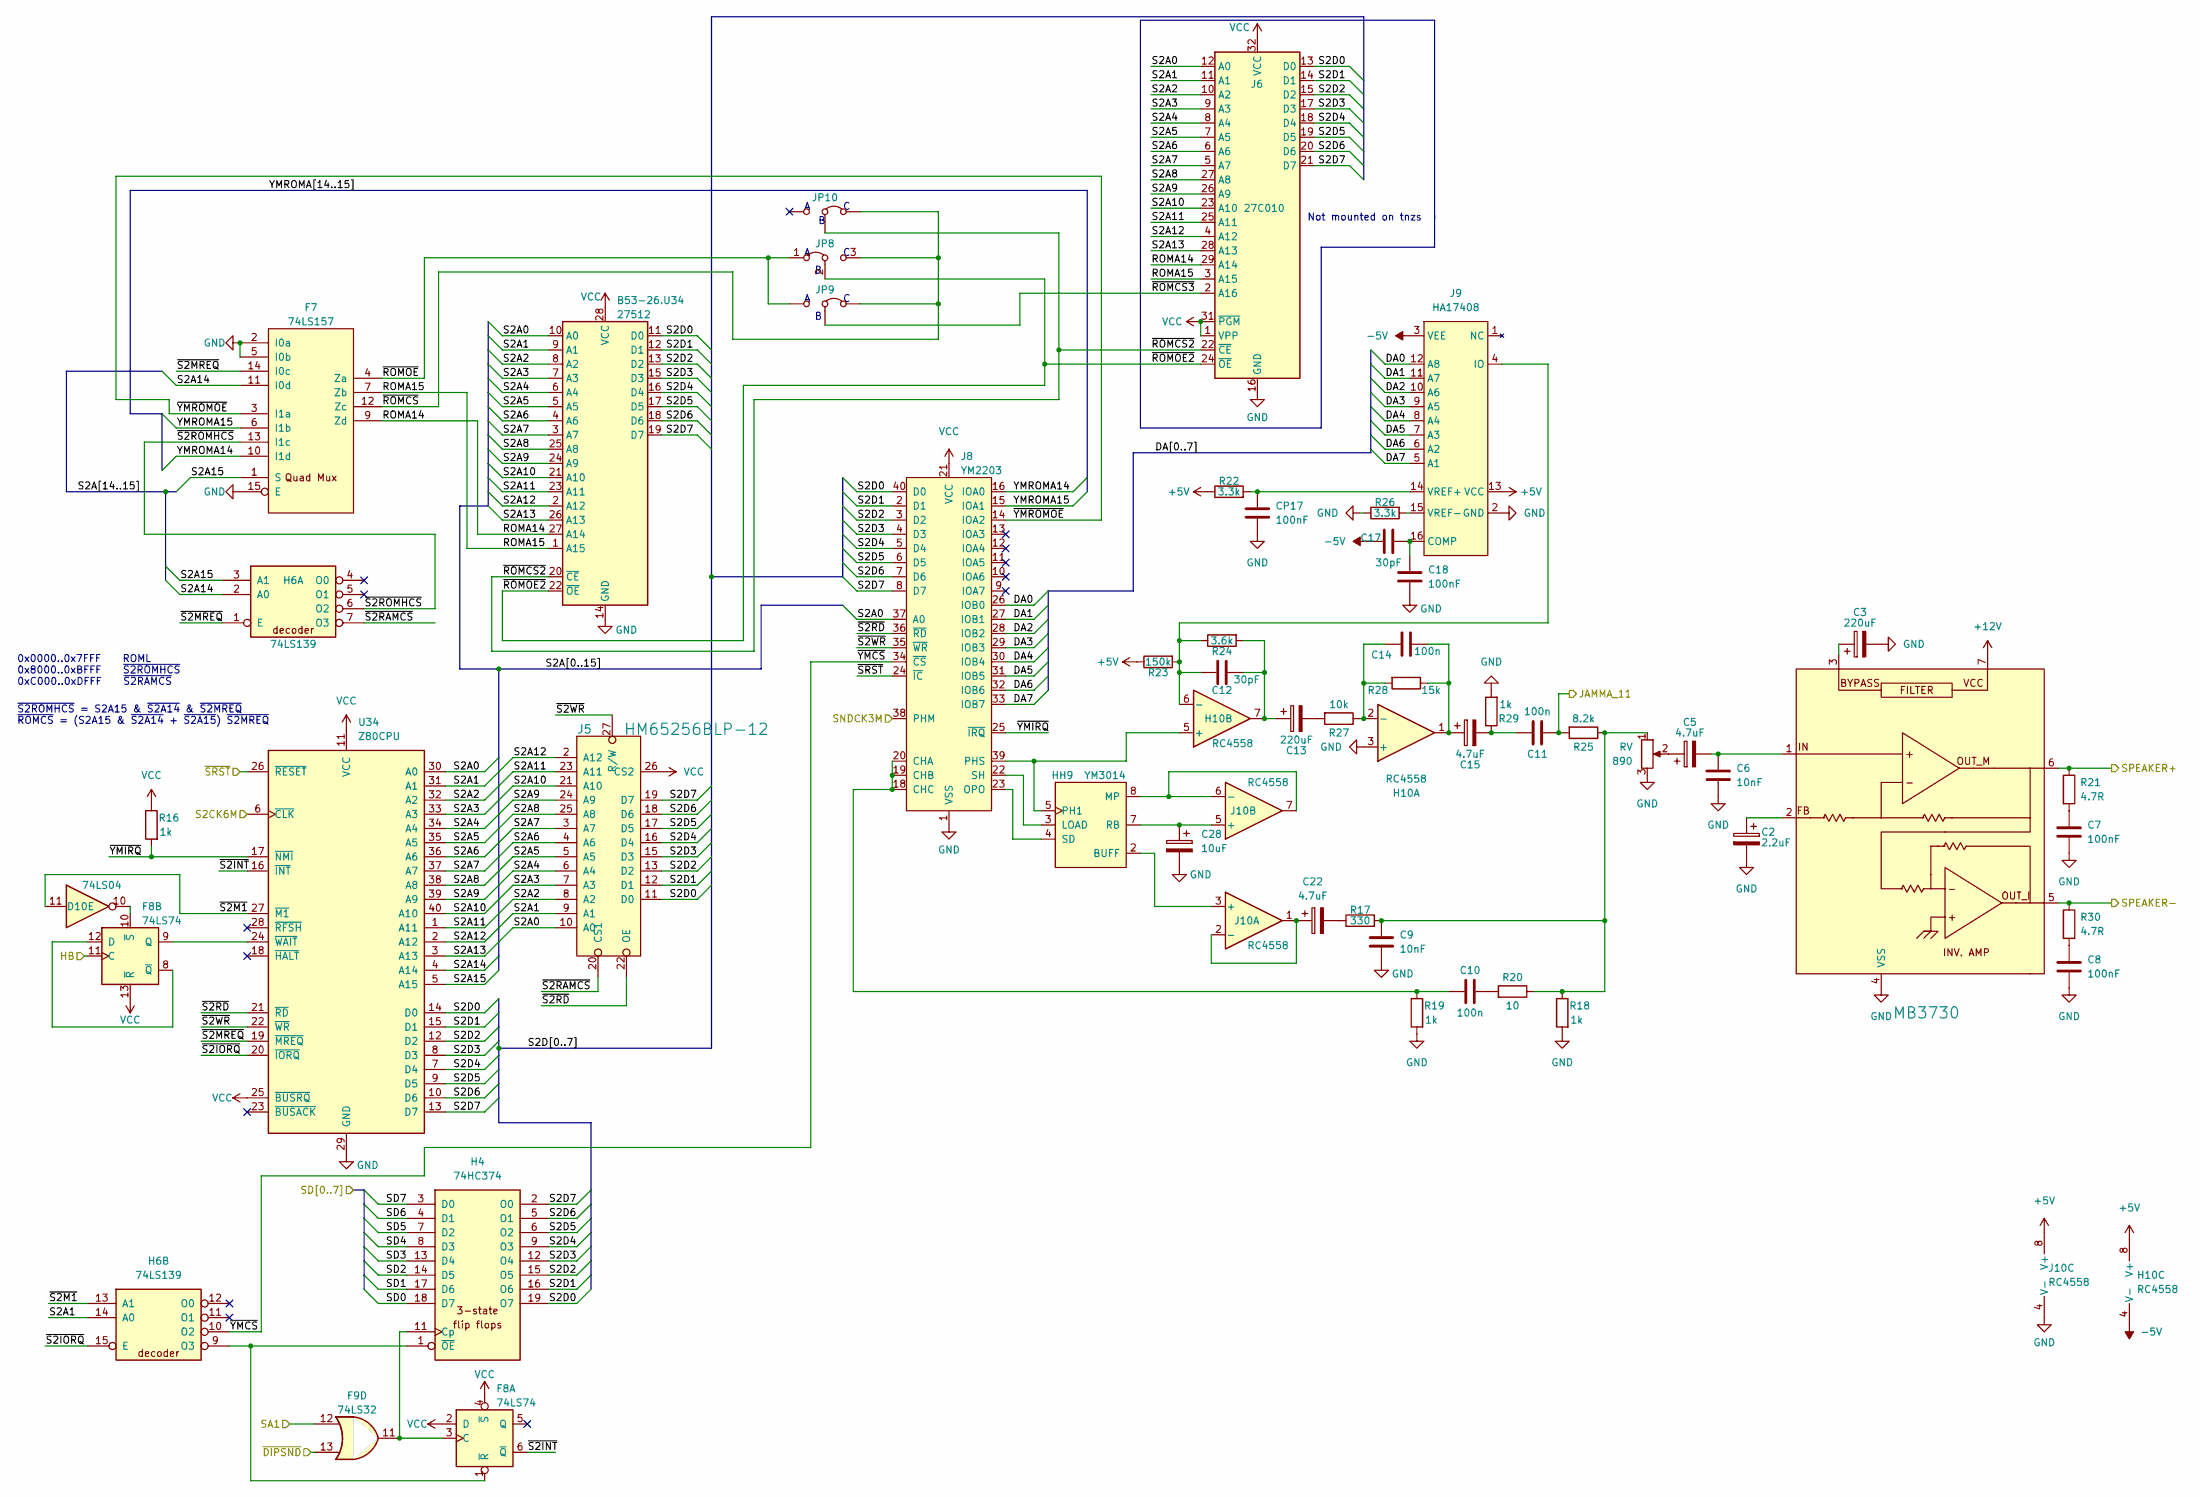
[picture p33: schematic sound.kicad_sch]

Parts:
B53-26.U34: 27512; DIP-28_W15.24mm
C2: 2.2uF
C3, C13: 220uF
C5, C15, C22: 4.7uF
C6, C9: 10nF
C7, C8, C18: 100nF
C10, C11, C14: 100n
C12, C17: 30pF
C28: 10uF
CP17: 100nF
D10: 74LS04
F7: 74LS157
F8: 74LS74
F9: 74LS32
H4: 74HC374
H6: 74LS139
H10: RC4558
HH9: YM3014; DIP-8_W7.62mm
J5: HM65256BLP-12
J6: 27C010
J8: YM2203; DIP-40_W15.24mm
J9: HA17408
J10: RC4558
J12: MB3730
JP8: Jumper_3_Bridged12
JP9, JP10: Jumper_3_Bridged23
R16, R18, R19, R29: 1k
R17: 330
R20: 10
R21, R30: 4.7R
R22, R26: 3.3k
R23: 150k
R24: 3.6k
R25: 8.2k
R27: 10k
R28: 15k
RV1: 890
U34: Z80CPU

Connections:
+5V: H10.8 (V+), J9.13 (VCC), J10.8 (V+), R22.1, R23.1
+12V: J12.7
-5V: C17.1, H10.4 (V-), J9.3 (VEE)
DA0: J8.26 (IOB0), J9.12 (A8)
DA1: J8.27 (IOB1), J9.11 (A7)
DA2: J8.28 (IOB2), J9.10 (A6)
DA3: J8.29 (IOB3), J9.9 (A5)
DA4: J8.30 (IOB4), J9.8 (A4)
DA5: J8.31 (IOB5), J9.7 (A3)
DA6: J8.32 (IOB6), J9.6 (A2)
DA7: J8.33 (IOB7), J9.5 (A1)
GND: B53-26.U34.14 (GND), C2.2, C3.2, C6.2, C7.2, C8.2, C9.2, C18.2, C28.2, CP17.2, F7.2 (I0a), F7.5 (I0b), F7.15 (E), H10.3 (+), J6.16 (GND), J8.1 (VSS), J9.2 (GND), J10.4 (V-), J12.4 (VSS), R18.2, R19.2, R26.1, R29.2, RV1.3, U34.29 (GND)
HB: F8.11 (C)
JAMMA_11: C11.1, R25.2
unnamed: C2.1, J12.2
unnamed: C3.1, J12.3
unnamed: C5.1, RV1.2
unnamed: C5.2, C6.1, J12.1
unnamed: C7.1, R21.2
unnamed: C8.1, R30.2
unnamed: C9.1, R17.2, R18.1, R20.1, R25.1, RV1.1
unnamed: C10.1, R20.2
unnamed: C10.2, J8.18 (CHC), J8.19 (CHB), J8.20 (CHA), R19.1
unnamed: C11.2, C15.2, R29.1
unnamed: C12.1, H10.6 (-), J9.4 (IO), R23.2, R24.1
unnamed: C12.2, C13.1, H10.7, R24.2
unnamed: C13.2, R27.2
unnamed: C14.1, C15.1, H10.1, R28.1
unnamed: C14.2, H10.2 (-), R27.1, R28.2
unnamed: C17.2, C18.1, J9.16 (COMP)
unnamed: C22.1, J10.1, J10.2 (-)
unnamed: C22.2, R17.1
unnamed: C28.1, HH9.7 (RB), J10.5 (+)
unnamed: CP17.1, J9.14 (VREF+), R22.2
unnamed: D10.10, F8.10 (~S)
unnamed: F8.1 (~R), H4.1 (~OE), H6.9 (O3)
unnamed: F8.3 (C), F9.11, H4.11 (Cp)
unnamed: F8.9 (Q), U34.24 (~WAIT)
unnamed: F8.8 (~Q), F8.12 (D)
unnamed: H10.5 (+), HH9.5 (PH1), J8.39 (PHS)
unnamed: HH9.2 (BUFF), J10.3 (+)
unnamed: HH9.3 (LOAD), J8.22 (SH)
unnamed: HH9.4 (SD), J8.23 (OPO)
unnamed: HH9.8 (MP), J10.6 (-), J10.7
unnamed: J9.15 (VREF-), R26.2
ROMA14: B53-26.U34.27 (A14), F7.9 (Zd), J6.29 (A14)
ROMA15: B53-26.U34.1 (A15), F7.7 (Zb), J6.3 (A15)
S2A0: B53-26.U34.10 (A0), J5.10 (A0), J6.12 (A0), J8.37 (A0), U34.30 (A0)
S2A1: B53-26.U34.9 (A1), H6.14 (A0), J5.9 (A1), J6.11 (A1), U34.31 (A1)
S2A2: B53-26.U34.8 (A2), J5.8 (A2), J6.10 (A2), U34.32 (A2)
S2A3: B53-26.U34.7 (A3), J5.7 (A3), J6.9 (A3), U34.33 (A3)
S2A4: B53-26.U34.6 (A4), J5.6 (A4), J6.8 (A4), U34.34 (A4)
S2A5: B53-26.U34.5 (A5), J5.5 (A5), J6.7 (A5), U34.35 (A5)
S2A6: B53-26.U34.4 (A6), J5.4 (A6), J6.6 (A6), U34.36 (A6)
S2A7: B53-26.U34.3 (A7), J5.3 (A7), J6.5 (A7), U34.37 (A7)
S2A8: B53-26.U34.25 (A8), J5.25 (A8), J6.27 (A8), U34.38 (A8)
S2A9: B53-26.U34.24 (A9), J5.24 (A9), J6.26 (A9), U34.39 (A9)
S2A10: B53-26.U34.21 (A10), J5.21 (A10), J6.23 (A10), U34.40 (A10)
S2A11: B53-26.U34.23 (A11), J5.23 (A11), J6.25 (A11), U34.1 (A11)
S2A12: B53-26.U34.2 (A12), J5.2 (A12), J6.4 (A12), U34.2 (A12)
S2A13: B53-26.U34.26 (A13), J6.28 (A13), U34.3 (A13)
S2A14: F7.11 (I0d), H6.2 (A0), U34.4 (A14)
S2A15: F7.1 (S), H6.3 (A1), U34.5 (A15)
S2CK6M: U34.6 (~CLK)
S2D0: B53-26.U34.11 (D0), H4.19 (O7), J5.11 (D0), J6.13 (D0), J8.40 (D0), U34.14 (D0)
S2D1: B53-26.U34.12 (D1), H4.16 (O6), J5.12 (D1), J6.14 (D1), J8.2 (D1), U34.15 (D1)
S2D2: B53-26.U34.13 (D2), H4.15 (O5), J5.13 (D2), J6.15 (D2), J8.3 (D2), U34.12 (D2)
S2D3: B53-26.U34.15 (D3), H4.12 (O4), J5.15 (D3), J6.17 (D3), J8.4 (D3), U34.8 (D3)
S2D4: B53-26.U34.16 (D4), H4.9 (O3), J5.16 (D4), J6.18 (D4), J8.5 (D4), U34.7 (D4)
S2D5: B53-26.U34.17 (D5), H4.6 (O2), J5.17 (D5), J6.19 (D5), J8.6 (D5), U34.9 (D5)
S2D6: B53-26.U34.18 (D6), H4.5 (O1), J5.18 (D6), J6.20 (D6), J8.7 (D6), U34.10 (D6)
S2D7: B53-26.U34.19 (D7), H4.2 (O0), J5.19 (D7), J6.21 (D7), J8.8 (D7), U34.13 (D7)
SA1: F9.12
SD0: H4.18 (D7)
SD1: H4.17 (D6)
SD2: H4.14 (D5)
SD3: H4.13 (D4)
SD4: H4.8 (D3)
SD5: H4.7 (D2)
SD6: H4.4 (D1)
SD7: H4.3 (D0)
SNDCK3M: J8.38 (PHM)
SPEAKER+: J12.6, R21.1
SPEAKER-: J12.5, R30.1
VCC: B53-26.U34.28 (VCC), F8.2 (D), F8.4 (~S), F8.13 (~R), J5.26 (CS2), J6.1 (VPP), J6.31 (~PGM), J6.32 (VCC), J8.21 (VCC), R16.1, U34.11 (VCC), U34.25 (~BUSRQ)
YMROMA14: F7.10 (I1d), J8.16 (IOA0)
YMROMA15: F7.6 (I1b), J8.15 (IOA1)
~DIPSND: F9.13
~ROMCS2: B53-26.U34.20 (~CE), J6.22 (~CE), JP10.2 (C)
~ROMCS3: J6.2 (A16), JP9.2 (C)
~ROMCS: F7.12 (Zc), JP8.3 (B), JP9.3 (B), JP10.3 (B)
~ROMOE2: B53-26.U34.22 (~OE), J6.24 (~OE), JP8.2 (C)
~ROMOE: F7.4 (Za), JP8.1 (A), JP9.1 (A)
~S2INT: F8.6 (~Q), U34.16 (~INT)
~S2IORQ: H6.15 (E), U34.20 (~IORQ)
~S2M1: D10.11, H6.13 (A1), U34.27 (~M1)
~S2MREQ: F7.14 (I0c), H6.1 (E), U34.19 (~MREQ)
~S2RAMCS: H6.7 (O3), J5.20 (CS1)
~S2RD: J5.22 (OE), J8.36 (~RD), U34.21 (~RD)
~S2ROMHCS: F7.13 (I1c), H6.6 (O2)
~S2WR: J5.27 (R/W), J8.35 (~WR), U34.22 (~WR)
~SRST: J8.24 (~IC), U34.26 (~RESET)
~YMCS: H6.10 (O2), J8.34 (~CS)
~YMIRQ: J8.25 (~IRQ), R16.2, U34.17 (~NMI)
~YMROMOE: F7.3 (I1a), J8.14 (IOA2)

Notes on the sheet:
0x0000..0x7FFF ROML 0x8000..0xBFFF ~{S2ROMHCS} 0xC000..0xDFFF ~{S2RAMCS}
~{S2ROMHCS} = S2A15 & ~{S2A14} & ~{S2MREQ} ~{ROMCS} = (S2A15 & ~{S2A14} + ~{S2A15}) ~{S2MREQ}
Not mounted on tnzs
