skutis/jtbubl/cores/kiwi/sch/tnzs/sub_pcb.kicad_sch

## KiCad design cores/kiwi/sch/tnzs/sub_pcb.kicad_sch (2022-12-01)

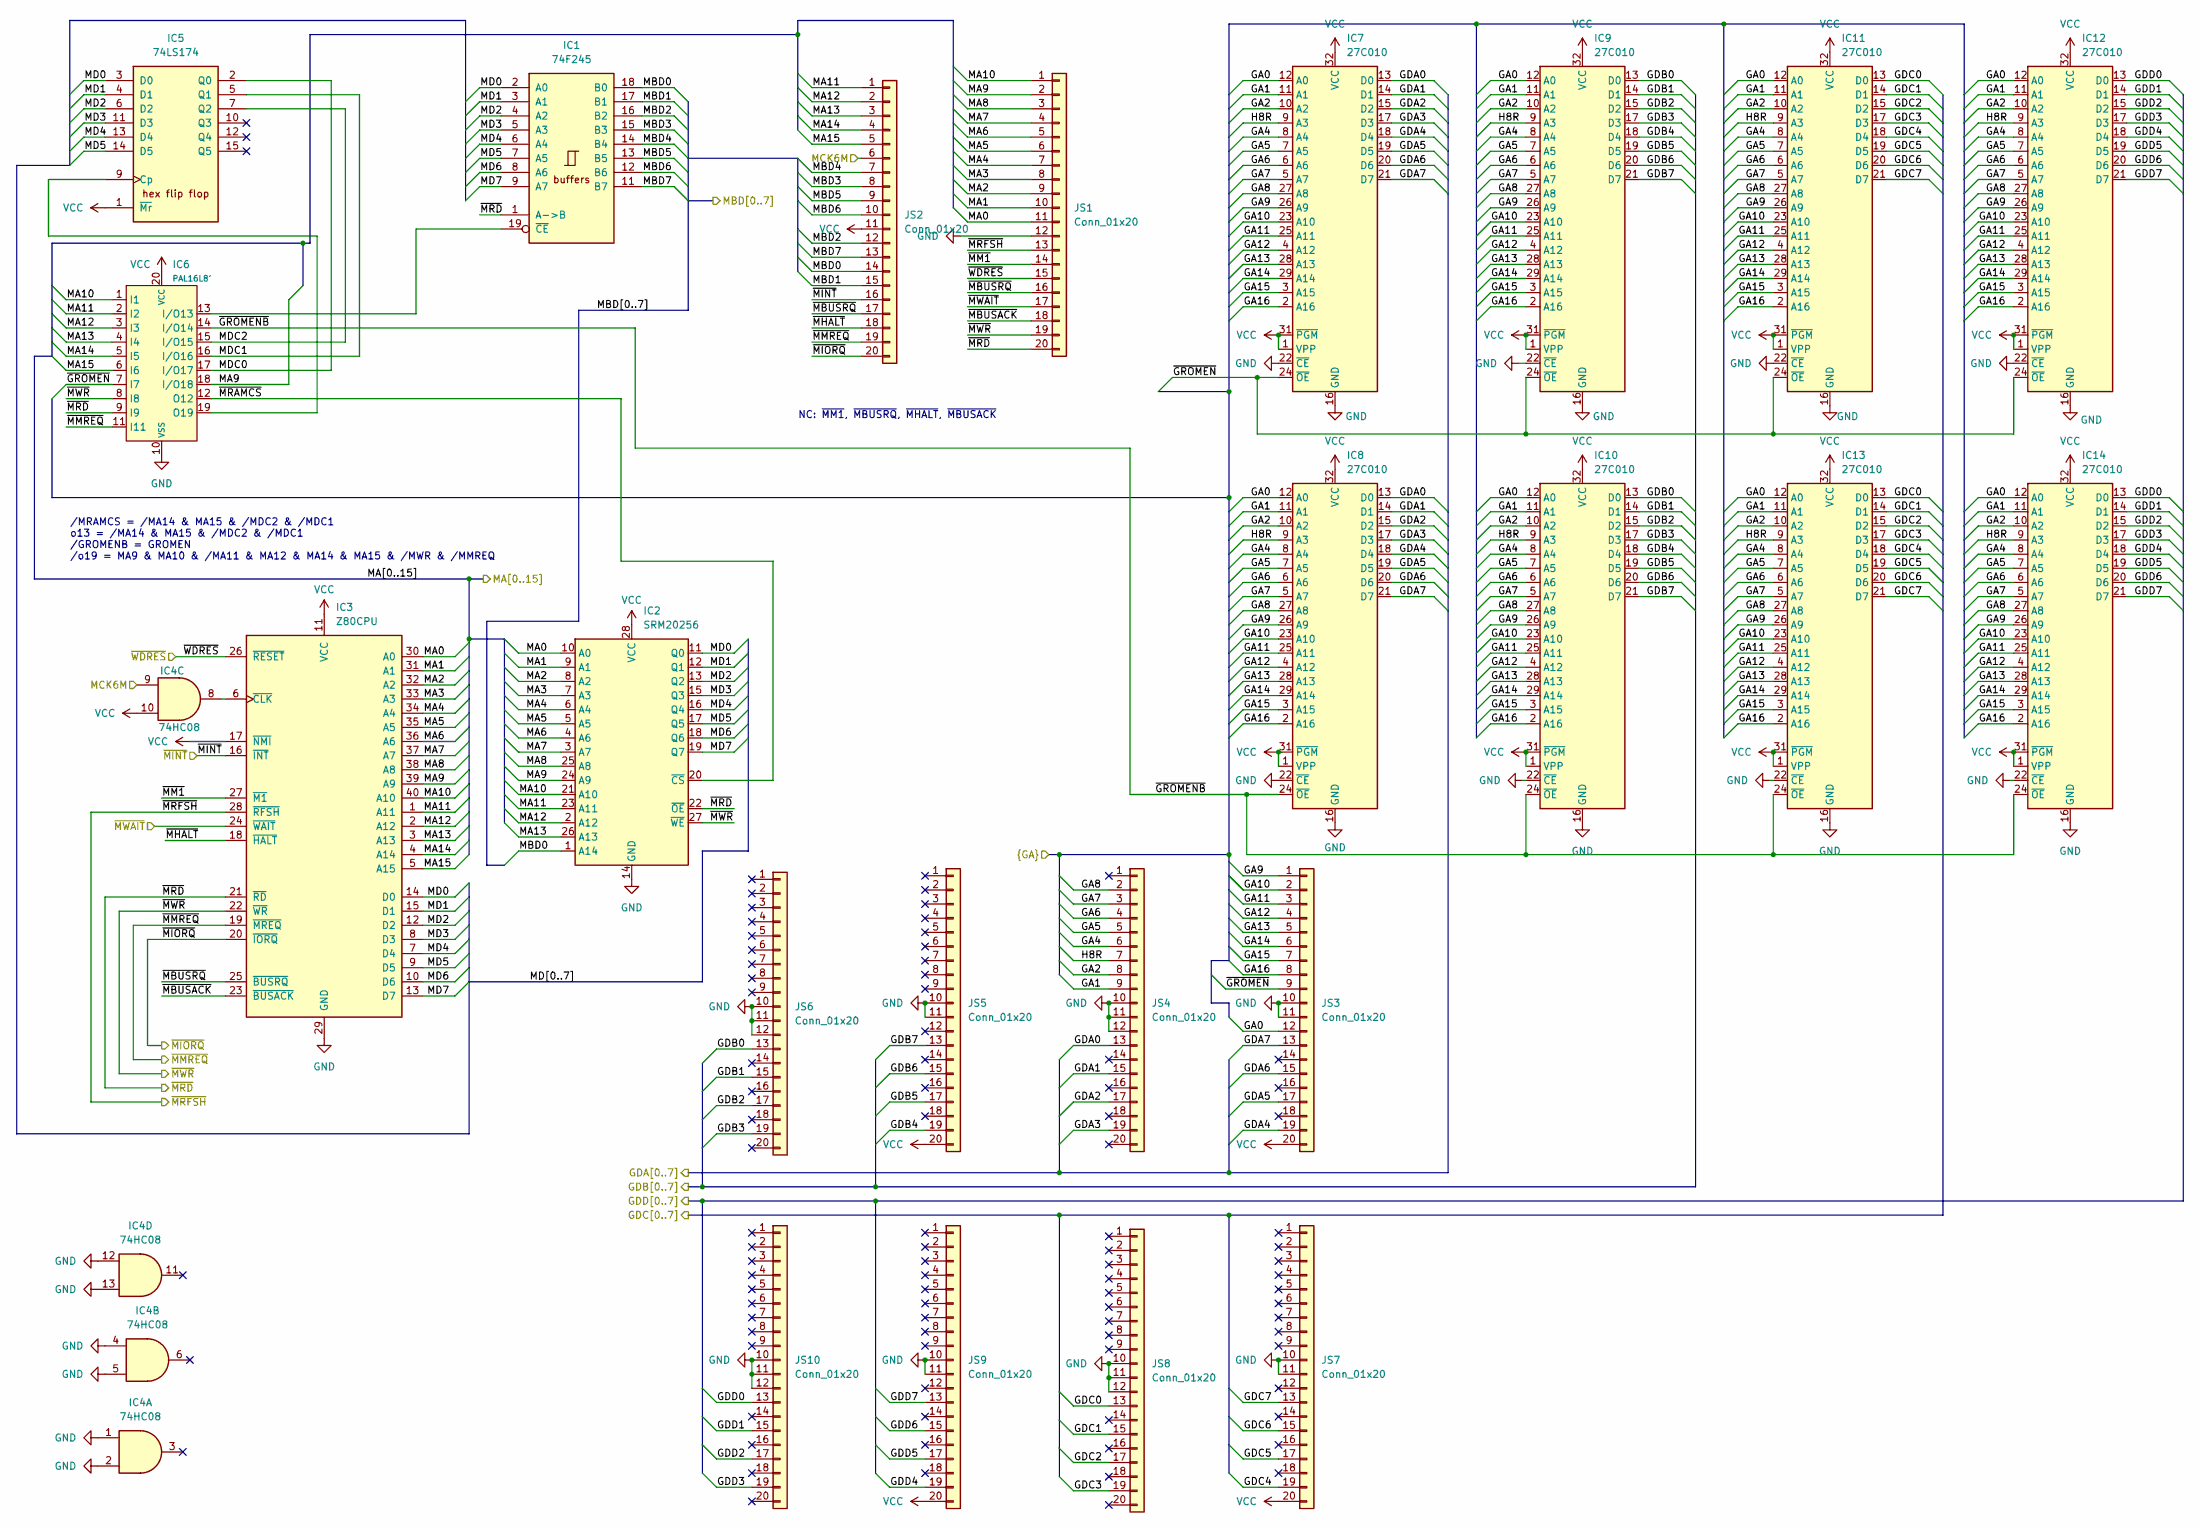
[picture p34: schematic sub_pcb.kicad_sch]

Parts:
IC1: 74F245
IC2: SRM20256; DIP-28_W15.24mm
IC3: Z80CPU
IC4: 74HC08
IC5: 74LS174
IC6: PAL16L8’
IC7, IC8, IC9, IC10, IC11, IC12, IC13, IC14: 27C010
JS1, JS2, JS3, JS4, JS5, JS6, JS7, JS8, JS9, JS10: Conn_01x20

Connections:
GA0: IC7.12 (A0), IC8.12 (A0), IC9.12 (A0), IC10.12 (A0), IC11.12 (A0), IC12.12 (A0), IC13.12 (A0), IC14.12 (A0), JS3.12
GA1: IC7.11 (A1), IC8.11 (A1), IC9.11 (A1), IC10.11 (A1), IC11.11 (A1), IC12.11 (A1), IC13.11 (A1), IC14.11 (A1), JS4.9
GA2: IC7.10 (A2), IC8.10 (A2), IC9.10 (A2), IC10.10 (A2), IC11.10 (A2), IC12.10 (A2), IC13.10 (A2), IC14.10 (A2), JS4.8
GA4: IC7.8 (A4), IC8.8 (A4), IC9.8 (A4), IC10.8 (A4), IC11.8 (A4), IC12.8 (A4), IC13.8 (A4), IC14.8 (A4), JS4.6
GA5: IC7.7 (A5), IC8.7 (A5), IC9.7 (A5), IC10.7 (A5), IC11.7 (A5), IC12.7 (A5), IC13.7 (A5), IC14.7 (A5), JS4.5
GA6: IC7.6 (A6), IC8.6 (A6), IC9.6 (A6), IC10.6 (A6), IC11.6 (A6), IC12.6 (A6), IC13.6 (A6), IC14.6 (A6), JS4.4
GA7: IC7.5 (A7), IC8.5 (A7), IC9.5 (A7), IC10.5 (A7), IC11.5 (A7), IC12.5 (A7), IC13.5 (A7), IC14.5 (A7), JS4.3
GA8: IC7.27 (A8), IC8.27 (A8), IC9.27 (A8), IC10.27 (A8), IC11.27 (A8), IC12.27 (A8), IC13.27 (A8), IC14.27 (A8), JS4.2
GA9: IC7.26 (A9), IC8.26 (A9), IC9.26 (A9), IC10.26 (A9), IC11.26 (A9), IC12.26 (A9), IC13.26 (A9), IC14.26 (A9), JS3.1
GA10: IC7.23 (A10), IC8.23 (A10), IC9.23 (A10), IC10.23 (A10), IC11.23 (A10), IC12.23 (A10), IC13.23 (A10), IC14.23 (A10), JS3.2
GA11: IC7.25 (A11), IC8.25 (A11), IC9.25 (A11), IC10.25 (A11), IC11.25 (A11), IC12.25 (A11), IC13.25 (A11), IC14.25 (A11), JS3.3
GA12: IC7.4 (A12), IC8.4 (A12), IC9.4 (A12), IC10.4 (A12), IC11.4 (A12), IC12.4 (A12), IC13.4 (A12), IC14.4 (A12), JS3.4
GA13: IC7.28 (A13), IC8.28 (A13), IC9.28 (A13), IC10.28 (A13), IC11.28 (A13), IC12.28 (A13), IC13.28 (A13), IC14.28 (A13), JS3.5
GA14: IC7.29 (A14), IC8.29 (A14), IC9.29 (A14), IC10.29 (A14), IC11.29 (A14), IC12.29 (A14), IC13.29 (A14), IC14.29 (A14), JS3.6
GA15: IC7.3 (A15), IC8.3 (A15), IC9.3 (A15), IC10.3 (A15), IC11.3 (A15), IC12.3 (A15), IC13.3 (A15), IC14.3 (A15), JS3.7
GA16: IC7.2 (A16), IC8.2 (A16), IC9.2 (A16), IC10.2 (A16), IC11.2 (A16), IC12.2 (A16), IC13.2 (A16), IC14.2 (A16), JS3.8
GDA0: IC7.13 (D0), IC8.13 (D0), JS4.13
GDA1: IC7.14 (D1), IC8.14 (D1), JS4.15
GDA2: IC7.15 (D2), IC8.15 (D2), JS4.17
GDA3: IC7.17 (D3), IC8.17 (D3), JS4.19
GDA4: IC7.18 (D4), IC8.18 (D4), JS3.19
GDA5: IC7.19 (D5), IC8.19 (D5), JS3.17
GDA6: IC7.20 (D6), IC8.20 (D6), JS3.15
GDA7: IC7.21 (D7), IC8.21 (D7), JS3.13
GDB0: IC9.13 (D0), IC10.13 (D0), JS6.13
GDB1: IC9.14 (D1), IC10.14 (D1), JS6.15
GDB2: IC9.15 (D2), IC10.15 (D2), JS6.17
GDB3: IC9.17 (D3), IC10.17 (D3), JS6.19
GDB4: IC9.18 (D4), IC10.18 (D4), JS5.19
GDB5: IC9.19 (D5), IC10.19 (D5), JS5.17
GDB6: IC9.20 (D6), IC10.20 (D6), JS5.15
GDB7: IC9.21 (D7), IC10.21 (D7), JS5.13
GDC0: IC11.13 (D0), IC13.13 (D0), JS8.13
GDC1: IC11.14 (D1), IC13.14 (D1), JS8.15
GDC2: IC11.15 (D2), IC13.15 (D2), JS8.17
GDC3: IC11.17 (D3), IC13.17 (D3), JS8.19
GDC4: IC11.18 (D4), IC13.18 (D4), JS7.19
GDC5: IC11.19 (D5), IC13.19 (D5), JS7.17
GDC6: IC11.20 (D6), IC13.20 (D6), JS7.15
GDC7: IC11.21 (D7), IC13.21 (D7), JS7.13
GDD0: IC12.13 (D0), IC14.13 (D0), JS10.13
GDD1: IC12.14 (D1), IC14.14 (D1), JS10.15
GDD2: IC12.15 (D2), IC14.15 (D2), JS10.17
GDD3: IC12.17 (D3), IC14.17 (D3), JS10.19
GDD4: IC12.18 (D4), IC14.18 (D4), JS9.19
GDD5: IC12.19 (D5), IC14.19 (D5), JS9.17
GDD6: IC12.20 (D6), IC14.20 (D6), JS9.15
GDD7: IC12.21 (D7), IC14.21 (D7), JS9.13
GND: IC2.14 (GND), IC3.29 (GND), IC4.1, IC4.2, IC4.4, IC4.5, IC4.12, IC4.13, IC6.10 (VSS), IC7.16 (GND), IC7.22 (~CE), IC8.16 (GND), IC8.22 (~CE), IC9.16 (GND), IC9.22 (~CE), IC10.16 (GND), IC10.22 (~CE), IC11.16 (GND), IC11.22 (~CE), IC12.16 (GND), IC12.22 (~CE), IC13.16 (GND), IC13.22 (~CE), IC14.16 (GND), IC14.22 (~CE), JS1.12, JS3.10, JS3.11, JS4.10, JS4.11, JS4.12, JS5.10, JS5.11, JS6.10, JS6.11, JS6.12, JS7.10, JS7.11, JS8.10, JS8.11, JS8.12, JS9.10, JS9.11, JS10.10, JS10.11, JS10.12
H8R: IC7.9 (A3), IC8.9 (A3), IC9.9 (A3), IC10.9 (A3), IC11.9 (A3), IC12.9 (A3), IC13.9 (A3), IC14.9 (A3), JS4.7
MA0: IC2.10 (A0), IC3.30 (A0), JS1.11
MA1: IC2.9 (A1), IC3.31 (A1), JS1.10
MA2: IC2.8 (A2), IC3.32 (A2), JS1.9
MA3: IC2.7 (A3), IC3.33 (A3), JS1.8
MA4: IC2.6 (A4), IC3.34 (A4), JS1.7
MA5: IC2.5 (A5), IC3.35 (A5), JS1.6
MA6: IC2.4 (A6), IC3.36 (A6), JS1.5
MA7: IC2.3 (A7), IC3.37 (A7), JS1.4
MA8: IC2.25 (A8), IC3.38 (A8), JS1.3
MA9: IC2.24 (A9), IC3.39 (A9), IC6.18 (I/O18), JS1.2
MA10: IC2.21 (A10), IC3.40 (A10), IC6.1 (I1), JS1.1
MA11: IC2.23 (A11), IC3.1 (A11), IC6.2 (I2), JS2.1
MA12: IC2.2 (A12), IC3.2 (A12), IC6.3 (I3), JS2.2
MA13: IC2.26 (A13), IC3.3 (A13), IC6.4 (I4), JS2.3
MA14: IC3.4 (A14), IC6.5 (I5), JS2.4
MA15: IC3.5 (A15), IC6.6 (I6), JS2.5
MBD0: IC1.18 (B0), IC2.1 (A14), JS2.14
MBD1: IC1.17 (B1), JS2.15
MBD2: IC1.16 (B2), JS2.12
MBD3: IC1.15 (B3), JS2.8
MBD4: IC1.14 (B4), JS2.7
MBD5: IC1.13 (B5), JS2.9
MBD6: IC1.12 (B6), JS2.10
MBD7: IC1.11 (B7), JS2.13
MCK6M: IC4.9, JS2.6
MD0: IC1.2 (A0), IC2.11 (Q0), IC3.14 (D0), IC5.3 (D0)
MD1: IC1.3 (A1), IC2.12 (Q1), IC3.15 (D1), IC5.4 (D1)
MD2: IC1.4 (A2), IC2.13 (Q2), IC3.12 (D2), IC5.6 (D2)
MD3: IC1.5 (A3), IC2.15 (Q3), IC3.8 (D3), IC5.11 (D3)
MD4: IC1.6 (A4), IC2.16 (Q4), IC3.7 (D4), IC5.13 (D4)
MD5: IC1.7 (A5), IC2.17 (Q5), IC3.9 (D5), IC5.14 (D5)
MD6: IC1.8 (A6), IC2.18 (Q6), IC3.10 (D6)
MD7: IC1.9 (A7), IC2.19 (Q7), IC3.13 (D7)
MDC0: IC5.2 (Q0), IC6.17 (I/O17)
MDC1: IC5.5 (Q1), IC6.16 (I/O16)
MDC2: IC5.7 (Q2), IC6.15 (I/O15)
unnamed: IC1.19 (~CE), IC6.13 (I/O13)
unnamed: IC3.6 (~CLK), IC4.8
unnamed: IC5.9 (Cp), IC6.19 (O19)
VCC: IC2.28 (VCC), IC3.11 (VCC), IC3.17 (~NMI), IC4.10, IC5.1 (~Mr), IC6.20 (VCC), IC7.1 (VPP), IC7.31 (~PGM), IC7.32 (VCC), IC8.1 (VPP), IC8.31 (~PGM), IC8.32 (VCC), IC9.1 (VPP), IC9.31 (~PGM), IC9.32 (VCC), IC10.1 (VPP), IC10.31 (~PGM), IC10.32 (VCC), IC11.1 (VPP), IC11.31 (~PGM), IC11.32 (VCC), IC12.1 (VPP), IC12.31 (~PGM), IC12.32 (VCC), IC13.1 (VPP), IC13.31 (~PGM), IC13.32 (VCC), IC14.1 (VPP), IC14.31 (~PGM), IC14.32 (VCC), JS2.11, JS3.20, JS5.20, JS7.20, JS9.20
~GROMENB: IC6.14 (I/O14), IC8.24 (~OE), IC10.24 (~OE), IC13.24 (~OE), IC14.24 (~OE)
~GROMEN: IC6.7 (I7), IC7.24 (~OE), IC9.24 (~OE), IC11.24 (~OE), IC12.24 (~OE), JS3.9
~MBUSACK: IC3.23 (~BUSACK), JS1.18
~MBUSRQ: IC3.25 (~BUSRQ), JS1.16, JS2.17
~MHALT: IC3.18 (~HALT), JS2.18
~MINT: IC3.16 (~INT), JS2.16
~MIORQ: IC3.20 (~IORQ), JS2.20
~MM1: IC3.27 (~M1), JS1.14
~MMREQ: IC3.19 (~MREQ), IC6.11 (I11), JS2.19
~MRAMCS: IC2.20 (~CS), IC6.12 (O12)
~MRD: IC1.1 (A->B), IC2.22 (~OE), IC3.21 (~RD), IC6.9 (I9), JS1.20
~MRFSH: IC3.28 (~RFSH), JS1.13
~MWAIT: IC3.24 (~WAIT), JS1.17
~MWR: IC2.27 (~WE), IC3.22 (~WR), IC6.8 (I8), JS1.19
~WDRES: IC3.26 (~RESET), JS1.15

Notes on the sheet:
NC: ~{MM1}, ~{MBUSRQ}, ~{MHALT}, ~{MBUSACK}
/MRAMCS = /MA14 & MA15 & /MDC2 & /MDC1 o13 = /MA14 & MA15 & /MDC2 & /MDC1 /GROMENB = GROMEN /o19 = MA9 & MA10 & /MA11 & MA12 & MA14 & MA15 & /MWR & /MMREQ
