skutis/jtbubl/cores/bubl/hdl/jtbubl_game.v

/*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
    Author: Jose Tejada Gomez. Twitter: @topapate
    Version: 1.0
    Date: 02-05-2020 */

module jtbubl_game(
    input           rst,
    input           clk,
    input           rst24,
    input           clk24,
    input           pxl2_cen,   // 12   MHz
    input           pxl_cen,    //  6   MHz
    output   [3:0]  red,
    output   [3:0]  green,
    output   [3:0]  blue,
    output          LHBL,
    output          LVBL,
    output          HS,
    output          VS,
    // cabinet I/O
    input   [ 1:0]  start_button,
    input   [ 1:0]  coin_input,
    input   [ 5:0]  joystick1,
    input   [ 5:0]  joystick2,
    // SDRAM interface
    input           downloading,
    output          dwnld_busy,
    output          sdram_req,
    output  [21:0]  sdram_addr,
    input   [31:0]  data_read,
    input           data_dst,
    input           data_rdy,
    input           sdram_ack,
    // ROM LOAD
    input   [24:0]  ioctl_addr,
    input   [ 7:0]  ioctl_dout,
    input           ioctl_wr,
    output  [21:0]  prog_addr,
    output  [ 7:0]  prog_data,
    output  [ 1:0]  prog_mask,
    output          prog_we,
    output          prog_rd,
    // DIP switches
    input   [31:0]  status,     // only bits 31:16 are looked at
    input   [31:0]  dipsw,
    input           service,
    input           tilt,
    input           dip_pause,
    inout           dip_flip,
    input           dip_test,
    input   [ 1:0]  dip_fxlevel, // Not a DIP on the original PCB
    // Sound output
    output  signed [15:0] snd,
    output          sample,
    output          game_led,
    input           enable_psg,
    input           enable_fm,
    // Debug
    input   [ 3:0]  gfx_en
);

wire        main_cs, sub_cs, mcu_cs, snd_cs, gfx_cs;
wire        main_ok, sub_ok, mcu_ok, snd_ok, gfx_ok;
wire        snd_rstn, black_n, flip;
wire [31:0] gfx_data;
wire [17:0] gfx_addr;

wire [ 7:0] main_data, sub_data, mcu_data, snd_data, snd_latch, main_latch;
wire [14:0] snd_addr, sub_addr;
wire [11:0] mcu_addr;
wire [17:0] main_addr;
wire        cen12, cen6, cen4, cen3, prom_we;
reg         tokio;

wire [ 7:0] dipsw_a, dipsw_b;
wire        main_flag, main_stb, snd_stb;

wire [12:0] cpu_addr;
wire        vram_cs,  pal_cs;
wire        cpu_cen, cpu_rnw, cpu_irqn;
wire [ 7:0] vram_dout, pal_dout, cpu_dout;
wire        snd_flag;

assign prog_rd    = 0;
assign dwnld_busy = downloading;
assign { dipsw_b, dipsw_a }   = dipsw[15:0];
assign dip_flip               = flip;

localparam [21:0] SUB_OFFSET = 22'h2_8000 >> 1;
localparam [21:0] SND_OFFSET = 22'h3_0000 >> 1;
localparam [21:0] MCU_OFFSET = 22'h3_8000 >> 1;
localparam [21:0] GFX_OFFSET = 22'h4_0000 >> 1;
localparam [24:0] PROM_START = 25'hC_0000;

jtframe_cen24 u_cen(
    .clk        ( clk24         ),    // 24 MHz
    .cen12      ( cen12         ),
    .cen6       ( cen6          ),
    .cen4       ( cen4          ),
    .cen3       ( cen3          ),
    .cen8       (               ),
    .cen3q      (               ), // 1/4 advanced with respect to cen3
    .cen1p5     (               ),
    // 180 shifted signals
    .cen12b     (               ),
    .cen6b      (               ),
    .cen3b      (               ),
    .cen3qb     (               ),
    .cen1p5b    (               )
);

wire [7:0] nc;

jtframe_dwnld #(.PROM_START(PROM_START))
u_dwnld(
    .clk            ( clk           ),
    .downloading    ( downloading   ),
    .ioctl_addr     ( ioctl_addr    ),
    .ioctl_dout     ( ioctl_dout    ),
    .ioctl_wr       ( ioctl_wr      ),
    .prog_addr      ( prog_addr     ),
    .prog_data      ( {nc,prog_data}),
    .prog_mask      ( prog_mask     ), // active low
    .prog_we        ( prog_we       ),
    .prom_we        ( prom_we       ),
    .sdram_ack      ( sdram_ack     ),
    .header         (               )
);

`ifdef SIMULATION
`ifndef LOADROM
    `ifdef TOKIO
    initial tokio=1;
    `else
    initial tokio=0;
    `endif
`endif
`endif

always @(posedge clk) begin
    if( ioctl_wr && ioctl_addr==25'd0 )
        tokio <= ioctl_dout==8'h7e; // single byte detection. Both tokyo and tokyob start like this
end

reg cpu_start;

always @(posedge clk24, posedge rst24) begin
    if( rst24 ) begin
        cpu_start <= 0;
    end else begin
        if( &{ main_ok, sub_ok, mcu_ok, snd_ok } ) cpu_start <= 1;
    end
end


`ifndef NOMAIN
jtbubl_main u_main(
    .rst            ( rst24         ),
    .clk24          ( clk24         ),        // 24 MHz
    .cen12          ( cen12         ),
    .cen6           ( cen6          ),
    .cen4           ( cen4          ),
    .cpu_start      ( cpu_start     ),
    //.cpu_cen        ( cpu_cen       ),

    .tokio          ( tokio         ),
    // Main CPU ROM
    .main_rom_addr  ( main_addr     ),
    .main_rom_cs    ( main_cs       ),
    .main_rom_ok    ( main_ok       ),
    .main_rom_data  ( main_data     ),
    // Sub CPU ROM
    .sub_rom_addr   ( sub_addr      ),
    .sub_rom_cs     ( sub_cs        ),
    .sub_rom_ok     ( sub_ok        ),
    .sub_rom_data   ( sub_data      ),
    // MCU ROM
    .mcu_rom_addr   ( mcu_addr      ),
    .mcu_rom_cs     ( mcu_cs        ),
    .mcu_rom_ok     ( mcu_ok        ),
    .mcu_rom_data   ( mcu_data      ),

    // Sound
    .snd_latch      ( snd_latch     ),
    .snd_stb        ( snd_stb       ),
    .snd_flag       ( snd_flag      ),
    .main_stb       ( main_stb      ),
    .main_flag      ( main_flag     ),
    .main_latch     ( main_latch    ),
    .snd_rstn       ( snd_rstn      ),
    // cabinet I/O
    .start_button   ( start_button  ),
    .coin_input     ( coin_input    ),
    .joystick1      ( joystick1     ),
    .joystick2      ( joystick2     ),
    .service        ( service       ),
    // Video
    .LVBL           ( LVBL          ),
    .flip           ( flip          ),
    .black_n        ( black_n       ),
    .cpu_addr       ( cpu_addr      ),
    .cpu_dout       ( cpu_dout      ),
    .cpu_rnw        ( cpu_rnw       ),
    .vram_cs        ( vram_cs       ),
    .vram_dout      ( vram_dout     ),
    .pal_cs         ( pal_cs        ),
    .pal_dout       ( pal_dout      ),

    // DIP switches
    .dip_pause      ( dip_pause     ),
    .dipsw_a        ( dipsw_a       ),
    .dipsw_b        ( dipsw_b       )
);
`else
assign main_cs = 0;
assign cpu_rnw = 1;
assign vram_cs = 0;
assign pal_cs  = 0;
assign cpu_cen = 0;
assign black_n = 1;
`endif

jtbubl_video u_video(
    .rst            ( rst           ),
    .clk            ( clk           ),
    .clk_cpu        ( clk24         ),
    .pxl2_cen       ( pxl2_cen      ),
    .pxl_cen        ( pxl_cen       ),
    .LHBL           ( LHBL          ),
    .LVBL           ( LVBL          ),
    .HS             ( HS            ),
    .VS             ( VS            ),
    .flip           ( flip          ),
    .dip_pause      ( dip_pause     ),
    .start_button   ( &start_button ),
    // PROMs
    .prom_we        ( prom_we       ),
    .prog_addr      ( prog_addr[7:0]),
    .prog_data      ( prog_data[3:0]),
    // GFX - CPU interface
    .vram_cs        ( vram_cs       ),
    .pal_cs         ( pal_cs        ),
    .cpu_rnw        ( cpu_rnw       ),
    .cpu_cen        ( cpu_cen       ),
    .cpu_addr       ( cpu_addr      ),
    .cpu_dout       ( cpu_dout      ),
    .vram_dout      ( vram_dout     ),
    .pal_dout       ( pal_dout      ),
    .black_n        ( black_n       ),
    // SDRAM
    .rom_addr       ( gfx_addr      ),
    .rom_data       ( gfx_data      ),
    .rom_ok         ( gfx_ok        ),
    .rom_cs         ( gfx_cs        ),
    // pixels
    .red            ( red           ),
    .green          ( green         ),
    .blue           ( blue          ),
    // Test
    .gfx_en         ( gfx_en        )
);

`ifndef NOSOUND
jtbubl_sound u_sound(
    .rst        ( rst24         ),
    .clk        ( clk24         ), // 24 MHz
    //.rstn       ( snd_rstn      ),
    .rstn       ( 1'b1          ),
    .cen3       ( cen3          ),
    .start      ( cpu_start     ),
    .fx_level   ( dip_fxlevel   ),

    .tokio      ( tokio         ),
    // communication with main CPU
    .snd_latch  ( snd_latch     ),
    .main_latch ( main_latch    ),
    .snd_stb    ( snd_stb       ),
    .main_stb   ( main_stb      ),
    .snd_flag   ( snd_flag      ),
    .main_flag  ( main_flag     ),
    // ROM
    .rom_addr   ( snd_addr      ),
    .rom_cs     ( snd_cs        ),
    .rom_data   ( snd_data      ),
    .rom_ok     ( snd_ok        ),

    // Sound output
    .snd        ( snd           ),
    .sample     ( sample        ),
    .peak       ( game_led      )
);
`else
assign snd_cs   = 0;
assign snd_addr = 15'd0;
assign snd      = 16'd0;
assign sample   = 0;
assign snd_flag = 0;
assign main_stb = 0;
`endif

jtframe_rom #(
    .SLOT0_AW    ( 18              ),
    .SLOT0_DW    (  8              ),
    .SLOT0_OFFSET(  0              ), // Main

    .SLOT1_AW    ( 15              ),
    .SLOT1_DW    (  8              ),
    .SLOT1_OFFSET(  SUB_OFFSET     ), // Sub

    .SLOT2_AW    ( 12              ),
    .SLOT2_DW    (  8              ),
    .SLOT2_OFFSET(  MCU_OFFSET     ), // MCU

    .SLOT3_AW    ( 15              ), // Sound
    .SLOT3_DW    (  8              ),
    .SLOT3_OFFSET( SND_OFFSET      ),

    .SLOT4_AW    ( 18              ), // GFX
    .SLOT4_DW    ( 32              ),
    .SLOT4_OFFSET( GFX_OFFSET      )
) u_rom (
    .rst         ( rst           ),
    .clk         ( clk           ),

    .slot0_cs    ( main_cs  | ~cpu_start     ),
    .slot1_cs    ( sub_cs   | ~cpu_start     ),
    .slot2_cs    ( mcu_cs   | ~cpu_start     ),
    .slot3_cs    ( snd_cs   | ~cpu_start     ), // unused
    .slot4_cs    ( gfx_cs        ),
    .slot5_cs    ( 1'b0          ), // unused
    .slot6_cs    ( 1'b0          ),
    .slot7_cs    ( 1'b0          ), // unused
    .slot8_cs    ( 1'b0          ),

    .slot0_ok    ( main_ok       ),
    .slot1_ok    ( sub_ok        ),
    .slot2_ok    ( mcu_ok        ),
    .slot3_ok    ( snd_ok        ),
    .slot4_ok    ( gfx_ok        ),
    .slot5_ok    (               ),
    .slot6_ok    (               ),
    .slot7_ok    (               ),
    .slot8_ok    (               ),

    .slot0_addr  ( main_addr     ),
    .slot1_addr  ( sub_addr      ),
    .slot2_addr  ( mcu_addr      ),
    .slot3_addr  ( snd_addr      ),
    .slot4_addr  ( gfx_addr      ),
    .slot5_addr  (               ),
    .slot6_addr  (               ),
    .slot7_addr  (               ),
    .slot8_addr  (               ),

    .slot0_dout  ( main_data     ),
    .slot1_dout  ( sub_data      ),
    .slot2_dout  ( mcu_data      ),
    .slot3_dout  ( snd_data      ),
    .slot4_dout  ( gfx_data      ),
    .slot5_dout  (               ),
    .slot6_dout  (               ),
    .slot7_dout  (               ),
    .slot8_dout  (               ),

    // SDRAM interface
    .sdram_rd    ( sdram_req     ),
    .sdram_ack   ( sdram_ack     ),
    .data_dst    ( data_dst      ),
    .data_rdy    ( data_rdy      ),
    .downloading ( downloading   ),
    .sdram_addr  ( sdram_addr    ),
    .data_read   (data_read[15:0])
);

endmodule
