skutis/jtbubl/cores/bubl/hdl/jtbubl_sound.v

/*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
    Author: Jose Tejada Gomez. Twitter: @topapate
    Version: 1.0
    Date: 02-06-2020 */

module jtbubl_sound(
    input             rst,    // System reset
    input             rstn,   // from Main
    input             clk,
    input             cen3,   //  3   MHz
    input             start,

    input      [ 1:0] fx_level,
    input             tokio,
    // Interface with main CPU
    input      [ 7:0] snd_latch,
    input             snd_stb,
    output reg [ 7:0] main_latch,
    output reg        main_stb,
    output            snd_flag,
    input             main_flag,
    // ROM
    output     [14:0] rom_addr,
    output  reg       rom_cs,
    input      [ 7:0] rom_data,
    input             rom_ok,

    // Sound output
    output signed [15:0] snd,
    output            sample,
    output            peak
);

wire        [15:0] A;
wire               iorq_n, m1_n, wr_n, rd_n;
wire        [ 7:0] ram_dout, dout, fm0_dout, fm1_dout;
reg                ram_cs, fm1_cs, fm0_cs, io_cs, nmi_en;
wire               mreq_n, rfsh_n;
reg         [ 7:0]  din;
wire               intn_fm0, intn_fm1;
wire               int_n;
wire               flag_clr;
wire               nmi_n;
wire signed [15:0] fm0_snd,  fm1_snd;
wire        [ 9:0] psg_snd;
wire signed [ 9:0] psg2x; // DC-removed version of psg0
wire               snd_rstn = ~rst & rstn;

assign int_n      = intn_fm0 & intn_fm1;
assign rom_addr   = A[14:0];
assign nmi_n      = snd_flag | ~nmi_en;
assign flag_clr   = (io_cs && !rd_n && A[1:0]==2'b0) || ~snd_rstn;

always @(*) begin
    rom_cs = !mreq_n && !A[15];
    ram_cs = !mreq_n &&  A[15] && A[14:12]==3'b00;
    if( tokio ) begin
        fm0_cs = !mreq_n && A[15:12]==4'b1011; // YM2203
        fm1_cs = 0;
        io_cs  = !mreq_n && (A[15:12]==4'b1001 || A[15:12]==4'b1010);
    end else begin
        fm0_cs = !mreq_n && A[15] && A[14:12]==3'b01; // YM2203
        fm1_cs = !mreq_n && A[15] && A[14:12]==3'b10; // OPL
        io_cs  = !mreq_n && A[15] && A[14:12]==3'b11;
    end
end

always @(posedge clk) begin
    case( 1'b1 )
        rom_cs:   din <= rom_data;
        fm0_cs:   din <= fm0_dout;
        fm1_cs:   din <= fm1_dout;
        io_cs:    din <= tokio ? (
                         !A[12] ? 8'hff :
                         ( A[11] ? {6'h3f, main_stb, snd_flag} : snd_latch )
                         ) : ( // Bubble Bobble:
                         A[1] ? 8'hff : (
                         A[0] ? {6'h3f, main_stb, snd_flag} : snd_latch));
        ram_cs:   din <= ram_dout;
        default:  din <= 8'hff;
    endcase
end

always @(posedge clk, negedge snd_rstn) begin
    if( !snd_rstn ) begin
        main_latch <= 8'h00;
        main_stb   <= 0;
        nmi_en     <= 0;
    end else begin
        if( io_cs && !wr_n ) begin
            if( tokio ) begin
                if( !A[12] ) begin // NMI control
                    if(!A[11]) nmi_en <= 0;
                    if( A[11]) nmi_en <= 1;
                end else begin
                    if(!A[11]) main_latch <= dout;
                    if( A[11]) main_stb   <= 1;
                end
            end else begin
                case( A[1:0] )
                    2'd0: begin
                        main_latch <= dout;
                        main_stb   <= 1;
                    end
                    2'd1: nmi_en     <= 1; // enables NMI
                    2'd2: nmi_en     <= 0;
                endcase
            end
        end else begin
            main_stb <= 0;
        end
    end
end

jtframe_ff u_flag(
    .clk    ( clk      ),
    .rst    ( rst      ),
    .cen    ( 1'b1     ),
    .din    ( 1'b1     ),
    .q      (          ),
    .qn     ( snd_flag ),
    .set    ( 1'b0     ),
    .clr    ( flag_clr ),
    .sigedge( snd_stb  )
);

jtframe_sysz80 #(.RAM_AW(13)) u_cpu(
    .rst_n      ( snd_rstn    ),
    .clk        ( clk         ),
    .cen        ( cen3        ),
    .cpu_cen    (             ),
    .int_n      ( int_n       ),
    .nmi_n      ( nmi_n       ),
    .busrq_n    ( 1'b1        ),
    .m1_n       (             ),
    .mreq_n     ( mreq_n      ),
    .iorq_n     (             ),
    .rd_n       ( rd_n        ),
    .wr_n       ( wr_n        ),
    .rfsh_n     (             ),
    .halt_n     (             ),
    .busak_n    (             ),
    .A          ( A           ),
    .cpu_din    ( din         ),
    .cpu_dout   ( dout        ),
    .ram_dout   ( ram_dout    ),
    .ram_cs     ( ram_cs      ),
    .rom_cs     ( rom_cs      ),
    .rom_ok     ( rom_ok      )
);

jt49_dcrm2 #(.sw(10)) u_dcrm (
    .clk    (  clk      ),
    .cen    (  cen3     ),
    .rst    (  rst      ),
    .din    (  psg_snd  ),
    .dout   (  psg2x    )
);

// Both FM chips have the same gain according to the schematics
// YM2203 to YM3526 ratio = 8:1

reg  [7:0] fm0_gain, psg_gain;

wire [7:0] fm1_gain = tokio ? 8'h40 : 8'h10; // YM3526

always @(posedge clk) begin
    if( tokio ) begin
        case( fx_level )
            2'd0: psg_gain <= 8'h01;
            2'd1: psg_gain <= 8'h02;
            2'd2: psg_gain <= 8'h04;
            2'd3: psg_gain <= 8'h08;
        endcase
        fm0_gain <= fm1_gain;
    end else begin
        case( fx_level )
            2'd0: fm0_gain <= 8'h18;
            2'd1: fm0_gain <= 8'h30;
            2'd2: fm0_gain <= 8'h60;
            2'd3: fm0_gain <= 8'hC0;
        endcase
        psg_gain <= fm0_gain;
    end
end

jtframe_mixer #(.W2(10),.W3(8)) u_mixer(
    .rst    ( rst          ),
    .clk    ( clk          ),
    .cen    ( cen3         ),
    .ch0    ( fm0_snd      ),
    .ch1    ( fm1_snd      ),
    .ch2    ( psg2x        ),
    .ch3    ( 8'd0         ),
    .gain0  ( fm0_gain     ), // YM2203 - Fx
    .gain1  ( fm1_gain     ), // YM3526 - Music
    .gain2  ( psg_gain     ), // PSG - Unused in Bubble Bobble - Used in Tokio
    .gain3  ( 8'd0         ),
    .mixed  ( snd          ),
    .peak   ( peak         )
);

jt03 u_2203(
    .rst        ( ~snd_rstn  ),
    .clk        ( clk        ),
    .cen        ( cen3       ),
    .din        ( dout       ),
    .dout       ( fm0_dout   ),
    .addr       ( A[0]       ),
    .cs_n       ( ~fm0_cs    ),
    .wr_n       ( wr_n       ),
    .psg_snd    ( psg_snd    ),
    .fm_snd     ( fm0_snd    ),
    .snd_sample ( sample     ),
    .irq_n      ( intn_fm0   ),
    // unused outputs
    .psg_A      (            ),
    .psg_B      (            ),
    .psg_C      (            ),
    .snd        (            )
);

jtopl u_opl(
    .rst        ( ~snd_rstn  ),
    .clk        ( clk        ),
    .cen        ( cen3       ),
    .din        ( dout       ),
    .dout       ( fm1_dout   ),
    .addr       ( A[0]       ),
    .cs_n       ( ~fm1_cs    ),
    .wr_n       ( wr_n       ),
    .irq_n      ( intn_fm1   ),
    .snd        ( fm1_snd    ),
    .sample     (            )
);

`ifdef SIMULATION
    integer fsnd;
    initial begin
        fsnd=$fopen("fm_sound.raw","wb");
    end
    always @(posedge sample) begin
        $fwrite(fsnd,"%u", {fm0_snd, fm1_snd});
    end
`endif

endmodule
