skutis/jtbubl/doc/mame/driver/bubl.cpp

// license:BSD-3-Clause
// copyright-holders:Chris Moore, Nicola Salmoria
/***************************************************************************

Tokio          (c) 1986 Taito
Bubble Bobble  (c) 1986 Taito

driver by Chris Moore, Nicola Salmoria
also based on Tokio driver by Marcelo de G. Malheiros <malheiro@dca.fee.unicamp.br>


Main clock: XTAL = 24 MHz
Horizontal video frequency: HSYNC = XTAL/4/384 = 15.625 kHz
Video frequency: VSYNC = HSYNC/264 = 59.185606 Hz
VBlank duration: 1/VSYNC * (40/264) = 2560 us

****************************************************************************

Bubble Bobble ROM info

CPU Board
---------
           | Taito  |Romstar | ?????  |Romstar |
           |        |        |missing |mode sel|
17  CU1    | A78-01 |   ->   |   ->   |   ->   |   protection mcu (JPH1011P)
49  PAL1   | A78-02 |   ->   |   ->   |   ->   |   address decoder
43  PAL2   | A78-03 |   ->   |   ->   |   ->   |   address decoder
12  PAL3   | A78-04 |   ->   |   ->   |   ->   |   address decoder
53  empty  |        |        |        |        |   main prg
52  ROM1   | A78-05 | A78-21 | A78-22 | A78-24 |   main prg
51  ROM2   | A78-06 |   ->   | A78-23 | A78-25 |   main prg
46  ROM4   | A78-07 |   ->   |   ->   |   ->   |   sound prg
37  ROM3   | A78-08 |   ->   |   ->   |   ->   |   sub prg

Video Board
-----------
12  ROM1   | A78-09 |   ->   |   ->   |   ->   |   gfx
13  ROM2   | A78-10 |   ->   |   ->   |   ->   |   gfx
14  ROM3   | A78-11 |   ->   |   ->   |   ->   |   gfx
15  ROM4   | A78-12 |   ->   |   ->   |   ->   |   gfx
16  ROM5   | A78-13 |   ->   |   ->   |   ->   |   gfx
17  ROM6   | A78-14 |   ->   |   ->   |   ->   |   gfx
18  empty  |        |        |        |        |   gfx
19  empty  |        |        |        |        |   gfx
30  ROM7   | A78-15 |   ->   |   ->   |   ->   |   gfx
31  ROM8   | A78-16 |   ->   |   ->   |   ->   |   gfx
32  ROM9   | A78-17 |   ->   |   ->   |   ->   |   gfx
33  ROM10  | A78-18 |   ->   |   ->   |   ->   |   gfx
34  ROM11  | A78-19 |   ->   |   ->   |   ->   |   gfx
35  ROM12  | A78-20 |   ->   |   ->   |   ->   |   gfx
36  empty  |        |        |        |        |   gfx
37  empty  |        |        |        |        |   gfx
41  ROM13  | A71-25 |   ->   |   ->   |   ->   |   video timing


Bobble Bobble memory map

most of the address decoding is done by various PALs which haven't been read, so
the memory map is inferred by program behaviour

CPU #1

Address          Dir Data     Name      Description
---------------- --- -------- --------- -----------------------
0xxxxxxxxxxxxxxx R   xxxxxxxx ROM 51    program ROM
10xxxxxxxxxxxxxx R   xxxxxxxx ROM 52/53 program ROM (banked)
110xxxxxxxxxxxxx R/W xxxxxxxx VRAM      video RAM
11100xxxxxxxxxxx R/W xxxxxxxx WORK      RAM shared with CPU #2
11101xxxxxxxxxxx R/W xxxxxxxx WORK      RAM shared with CPU #2
11110xxxxxxxxxxx R/W xxxxxxxx WORK      RAM shared with CPU #2
1111 100x xxxxxxxx R/W xxxxxxxx COLOR     palette RAM
1111 1010 0-----00   W xxxxxxxx SOUND     command for sound CPU
1111 1010 0-----01   W --------           n.c.
1111 1010 0-----10   W --------           n.c.
1111 1010 0-----11   W -------x SRESET    reset sound CPU, sound chips, and sound CPU to CPU #1 semaphore
1111 1010 0-----00 R   xxxxxxxx           answer from sound CPU (not used)
1111 1010 0-----01 R   -------x           message pending from sound CPU to CPU #1 (not used)
1111 1010 0-----01 R   ------x-           message pending from CPU #1 to sound CPU (not used)
1111 1010 0-----10 R                      n.c.
1111 1010 0-----11 R                      n.c.
1111 1010 1-------   W -------- TRES?     watchdog reset
1111 1011 00------   W -------- NMIRQ     trigger NMI on CPU #2 (not used)
1111 1011 01------   W -----xxx           ROM bank
1111 1011 01------   W ----x---           n.c.
1111 1011 01------   W ---x---- SBRES     reset CPU #2
1111 1011 01------   W --x----- SEQRES    reset MCU
1111 1011 01------   W -x------ BLACK     blank screen
1111 1011 01------   W x------- VHINV     flip screen
1111 1011 10------   W --------           n.c.
1111 1011 11------   W --------           n.c.
1111 1011 1-------   W --------           n.c.
1111 11xx xxxxxxxx R/W xxxxxxxx MCRAM     RAM shared with MCU


CPU #2

Address          Dir Data     Name      Description
---------------- --- -------- --------- -----------------------
0xxxxxxxxxxxxxxx R   xxxxxxxx ROM 37    program ROM
111xxxxxxxxxxxxx R/W xxxxxxxx WORK      RAM shared with CPU #1 [1]

[1] The last 2kB could be used exclusively by this CPU, but they are not used at all.


Sound CPU

Address          Dir Data     Name      Description
---------------- --- -------- --------- -----------------------
0xxxxxxxxxxxxxxx R   xxxxxxxx ROM 46    program ROM
1000xxxxxxxxxxxx R/W xxxxxxxx RAM 47    work RAM
1001-----------x R/W xxxxxxxx FMA       YM2203
1010-----------x R/W xxxxxxxx FMB       YM3526
1011----------00 R   xxxxxxxx           command from CPU #1
1011----------01 R   -------x           message pending from sound CPU to CPU #1
1011----------01 R   ------x-           message pending from CPU #1 to sound CPU
1011----------10 R                      n.c.
1011----------11 R                      n.c.
1011----------00   W xxxxxxxx           answer to CPU #1
1011----------01   W --------           sound NMI enable
1011----------10   W --------           sound NMI disable
1011----------11   W                    n.c.
111------------- R   xxxxxxxx           space for diagnostic ROM?


****************************************************************************


Tokio
1986, Taito (Romstar license)

PCB Layout                                                                   G Pinout
----------                                                                   --------
                                                                   Component Side  Solder Side
Top Board                                                         ----------------|----------------
                                                                       Ground   1 | A  Ground
J1100069A CPU BOARD                                                 Video Red   2 | B  Video Ground
K1100157A                                                         Video Green   3 | C  Video Blue
M4300053A (sticker)                                                Video Sync   4 | D
  |------------------------------------------------------|          Speaker +   5 | E  Speaker -
  |   VOL      TL074          YM2203              Z80A   |                Key   6 | F  Key
|-|                                                      |                      7 | H
|     MB3731  PC010SA                      A71_07.IC10   |            Coin Sw   8 | J
|H                                                       |         Coin Meter   9 | K
|     TL7700                                      2016   |                     10 | L
|-|                                                      |            Service  11 | M  Slam Switch
  |   MC68705P5                           A71_06-1.IC8  |-|          1P Start  12 | N  2P Start
|-| (A71_24.IC57)                                       | |                    13 | P
|                                           A71_05.IC7  | |                    14 | R
|                                                       | |          1P Right  15 | S  2P Right
|                                           A71_04.IC6  | |          1P Left   16 | T  2P Left
|   PC030CM                   PAL                       | |                    17 | U
|                                         A71_28-1.IC5  | |                    18 | V
|G                                                      | |                    19 | W
|                                         A71_27-1.IC4  | |                    20 | X
|                                                       | |           1P Fire  21 | Y  2P Fire
|                                                       | |                    22 | Z
|                                                 Z80B  | |
|-|                                                     |-|
  |                                                      |                   H Pinout
  |                    2016                       Z80B   |                   --------
  |                                                      |                   1   Ground
  |                    2016                              |                   2   Ground
  |                                         A71_01.IC1   |                   3   Ground
  |   DSWB(8) DSWA(8)  2016                              |                   4   Ground
  |------------------------------------------------------|                   5   +5VDC
Notes:                                                                       6   +5VDC
        H - 12-pin Connector for Power Input                                 7   +5VDC
        G - 22-Way Edge Connector                                            8   -5VDC
      PAL - MMI PAL16L8B stamped 'A71-26' (DIP20)                            9   +12VDC
  PC030CM - Taito Custom Ceramic IC, possibly contains a smt logic IC,       10  Key
            smt resistors and smt capacitors (SIP20)                         11  +12VDC
  PC010SA - Taito Custom Ceramic IC, possibly contains                       12  +12VDC
            smt resistors and smt capacitors, sound DAC (SIP14)
   MB3731 - Fujitsu MB3731 18W Power Amplifier (SIP12)
   TL7700 - Texas Instruments TL7700 Supply-Voltage Supervisor/Power-On Reset IC (DIP8)
MC68705P5 - Motorola MC68705P5 Microcontroller with 2K Internal EPROM,
            clock input 3.000MHz [24/8] (DIP28)
     2016 - Toshiba TMM2016BP-10 2K x8 SRAM (DIP24)
     Z80A - Zilog Z8400APS Z80A CPU, clock input 3.000MHz [24/8] (DIP40)
     Z80B - Zilog Z8400BPS Z80B CPU, clock input 6.000MHz [24/4] (DIP40)
   YM2203 - Yamaha YM2203 Sound Chip, clock input 3.000MHz [24/8] (DIP40)
    VSync - 60Hz

     ROMs - (All EPROMs are 27C256)
            A71_07.IC10    Sound CPU Program

            A71_06-1.IC8 \
            A71_05.IC7   |
            A71_04.IC6   | Main CPU Program
            A71_28-1.IC5 |
            A71_27-1.IC4 /

            A71_01.IC1     Sub CPU Program

            A71_24.IC57    68705 Microcontroller Program



Bottom Board

J1100070A VIDEO BOARD
K1100158A
K1100172A (sticker)
  |------------------------------------------------------|                   T Pinout
  |                                     24MHz            |                   --------
  |                                                      |         Component Side  Solder Side
  |                                     2018             |        ----------------|-----------
  |                                     2018             |             Ground   1 | A  Ground
  |                     A71_25.IC41                      |             Ground   2 | B  Ground
  |                                     2018             |             Ground   3 | C  Ground
  |                                     2018            |-|            Ground   4 | D  Ground
  |                                                     | |                     5 | E
|-|                                                     | |                     6 | F
|                                                       | |                     7 | H
|    A71_08.IC12  A71_16.IC30                           | |                     8 | J
|                                                       | |                     9 | K
|T   A71_09.IC13  A71_17.IC31                           | |                    10 | L
|                                                       | |                    11 | M
|    A71_10.IC14  A71_18.IC32                           | |                    12 | N
|                                                       | |                    13 | P
|    A71_11.IC15  A71_19.IC33                           | |                    14 | R
|-|                                     2018            | |               +5V  15 | S  +5V
  |  A71_12.IC16  A71_20.IC34           2018            |-|               +5V  16 | T  +5V
  |                                                      |                +5V  17 | U  +5V
  |  A71_13.IC17  A71_21.IC35           2018             |                +5V  18 | V  +5V
  |                                     2018             |
  |  A71_14.IC18  A71_22.IC36           PC040DA          |
  |                                     PC040DA          |
  |  A71_15.IC19  A71_23.IC37           PC040DA          |
  |------------------------------------------------------|
Notes:
        T - 36-Way Edge Connector
  PC040DA - Taito Custom Ceramic IC, Video DAC (SIP19)
     2018 - Toshiba TMM2018D-45 2K x8 SRAM (DIP24)

     ROMs -
            A71_25.IC41    MMI 63S141 Bipolar PROM (DIP16)
            All EPROMs are 27C256


****************************************************************************


Notes:
- The coin inputs are handled by a custom called PC030. It would be responsible of
  handling the coin counters.
- There is a weird dip switch in Bubble Bobble (SWB #7). When it is on, the game
  takes the player score and the level number (increased by 1) and writes them,
  byte by byte, to $F7FE and $F7FF ($F7FF receives the same data but with the
  bit order reversed). After doing that, it sometimes hangs because it expects
  the value at $F7FF to change.
  This is done by routines $0F26 (player 1) and $0F74 (player 2).
  Frankly I don't know what this could be. The schematics don't show anything
  special there. A debug feature seems unlikely - why care about the score?
  Could it be provision for some kind of externally controlled redemption scheme?
- "Attract Sound" in Tokio is a very relative term - it just plays a very short
  sound every four rounds of demo play.

TODO:
- the Bubble Bobble MCU is actually an MC6801U4, which has additional features like
    internal timers (similar to the HD63701). I've just mapped the I/O ports since
    that's the only thing required for normal operation, but the program does
    use some of the additional features in its special "test" mode.
- tokio: sound support is probably incomplete. There are a couple of unknown
  accesses done by the sound CPU to the YM2203 I/O ports. At the very least, there
  could be some filters.

 There are also Bubble Bobble bootlegs with a P8749H MCU, however the MCU
 is protected against reading and the main code only differs by 1 byte from
 Bubble Bobble.  If the MCU were to be dumped that would also make for
 interesting comparisons.

***************************************************************************/

#include "emu.h"
#include "includes/bublbobl.h"

#include "cpu/m6800/m6801.h"
#include "cpu/z80/z80.h"
#include "machine/watchdog.h"
#include "sound/2203intf.h"
#include "sound/3526intf.h"
#include "screen.h"
#include "speaker.h"


#define MAIN_XTAL   XTAL(24'000'000)


/*************************************
 *
 *  Address maps
 *
 *************************************/
void bublbobl_state::common_maincpu_map(address_map &map)
{
	map(0x0000, 0x7fff).rom();
	map(0x8000, 0xbfff).bankr("bank1");
	map(0xc000, 0xdcff).ram().share("videoram");
	map(0xdd00, 0xdfff).ram().share("objectram");
	map(0xe000, 0xf7ff).ram().share("share1");
	map(0xf800, 0xf9ff).ram().w(m_palette, FUNC(palette_device::write8)).share("palette");
}

void bublbobl_state::bublbobl_maincpu_map(address_map &map)
{
	common_maincpu_map(map);
	map(0xfa00, 0xfa00).mirror(0x007c).r(m_sound_to_main, FUNC(generic_latch_8_device::read)).w(m_main_to_sound, FUNC(generic_latch_8_device::write));
	map(0xfa01, 0xfa01).mirror(0x007c).r(FUNC(bublbobl_state::common_sound_semaphores_r));
	map(0xfa03, 0xfa03).mirror(0x007c).w(FUNC(bublbobl_state::bublbobl_soundcpu_reset_w));
	map(0xfa80, 0xfa80).mirror(0x007f).w("watchdog", FUNC(watchdog_timer_device::reset_w));
	map(0xfb00, 0xfb00).mirror(0x003f).w(FUNC(bublbobl_state::bublbobl_nmitrigger_w));
	map(0xfb40, 0xfb40).mirror(0x003f).w(FUNC(bublbobl_state::bublbobl_bankswitch_w));
	map(0xfc00, 0xffff).ram().share("mcu_sharedram");
}

void bublbobl_state::subcpu_map(address_map &map)
{
	map(0x0000, 0x7fff).rom();
	map(0xe000, 0xf7ff).ram().share("share1");
}

/* Sound cpu address map
           |           |           |
15 14 13 12 11 10  9  8  7  6  5  4  3  2  1  0
 0  *  *  *  *  *  *  *  *  *  *  *  *  *  *  *  R  ROM (27256 or 27128@ic46)
 1  *  *  *                                      decoded by 74ls138@ic48
 1  0  0  0  *  *  *  *  *  *  *  *  *  *  *  *  RW RAM (first half of 6264@ic37[1])
 1  0  0  1  x  x  x  x  x  x  x  x  x  x  x  *  RW YM2203 OPM chip
 1  0  1  0  x  x  x  x  x  x  x  x  x  x  x  *  RW YM3526 OPL chip
 1  0  1  1                                *  *  decoded by 74ls155@ic33
 1  0  1  1  x  x  x  x  x  x  x  x  x  x  0  0  R maincpu_to_sound latch 74ls374 @ic24 and clear maincpu_has_written semaphore
 1  0  1  1  x  x  x  x  x  x  x  x  x  x  0  0  W sound_to_maincpu latch 74ls374 @ic25 and set sound_has_written semaphore
 1  0  1  1  x  x  x  x  x  x  x  x  x  x  0  1  R read semaphores in d0 and d1
 1  0  1  1  x  x  x  x  x  x  x  x  x  x  0  1  W set latch to enable sound cpu nmi on maincpu_has_written semaphore active
 1  0  1  1  x  x  x  x  x  x  x  x  x  x  1  x  R OPEN BUS
 1  0  1  1  x  x  x  x  x  x  x  x  x  x  1  0  W clear latch to disable sound cpu nmi on maincpu_has_written semaphore active
 1  0  1  1  x  x  x  x  x  x  x  x  x  x  1  1  RW OPEN BUS
 1  0  1  1  x  x  x  x  x  x  x  x  x  x  x  0  RW sound latch[2]
 1  1  x  x  x  x  x  x  x  x  x  x  x  x  x  x  OPEN BUS
(1  1  *  *  *  *  *  *  *  *  *  *  *  *  *  *  R  DIAGNOSTIC ROM[4])
   [1] Technicaly A12 is connected to the 6264 SRAM too, but the 74ls138 disables the SRAM when A12 is high, so only half is usable
   [4] While normally not populated (or even present? not shown on the schematic at all? possibly a holdover from tokio?)
       the sound code probes for a ROM here, and will use it if found.
Sound cpu semaphores are both active low:
 74ls74@ic9 [1/2] 'sound_has_written', appears on d0
 74ls74@ic10 [2/2] 'maincpu_has_written', appears on d1
*/
void bublbobl_state::sound_map(address_map &map)
{
	map(0x0000, 0x7fff).rom();
	map(0x8000, 0x8fff).ram();
	map(0x9000, 0x9001).mirror(0x0ffe).rw("ym2203", FUNC(ym2203_device::read), FUNC(ym2203_device::write));
	map(0xa000, 0xa001).mirror(0x0ffe).rw("ym3526", FUNC(ym3526_device::read), FUNC(ym3526_device::write));
	map(0xb000, 0xb000).mirror(0x0ffc).r(m_main_to_sound, FUNC(generic_latch_8_device::read)).w(m_sound_to_main, FUNC(generic_latch_8_device::write));
	map(0xb001, 0xb001).mirror(0x0ffc).r(FUNC(bublbobl_state::common_sound_semaphores_r)).w(m_soundnmi, FUNC(input_merger_device::in_set<0>));
	map(0xb002, 0xb002).mirror(0x0ffc).w(m_soundnmi, FUNC(input_merger_device::in_clear<0>));
	map(0xe000, 0xffff).rom(); // space for diagnostic ROM?
}

void bublbobl_state::mcu_map(address_map &map)
{
	map(0x0000, 0x0000).rw(FUNC(bublbobl_state::bublbobl_mcu_ddr1_r), FUNC(bublbobl_state::bublbobl_mcu_ddr1_w));
	map(0x0001, 0x0001).rw(FUNC(bublbobl_state::bublbobl_mcu_ddr2_r), FUNC(bublbobl_state::bublbobl_mcu_ddr2_w));
	map(0x0002, 0x0002).rw(FUNC(bublbobl_state::bublbobl_mcu_port1_r), FUNC(bublbobl_state::bublbobl_mcu_port1_w));
	map(0x0003, 0x0003).rw(FUNC(bublbobl_state::bublbobl_mcu_port2_r), FUNC(bublbobl_state::bublbobl_mcu_port2_w));
	map(0x0004, 0x0004).rw(FUNC(bublbobl_state::bublbobl_mcu_ddr3_r), FUNC(bublbobl_state::bublbobl_mcu_ddr3_w));
	map(0x0005, 0x0005).rw(FUNC(bublbobl_state::bublbobl_mcu_ddr4_r), FUNC(bublbobl_state::bublbobl_mcu_ddr4_w));
	map(0x0006, 0x0006).rw(FUNC(bublbobl_state::bublbobl_mcu_port3_r), FUNC(bublbobl_state::bublbobl_mcu_port3_w));
	map(0x0007, 0x0007).rw(FUNC(bublbobl_state::bublbobl_mcu_port4_r), FUNC(bublbobl_state::bublbobl_mcu_port4_w));
	map(0x0040, 0x00ff).ram();
	map(0xf000, 0xffff).rom();
}

void bublbobl_state::bootleg_map(address_map &map)
{
	common_maincpu_map(map);
	map(0xfa00, 0xfa00).mirror(0x007c).r(m_sound_to_main, FUNC(generic_latch_8_device::read)).w(m_main_to_sound, FUNC(generic_latch_8_device::write));
	map(0xfa01, 0xfa01).mirror(0x007c).r(FUNC(bublbobl_state::common_sound_semaphores_r));
	map(0xfa03, 0xfa03).mirror(0x007c).w(FUNC(bublbobl_state::bublbobl_soundcpu_reset_w));
	map(0xfa80, 0xfa80).mirror(0x007f).w("watchdog", FUNC(watchdog_timer_device::reset_w));
	map(0xfb00, 0xfb00).mirror(0x003f).w(FUNC(bublbobl_state::bublbobl_nmitrigger_w));
	map(0xfb40, 0xfb40).mirror(0x003f).w(FUNC(bublbobl_state::bublbobl_bankswitch_w));
	// above here is identical to non-bootleg
	map(0xfc00, 0xfcff).ram();
	map(0xfd00, 0xfdff).ram();
	map(0xfe00, 0xfe03).rw(FUNC(bublbobl_state::boblbobl_ic43_a_r), FUNC(bublbobl_state::boblbobl_ic43_a_w));
	map(0xfe80, 0xfe83).rw(FUNC(bublbobl_state::boblbobl_ic43_b_r), FUNC(bublbobl_state::boblbobl_ic43_b_w));
	map(0xff00, 0xff00).portr("DSW0");
	map(0xff01, 0xff01).portr("DSW1");
	map(0xff02, 0xff02).portr("IN0");
	map(0xff03, 0xff03).portr("IN1");
	map(0xff94, 0xff94).nopw(); // ???
	map(0xff98, 0xff98).nopw(); // ???
}


void bublbobl_state::tokio_map(address_map &map)
{
	common_maincpu_map(map);
	map(0xfa00, 0xfa00).w("watchdog", FUNC(watchdog_timer_device::reset_w));
	map(0xfa03, 0xfa03).portr("DSW0");
	map(0xfa04, 0xfa04).portr("DSW1");
	map(0xfa05, 0xfa05).portr("IN0");
	map(0xfa06, 0xfa06).portr("IN1");
	map(0xfa07, 0xfa07).portr("IN2");
	map(0xfa80, 0xfa80).w(FUNC(bublbobl_state::tokio_bankswitch_w));
	map(0xfb00, 0xfb00).w(FUNC(bublbobl_state::tokio_videoctrl_w));
	map(0xfb80, 0xfb80).w(FUNC(bublbobl_state::bublbobl_nmitrigger_w));
	map(0xfc00, 0xfc00).r(m_sound_to_main, FUNC(generic_latch_8_device::read)).w(m_main_to_sound, FUNC(generic_latch_8_device::write));
}

void bublbobl_state::tokio_map_mcu(address_map &map)
{
	tokio_map(map);
	map(0xfe00, 0xfe00).rw("bmcu", FUNC(taito68705_mcu_device::data_r), FUNC(taito68705_mcu_device::data_w));
}

void bublbobl_state::tokio_map_bootleg(address_map &map)
{
	tokio_map(map);
	map(0xfe00, 0xfe00).r(FUNC(bublbobl_state::tokiob_mcu_r));
}


void bublbobl_state::tokio_subcpu_map(address_map &map)
{
	map(0x0000, 0x7fff).rom();
	map(0x8000, 0x97ff).ram().share("share1");
}

void bublbobl_state::tokio_sound_map(address_map &map)
{
	map(0x0000, 0x7fff).rom();
	map(0x8000, 0x8fff).ram();
	map(0x9000, 0x9000).r(m_main_to_sound, FUNC(generic_latch_8_device::read)).w(m_sound_to_main, FUNC(generic_latch_8_device::write));
	map(0x9800, 0x9800).r(FUNC(bublbobl_state::common_sound_semaphores_r));
	map(0xa000, 0xa000).w(m_soundnmi, FUNC(input_merger_device::in_clear<0>));
	map(0xa800, 0xa800).w(m_soundnmi, FUNC(input_merger_device::in_set<0>));
	map(0xb000, 0xb001).rw("ym2203", FUNC(ym2203_device::read), FUNC(ym2203_device::write));
	map(0xe000, 0xffff).rom(); // space for diagnostic ROM?
}


/*************************************
 *
 *  Input ports
 *
 *************************************/

static INPUT_PORTS_START( bublbobl )
	PORT_START("IN0")
	PORT_BIT( 0x01, IP_ACTIVE_LOW, IPT_TILT )
	PORT_BIT( 0x02, IP_ACTIVE_LOW, IPT_SERVICE1 )
	PORT_BIT( 0x04, IP_ACTIVE_HIGH, IPT_COIN1 )
	PORT_BIT( 0x08, IP_ACTIVE_HIGH, IPT_COIN2 )
	PORT_BIT( 0x10, IP_ACTIVE_LOW, IPT_CUSTOM )    // output: coin lockout
	PORT_BIT( 0x20, IP_ACTIVE_LOW, IPT_CUSTOM )    // output: select 1-way or 2-way coin counter
	PORT_BIT( 0x40, IP_ACTIVE_LOW, IPT_CUSTOM )    // output: trigger IRQ on main CPU (jumper switchable to vblank)
	PORT_BIT( 0x80, IP_ACTIVE_LOW, IPT_CUSTOM )    // output: select read or write shared RAM

	PORT_START("DSW0")
	PORT_DIPNAME( 0x05, 0x04, "Mode" )                      PORT_DIPLOCATION("DSW-A:1,3")
	PORT_DIPSETTING(    0x04, "Game, English" )
	PORT_DIPSETTING(    0x05, "Game, Japanese" )
	PORT_DIPSETTING(    0x01, "Test (Grid and Inputs)" )
	PORT_DIPSETTING(    0x00, "Test (RAM and Sound)/Pause" )
	PORT_DIPNAME( 0x02, 0x02, DEF_STR( Flip_Screen ) )      PORT_DIPLOCATION("DSW-A:2")
	PORT_DIPSETTING(    0x02, DEF_STR( Off ) )
	PORT_DIPSETTING(    0x00, DEF_STR( On ) )
	PORT_DIPNAME( 0x08, 0x08, DEF_STR( Demo_Sounds ) )      PORT_DIPLOCATION("DSW-A:4")
	PORT_DIPSETTING(    0x00, DEF_STR( Off ) )
	PORT_DIPSETTING(    0x08, DEF_STR( On ) )
	PORT_DIPNAME( 0x30, 0x30, DEF_STR( Coin_A ) )           PORT_DIPLOCATION("DSW-A:5,6")
	PORT_DIPSETTING(    0x10, DEF_STR( 2C_1C ) )
	PORT_DIPSETTING(    0x30, DEF_STR( 1C_1C ) )
	PORT_DIPSETTING(    0x00, DEF_STR( 2C_3C ) )
	PORT_DIPSETTING(    0x20, DEF_STR( 1C_2C ) )
	PORT_DIPNAME( 0xc0, 0xc0, DEF_STR( Coin_B ) )           PORT_DIPLOCATION("DSW-A:7,8")
	PORT_DIPSETTING(    0x40, DEF_STR( 2C_1C ) )
	PORT_DIPSETTING(    0xc0, DEF_STR( 1C_1C ) )
	PORT_DIPSETTING(    0x00, DEF_STR( 2C_3C ) )
	PORT_DIPSETTING(    0x80, DEF_STR( 1C_2C ) )

	PORT_START("DSW1")
	PORT_DIPNAME( 0x03, 0x03, DEF_STR( Difficulty ) )       PORT_DIPLOCATION("DSW-B:1,2")
	PORT_DIPSETTING(    0x02, DEF_STR( Easy ) )
	PORT_DIPSETTING(    0x03, DEF_STR( Normal ) )
	PORT_DIPSETTING(    0x01, DEF_STR( Hard ) )
	PORT_DIPSETTING(    0x00, DEF_STR( Very_Hard ) )
	PORT_DIPNAME( 0x0c, 0x0c, DEF_STR( Bonus_Life ) )       PORT_DIPLOCATION("DSW-B:3,4")
	PORT_DIPSETTING(    0x08, "20K 80K 300K" )
	PORT_DIPSETTING(    0x0c, "30K 100K 400K" )
	PORT_DIPSETTING(    0x04, "40K 200K 500K" )
	PORT_DIPSETTING(    0x00, "50K 250K 500K" )
	// then more bonus lives at 1M 2M 3M 4M 5M - for all dip switch settings
	PORT_DIPNAME( 0x30, 0x30, DEF_STR( Lives ) )            PORT_DIPLOCATION("DSW-B:5,6")
	PORT_DIPSETTING(    0x10, "1" )
	PORT_DIPSETTING(    0x00, "2" )
	PORT_DIPSETTING(    0x30, "3" )
	PORT_DIPSETTING(    0x20, "5" )
	PORT_DIPNAME( 0x40, 0x40, DEF_STR( Unknown ) )          PORT_DIPLOCATION("DSW-B:7")
	PORT_DIPSETTING(    0x40, DEF_STR( Off ) )              // must be off (see notes)
	PORT_DIPSETTING(    0x00, DEF_STR( On ) )
	PORT_DIPNAME( 0x80, 0x80, "ROM Type" )                  PORT_DIPLOCATION("DSW-B:8")
	PORT_DIPSETTING(    0x80, "IC52=512kb, IC53=none" )     // will hang on startup if set to wrong type
	PORT_DIPSETTING(    0x00, "IC52=256kb, IC53=256kb" )

	PORT_START("IN1")
	PORT_BIT( 0x01, IP_ACTIVE_LOW, IPT_JOYSTICK_LEFT  ) PORT_2WAY
	PORT_BIT( 0x02, IP_ACTIVE_LOW, IPT_JOYSTICK_RIGHT ) PORT_2WAY
	PORT_BIT( 0x04, IP_ACTIVE_LOW, IPT_UNKNOWN ) // joy down, present on connector and readable
	PORT_BIT( 0x08, IP_ACTIVE_LOW, IPT_UNKNOWN ) // joy up, present on connector and readable
	PORT_BIT( 0x10, IP_ACTIVE_LOW, IPT_BUTTON2 )
	PORT_BIT( 0x20, IP_ACTIVE_LOW, IPT_BUTTON1 )
	PORT_BIT( 0x40, IP_ACTIVE_LOW, IPT_START1 )
	PORT_BIT( 0x80, IP_ACTIVE_LOW, IPT_UNKNOWN ) // tied to +5v

	PORT_START("IN2")
	PORT_BIT( 0x01, IP_ACTIVE_LOW, IPT_JOYSTICK_LEFT  ) PORT_2WAY PORT_PLAYER(2)
	PORT_BIT( 0x02, IP_ACTIVE_LOW, IPT_JOYSTICK_RIGHT ) PORT_2WAY PORT_PLAYER(2)
	PORT_BIT( 0x04, IP_ACTIVE_LOW, IPT_UNKNOWN ) // joy 2 down, present on connector and readable
	PORT_BIT( 0x08, IP_ACTIVE_LOW, IPT_UNKNOWN ) // joy 2 up, present on connector and readable
	PORT_BIT( 0x10, IP_ACTIVE_LOW, IPT_BUTTON2 ) PORT_PLAYER(2)
	PORT_BIT( 0x20, IP_ACTIVE_LOW, IPT_BUTTON1 ) PORT_PLAYER(2)
	PORT_BIT( 0x40, IP_ACTIVE_LOW, IPT_START2 )
	PORT_BIT( 0x80, IP_ACTIVE_LOW, IPT_UNKNOWN ) // tied to +5v
INPUT_PORTS_END

static INPUT_PORTS_START( boblbobl )
	PORT_START("DSW0")
	PORT_DIPNAME( 0x05, 0x04, "Mode" )
	PORT_DIPSETTING(    0x04, "Game, English" )
	PORT_DIPSETTING(    0x05, "Game, Japanese" )
	PORT_DIPSETTING(    0x01, "Test (Grid and Inputs)" )
	PORT_DIPSETTING(    0x00, "Test (RAM and Sound)" )
	PORT_DIPNAME( 0x02, 0x02, DEF_STR( Flip_Screen ) )
	PORT_DIPSETTING(    0x02, DEF_STR( Off ) )
	PORT_DIPSETTING(    0x00, DEF_STR( On ) )
	PORT_DIPNAME( 0x08, 0x08, DEF_STR( Demo_Sounds ) )
	PORT_DIPSETTING(    0x00, DEF_STR( Off ) )
	PORT_DIPSETTING(    0x08, DEF_STR( On ) )
	PORT_DIPNAME( 0x30, 0x30, DEF_STR( Coin_A ) )
	PORT_DIPSETTING(    0x10, DEF_STR( 2C_1C ) )
	PORT_DIPSETTING(    0x30, DEF_STR( 1C_1C ) )
	PORT_DIPSETTING(    0x00, DEF_STR( 2C_3C ) )
	PORT_DIPSETTING(    0x20, DEF_STR( 1C_2C ) )
	PORT_DIPNAME( 0xc0, 0xc0, DEF_STR( Coin_B ) )
	PORT_DIPSETTING(    0x40, DEF_STR( 2C_1C ) )
	PORT_DIPSETTING(    0xc0, DEF_STR( 1C_1C ) )
	PORT_DIPSETTING(    0x00, DEF_STR( 2C_3C ) )
	PORT_DIPSETTING(    0x80, DEF_STR( 1C_2C ) )

	PORT_START("DSW1")
	PORT_DIPNAME( 0x03, 0x03, DEF_STR( Difficulty ) )
	PORT_DIPSETTING(    0x02, DEF_STR( Easy ) )
	PORT_DIPSETTING(    0x03, DEF_STR( Normal ) )
	PORT_DIPSETTING(    0x01, DEF_STR( Hard ) )
	PORT_DIPSETTING(    0x00, DEF_STR( Very_Hard ) )
	PORT_DIPNAME( 0x0c, 0x0c, DEF_STR( Bonus_Life ) )
	PORT_DIPSETTING(    0x08, "20K 80K 300K" )
	PORT_DIPSETTING(    0x0c, "30K 100K 400K" )
	PORT_DIPSETTING(    0x04, "40K 200K 500K" )
	PORT_DIPSETTING(    0x00, "50K 250K 500K" )
	// then more bonus lives at 1M 2M 3M 4M 5M - for all dip switch settings
	PORT_DIPNAME( 0x30, 0x30, DEF_STR( Lives ) )
	PORT_DIPSETTING(    0x10, "1" )
	PORT_DIPSETTING(    0x00, "2" )
	PORT_DIPSETTING(    0x30, "3" )
	PORT_DIPSETTING(    0x20, "5" )
	PORT_DIPNAME( 0xc0, 0x00, "Monster Speed" )
	PORT_DIPSETTING(    0x00, DEF_STR( Normal ) )
	PORT_DIPSETTING(    0x40, DEF_STR( Medium ) )
	PORT_DIPSETTING(    0x80, DEF_STR( High ) )
	PORT_DIPSETTING(    0xc0, DEF_STR( Very_High ) )

	PORT_START("IN0")
	PORT_BIT( 0x01, IP_ACTIVE_LOW, IPT_JOYSTICK_LEFT  ) PORT_2WAY
	PORT_BIT( 0x02, IP_ACTIVE_LOW, IPT_JOYSTICK_RIGHT ) PORT_2WAY
	PORT_BIT( 0x04, IP_ACTIVE_HIGH, IPT_COIN2 ) PORT_IMPULSE(1)
	PORT_BIT( 0x08, IP_ACTIVE_HIGH, IPT_COIN1 ) PORT_IMPULSE(1)
	PORT_BIT( 0x10, IP_ACTIVE_LOW, IPT_BUTTON2 )
	PORT_BIT( 0x20, IP_ACTIVE_LOW, IPT_BUTTON1 )
	PORT_BIT( 0x40, IP_ACTIVE_LOW, IPT_START1 )
	PORT_BIT( 0x80, IP_ACTIVE_LOW, IPT_UNKNOWN )

	PORT_START("IN1")
	PORT_BIT( 0x01, IP_ACTIVE_LOW, IPT_JOYSTICK_LEFT  ) PORT_2WAY PORT_PLAYER(2)
	PORT_BIT( 0x02, IP_ACTIVE_LOW, IPT_JOYSTICK_RIGHT ) PORT_2WAY PORT_PLAYER(2)
	PORT_BIT( 0x04, IP_ACTIVE_LOW, IPT_TILT ) // ???
	PORT_BIT( 0x08, IP_ACTIVE_LOW, IPT_SERVICE1 )
	PORT_BIT( 0x10, IP_ACTIVE_LOW, IPT_BUTTON2 ) PORT_PLAYER(2)
	PORT_BIT( 0x20, IP_ACTIVE_LOW, IPT_BUTTON1 ) PORT_PLAYER(2)
	PORT_BIT( 0x40, IP_ACTIVE_LOW, IPT_START2 )
	PORT_BIT( 0x80, IP_ACTIVE_LOW, IPT_UNKNOWN )
INPUT_PORTS_END


static INPUT_PORTS_START( boblcave )
	PORT_INCLUDE( boblbobl )

	PORT_MODIFY( "DSW1" ) // not monster speed on this, causes startup hangs just like original bublbobl
	PORT_DIPNAME( 0x40, 0x40, DEF_STR( Unknown ) )          PORT_DIPLOCATION("DSW-B:7")
	PORT_DIPSETTING(    0x40, DEF_STR( Off ) )              // must be off (see notes)
	PORT_DIPSETTING(    0x00, DEF_STR( On ) )
	PORT_DIPNAME( 0x80, 0x80, "ROM Type" )                  PORT_DIPLOCATION("DSW-B:8")
	PORT_DIPSETTING(    0x80, "IC52=512kb, IC53=none" )     // will hang on startup if set to wrong type
	PORT_DIPSETTING(    0x00, "IC52=256kb, IC53=256kb" )
INPUT_PORTS_END

static INPUT_PORTS_START( sboblboblb )
	PORT_INCLUDE( boblbobl )

	PORT_MODIFY( "DSW0" )
	PORT_DIPNAME( 0x01, 0x00, "Game" )
	PORT_DIPSETTING(    0x01, "Bobble Bobble" )
	PORT_DIPSETTING(    0x00, "Super Bobble Bobble" )
	PORT_SERVICE( 0x04, IP_ACTIVE_LOW )

	PORT_MODIFY( "DSW1" )
	PORT_DIPNAME( 0x30, 0x30, DEF_STR( Lives ) )
	PORT_DIPSETTING(    0x10, "1" )
	PORT_DIPSETTING(    0x00, "2" )
	PORT_DIPSETTING(    0x30, "3" )
	PORT_DIPSETTING(    0x20, "100 (Cheat)")
INPUT_PORTS_END

static INPUT_PORTS_START( sboblbobl )
	PORT_INCLUDE( sboblboblb )

	PORT_MODIFY( "IN0" )
	PORT_BIT( 0x04, IP_ACTIVE_LOW, IPT_COIN2 ) PORT_IMPULSE(1)
	PORT_BIT( 0x08, IP_ACTIVE_LOW, IPT_COIN1 ) PORT_IMPULSE(1)
	PORT_BIT( 0x80, IP_ACTIVE_HIGH, IPT_UNKNOWN ) // Must be low or the game freezes!
INPUT_PORTS_END

// default to 'Dream Land' not 'Super Dream Land'
static INPUT_PORTS_START( dland )
	PORT_INCLUDE( boblbobl )

	PORT_MODIFY( "DSW0" )
	PORT_DIPNAME( 0x01, 0x01, "Game" )
	PORT_DIPSETTING(    0x01, "Dream Land" )
	PORT_DIPSETTING(    0x00, "Super Dream Land" )
	PORT_SERVICE( 0x04, IP_ACTIVE_LOW )

	PORT_MODIFY( "DSW1" )
	PORT_DIPNAME( 0x30, 0x30, DEF_STR( Lives ) )
	PORT_DIPSETTING(    0x10, "1" )
	PORT_DIPSETTING(    0x00, "2" )
	PORT_DIPSETTING(    0x30, "3" )
	PORT_DIPSETTING(    0x20, "100 (Cheat)")
INPUT_PORTS_END

static INPUT_PORTS_START( tokio_base )
	PORT_START("DSW0")
	PORT_DIPNAME( 0x01, 0x00, DEF_STR( Cabinet ) )      PORT_DIPLOCATION("SW A:1")
	PORT_DIPSETTING(    0x00, DEF_STR( Upright ) )
	PORT_DIPSETTING(    0x01, DEF_STR( Cocktail ) )
	PORT_DIPNAME( 0x02, 0x02, DEF_STR( Flip_Screen ) )  PORT_DIPLOCATION("SW A:2")
	PORT_DIPSETTING(    0x02, DEF_STR( Off ) )
	PORT_DIPSETTING(    0x00, DEF_STR( On ) )
	PORT_SERVICE_DIPLOC( 0x04, IP_ACTIVE_LOW, "SW A:3" )
	PORT_DIPNAME( 0x08, 0x08, DEF_STR( Demo_Sounds ) )  PORT_DIPLOCATION("SW A:4")
	PORT_DIPSETTING(    0x00, DEF_STR( Off ) )
	PORT_DIPSETTING(    0x08, DEF_STR( On ) )
	PORT_DIPNAME( 0x30, 0x30, DEF_STR( Coin_A ) )       PORT_DIPLOCATION("SW A:5,6")
	PORT_DIPSETTING(    0x10, DEF_STR( 2C_1C ) )
	PORT_DIPSETTING(    0x30, DEF_STR( 1C_1C ) )
	PORT_DIPSETTING(    0x00, DEF_STR( 2C_3C ) )
	PORT_DIPSETTING(    0x20, DEF_STR( 1C_2C ) )
	PORT_DIPNAME( 0xc0, 0xc0, DEF_STR( Coin_B ) )       PORT_DIPLOCATION("SW A:7,8")
	PORT_DIPSETTING(    0x40, DEF_STR( 2C_1C ) )
	PORT_DIPSETTING(    0xc0, DEF_STR( 1C_1C ) )
	PORT_DIPSETTING(    0x00, DEF_STR( 2C_3C ) )
	PORT_DIPSETTING(    0x80, DEF_STR( 1C_2C ) )

	PORT_START("DSW1")
	PORT_DIPNAME( 0x01, 0x00, "Enemies" )               PORT_DIPLOCATION("SW B:1")
	PORT_DIPSETTING(    0x01, "Few (Easy)" )
	PORT_DIPSETTING(    0x00, "Many (Hard)" )
	PORT_DIPNAME( 0x02, 0x02, "Enemy Shots" )           PORT_DIPLOCATION("SW B:2")
	PORT_DIPSETTING(    0x02, "Few (Easy)" )
	PORT_DIPSETTING(    0x00, "Many (Hard)" )
	PORT_DIPNAME( 0x0c, 0x0c, DEF_STR( Bonus_Life ) )   PORT_DIPLOCATION("SW B:3,4")
	PORT_DIPSETTING(    0x0c, "100K 400K" )
	PORT_DIPSETTING(    0x08, "200K 400K" )
	PORT_DIPSETTING(    0x04, "300K 400K" )
	PORT_DIPSETTING(    0x00, "400K 400K" )
	PORT_DIPNAME( 0x30, 0x30, DEF_STR( Lives ) )        PORT_DIPLOCATION("SW B:5,6")
	PORT_DIPSETTING(    0x30, "3" )
	PORT_DIPSETTING(    0x20, "4" )
	PORT_DIPSETTING(    0x10, "5" )
	PORT_DIPSETTING(    0x00, "99 (Cheat)") // 6 in original version
	PORT_DIPUNUSED_DIPLOC( 0x40, IP_ACTIVE_LOW, "SW B:7" )
	PORT_DIPNAME( 0x80, 0x00, DEF_STR( Language ) )     PORT_DIPLOCATION("SW B:8")
	PORT_DIPSETTING(    0x00, DEF_STR( English ) )
	PORT_DIPSETTING(    0x80, DEF_STR( Japanese ) )

	PORT_START("IN0")
	PORT_BIT( 0x01, IP_ACTIVE_LOW, IPT_TILT )
	PORT_BIT( 0x02, IP_ACTIVE_LOW, IPT_SERVICE1 )
	PORT_BIT( 0x04, IP_ACTIVE_HIGH, IPT_COIN1 ) PORT_IMPULSE(1)
	PORT_BIT( 0x08, IP_ACTIVE_HIGH, IPT_COIN2 ) PORT_IMPULSE(1)
	PORT_BIT( 0x10, IP_ACTIVE_HIGH, IPT_CUSTOM ) // see INPUT_PORTS_START( tokio )
	PORT_BIT( 0x20, IP_ACTIVE_HIGH, IPT_CUSTOM ) // see INPUT_PORTS_START( tokio )
	PORT_BIT( 0x40, IP_ACTIVE_LOW, IPT_UNKNOWN )
	PORT_BIT( 0x80, IP_ACTIVE_LOW, IPT_UNKNOWN )

	PORT_START("IN1")
	PORT_BIT( 0x01, IP_ACTIVE_LOW, IPT_JOYSTICK_LEFT  ) PORT_8WAY
	PORT_BIT( 0x02, IP_ACTIVE_LOW, IPT_JOYSTICK_RIGHT ) PORT_8WAY
	PORT_BIT( 0x04, IP_ACTIVE_LOW, IPT_JOYSTICK_DOWN  ) PORT_8WAY
	PORT_BIT( 0x08, IP_ACTIVE_LOW, IPT_JOYSTICK_UP    ) PORT_8WAY
	PORT_BIT( 0x10, IP_ACTIVE_LOW, IPT_BUTTON2 )
	PORT_BIT( 0x20, IP_ACTIVE_LOW, IPT_BUTTON1 )
	PORT_BIT( 0x40, IP_ACTIVE_LOW, IPT_START1 )
	PORT_BIT( 0x80, IP_ACTIVE_LOW, IPT_UNKNOWN )

	PORT_START("IN2")
	PORT_BIT( 0x01, IP_ACTIVE_LOW, IPT_JOYSTICK_LEFT  ) PORT_8WAY PORT_COCKTAIL
	PORT_BIT( 0x02, IP_ACTIVE_LOW, IPT_JOYSTICK_RIGHT ) PORT_8WAY PORT_COCKTAIL
	PORT_BIT( 0x04, IP_ACTIVE_LOW, IPT_JOYSTICK_DOWN  ) PORT_8WAY PORT_COCKTAIL
	PORT_BIT( 0x08, IP_ACTIVE_LOW, IPT_JOYSTICK_UP    ) PORT_8WAY PORT_COCKTAIL
	PORT_BIT( 0x10, IP_ACTIVE_LOW, IPT_BUTTON2 ) PORT_COCKTAIL
	PORT_BIT( 0x20, IP_ACTIVE_LOW, IPT_BUTTON1 ) PORT_COCKTAIL
	PORT_BIT( 0x40, IP_ACTIVE_LOW, IPT_START2 )
	PORT_BIT( 0x80, IP_ACTIVE_LOW, IPT_UNKNOWN )
INPUT_PORTS_END

static INPUT_PORTS_START( tokio )
	PORT_INCLUDE( tokio_base )

	PORT_MODIFY("IN0")
	PORT_BIT( 0x10, IP_ACTIVE_LOW, IPT_CUSTOM ) PORT_READ_LINE_DEVICE_MEMBER("bmcu", taito68705_mcu_device, host_semaphore_r)
	PORT_BIT( 0x20, IP_ACTIVE_LOW, IPT_CUSTOM ) PORT_READ_LINE_DEVICE_MEMBER("bmcu", taito68705_mcu_device, mcu_semaphore_r)
INPUT_PORTS_END

static INPUT_PORTS_START( bublboblp )
	PORT_INCLUDE( tokio_base )

	PORT_MODIFY("DSW0")
	PORT_DIPNAME( 0x01, 0x00, DEF_STR( Language ) )     PORT_DIPLOCATION("SW A:1")
	PORT_DIPSETTING(    0x00, DEF_STR( English ) )
	PORT_DIPSETTING(    0x01, DEF_STR( Japanese ) )
	PORT_DIPNAME( 0x02, 0x02, DEF_STR( Flip_Screen ) )  PORT_DIPLOCATION("SW A:2")
	PORT_DIPSETTING(    0x02, DEF_STR( Off ) )
	PORT_DIPSETTING(    0x00, DEF_STR( On ) )
	PORT_SERVICE_DIPLOC( 0x04, IP_ACTIVE_LOW, "SW A:3" )
	PORT_DIPNAME( 0x08, 0x08, DEF_STR( Demo_Sounds ) )  PORT_DIPLOCATION("SW A:4")
	PORT_DIPSETTING(    0x00, DEF_STR( Off ) )
	PORT_DIPSETTING(    0x08, DEF_STR( On ) )
	PORT_DIPNAME( 0x30, 0x30, DEF_STR( Coin_A ) )       PORT_DIPLOCATION("SW A:5,6")
	PORT_DIPSETTING(    0x10, DEF_STR( 2C_3C ) )
	PORT_DIPSETTING(    0x30, DEF_STR( 1C_1C ) )
	PORT_DIPSETTING(    0x00, DEF_STR( 2C_1C ) )
	PORT_DIPSETTING(    0x20, DEF_STR( 1C_2C ) )
	PORT_DIPNAME( 0xc0, 0xc0, DEF_STR( Coin_B ) )       PORT_DIPLOCATION("SW A:7,8")
	PORT_DIPSETTING(    0x40, DEF_STR( 2C_3C ) )
	PORT_DIPSETTING(    0xc0, DEF_STR( 1C_1C ) )
	PORT_DIPSETTING(    0x00, DEF_STR( 2C_1C ) )
	PORT_DIPSETTING(    0x80, DEF_STR( 1C_2C ) )

	PORT_MODIFY("DSW1")
	PORT_DIPNAME( 0x03, 0x03, DEF_STR( Difficulty ) )       PORT_DIPLOCATION("DSW-B:1,2") // code is present to read this and look up a table per level, but unclear if it actually works
	PORT_DIPSETTING(    0x02, DEF_STR( Easy ) )
	PORT_DIPSETTING(    0x03, DEF_STR( Normal ) )
	PORT_DIPSETTING(    0x01, DEF_STR( Hard ) )
	PORT_DIPSETTING(    0x00, DEF_STR( Very_Hard ) )
	PORT_DIPNAME( 0x0c, 0x0c, DEF_STR( Bonus_Life ) )       PORT_DIPLOCATION("DSW-B:3,4")
	PORT_DIPSETTING(    0x08, "20K 80K 300K" )
	PORT_DIPSETTING(    0x0c, "30K 100K 400K" )
	PORT_DIPSETTING(    0x04, "40K 200K 500K" )
	PORT_DIPSETTING(    0x00, "50K 250K 500K" )
	// then more bonus lives at 1M 2M 3M 4M 5M - for all dip switch settings
	PORT_DIPNAME( 0x30, 0x30, DEF_STR( Lives ) )            PORT_DIPLOCATION("DSW-B:5,6")
	PORT_DIPSETTING(    0x10, "1" )
	PORT_DIPSETTING(    0x00, "2" )
	PORT_DIPSETTING(    0x30, "3" )
	PORT_DIPSETTING(    0x20, "5" )
	PORT_DIPNAME( 0x40, 0x40, "Edit Mode" )                 PORT_DIPLOCATION("DSW-B:7")
	PORT_DIPSETTING(    0x40, DEF_STR( Off ) )
	PORT_DIPSETTING(    0x00, DEF_STR( On ) )
	PORT_DIPNAME( 0x80, 0x80, DEF_STR( Unknown ) )          PORT_DIPLOCATION("DSW-B:8")
	PORT_DIPSETTING(    0x80, DEF_STR( Off ) )
	PORT_DIPSETTING(    0x00, DEF_STR( On ) )
INPUT_PORTS_END

/*************************************
 *
 *  Graphics definitions
 *
 *************************************/

static const gfx_layout charlayout =
{
	8, 8,
	RGN_FRAC(1,2),
	4,
	{ 0, 4, RGN_FRAC(1,2), RGN_FRAC(1,2)+4 },
	{ 3, 2, 1, 0, 8+3, 8+2, 8+1, 8+0 },
	{ 0*16, 1*16, 2*16, 3*16, 4*16, 5*16, 6*16, 7*16 },
	16*8
};

static GFXDECODE_START( gfx_bublbobl )
	GFXDECODE_ENTRY( "gfx1", 0, charlayout, 0, 16 )
GFXDECODE_END


/*************************************
 *
 *  Machine driver
 *
 *************************************/

MACHINE_START_MEMBER(bublbobl_state,common)
{
	m_sreset_old = CLEAR_LINE;
	save_item(NAME(m_video_enable));
	save_item(NAME(m_sreset_old));
}

MACHINE_RESET_MEMBER(bublbobl_state,common) // things common on both tokio and bubble bobble hw
{
	m_soundnmi->in_w<0>(0); // clear sound NMI stuff
	m_soundnmi->in_w<1>(0);
	m_subcpu->set_input_line(INPUT_LINE_NMI, CLEAR_LINE); // if a subcpu nmi is active (extremely remote chance), it is cleared
	if (!m_sreset_old)
	{
		// /SRESET is pulsed
		common_sreset(ASSERT_LINE);
		common_sreset(CLEAR_LINE);
	}
}


MACHINE_START_MEMBER(bublbobl_state,tokio)
{
	MACHINE_START_CALL_MEMBER(common);
}

MACHINE_RESET_MEMBER(bublbobl_state,tokio)
{
	MACHINE_RESET_CALL_MEMBER(common);
	tokio_bankswitch_w(0x00); // force a bankswitch write of all zeroes, as /RESET clears the latch
	tokio_videoctrl_w(0x00); // TODO: does /RESET clear this the same as above? probably yes, needs tracing...
}

void bublbobl_state::tokio(machine_config &config)
{
	/* basic machine hardware */
	Z80(config, m_maincpu, MAIN_XTAL/4); // 6 MHz
	m_maincpu->set_addrmap(AS_PROGRAM, &bublbobl_state::tokio_map_mcu);
	m_maincpu->set_vblank_int("screen", FUNC(bublbobl_state::irq0_line_hold));

	Z80(config, m_subcpu, MAIN_XTAL/4); // 6 MHz
	m_subcpu->set_addrmap(AS_PROGRAM, &bublbobl_state::tokio_subcpu_map);
	m_subcpu->set_vblank_int("screen", FUNC(bublbobl_state::irq0_line_hold));

	Z80(config, m_audiocpu, MAIN_XTAL/8); // 3 MHz
	m_audiocpu->set_addrmap(AS_PROGRAM, &bublbobl_state::tokio_sound_map); // NMIs are triggered by the main CPU, IRQs are triggered by the YM2203

	TAITO68705_MCU(config, "bmcu", MAIN_XTAL/8); // 3 Mhz

	config.set_perfect_quantum(m_maincpu); // is this necessary?

	WATCHDOG_TIMER(config, "watchdog").set_vblank_count("screen", 128); // 74LS393, counts 128 vblanks before firing watchdog; same circuit as taitosj uses

	MCFG_MACHINE_START_OVERRIDE(bublbobl_state, tokio)
	MCFG_MACHINE_RESET_OVERRIDE(bublbobl_state, tokio)

	/* video hardware */
	SCREEN(config, m_screen, SCREEN_TYPE_RASTER);
	m_screen->set_raw(MAIN_XTAL/4, 384, 0, 256, 264, 16, 240);
	m_screen->set_screen_update(FUNC(bublbobl_state::screen_update_bublbobl));
	m_screen->set_palette(m_palette);

	GFXDECODE(config, m_gfxdecode, m_palette, gfx_bublbobl);
	PALETTE(config, m_palette).set_format(palette_device::RGBx_444, 256).set_endianness(ENDIANNESS_BIG);

	/* sound hardware */
	SPEAKER(config, "mono").front_center();

	INPUT_MERGER_ALL_HIGH(config, m_soundnmi).output_handler().set_inputline(m_audiocpu, INPUT_LINE_NMI);

	GENERIC_LATCH_8(config, m_main_to_sound).data_pending_callback().set(m_soundnmi, FUNC(input_merger_device::in_w<1>));
	GENERIC_LATCH_8(config, m_sound_to_main);

	YM2203(config, m_ym2203, MAIN_XTAL/8);
	m_ym2203->irq_handler().set_inputline(m_audiocpu, 0);
	m_ym2203->add_route(0, "mono", 0.08);
	m_ym2203->add_route(1, "mono", 0.08);
	m_ym2203->add_route(2, "mono", 0.08);
	m_ym2203->add_route(3, "mono", 1.0);
}

void bublbobl_state::bublboblp(machine_config &config)
{
	tokio(config);
	config.device_remove("bmcu"); // no mcu, socket is empty

	// watchdog circuit is actually present on the prototype pcb, but is either
	// hooked up wrong in MAME for tokio in general, or is disabled with a wire
	// jumper under the epoxy
	config.device_remove("watchdog");
	WATCHDOG_TIMER(config, "watchdog"); // this adds back a watchdog, but due to the way MAME handles watchdogs, it will never fire unless it first gets at least one pulse, which it never will.

	Z80(config.replace(), m_maincpu, MAIN_XTAL/4); // 6 MHz
	m_maincpu->set_addrmap(AS_PROGRAM, &bublbobl_state::tokio_map); // no mcu or resistors at all
	m_maincpu->set_vblank_int("screen", FUNC(bublbobl_state::irq0_line_hold));
}

void bublbobl_state::tokiob(machine_config &config)
{
	tokio(config);
	config.device_remove("bmcu"); // no mcu, but see below...

	Z80(config.replace(), m_maincpu, MAIN_XTAL/4); // 6 MHz
	m_maincpu->set_addrmap(AS_PROGRAM, &bublbobl_state::tokio_map_bootleg); // resistor tying mcu's footprint PA6 pin low so mcu reads always return 0xBF
	m_maincpu->set_vblank_int("screen", FUNC(bublbobl_state::irq0_line_hold));
}


MACHINE_START_MEMBER(bublbobl_state,bublbobl)
{
	MACHINE_START_CALL_MEMBER(common);

	save_item(NAME(m_ddr1));
	save_item(NAME(m_ddr2));
	save_item(NAME(m_ddr3));
	save_item(NAME(m_ddr4));
	save_item(NAME(m_port1_in));
	save_item(NAME(m_port2_in));
	save_item(NAME(m_port3_in));
	save_item(NAME(m_port4_in));
	save_item(NAME(m_port1_out));
	save_item(NAME(m_port2_out));
	save_item(NAME(m_port3_out));
	save_item(NAME(m_port4_out));
}

MACHINE_RESET_MEMBER(bublbobl_state,bublbobl)
{
	MACHINE_RESET_CALL_MEMBER(common);
	bublbobl_bankswitch_w(0x00); // force a bankswitch write of all zeroes, as /RESET clears the latch

	m_ddr1 = 0;
	m_ddr2 = 0;
	m_ddr3 = 0;
	m_ddr4 = 0;
	m_port1_in = 0;
	m_port2_in = 0;
	m_port3_in = 0;
	m_port4_in = 0;
	m_port1_out = 0;
	m_port2_out = 0;
	m_port3_out = 0;
	m_port4_out = 0;
}

void bublbobl_state::bublbobl_nomcu(machine_config &config)
{
	/* basic machine hardware */
	Z80(config, m_maincpu, MAIN_XTAL/4); // 6 MHz
	m_maincpu->set_addrmap(AS_PROGRAM, &bublbobl_state::bublbobl_maincpu_map);

	Z80(config, m_subcpu, MAIN_XTAL/4); // 6 MHz
	m_subcpu->set_addrmap(AS_PROGRAM, &bublbobl_state::subcpu_map);
	m_subcpu->set_vblank_int("screen", FUNC(bublbobl_state::irq0_line_hold));

	Z80(config, m_audiocpu, MAIN_XTAL/8); // 3 MHz
	m_audiocpu->set_addrmap(AS_PROGRAM, &bublbobl_state::sound_map); // IRQs are triggered by the YM2203

	config.set_maximum_quantum(attotime::from_hz(6000)); // 100 CPU slices per frame - a high value to ensure proper synchronization of the CPUs

	WATCHDOG_TIMER(config, "watchdog").set_vblank_count("screen", 128); // 74LS393, counts 128 vblanks before firing watchdog; same circuit as taitosj uses

	MCFG_MACHINE_START_OVERRIDE(bublbobl_state, bublbobl)
	MCFG_MACHINE_RESET_OVERRIDE(bublbobl_state, bublbobl)

	/* video hardware */
	SCREEN(config, m_screen, SCREEN_TYPE_RASTER);
	m_screen->set_raw(MAIN_XTAL/4, 384, 0, 256, 264, 16, 240);
	m_screen->set_screen_update(FUNC(bublbobl_state::screen_update_bublbobl));
	m_screen->set_palette(m_palette);

	GFXDECODE(config, m_gfxdecode, m_palette, gfx_bublbobl);
	PALETTE(config, m_palette).set_format(palette_device::RGBx_444, 256).set_endianness(ENDIANNESS_BIG);

	/* sound hardware */
	SPEAKER(config, "mono").front_center();

	INPUT_MERGER_ANY_HIGH(config, m_soundirq).output_handler().set_inputline(m_audiocpu, INPUT_LINE_IRQ0);
	INPUT_MERGER_ALL_HIGH(config, m_soundnmi).output_handler().set_inputline(m_audiocpu, INPUT_LINE_NMI);

	GENERIC_LATCH_8(config, m_main_to_sound).data_pending_callback().set(m_soundnmi, FUNC(input_merger_device::in_w<1>));
	GENERIC_LATCH_8(config, m_sound_to_main);

	YM2203(config, m_ym2203, MAIN_XTAL/8);
	m_ym2203->irq_handler().set("soundirq", FUNC(input_merger_device::in_w<0>));
	m_ym2203->add_route(ALL_OUTPUTS, "mono", 0.25);

	YM3526(config, m_ym3526, MAIN_XTAL/8);
	m_ym3526->irq_handler().set("soundirq", FUNC(input_merger_device::in_w<1>));
	m_ym3526->add_route(ALL_OUTPUTS, "mono", 0.50);
}

void bublbobl_state::bublbobl(machine_config &config)
{
	bublbobl_nomcu(config);
	M6801(config, m_mcu, XTAL(4'000'000)); // actually 6801U4 - xtal is 4MHz, divided by 4 internally
	m_mcu->set_addrmap(AS_PROGRAM, &bublbobl_state::mcu_map);

	m_screen->screen_vblank().set_inputline(m_mcu, M6801_IRQ_LINE); // same clock latches the INT pin on the second Z80
}

MACHINE_START_MEMBER(bublbobl_state,boblbobl)
{
	MACHINE_START_CALL_MEMBER(common);

	save_item(NAME(m_ic43_a));
	save_item(NAME(m_ic43_b));
}

MACHINE_RESET_MEMBER(bublbobl_state,boblbobl)
{
	MACHINE_RESET_CALL_MEMBER(common);
	bublbobl_bankswitch_w(0x00); // force a bankswitch write of all zeroes, as /RESET clears the latch

	m_ic43_a = 0;
	m_ic43_b = 0;
}

void bublbobl_state::boblbobl(machine_config &config)
{
	bublbobl_nomcu(config);

	/* basic machine hardware */
	m_maincpu->set_addrmap(AS_PROGRAM, &bublbobl_state::bootleg_map);
	m_maincpu->set_vblank_int("screen", FUNC(bublbobl_state::irq0_line_hold)); // interrupt mode 1, unlike Bubble Bobble

	MCFG_MACHINE_START_OVERRIDE(bublbobl_state, boblbobl)
	MCFG_MACHINE_RESET_OVERRIDE(bublbobl_state, boblbobl)
}


MACHINE_START_MEMBER(bub68705_state, bub68705)
{
	MACHINE_START_CALL_MEMBER(common);

	save_item(NAME(m_port_a_out));
	save_item(NAME(m_port_b_out));
	save_item(NAME(m_address));
	save_item(NAME(m_latch));

	m_port_a_out = 0xff;
	m_port_b_out = 0xff;
}

MACHINE_RESET_MEMBER(bub68705_state, bub68705)
{
	MACHINE_RESET_CALL_MEMBER(common);
	bublbobl_bankswitch_w(0x00); // force a bankswitch write of all zeroes, as /RESET clears the latch

	m_address = 0;
	m_latch = 0;
}

void bub68705_state::bub68705(machine_config &config)
{
	bublbobl_nomcu(config);

	/* basic machine hardware */
	M68705P3(config, m_mcu, XTAL(4'000'000)); // xtal is 4MHz, divided by 4 internally
	m_mcu->portc_r().set_ioport("IN0");
	m_mcu->porta_w().set(FUNC(bub68705_state::port_a_w));
	m_mcu->portb_w().set(FUNC(bub68705_state::port_b_w));
	m_mcu->set_vblank_int("screen", FUNC(bub68705_state::bublbobl_m68705_interrupt)); // ??? should come from the same clock which latches the INT pin on the second Z80

	MCFG_MACHINE_START_OVERRIDE(bub68705_state, bub68705)
	MCFG_MACHINE_RESET_OVERRIDE(bub68705_state, bub68705)
}



/*************************************
 *
 *  ROM definition(s)
 *
 *************************************/
ROM_START( tokio ) // newer japan set, has -1 revision of roms 02, 03 and 06
	ROM_REGION( 0x30000, "maincpu", 0 ) /* main CPU */
	ROM_LOAD( "a71-02-1.ic4", 0x00000, 0x8000, CRC(bb8dabd7) SHA1(141e9f0c19bcf316477681369e2d98dffdd8435d) )
	/* ROMs banked at 8000-bfff */
	ROM_LOAD( "a71-03-1.ic5", 0x10000, 0x8000, CRC(ee49b383) SHA1(d510a1d168542df6a87c7d7c67a47cf776a51f29) )
	ROM_LOAD( "a71-04.ic6",   0x18000, 0x8000, CRC(a0a4ce0e) SHA1(c49bdcd85c760a5e7327d1b424772e1560f1a318) )
	ROM_LOAD( "a71-05.ic7",   0x20000, 0x8000, CRC(6da0b945) SHA1(6c80b8333dd95657f99e6ba5b6e877733ac02a8c) )
	ROM_LOAD( "a71-06-1.ic8", 0x28000, 0x8000, CRC(56927b3f) SHA1(33fb4e71b95664ecff1f35f6782a14101982a56d) )

	ROM_REGION( 0x10000, "subcpu", 0 )   /* video CPU */
	ROM_LOAD( "a71-01.ic1",   0x00000, 0x8000, CRC(0867c707) SHA1(7129974f1252b28e9e338bd3c7fcb87210dcf412) )

	ROM_REGION( 0x10000, "audiocpu", 0 )    /* audio CPU */
	ROM_LOAD( "a71-07.ic10",  0x0000, 0x08000, CRC(f298cc7b) SHA1(ebf5c804aa07b7f198ec3e1f8d1e111cd89ebdf3) )

	ROM_REGION( 0x0800, "bmcu:mcu", 0 ) /* 2k for the microcontroller (68705P5) */
	ROM_LOAD( "a71__24.ic57",  0x0000, 0x0800, CRC(0f4b25de) SHA1(e2d82aa8d8cc6a86aaf5715ef9cb62f526fd5b11) )

	ROM_REGION( 0x80000, "gfx1", ROMREGION_INVERT ) /* gfx roms, on gfx board */
	ROM_LOAD( "a71-08.ic12",  0x00000, 0x8000, CRC(0439ab13) SHA1(84142220a6a29f0e34f7c7c751b583bf394df8ce) )    /* 1st plane */
	ROM_LOAD( "a71-09.ic13",  0x08000, 0x8000, CRC(edb3d2ff) SHA1(0c6e4bbc786a097f9d99220e72f98c1c795a7292) )
	ROM_LOAD( "a71-10.ic14",  0x10000, 0x8000, CRC(69f0888c) SHA1(1704ab6339981195cd09d581e83094c75037d18e) )
	ROM_LOAD( "a71-11.ic15",  0x18000, 0x8000, CRC(4ae07c31) SHA1(452d1eb5a70e7853791cd05e4578c1454477bdec) )
	ROM_LOAD( "a71-12.ic16",  0x20000, 0x8000, CRC(3f6bd706) SHA1(b03c534a95b71941331d3ffd9aa7069b5f05687e) )
	ROM_LOAD( "a71-13.ic17",  0x28000, 0x8000, CRC(f2c92aaa) SHA1(7dfdc473794a298032405ba918df8085b0bbe174) )
	ROM_LOAD( "a71-14.ic18",  0x30000, 0x8000, CRC(c574b7b2) SHA1(9839adce60c0017ae3997603a2aece511af226d2) )
	ROM_LOAD( "a71-15.ic19",  0x38000, 0x8000, CRC(12d87e7f) SHA1(327a80f08207ee66721738f7e1c53f75b5659be0) )
	ROM_LOAD( "a71-16.ic30",  0x40000, 0x8000, CRC(0bce35b6) SHA1(3f0496db6681c7be1e36ba41296115d158d7457a) )    /* 2nd plane */
	ROM_LOAD( "a71-17.ic31",  0x48000, 0x8000, CRC(deda6387) SHA1(40f0be3a71b0a03f0275da72f4124424b162318a) )
	ROM_LOAD( "a71-18.ic32",  0x50000, 0x8000, CRC(330cd9d7) SHA1(919f78036b760938d6aa72754be1a615f568b470) )
	ROM_LOAD( "a71-19.ic33",  0x58000, 0x8000, CRC(fc4b29e0) SHA1(d11393a24b5c6c04f5058b299e4b0fc773a03e4b) )
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
	ROM_LOAD( "c8.ic34",  0x60000, 0x8000, CRC(1320e15d) SHA1(b5da80bc27c053353c701f523f89f704c11c24e9) )
	ROM_LOAD( "c10.ic35", 0x68000, 0x8000, CRC(29c41387) SHA1(6f7b433a82e34b9daf5ce3f9a28061c64db061f6) )
	// ic36 socket is empty
	// ic37 socket is empty

	ROM_REGION( 0x0100, "proms", 0 )
	ROM_LOAD( "a71-25.ic41",  0x0000, 0x0100, BAD_DUMP CRC(2d0f8545) SHA1(089c31e2f614145ef2743164f7b52ae35bc06808) )    /* video timing, on gfx board */ // NEEDS DUMPING, temporarily copied from tokio for now

	ROM_REGION( 0x0200, "plds", 0 )
	ROM_LOAD( "bublboblp.pal16l8.ic19",  0x0000, 0x0117, CRC(4e1f119c) SHA1(0ac8eb2fdb202951e5f7145f92dfd10fe96b294b) ) // under epoxy; unlabeled, but equations are identical to tokio a71-26.ic19. fusemap was not dumped.
ROM_END

/*

bublbobl.zip - a78-05-1.52
TAITO CORPORATION 1986
ALL RIGHTS RESERVED
VER 0.1 4.SEP,1986 SUMMER

Name          Size    CRC32       Chip Type
-------------------------------------------
a78-05-1.52    65536  0x9f8ee242  Fujitsu MBM27C512
a78-06-1.51    32768  0x567934b6  Intel D27256

*/

ROM_START( bublbobl )
	ROM_REGION( 0x30000, "maincpu", 0 )
	ROM_LOAD( "a78-06-1.51",    0x00000, 0x08000, CRC(567934b6) SHA1(b0c4d49fd551f465d148c25c3e80b278835e2f0d) )
	/* ROMs banked at 8000-bfff */
	ROM_LOAD( "a78-05-1.52",    0x10000, 0x10000, CRC(9f8ee242) SHA1(924150d4e7e087a9b2b0a294c2d0e9903a266c6c) )
	/* 20000-2ffff empty */

	ROM_REGION( 0x10000, "subcpu", 0 )   /* 64k for the second CPU */
	ROM_LOAD( "a78-08.37",    0x0000, 0x08000, CRC(ae11a07b) SHA1(af7a335c8da637103103cc274e077f123908ebb7) )

	ROM_REGION( 0x10000, "audiocpu", 0 )    /* 64k for the third CPU */
	ROM_LOAD( "a78-07.46",    0x0000, 0x08000, CRC(4f9a26e8) SHA1(3105b34b88a7134493c2b3f584729f8b0407a011) )

	ROM_REGION( 0x10000, "mcu", 0 ) /* 64k for the MCU */
	ROM_LOAD( "a78-01.17",    0xf000, 0x1000, CRC(b1bfb53d) SHA1(31b8f31acd3aa394acd80db362774749842e1285) )

	ROM_REGION( 0x80000, "gfx1", ROMREGION_INVERT )
	ROM_LOAD( "a78-09.12",    0x00000, 0x8000, CRC(20358c22) SHA1(2297af6c53d5807bf90a8e081075b8c72a994fc5) )    /* 1st plane */
	ROM_LOAD( "a78-10.13",    0x08000, 0x8000, CRC(930168a9) SHA1(fd358c3c3b424bca285f67a1589eb98a345ff670) )
	ROM_LOAD( "a78-11.14",    0x10000, 0x8000, CRC(9773e512) SHA1(33c1687ee575d66bf0e98add45d06da827813765) )
	ROM_LOAD( "a78-12.15",    0x18000, 0x8000, CRC(d045549b) SHA1(0c12077d3ddc2ce6aa45a0224ad5540f3f218446) )
	ROM_LOAD( "a78-13.16",    0x20000, 0x8000, CRC(d0af35c5) SHA1(c5a89f4d73acc0db86654540b3abfd77b3757db5) )
	ROM_LOAD( "a78-14.17",    0x28000, 0x8000, CRC(7b5369a8) SHA1(1307b26d80e6f36ebe6c442bebec41d20066eaf9) )
	/* 0x30000-0x3ffff empty */
	ROM_LOAD( "a78-15.30",    0x40000, 0x8000, CRC(6b61a413) SHA1(44eddf12fb46fceca2addbe6da929aaea7636b13) )    /* 2nd plane */
	ROM_LOAD( "a78-16.31",    0x48000, 0x8000, CRC(b5492d97) SHA1(d5b045e3ebaa44809757a4220cefb3c6815470da) )
	ROM_LOAD( "a78-17.32",    0x50000, 0x8000, CRC(d69762d5) SHA1(3326fef4e0bd86681a3047dc11886bb171ecb609) )
	ROM_LOAD( "a78-18.33",    0x58000, 0x8000, CRC(9f243b68) SHA1(32dce8d311a4be003693182a999e4053baa6bb0a) )
	ROM_LOAD( "a78-19.34",    0x60000, 0x8000, CRC(66e9438c) SHA1(b94e62b6fbe7f4e08086d0365afc5cff6e0ccafd) )
	ROM_LOAD( "a78-20.35",    0x68000, 0x8000, CRC(9ef863ad) SHA1(29f91b5a3765e4d6e6c3382db1d8d8297b6e56c8) )
	/* 0x70000-0x7ffff empty */

	ROM_REGION( 0x0100, "proms", 0 )
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
	ROM_LOAD( "a78-08.37",    0x0000, 0x08000, CRC(ae11a07b) SHA1(af7a335c8da637103103cc274e077f123908ebb7) )

	ROM_REGION( 0x10000, "audiocpu", 0 )    /* 64k for the third CPU */
	ROM_LOAD( "a78-07.46",    0x0000, 0x08000, CRC(4f9a26e8) SHA1(3105b34b88a7134493c2b3f584729f8b0407a011) )

	ROM_REGION( 0x80000, "gfx1", ROMREGION_INVERT )
	ROM_LOAD( "a78-09.12",    0x00000, 0x8000, CRC(20358c22) SHA1(2297af6c53d5807bf90a8e081075b8c72a994fc5) )    /* 1st plane */
	ROM_LOAD( "a78-10.13",    0x08000, 0x8000, CRC(930168a9) SHA1(fd358c3c3b424bca285f67a1589eb98a345ff670) )
	ROM_LOAD( "a78-11.14",    0x10000, 0x8000, CRC(9773e512) SHA1(33c1687ee575d66bf0e98add45d06da827813765) )
	ROM_LOAD( "a78-12.15",    0x18000, 0x8000, CRC(d045549b) SHA1(0c12077d3ddc2ce6aa45a0224ad5540f3f218446) )
	ROM_LOAD( "a78-13.16",    0x20000, 0x8000, CRC(d0af35c5) SHA1(c5a89f4d73acc0db86654540b3abfd77b3757db5) )
	ROM_LOAD( "a78-14.17",    0x28000, 0x8000, CRC(7b5369a8) SHA1(1307b26d80e6f36ebe6c442bebec41d20066eaf9) )
	/* 0x30000-0x3ffff empty */
	ROM_LOAD( "a78-15.30",    0x40000, 0x8000, CRC(6b61a413) SHA1(44eddf12fb46fceca2addbe6da929aaea7636b13) )    /* 2nd plane */
	ROM_LOAD( "a78-16.31",    0x48000, 0x8000, CRC(b5492d97) SHA1(d5b045e3ebaa44809757a4220cefb3c6815470da) )
	ROM_LOAD( "a78-17.32",    0x50000, 0x8000, CRC(d69762d5) SHA1(3326fef4e0bd86681a3047dc11886bb171ecb609) )
	ROM_LOAD( "a78-18.33",    0x58000, 0x8000, CRC(9f243b68) SHA1(32dce8d311a4be003693182a999e4053baa6bb0a) )
	ROM_LOAD( "a78-19.34",    0x60000, 0x8000, CRC(66e9438c) SHA1(b94e62b6fbe7f4e08086d0365afc5cff6e0ccafd) )
	ROM_LOAD( "a78-20.35",    0x68000, 0x8000, CRC(9ef863ad) SHA1(29f91b5a3765e4d6e6c3382db1d8d8297b6e56c8) )
	/* 0x70000-0x7ffff empty */

	ROM_REGION( 0x0100, "proms", 0 )
	ROM_LOAD( "a71-25.41",    0x0000, 0x0100, CRC(2d0f8545) SHA1(089c31e2f614145ef2743164f7b52ae35bc06808) )    /* video timing */

	ROM_REGION( 0x0600, "plds", 0 )
	ROM_LOAD( "pal16r4.u36", 0x0000, 0x0104, CRC(22fe26ac) SHA1(bbbfcbe6faded4af7ceec57b800297c054a997da) )
	ROM_LOAD( "pal16l8.u38", 0x0200, 0x0104, CRC(c02d9663) SHA1(5d23cfd96f072981fd5fcf0dd7e98459da58b662) )
	ROM_LOAD( "pal16l8.u4",  0x0400, 0x0104, CRC(077d20a8) SHA1(8e568ffd6f66c3dd61708dd0f3be9c2ed488ae4b) )
ROM_END

/*************************************
 *
 *  Driver initialization
 *
 *************************************/

void bublbobl_state::configure_banks(  )
{
	uint8_t *ROM = memregion("maincpu")->base();
	membank("bank1")->configure_entries(0, 8, &ROM[0x10000], 0x4000);
}

void bublbobl_state::init_common()
{
	configure_banks();
}

void bublbobl_state::init_dland()
{
	// rearrange gfx to original format
	uint8_t* src = memregion("gfx1")->base();
	for (int i = 0; i < 0x40000; i++)
		src[i] = bitswap<8>(src[i],7,6,5,4,0,1,2,3);

	for (int i = 0x40000; i < 0x80000; i++)
		src[i] = bitswap<8>(src[i],7,4,5,6,3,0,1,2);

	init_common();
}


/*************************************
 *
 *  Game driver(s)
 *
 *************************************/
//    YEAR  NAME        PARENT    MACHINE    INPUT       STATE           INIT         ROT    COMPANY     FULLNAME      FLAGS
GAME( 1986, tokio,      0,        tokio,     tokio,      bublbobl_state, init_common, ROT90, "Taito Corporation",                           "Tokio / Scramble Formation (newer)",   MACHINE_SUPPORTS_SAVE )
GAME( 1986, tokioo,     tokio,    tokio,     tokio,      bublbobl_state, init_common, ROT90, "Taito Corporation",                           "Tokio / Scramble Formation (older)",   MACHINE_SUPPORTS_SAVE )
GAME( 1986, tokiou,     tokio,    tokio,     tokio,      bublbobl_state, init_common, ROT90, "Taito America Corporation (Romstar license)", "Tokio / Scramble Formation (US)",      MACHINE_SUPPORTS_SAVE )
GAME( 1986, tokiob,     tokio,    tokiob,    tokio_base, bublbobl_state, init_common, ROT90, "bootleg",                                     "Tokio / Scramble Formation (bootleg)", MACHINE_SUPPORTS_SAVE )

GAME( 1986, bublboblp,  bublbobl, bublboblp, bublboblp,  bublbobl_state, init_common, ROT0,  "Taito Corporation",                           "Bubble Bobble (prototype on Tokio hardware)", MACHINE_SUPPORTS_SAVE )
GAME( 1986, bublbobl,   0,        bublbobl,  bublbobl,   bublbobl_state, init_common, ROT0,  "Taito Corporation",                           "Bubble Bobble (Japan, Ver 0.1)", MACHINE_SUPPORTS_SAVE )
GAME( 1986, bublbobl1,  bublbobl, bublbobl,  bublbobl,   bublbobl_state, init_common, ROT0,  "Taito Corporation",                           "Bubble Bobble (Japan, Ver 0.0)", MACHINE_SUPPORTS_SAVE )
GAME( 1986, bublboblr,  bublbobl, bublbobl,  bublbobl,   bublbobl_state, init_common, ROT0,  "Taito America Corporation (Romstar license)", "Bubble Bobble (US, Ver 5.1)",    MACHINE_SUPPORTS_SAVE ) // newest release, with mode select
GAME( 1986, bublboblr1, bublbobl, bublbobl,  bublbobl,   bublbobl_state, init_common, ROT0,  "Taito America Corporation (Romstar license)", "Bubble Bobble (US, Ver 1.0)",    MACHINE_SUPPORTS_SAVE )

GAME( 1986, boblbobl,   bublbobl, boblbobl,  boblbobl,   bublbobl_state, init_common, ROT0,  "bootleg",         "Bobble Bobble (bootleg of Bubble Bobble)", MACHINE_SUPPORTS_SAVE )
GAME( 1986, sboblbobl,  bublbobl, boblbobl,  sboblbobl,  bublbobl_state, init_common, ROT0,  "bootleg (Datsu)", "Super Bobble Bobble (bootleg, set 1)",     MACHINE_SUPPORTS_SAVE )
GAME( 1986, sboblbobla, bublbobl, boblbobl,  boblbobl,   bublbobl_state, init_common, ROT0,  "bootleg",         "Super Bobble Bobble (bootleg, set 2)",     MACHINE_SUPPORTS_SAVE )
GAME( 1986, sboblboblb, bublbobl, boblbobl,  sboblboblb, bublbobl_state, init_common, ROT0,  "bootleg",         "Super Bobble Bobble (bootleg, set 3)",     MACHINE_SUPPORTS_SAVE )
GAME( 1986, sboblbobld, bublbobl, boblbobl,  sboblboblb, bublbobl_state, init_common, ROT0,  "bootleg",         "Super Bobble Bobble (bootleg, set 4)",     MACHINE_SUPPORTS_SAVE )
GAME( 1986, sboblboble, bublbobl, boblbobl,  sboblboblb, bublbobl_state, init_common, ROT0,  "bootleg",         "Super Bobble Bobble (bootleg, set 5)",     MACHINE_SUPPORTS_SAVE )
GAME( 1986, sboblboblf, bublbobl, boblbobl,  sboblboblb, bublbobl_state, init_common, ROT0,  "bootleg",         "Super Bobble Bobble (bootleg, set 6)",     MACHINE_SUPPORTS_SAVE )
GAME( 1986, sboblboblc, bublbobl, boblbobl,  sboblboblb, bublbobl_state, init_common, ROT0,  "bootleg",         "Super Bubble Bobble (bootleg)",            MACHINE_SUPPORTS_SAVE ) // the title screen on this one isn't hacked
GAME( 1986, bub68705,   bublbobl, bub68705,  bublbobl,   bub68705_state, init_common, ROT0,  "bootleg",         "Bubble Bobble (bootleg with 68705)",       MACHINE_SUPPORTS_SAVE )

GAME( 1987, dland,      bublbobl, boblbobl,  dland,      bublbobl_state, init_dland,  ROT0,  "bootleg", "Dream Land / Super Dream Land (bootleg of Bubble Bobble)", MACHINE_SUPPORTS_SAVE )

GAME( 2013, bbredux,    bublbobl, boblbobl,  boblbobl,   bublbobl_state, init_common, ROT0,  "bootleg (Punji)",  "Bubble Bobble ('bootleg redux' hack for Bobble Bobble PCB)", MACHINE_SUPPORTS_SAVE ) // for use on non-MCU bootleg boards (Bobble Bobble etc.) has more faithful simulation of the protection device (JAN-04-2015 release)
GAME( 2013, bublboblb,  bublbobl, boblbobl,  boblcave,   bublbobl_state, init_common, ROT0,  "bootleg (Aladar)", "Bubble Bobble (for Bobble Bobble PCB)",                      MACHINE_SUPPORTS_SAVE ) // alt bootleg/hack to restore proper MCU behavior to bootleg boards
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
