skutis/jtbubl/cores/kiwi/hdl/jtkiwi_game.v

/*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
    Author: Jose Tejada Gomez. Twitter: @topapate
    Version: 1.0
    Date: 02-05-2020 */

module jtkiwi_game(
    `include "jtframe_game_ports.inc" // see $JTFRAME/hdl/inc/jtframe_game_ports.inc
);

wire        sub_rnw, shr_cs, mshramen, snd_rstn;
wire [ 7:0] shr_din, shr_dout, main_st, gfx_st, snd_st,
            vram_dout, pal_dout, cpu_dout;
wire [ 8:0] hdump;
wire [12:0] shr_addr, cpu_addr;
wire        cen6, cen3, cen1p5;

wire        vram_cs,  pal_cs, flip;
wire        cpu_rnw, vctrl_cs, vflag_cs,
            colprom_we, mcuprom_we;
reg         colprom_en=0, kabuki=0, kageki=0, mcu_en=0;

assign dip_flip   = flip;
assign debug_view = st_addr[7:6]==0 ? { 4'd0, kageki, kabuki, colprom_en, mcu_en } :
                    st_addr[7:6]==1 ? main_st :
                    st_addr[7:6]==2 ? gfx_st  : snd_st;
assign colprom_we = prom_we && ioctl_addr[15:10]==0;
assign mcuprom_we = prom_we && ioctl_addr >= `MCU_START;
assign st_dout    = debug_view;

always @(posedge clk) begin
    if( prog_we && header && prog_addr==0 ) begin
        { kageki, kabuki, colprom_en, mcu_en } <= prog_data[3:0];
    end
end

jtframe_frac_cen #(.WC(4),.W(3)) u_cen24(
    .clk    ( clk       ),    // 24 MHz
    .n      ( 4'd1      ),
    .m      ( 4'd8      ),
    .cen    ( { cen1p5, cen3, cen6 } ),
    .cenb   (           )
);

jtkiwi_main u_main(
    .rst            ( rst           ),
    .clk            ( clk           ),
    .cen6           ( cen6          ),

    .LVBL           ( LVBL          ),
    .hcnt           ( hdump         ),
    .colprom_en     ( colprom_en    ),
    // Main CPU ROM
    .rom_addr       ( main_addr     ),
    .rom_cs         ( main_cs       ),
    .rom_ok         ( main_ok       ),
    .rom_data       ( main_data     ),

    // Sub CPU access to shared RAM
    .shr_addr       ( shr_addr      ),
    .shr_dout       ( shr_dout      ),
    .sub_rnw        ( sub_rnw       ),
    .shr_din        ( shr_din       ),
    .shr_cs         ( shr_cs        ),
    .mshramen       ( mshramen      ),
    // Sound
    .snd_rstn       ( snd_rstn      ),

    // Video
    .cpu_addr       ( cpu_addr      ),
    .cpu_dout       ( cpu_dout      ),
    .cpu_rnw        ( cpu_rnw       ),

    .vctrl_cs       ( vctrl_cs      ),
    .vram_cs        ( vram_cs       ),
    .vflag_cs       ( vflag_cs      ),
    .vram_dout      ( vram_dout     ),

    .pal_cs         ( pal_cs        ),
    .pal_dout       ( pal_dout      ),
    .dip_pause      ( dip_pause     ),
    .debug_bus      ( debug_bus     ),
    .st_dout        ( main_st       )
);

/* verilator tracing_off */
jtkiwi_video u_video(
    .rst            ( rst           ),
    .clk            ( clk           ),
    .clk_cpu        ( clk           ),

    .pxl2_cen       ( pxl2_cen      ),
    .pxl_cen        ( pxl_cen       ),
    .LHBL           ( LHBL          ),
    .LVBL           ( LVBL          ),
    .HS             ( HS            ),
    .VS             ( VS            ),
    .flip           ( flip          ),
    .hdump          ( hdump         ),
    // PROMs
    .prom_we        ( colprom_we    ),
    .prog_addr      ( prog_addr[9:0]),
    .prog_data      ( prog_data     ),
    .colprom_en     ( colprom_en    ),
    // GFX - CPU interface
    .cpu_rnw        ( cpu_rnw       ),
    .cpu_addr       ( cpu_addr      ),
    .cpu_dout       ( cpu_dout      ),

    .vram_cs        ( vram_cs       ),
    .vctrl_cs       ( vctrl_cs      ),
    .vflag_cs       ( vflag_cs      ),
    .vram_dout      ( vram_dout     ),

    .pal_cs         ( pal_cs        ),
    .pal_dout       ( pal_dout      ),
    // SDRAM
    .scr_addr       ( scr_addr      ),
    .scr_data       ( scr_data      ),
    .scr_ok         ( scr_ok        ),
    .scr_cs         ( scr_cs        ),

    .obj_addr       ( obj_addr      ),
    .obj_data       ( obj_data      ),
    .obj_ok         ( obj_ok        ),
    .obj_cs         ( obj_cs        ),
    // pixels
    .red            ( red           ),
    .green          ( green         ),
    .blue           ( blue          ),
    // Test
    .gfx_en         ( gfx_en        ),
    .debug_bus      ( debug_bus     ),
    .st_dout        ( gfx_st        )
);
/* verilator tracing_on */


jtkiwi_snd u_sound(
    .rst        ( rst           ),
    .clk        ( clk           ),
    .snd_rstn   ( snd_rstn      ),
    .cen6       ( cen6          ),
    .cen1p5     ( cen1p5        ),
    .LVBL       ( LVBL          ),
    .fm_en      ( enable_fm     ),
    .psg_en     ( enable_psg    ),

    // Game variations
    .kabuki     ( kabuki        ),
    .kageki     ( kageki        ),

    // PCM
    .pcm_addr   ( pcm_addr      ),
    .pcm_data   ( pcm_data      ),
    .pcm_ok     ( pcm_ok        ),
    .pcm_cs     ( pcm_cs        ),

    // cabinet I/O
    .start_button( start_button ),
    .coin_input ( coin_input    ),
    .joystick1  ( joystick1     ),
    .joystick2  ( joystick2     ),
    .service    ( service       ),
    .tilt       ( tilt          ),
    // DIP switches
    .dipsw      ( dipsw[15:0]   ),
    .dip_pause  ( dip_pause     ),

    // Shared RAM
    .ram_addr   ( shr_addr      ),
    .ram_din    ( shr_din       ),
    .ram_dout   ( shr_dout      ),
    .cpu_rnw    ( sub_rnw       ),
    .ram_cs     ( shr_cs        ),
    .mshramen   ( mshramen      ),

    // MCU
    .mcu_en     ( mcu_en        ),
    .prog_addr  ( prog_addr[10:0]),
    .prog_data  ( prog_data     ),
    .prom_we    ( mcuprom_we    ),

    // ROM
    .rom_addr   ( sub_addr      ),
    .rom_cs     ( sub_cs        ),
    .rom_data   ( sub_data      ),
    .rom_ok     ( sub_ok        ),

    // Sound output
    .fx_level   ( dip_fxlevel   ),
    .snd        ( snd           ),
    .sample     ( sample        ),
    .peak       ( game_led      ),
    // Debug
    .st_addr    ( st_addr       ),
    .st_dout    ( snd_st        )
);

endmodule
