skutis/jtbubl/cores/kiwi/hdl/jtkiwi_gfx.v

/*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
    Author: Jose Tejada Gomez. Twitter: @topapate
    Version: 1.0
    Date: 18-09-2022 */

// There is bus contention to access the memories
// in this module, based. When H4 is high, the
// GPU is in control. When H4 is low, it's the CPU

module jtkiwi_gfx(
    input               rst,
    input               clk,
    input               clk_cpu,

    input               pxl2_cen,
    input               pxl_cen,

    input               LHBL,
    input               LVBL,
    input               hs,
    input               vs,
    output              flip,

    input      [ 8:0]   vdump,
    input      [ 8:0]   vrender,
    input      [ 8:0]   hdump,

    input               cpu_rnw,
    input      [12:0]   cpu_addr,
    input      [ 7:0]   cpu_dout,
    input               vram_cs,
    input               vctrl_cs,
    input               vflag_cs,
    output     [ 7:0]   cpu_din,

    // SDRAM interface
    output     [19:2]   scr_addr,
    input      [31:0]   scr_data,
    input               scr_ok,
    output              scr_cs,

    output     [19:2]   obj_addr,
    input      [31:0]   obj_data,
    input               obj_ok,
    output              obj_cs,

    output      [ 8:0]  scr_pxl,
    output      [ 8:0]  obj_pxl,
    input       [ 7:0]  debug_bus,
    output      [ 7:0]  st_dout
);

wire        yram_we, video_en;
wire [ 1:0] vram_we;
wire [11:0] tm_addr, lut_addr;
reg  [11:0] code_addr;
reg  [ 9:0] col_addr;
wire [ 7:0] yram_dout, col_data;
wire [ 7:0] scol_addr;
reg  [ 7:0] attr, xpos, ypos;
reg  [ 7:0] cfg[0:3], flag;
reg         scan_cen, done, dr_start, dr_busy,
            match, xflip, yflip,
            yram_cs, cfg_cs;
reg  [ 2:0] st;
reg  [13:0] code;
reg  [ 1:0] cen_cnt;
wire        tm_page;
wire [15:0] vram_dout, code_dout, col_xmsb;
wire [ 3:0] col_cfg;
wire [ 1:0] col0;
reg         tm_cen, lut_cen;
// Objects
wire [ 8:0] y_addr;

`ifdef SIMULATION
wire [7:0] cfg0 = cfg[0], cfg1 = cfg[1], cfg2 = cfg[2], cfg3 = cfg[3];
`endif

assign vram_we  = {2{vram_cs  & ~cpu_rnw}} & { cpu_addr[12], ~cpu_addr[12] };
assign yram_we  = yram_cs & ~cpu_rnw;
assign flip     = ~cfg[0][6]; // only flip y?
assign video_en = cfg[0][4]; // uncertain
assign col0     = cfg[0][1:0]; // start column in the tilemap VRAM
assign tm_page  = cfg[1][6];
// assign obj_page = cfg[1][5]; // ?
assign col_cfg  = cfg[1][3:0];
assign col_xmsb = { cfg[3], cfg[2] };
assign cpu_din  = yram_cs ? yram_dout :
                  vram_cs ? (cpu_addr[12] ? vram_dout[15:8] : vram_dout[7:0]) : 8'h00;
assign st_dout  = { flip, 1'd0, col0, col_cfg };

always @* begin
    yram_cs = 0;
    cfg_cs  = 0;
    if( vctrl_cs ) case( cpu_addr[9:8] )
        0,1,2: yram_cs = 1;
        3: cfg_cs  = 1;
        default:;
    endcase
end

always @(posedge clk, posedge rst) begin
    if( rst ) begin
        cen_cnt <= 0;
        tm_cen  <= 0;
        lut_cen <= 0;
    end else begin
        cen_cnt <= cen_cnt + 1'd1;
        tm_cen  <= cen_cnt==0;
        lut_cen <= cen_cnt==2;
    end
end

`ifdef NOMAIN
initial $readmemh("seta_cfg.hex",cfg);
`endif

always @(posedge clk, posedge rst) begin
`ifndef NOMAIN
    if( rst ) begin
        cfg[0]  <= 0;
        cfg[1]  <= 9;
        cfg[2]  <= 0;
        cfg[3]  <= 0;
    end else
`endif
    begin
        if( cfg_cs  ) cfg[ cpu_addr[1:0] ] <= cpu_dout;
        if( vflag_cs ) flag <= cpu_dout;
    end
end

always @* begin
    case( cen_cnt )
        0,1: begin
            col_addr  = { 2'b10, scol_addr };
            code_addr = tm_addr;
        end
        2,3: begin // objects
            col_addr  = { 1'b0, y_addr };
            code_addr = lut_addr;
        end
    endcase
end

jtkiwi_tilemap u_tilemap(
    .rst        ( rst       ),
    .clk        ( clk       ),
    .tm_cen     ( tm_cen    ),

    .hs         ( hs        ),
    .flip       ( flip      ),
    .page       ( tm_page   ),

    .col_xmsb   ( col_xmsb  ),
    .col_cfg    ( col_cfg   ),
    .col0       ( col0      ),

    .tm_addr    ( tm_addr   ),
    .tm_data    ( code_dout ),

    // Column scroll
    .col_addr   ( scol_addr ),
    .col_data   ( col_data  ),

    .rom_addr   ( scr_addr  ),
    .rom_cs     ( scr_cs    ),
    .rom_ok     ( scr_ok    ),
    .rom_data   ( scr_data  ),

    .vrender    ( vrender   ),
    .hdump      ( hdump     ),
    .pxl        ( scr_pxl   ),
    .debug_bus  ( debug_bus )
);

jtkiwi_obj u_obj(
    .rst        ( rst       ),
    .clk        ( clk       ),
    .lut_cen    ( lut_cen   ),
    .pxl_cen    ( pxl_cen   ),

    .hs         ( hs        ),
    .flip       ( flip      ),
    .page       ( tm_page   ),

    .lut_addr   ( lut_addr  ),
    .lut_data   ( code_dout ),

    // Column scroll
    .y_addr     ( y_addr    ),
    .y_data     ( col_data  ),

    .rom_addr   ( obj_addr  ),
    .rom_cs     ( obj_cs    ),
    .rom_ok     ( obj_ok    ),
    .rom_data   ( obj_data  ),

    .vdump      ( vdump     ),
    .hdump      ( hdump     ),
    .pxl        ( obj_pxl   ),
    .debug_bus  ( debug_bus )
);

// This is an external memory chip. The original
// one is an 8-bit memory. Changed to 16-bit access
// to ease the drawing logic
// the upper byte refers to the upper half of the
// memory for the CPU
// In MAME the lower half is called spritecodelow
// and the upper spritecodehigh
jtframe_dual_ram16 #(.aw(12),
    .simfile_lo("vram_lo.bin"),
    .simfile_hi("vram_hi.bin")
) u_vram(
    .clk0   ( clk_cpu    ),
    .clk1   ( clk        ),
    // Main CPU
    .addr0  ( cpu_addr[11:0] ),
    .data0  ( {2{cpu_dout}}  ),
    .we0    ( vram_we    ),
    .q0     ( vram_dout  ),
    // GFX
    .addr1  ( code_addr  ),
    .data1  ( 16'd0      ),
    .we1    ( 2'd0       ),
    .q1     ( code_dout  )
);

// This memory is internal to the SETA-X1-001 chip
// this is called spriteylow by MAME
jtframe_dual_ram #(.aw(10),.simfile("col.bin")) u_yram(
    .clk0   ( clk_cpu    ),
    .clk1   ( clk        ),
    // Main CPU
    .addr0  (cpu_addr[9:0]),
    .data0  ( cpu_dout   ),
    .we0    ( yram_we    ),
    .q0     ( yram_dout  ),
    // GFX
    .addr1  ( col_addr   ),
    .data1  ( 8'd0       ),
    .we1    ( 1'd0       ),
    .q1     ( col_data   )
);

endmodule
