skutis/jtbubl/cores/kiwi/hdl/jtkiwi_colmix.v

/*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
    Author: Jose Tejada Gomez. Twitter: @topapate
    Version: 1.0
    Date: 18-9-2022 */

module jtkiwi_colmix(
    input        clk,
    input        clk_cpu,
    input        pxl_cen,
    input        LHBL,
    input        LVBL,

    input  [8:0] scr_pxl,
    input  [8:0] obj_pxl,

    input  [9:0] cpu_addr,
    input  [7:0] cpu_dout,
    input        cpu_rnw,
    output [7:0] cpu_din,
    input        pal_cs,

    input  [9:0] prog_addr,
    input  [7:0] prog_data,
    input        prom_we,
    input        colprom_en,

    input  [7:0] debug_bus,
    input  [3:0] gfx_en,
    output [4:0] red,
    output [4:0] green,
    output [4:0] blue
);

wire [ 7:0] pal_dout;
wire [ 9:0] pal_addr;
reg  [ 7:0] pall;
reg  [ 8:0] coll, col_addr;
reg  [14:0] rgb;
wire        pal_we;
wire        blank;
reg         half, obj_sel;
// PROM variation
wire [15:0] prom_dout;
wire        promhi_we, promlo_we;
wire [ 3:0] sort;

assign pal_addr = { coll, half };
assign pal_we   = pal_cs & ~cpu_rnw;
assign blank    = ~(LVBL & LHBL);
assign {red,green,blue} = {15{~blank}} & rgb;
// PROM
assign promhi_we = prom_we & ~prog_addr[9];
assign promlo_we = prom_we &  prog_addr[9];

always @* begin
    obj_sel = obj_pxl[3:0] != 4'h0;
    if( !gfx_en[0] ) obj_sel = 1;
    if( !gfx_en[3] ) obj_sel = 0;
    col_addr = obj_sel ? obj_pxl : scr_pxl; // simple priority for now.
end

always @(posedge clk) begin
    half <= ~half;
    if( pxl_cen ) begin
`ifdef GRAY
        rgb <= ~{3{ {coll[3:0]}, 1'b0 } };
`else
        rgb <= colprom_en ? prom_dout[14:0] : { pal_dout[6:0], pall };
`endif
        half <= 1;
        coll <= col_addr;
    end
    pall <= pal_dout;
end

jtframe_sort u_sort(
    .debug_bus  ( debug_bus ),
    .busin      ( col_addr[3:0]    ),
    .busout     ( sort  )
);

// Palette RAM X1-007 chip
jtframe_dual_ram #(.aw(10),.simfile("pal.bin")) u_comm(
    .clk0   ( clk_cpu      ),
    .clk1   ( clk          ),
    // Main CPU
    .addr0  ( cpu_addr     ),
    .data0  ( cpu_dout     ),
    .we0    ( pal_we       ),
    .q0     ( cpu_din      ),
    // Color mixer
    .addr1  ( pal_addr     ),
    .data1  (              ),
    .we1    ( 1'b0         ),
    .q1     ( pal_dout     )
);

// PROM for Extermination
jtframe_prom #( .aw(9), .simfile("../../../../rom/extrmatn/b06-09.15f")) u_promhi(
    .clk    ( clk       ),
    .cen    ( 1'b1      ),
    .data   ( prog_data ),
    .rd_addr( {col_addr[8:4], sort}  ),
    .wr_addr( prog_addr[8:0]  ),
    .we     ( promhi_we ),
    .q      ( prom_dout[15:8] )
);

jtframe_prom #( .aw(9), .simfile("../../../../rom/extrmatn/b06-08.17f")) u_promlo(
    .clk    ( clk       ),
    .cen    ( 1'b1      ),
    .data   ( prog_data ),
    .rd_addr( {col_addr[8:4], sort}  ),
    .wr_addr( prog_addr[8:0] ),
    .we     ( promlo_we ),
    .q      ( prom_dout[7:0] )
);

endmodule
