skutis/jtbubl/cores/kiwi/hdl/jtkiwi_draw.v

/*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
    Author: Jose Tejada Gomez. Twitter: @topapate
    Version: 1.0
    Date: 7-11-2022 */

// This is tile map section of the SETA chip
// This one uses an independent line buffer
// from that of the sprites

module jtkiwi_draw(
    input               rst,
    input               clk,

    input               draw,
    output reg          busy,
    input      [12:0]   code,
    input      [ 8:0]   xpos,
    input      [ 3:0]   ysub,
    input               flip,

    input               hflip,
    input               vflip,
    input      [ 4:0]   pal,

    output     [19:2]   rom_addr,
    output reg          rom_cs,
    input               rom_ok,
    input      [31:0]   rom_data,

    output reg [ 8:0]   buf_addr,
    output              buf_we,
    output     [ 8:0]   buf_din,

    input      [ 7:0]   debug_bus
);

// Each tile is 16x16 and comes from the same ROM
// but it looks like the sprites have the two 8x16 halves swapped
parameter SWAP_HALVES = 1'b0;

reg  [31:0] pxl_data;
reg         rom_lsb;
reg  [ 3:0] cnt;
wire [ 3:0] ysubf, pxl_in;

assign ysubf    = ysub^{4{vflip}};
assign buf_din  = { pal, pxl_in };
assign pxl_in   = hflip ?
    { pxl_data[23], pxl_data[ 7], pxl_data[31], pxl_data[15] } :
    { pxl_data[16], pxl_data[ 0], pxl_data[24], pxl_data[ 8] };

    // { pxl_data[15], pxl_data[31], pxl_data[ 7], pxl_data[23] } :
    // { pxl_data[ 8], pxl_data[24], pxl_data[ 0], pxl_data[16] } };

assign rom_addr = { code, ysubf[3], rom_lsb^SWAP_HALVES, ysubf[2:0] };
assign buf_we   = busy & ~cnt[3];

always @(posedge clk, posedge rst) begin
    if( rst ) begin
        rom_cs   <= 0;
        buf_addr <= 0;
        pxl_data <= 0;
        busy     <= 0;
        cnt      <= 0;
    end else begin
        if( !busy ) begin
            if( draw ) begin
                rom_lsb  <= hflip; // 14+4 = 18 (+2=20)
                rom_cs   <= 1;
                buf_addr <= xpos;
                busy     <= 1;
                cnt      <= 8;
            end
        end else begin
            if( rom_ok && rom_cs && cnt[3]) begin
                pxl_data <= rom_data;
                cnt[3]   <= 0;
                if( rom_lsb^hflip ) begin
                    rom_cs <= 0;
                end else begin
                    rom_cs <= 1;
                end
            end
            if( !cnt[3] ) begin
                cnt      <= cnt+1'd1;
                buf_addr <= buf_addr+1'd1;
                pxl_data <= hflip ? pxl_data << 1 : pxl_data >> 1;
                rom_lsb  <= ~hflip;
                if( cnt[2:0]==7 && !rom_cs ) busy <= 0;
            end
        end
    end
end

endmodule
