skutis/jtbubl/cores/kiwi/ver/game/mist_dump.v

/*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
    Author: Jose Tejada Gomez. Twitter: @topapate
    Version: 1.0
    Date: 20-8-2020 */

`timescale 1ns/1ps

module mist_dump(
    input           VGA_VS,
    input           led,
    input   [31:0]  frame_cnt
);

`ifdef DUMP
    initial begin
        `ifdef IVERILOG
            $dumpfile("test.lxt");
        `else
            $dumpfile("test.vcd");
        `endif
    end
`ifdef DUMP_START
    initial $display("Dumping will start at frame %0d", `DUMP_START);
    always @(negedge VGA_VS) if( frame_cnt==`DUMP_START ) begin
`else
    initial begin
`endif
        `ifdef DEEPDUMP
            $display("Dumping all signals");
            $dumpvars(0,mist_test);
        `else
            $display("Dumping selected signals");
            $dumpvars(1,UUT.u_game.u_game.u_main);
            $dumpvars(1,UUT.u_game.u_game.u_sound);
            $dumpvars(1,UUT.u_game.u_game.u_main.u_gamecpu.u_cpu.u_cpu.i_tv80_core.PC);
            $dumpvars(1,UUT.u_game.u_game.u_main.u_gamecpu.u_cpu.u_cpu.i_tv80_core.ACC);
            $dumpvars(1,UUT.u_game.u_game.u_main.u_gamecpu.u_cpu.u_cpu.i_tv80_core.Ap);
            $dumpvars(1,UUT.u_game.u_game.u_main.u_gamecpu.u_cpu.u_cpu.i_tv80_core.SP);
            $dumpvars(1,UUT.u_game.u_game.u_main.u_gamecpu.u_cpu.u_cpu.i_tv80_core.F);
            $dumpvars(1,UUT.u_game.u_game.u_main.u_gamecpu.u_cpu.u_cpu.i_tv80_core.Fp);
            $dumpvars(1,UUT.u_game.u_game.u_main.u_gamecpu.u_cpu.u_cpu.i_tv80_core.Alternate);
            $dumpvars(1,UUT.u_game.u_game.u_main.u_gamecpu.u_cpu.u_cpu.i_tv80_core.i_reg.B);
            $dumpvars(1,UUT.u_game.u_game.u_main.u_gamecpu.u_cpu.u_cpu.i_tv80_core.i_reg.C);
            $dumpvars(1,UUT.u_game.u_game.u_main.u_gamecpu.u_cpu.u_cpu.i_tv80_core.i_reg.D);
            $dumpvars(1,UUT.u_game.u_game.u_main.u_gamecpu.u_cpu.u_cpu.i_tv80_core.i_reg.E);
            $dumpvars(1,UUT.u_game.u_game.u_main.u_gamecpu.u_cpu.u_cpu.i_tv80_core.i_reg.H);
            $dumpvars(1,UUT.u_game.u_game.u_main.u_gamecpu.u_cpu.u_cpu.i_tv80_core.i_reg.L);
            $dumpvars(1,UUT.u_game.u_game.u_main.u_gamecpu.u_cpu.u_cpu.i_tv80_core.i_reg.IX);
            $dumpvars(1,UUT.u_game.u_game.u_main.u_gamecpu.u_cpu.u_cpu.i_tv80_core.i_reg.IY);
            $dumpvars(1,UUT.u_game.u_game.u_sound.u_gamecpu.u_cpu.u_cpu.i_tv80_core.PC);
            $dumpvars(1,UUT.u_game.u_game.u_sound.u_gamecpu.u_cpu.u_cpu.i_tv80_core.ACC);
            $dumpvars(1,UUT.u_game.u_game.u_sound.u_gamecpu.u_cpu.u_cpu.i_tv80_core.Ap);
            $dumpvars(1,UUT.u_game.u_game.u_sound.u_gamecpu.u_cpu.u_cpu.i_tv80_core.SP);
            $dumpvars(1,UUT.u_game.u_game.u_sound.u_gamecpu.u_cpu.u_cpu.i_tv80_core.F);
            $dumpvars(1,UUT.u_game.u_game.u_sound.u_gamecpu.u_cpu.u_cpu.i_tv80_core.Fp);
            $dumpvars(1,UUT.u_game.u_game.u_sound.u_gamecpu.u_cpu.u_cpu.i_tv80_core.Alternate);
            $dumpvars(1,UUT.u_game.u_game.u_sound.u_gamecpu.u_cpu.u_cpu.i_tv80_core.i_reg.B);
            $dumpvars(1,UUT.u_game.u_game.u_sound.u_gamecpu.u_cpu.u_cpu.i_tv80_core.i_reg.C);
            $dumpvars(1,UUT.u_game.u_game.u_sound.u_gamecpu.u_cpu.u_cpu.i_tv80_core.i_reg.D);
            $dumpvars(1,UUT.u_game.u_game.u_sound.u_gamecpu.u_cpu.u_cpu.i_tv80_core.i_reg.E);
            $dumpvars(1,UUT.u_game.u_game.u_sound.u_gamecpu.u_cpu.u_cpu.i_tv80_core.i_reg.H);
            $dumpvars(1,UUT.u_game.u_game.u_sound.u_gamecpu.u_cpu.u_cpu.i_tv80_core.i_reg.L);
            $dumpvars(1,UUT.u_game.u_game.u_sound.u_gamecpu.u_cpu.u_cpu.i_tv80_core.i_reg.IX);
            $dumpvars(1,UUT.u_game.u_game.u_sound.u_gamecpu.u_cpu.u_cpu.i_tv80_core.i_reg.IY);

            $dumpvars(1,mist_test.frame_cnt);
        `endif
        $dumpon;
    end
`endif

endmodule // mist_dump
